experientials/ziloo/Hardware/faceboard/FACEBOARD.md

## Faceboard

LED arrangement

LED mounting

Powering

Camera mounting

Sensors. Motion, light, sound
