experientials/ziloo/Hardware/faceboard/USING_GPIO.md

# Using the GPIO connectors

## CAN bus interfacing

## SPI communication

## Retro signalling

If you want to interface with retro computing equipment software drivers for VGA, DVI and Parallel Port the allow you connect
these via the GPIO header.

## Attaching extra I2C sensors

## Attaching Analog Sensors

- humidity
- temperature
- human body
- ?

## Making a Robot

Adding
- Wheels
- Arms 
- Legs

# Power

- 5V (limited A)
- 3V3 while awake
- 3V3 for always on sensors
