experientials/ziloo/Hardware/pinouts/I2C_EXPANDER_1.md

The development board uses a single Expander. The 909 and 801 uses 2x PCA9555 to control more states.

The EX1 expander input triggers interrupt via EX_OH_nINT (GPIO1_IO0).
The pins relate to USB1 OTG and M.2 Key E.

The EX1 expander allows controlling T-USB maps,

| Expander  | Connected to |
|---|---|
| EX1.0 | |
| EX1.1 | |
| EX1.2 |  |
| EX1.3 | MUX_USB2_SEL |
| EX1.4 | MUX_USB3_SEL |
| EX1.5 | COEX4 |
| EX1.6 | DEV_WLAN_WAKE |
| EX1.7 | ALERT / I2C_IRQ |
| EX1.9 | LED / DAS / DSS  |
| EX1.10 | W_DISABLE2# |
| EX1.11 | W_DISABLE1# |
| EX1.12 | UART WAKE |
| EX1.13 | SDIO WAKE |
| EX1.14 | LED2# |
| EX1.15 | |
