experientials/ziloo/Hardware/pinouts/RPI_15_CONNECTOR.md

| Pin | Code | Type | Details | Voltage |
|-----|---|---|---|---|
| 1 |	GND | Power | Ground | |
| 2 |	CAM_D0_N | Data | MIPI Data Lane 0 Negative | |
| 3 |	CAM_D0_P | Data | MIPI Data Lane 0 Positive | |
| 4 |	GND | Power | Ground | |
| 5 |	CAM_D1_N | Data | MIPI Data Lane 1 Negative | |
| 6 |	CAM_D1_P | Data | MIPI Data Lane 1 Positive | |
| 7 |	GND | Power | Ground | |
| 8 |	CAM_CK_N | Data | MIPI Clock Lane Negative | |
| 9 |	CAM_CK_P | Data | MIPI Clock Lane Positive | |
| 10  |	GND | Power | Ground | |
| 11  |	CAM_IO0 | Power | Power Enable | |
| 12  |	CAM_IO1 | LED | LED Indicator | |
| 13  |	SCL | I2C | I2C SCL | |
| 14  |	SDA | I2C | SCCB serial Interface data IO | | 
| 15  |	CAM_3V3 | Power | 3.3V Power Supply | |
