experientials/ziloo/Hardware/pinouts/T-USB_HOST_ALT_CONNECTOR.md

| Pin | Code | Description | 
|-----|---|---|
|  1  | 3V3 | |
|  2  | SBU2 | Host AUX+ / SBU2 |
|  3  | SBU1 | Host AUX- / SBU1 |
|  4  | 3V3 | |
|  5  | HA+ | Host A+ |
|  6  | HA- | Host A- |
|  7  | 3V3 | |
|  8  | HB+ | Host B+ |
|  9  | HB- | Host B- |
| 10  | 3V3 | |
| 11  | HC+ | Host C+ |
| 12  | HC- | Host C- |
| 13  | 3V3 | |
| 14  | HD+ | Host D+ |
| 15  | HD- | Host D- |
| 16  | GND | |
| 17  | | |
| 18  | | |
| 19  | GND | |
| 20  | HX+ | Host Extra 2.0 D+ |
| 21  | HX- | Host Extra 2.0 D- |
| 22  | | |
| 23  | | |
| 24  | GND | |
| 25  | LVCLK+ | LVDS CLK+ |
| 26  | LVCLK- | LVDS CLK- |
| 27  | GND | |
| 28  | LVD0+ | LVDS D0+ |
| 29  | LVD0- | LVDS D0- |
| 30  | GND | |
| 31  | LVD1+ | LVDS D1+ |
| 32  | LVD1- | LVDS D1- |
| 33  | GND | |
| 34  | LVD2+ | LVDS D2+ |
| 35  | LVD2- | LVDS D2- |
| 36  | GND | |
| 37  | LVD3+ | LVDS D3+ |
| 38  | LVD3- | LVDS D3- |
| 39  | GND | |
| 44  | UART_RP…TXD. | Debug  | | | | GP0. |
| 45  | UART…RP…RXD. | Debug. | | | | GP1 |
