experientials/ziloo/Hardware/pinouts/T-USB_OTG_ALT_CONNECTOR.md

| Pin | Code | Category | Description | Voltage | SoM pin  | MCU pin |
|-----|---|---|---|---|---|---|
|  1  | 3V3 | Power | |
|  2  | SBU2 | USB | OTG AUX+ / SBU2 |
|  3  | SBU1 | USB | OTG AUX- / SBU1 |
|  4  | 3V3 | |
|  5  | OA+ | USB | OTG A+ |
|  6  | OA- | USB | OTG A- |
|  7  | 3V3 | |
|  8  | OB+ | USB | OTG B+ |
|  9  | HB- | USB | OTG B- |
| 10  | 3V3 | |
| 11  | OC+ | USB | OTG C+ | 
| 12  | OC- | USB | OTG C- |
| 13  | 3V3 | |
| 14  | OD+ | USB | OTG D+ |
| 15  | OD- | USB | OTG D- |
| 16  | GND | |
| 17  | OX+ | USB | OTG Extra 2.0 D+ |
| 18  | OX- | USB | OTG Extra 2.0 D- |
| 19  | MCU_D+ | USB | Stem MCU 2.0 D+ | 
| 20  | MCU_D- | USB | Stem MCU 2.0 D- |
| 21  | GND | |
| 22  | STEM SCL | I2C | STEM SCL | | | GP17 I2C0 |
| 23  | STEM SDA | I2C | STEM SDA | | | GP16 I2C0 |
| 24  | STEM INT | I2C | Sensor interrupts | |
| 25  | NIGHT SCL  | I2C | I2C6 SCL | | P21.2 ? | GP19 I2C1. |
| 26  | NIGHT SDA  | I2C | I2C6 SDA | | P21.4 ? | GP18 I2C1. |
| 27  | NIGHT INT  | I2C | Sensor interrupts | |
| 28  | SYS I2C SCL| I2C | | | GP15 I2C1.  |
| 29  | SYS I2C SDA| I2C | | | GP14 I2C1.  |
| 30  | GND | Power | Ground | |
| 31  | SWD CLK RP | | | |
| 32  | SWD DAT RP | | | 
| 33  | GND | Power | Ground | |
| 34  | UART1_TXD  | UART | P1.72 UART1 Tx | | P20.9 | GP4 UART1 |
| 35  | UART1_RXD  | UART | P1.19 UART1 Rx | | P20.11  | GP5 UART1 |
| 36  | UART2_TXD  | UART | UART2 Tx | | P20.1 | GP8 UART1. |
| 37  | UART2_RXD  | UART | UART2 Rx | | P20.3 | GP9 UART1 |
| 38  | UART3_TXD  | UART | P1.61 UART3 Tx | | P20.2 | GP12 UART0 |
| 39  | UART3_RXD  | UART | P1.21 UART3 Rx | | P20.4 | GP13 UART0 |
| 40  | UART4_TXD  | UART | UART4 Tx | | P20.8 | GP20 UART1 |
| 41  | UART4_RXD  | UART | UART4 Rx | | P20.10  | GP21 UART1 |
| 42  | SPI_CS | RP2040 | Programming/External flash directly  | 3.3V | | GP29 SPI1 |
| 43  | SPI_CLK | RP2040 | Programming/External flash directly  | 3.3V | | GP26 SPI1 |
| 44  | SPI_MISO | RP2040 | Programming/External flash directly  | 3.3V | | GP28 SPI1 |
| 45  | SPI_MOSI | RP2040 | Programming/External flash directly  | 3.3V | | GP27 SPI1 |
