experientials/ziloo/Hardware/pinouts/BOARD_POWER_4_CONNECTOR.md

| No. | Pin  | Description |
|-----|---|---|
|  1  |	5V |	Board Power 5V |
|  2  |	GND  |	 GND 	 |
|  3  |	GND  |	 GND 	 |
|  4  |	VIN  |	Voltage Input from USB-C |

Max. Current per pin 1A
