experientials/ziloo/Hardware/standards/POWER.md

PMIC_STBY_REQ

Output low with PD
NVCC_SNVS

POR_B

Input with PU
NVCC_SNVS

NVCC_SNVS_1P8
Expected max draw 2mA
