experientials/ziloo/Hardware/pinouts/BOARD_POWER_CONNECTOR.md

| No. | Pin  | Description |
|-----|---|---|
|  1  |	 | Reserved 	 |
|  2  |	5V |	Board Power 5V |
|  3  |	GND  |	 GND 	 |
|  4  |	GND  |	 GND 	 |
|  5  |	VIN  |	Voltage Input from USB-C |
| 6  |	VIN  |	 VIN 	 |
| 7  | PD_I2C1_SCL| I2C1_SCL(pullup resistor 2.2K) | 
| 8  | PD_I2C1_SDA| I2C1_SDA(pullup resistor 2.2K) | 
| 9  | PD_I2C2_SCL| I2C2_SCL(pullup resistor 2.2K) | 
| 10  | PD_I2C2_SDA| I2C2_SDA(pullup resistor 2.2K) | 

Max. Current per pin 3.0A

IRQZ pins for the two I2Cx
