experientials/ziloo/Hardware/pinouts/EXTRAS_CONNECTOR.md

| Pin | Code | Description | 
|-----|---|---|
| 1 | LCAM_FSIN  | Left Frame sync input | 
| 2 | LCAM_STROBE| Left Frame sync output | 
| 3 | LCAM_RESET | Camera Reset, Active Low (RSTB) | 
| 4 | LCAM_PWRDN | Camera Power Down | 
| 5 | LCAM_EXTCLK| Left External Clock Input (MCLK) | 
| 6 | LATT_INT | Left Interrupt Attached Sensor, Active L |
| 7 | LATT_XSHUT | Left Attached Sensor XSHUTDOWN |
| 8 | L_AF_PWM | PWM Motor control | 
| 9 | | Reserved |
| 10  | | Reserved |
| 11  | LCAM_FSIN  | Left Frame sync input | 
| 12  | LCAM_STROBE| Left Frame sync output | 
| 13  | LCAM_RESET | Camera Reset, Active Low (RSTB) | 
| 14  | LCAM_PWRDN | Camera Power Down | 
| 15  | LCAM_EXTCLK| Left External Clock Input (MCLK) | 
| 16  | LATT_INT | Left Interrupt Attached Sensor, Active L |
| 17  | LATT_XSHUT | Left Attached Sensor XSHUTDOWN |
| 18  | L_AF_PWM | PWM Motor control | 
| 19  | | Reserved |
| 20  | | Reserved |
| 21  | BCLK / SCK | Bit clock line | 
| 22  | WS / LRCLK | Word clock line | 
| 23  | SDATA1 | Input data 1 | 
| 24  | SDATA2 | Input data 2 (NC) | 
| 25  | SDATA3 | Input data 3 (NC) | 
| 26  | SDATA4 | Input data 4 (NC) | 
| 27  | PD_I2C1_SCL| I2C1_SCL(pullup resistor 2.2K) | 
| 28  | PD_I2C1_SDA| I2C1_SDA(pullup resistor 2.2K) | 
| 29  | PD_I2C2_SCL| I2C2_SCL(pullup resistor 2.2K) | 
| 30  | PD_I2C2_SDA| I2C2_SDA(pullup resistor 2.2K) | 
| 31  | GND | |
| 34  | GND | |
| 37  | GND | |
| 40  | GND | |
| 43  | GND | |
