experientials/ziloo/Hardware/pinouts/I-PEX_30_CONNECTOR.md

The connector is an [I-PEX type 20525-030E-02](https://www.i-pex.com/product/cabline-ca) with 0.4mm pitch & 30 pins.
Data pins are 1.8V level.

| Pin | Code | Details |
|-----|---|---|
| 1 | CAM_3V3	 | 3.3V Power Input |
| 2 | CAM_3V3 | |
| 3 | CAM_1V8	 | 1.8V Power Input |
| 4 | GND | |
| 5 | GND | |
| 6 | PWR DWN | PWRDN on 34pin |
| 7 | I2C SCL | |
| 8 | I2C SDA | |
| 9 | GND | |
| 10  | CSI D2- | |
| 11  | CSI D2+ | |
| 12  | TRIGGER | |
| 13  | MCLK | EXTCLK on 34pin |
| 14  | Reserved | |
| 15  | CSI D1- | |
| 16  | CSI D1+ | |
| 17  | GND | |
| 18  | GND | |
| 19  | CSI D0- | |
| 20  | CSI D0+ | |
| 21  | RESET | RESET on 34pin |
| 22  | GND | |
| 23  | Reserved | |
| 24  | CSI CLK- | |
| 25  | CSI CLK+ | |
| 26  | GND | |
| 27  | CSI D3- | |
| 28  | CSI D3+ | |
| 29  | Flash | |
| 30  | Reserved | |

Refs
- https://www.leopardimaging.com/product/accessories/cables/faw-1233-03/
- https://www.mouser.com/datasheet/2/233/LI-TX1-CB-6CAM_datasheet-1395894.pdf
- https://connecttech.com/ftp/pdf/ASG006_Spacely.pdf
- https://www.i-pex.com/product/cabline-ca
