experientials/ziloo/Hardware/801/iMX8MP.md

# i.MX 8M Plus

The model used on Compulab dev board is i.MX8M Plus QuadLite 1.8GHz, 1GB RAM, 16GB eMMC w/o Ethernet. 
UCM-iMX8PLUS-C1800Q-D1-N16 price $54*150 for 100pcs.

* [Forlinx OKMX8MP-C Single Board Computer](https://www.forlinx.net/product/okmx8mp-c-development-board-120.html) $54
* [Compulab UCM-iMX8M-Plus](https://www.compulab.com/products/computer-on-modules/ucm-imx8m-plus-nxp-i-mx-8m-plus-som-system-on-module-computer/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) $150
* [Compulab Resources](https://www.compulab.com/products/computer-on-modules/ucm-imx8m-plus-nxp-i-mx-8m-plus-som-system-on-module-computer/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)

* [Building Boot Firmware for CompuLab's i.MX8M Plus products](https://github.com/compulab-yokneam/meta-bsp-imx8mp/blob/ucm-imx8m-plus-r1.0/Documentation/imx_boot_image_build.md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)
* [Compulab Yocto Layer](https://github.com/compulab/yocto-compulab-layer)
* [Compulab getting started](https://mediawiki.compulab.com/w/index.php?title=UCM-iMX8M-Plus:_Evaluation_Kit:_Getting_Started)

nRF 5340 BT40 Module

https://www.digikey.com/en/products/detail/fanstel-corp/BT40/13174283
