experientials/ziloo/Hardware/refs/RV1126.md

# RV1126 Implementation Notes

1. Quad-core AI vision processor
Low-consumption AI vision processor RV1126, with 14nm lithography process and quad-core 32-bit ARM Cortex-A7 architecture, integrates NEON and FPU — the frequency is up to 1.5GHz. It supports FastBoot, TrustZone technology and multiple crypto engines.

2. High performance, high computing power
Built-in neural network processor NPU with computing power up to 2.0 Tops realizes that the power consumption of AI computing is less than 10% of the power required by the GPU. With tools and supporting AI algorithms provided, it supports direct conversion and deployment of Tensorflow, PyTorch, Caffe, MxNet, DarkNet, ONNX, etc.

3. Multi-level image noise reduction
With multi-level image noise reduction, 3F-HDR and other technologies, RV1126 not only ensures the dynamic range of the scene, but also meets the needs of outputting full color in darkness, making "clearly visible" a reality — more conforms to the actual demands in the security field.

4. 4K H.265 encoding & decoding
Built-in Video CODEC supports 4K H.254/H.265@30FPS and multi-channel video encoding and decoding, meeting the needs of low bit rate, low-latency encoding, perceptual encoding and making the video occupancy smaller.

5. Exquisite and mini
Core board pins are made with gold plating technology, which is anti-corrosion. The size is only 69.6mm x 33.9mm, saving a lot of space.

6. Stable and reliable OS
It supports Buildroot+QT OS — occupies small space, starts fast, and provides stable and reliable operation.

7. Various interfaces
SODIMM 260P port is provided; I2C, SPI, UART, ADC, PWM, GPIO, USB2.0, SDIO, I2S, MIPI-DSI, MIPI-CSI, CIF, SDMMC, PHY and other interfaces are equipped, meeting needs of more usage scenarios.

8. To form high-performance mainboard
The core board can be combined with the backplane to form a complete high-performance industrial mainboard with more expansion interfaces and more powerful performance, which can be directly applied to various smart products to accelerate the product development process.

9. Abundant resources for customization
A complete SDK, including cross compiler toolchain, BSP source code, application development environment, development documents, examples, face recognition algorithms and other resources, is provided for the users to make a further customization.

10. Applications
It is widely used in face recognition, gesture recognition, gate access control, smart security, smart IP camera, smart doorbell/peephole, self-service terminals, smart finance, smart construction, smart travel and other industries.

Basic Specifications
SoC
RV1126
CPU
Quad-core ARM Cortex-A7 32-bit, integrates NEON and FPU
Each core has a 32KB I-cache, 32KB D-cache and 512KB shared second-level cache Based on RISC-V MCU
NPU
2.0Tops, supports INT8/ INT16，
It has strong network model compatibility, can realize the conversion of commonly used AI framework models,eg:
Tensor Flow/MXNet/PyTorch/Caffe/...
RAM
1GB / 2GB DDR4
Storage
8GB / 16GB eMMC
Video Encoding
4K H.264/H.265 30fps video encoding:
3840 x 2160@30 fps+720p@30 fps encoding
Video Decoding
4K H.264/H.265 30fps video decoding:
3840 x 2160@30 encoding + 3840 x 2160@30 fps decoding
Hardware Features
Ethernet
Supports 10/100/1000M Ethernet,
With TSO(TCP Segmentation Offload) network acceleration
WiFi
Via SDIO 3.0 interface
Display
Supports MIPI-DSI interface 1080P @ 60 FPS
Audio
8-channel I2S with TDM/PDM, 2-channel I2S
Camera
Supports 3 cameras simultaneous input:
2 groups of MIPI CSI (or LVDS/sub LVDS) and 1 group of DVP (BT.601/BT.656/BT.1120) Supports 14M ISP 2.0 with 3-frame HDR(Line-based/Frame-based/DCG)
Interface
USB 2.0 OTG , USB 2.0 host
1000M Ethernet port, with TSO(TCP Segmentation Offload) network acceleration SDIO 3.0×2 (for Wi-Fi and SD card)
8-channel I2S with TDM/PDM, 2-channel I2S
UART×6, SPI×2, I2C×6, GPIO, CAN, PWM

## CAM-C1126S2U Spec

J4700(MIPI CSI Interface) 

Pin Pin Name            Default function                                IO Power domain   Pad type IO pull
1 AVDD_2V8                2.8V OUTPUT, Max 500mA            IR_AVDD 2.8V
2 VCC3V3_SYS            3.3V OUTPUT, Max 500mA            RGB_AVDD        3.3V
3 GND                    GND                                Power ground
4 IR_PWDN                IR- PWER EN                    For IR Camera            3.3V
5 IR_RESET                IR_RESET,Active L                 For IR Camera     3.3V
6 I2C1_SCL                I2C1_SCL(pullup resistor 2.2K)    IR+RGB            1.8V         UP
7 I2C1_SDA                I2C1_SDA(pullup resistor 2.2K)    IR+RGB             1.8V         UP
8 GND                    GND                                Power ground
9 MIPI_CSI_CLK0            MIPI_CSI_CLK0 OUTPUT             For IR Camera        1.8V DOWN
10 GND                    GND                                Power ground
11 MIPI_CSI_RX0_CLKP        MIPI_CSI_RX0_CLK+                For IR Camera     1.8V
12 MIPI_CSI_RX0_CLKN        MIPI_CSI_RX0_CLK-                For IR Camera      1.8V
13 GND                    GND                                Power ground
14 MIPI_CSI_RX0_D0P        MIPI_CSI_RX0_D0+                For IR Camera        1.8V
15 MIPI_CSI_RX0_D0N        MIPI_CSI_RX0_D0-                  For IR Camera         1.8V
16 GND                    GND                            Power ground
17 MIPI_CSI_RX0_D1P        MIPI_CSI_RX0_D1+                    For IR Camera         1.8V
18 MIPI_CSI_RX0_D1N        MIPI_CSI_RX0_D1-                For IR Camera            1.8V
19 GND                    GND                                Power ground
20 MIPI_CSI_RX0_D2P        MIPI_CSI_RX0_D2+                For IR Camera            1.8V
21 MIPI_CSI_RX0_D2N        MIPI_CSI_RX0_D2-                For IR Camera            1.8V
22 GND                    GND                                Power ground
23 NC                    NC
24 VCC_1V8                1.8V OUT ,MAX 200mA                IR+RGB                    3.3V
25 FSVNC                Default NC                            IR+RGB
26 DVDD_1V2                1.2V OUT ,MAX 300mA                For IR Camera            1.2V
27 DVDD_1V3                1.3V OUT ,MAX 300mA                For RGB Camera           1.3V
28 GND                    GND                                Power ground
29 MIPI_RX0_PDN            MIPI_ PDN                         For RGB Camera           1.8V DOWN
30 MIPI_RX0_RST            MIPI _RST, Active L                For RGB Camera            1.8V        DOWN
31 GND                    GND                                Power ground
32 MIPI_CSI_CLK1            MIPI_CSI_CLK1 Output            For RGB Camera            1.8V        DOWN
33 GND                    GND                                Power ground
34 MIPI_CSI_RX1_CLKP        MIPI_CSI_RX1_CLK+                For RGB Camera            1.8V
35 MIPI_CSI_RX1_CLKN        MIPI_CSI_RX1_CLK-                For RGB Camera            1.8V
36 GND                    GND                                Power ground
37 MIPI_CSI_RX1_D0P        MIPI_CSI_RX1_D0+                  For RGB Camera            1.8V
38 MIPI_CSI_RX1_D0N        MIPI_CSI_RX1_D0-                  For RGB Camera            1.8V
39 GND                    GND                                Power ground
40 MIPI_CSI_RX1_D1P        MIPI_CSI_RX1_D1+                  For RGB Camera            1.8V
41 MIPI_CSI_RX1_D1N        MIPI_CSI_RX1_D1-                  For RGB Camera            1.8V
42 GND                    GND                                Power ground
43 MIPI_CSI_RX1_D2P        MIPI_CSI_RX1_D2P                  For RGB Camera            1.8V
44 MIPI_CSI_RX1_D2N        MIPI_CSI_RX1_D2N                  For RGB Camera            1.8V
45 GND                     GND                                POWER GROUND

## Related Repos

* https://github.com/Consti10/rv1126/issues/13
* https://github.com/lloovve/RV1126-SDK
* https://github.com/xingxingRealzyx/rv1126_bsp/tree/main/projects

## Core-1126-JD4 Spec

* RV1126 MCU/NPU
* 2 * SEC 040K4A46165VF / SEC 949 K4A4G16 5NE BCRC DDR3 1GB 
* SEC 946 BO41 KLM8G1GETF eMMC 8GB
* RK809-2 PMU

1
3
5
7
9
11
13
15
17
19
21
23
25
27
29
31
33
35
37
39
41
43
45
47
49
51
53
55
57
59
61
63
65
67
69
71
73
75
77
79
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
Core board pin definition
GND_1
GPIO0_A4_U
GPIO0_C0_D
GPIO0_A2_Z
GND_2
MIC1_INN
MIC1_INP
HPR_OUT
HP_SNS
HPL_OUT
SPKN_OUT
SPKP_OUT
GND
USB_HOST_DP
USB_HOST_DM
GND_4
NC
NC
GND_5
I2C2_SCL
I2C2_SDA
GND_4
MIPI_CSI_RX0_D2P
MIPI_CSI_RX0_D2N
MIPI_CSI_RX0_D3P
MIPI_CSI_RX0_D3N
MIPI_CSI_RX0_D1P
MIPI_CSI_RX0_D1N
MIPI_CSI_RX1_D3P
MIPI_CSI_RX1_D3N
MIPI_CSI_RX1_D2P
MIPI_CSI_RX1_D2N
GND_7
MIPI_CSI_RX1_D1P
MIPI_CSI_RX1_D1N
MIPI_CSI_RX1_D0P
MIPI_CSI_RX1_D0N
GND8
MIPI_CSI_PWDN0
MIPI_CSI_CLK1
MIPI_CSI_CLK0
GND_9
SPI0_CS1N_M1
SPI0_MOSI_M1/I2C3_SC L_M2
SPI0_CLK_M1
SPI0_CS0N_M1
SPI0_MISO_M1/I2C3_SD A_M2
UART4_TX_M1 /GPIO2_A6_D
GND_10
RMII_RXDV
RMII_RXD0
RMII_CLK
RMII_RXD1
RMII_MDIO
RMII_MDC
RMII_RXER
RMII_TXD0
GND_11
RMII_TXD1
CLKOUT/GPIO_C5_D
RMII_RXD3/HOST_DRV_ H
GND_12
RMII_TXEN/GPIO2_C6_D
RMII_TXD2/ZOOM_EN_ H
RMII_TXCLK/FOCUS_EN_ H
NC
Pin type
G
I/O
I/O
I/O
G
O
O
O
O
G
I/O
I/O
G
G
I/O
I/O
G
G
G
I/O
I/O
I/O
G
I/O
I/O
I/O
I/O
I/O
I/O
G
I/O
I/O
I/O
I/O
I/O
I/O
I/O
I/O
G
I/O
I/O
I/O
G
I/O
I/O
I/O
I
I
I
I
I
I
I
I
I
I
I
I
I
I
I
I
I/O Pull
UP
DOWN
DOWN
DOWN
UP
DOWN
DOWN
DOWN
DOWN
DOWN
DOWN
DOWN
DOWN
DOWN
DOWN
DOWN
DOWN
DOWN
DOWN
DOWN
DOWN
DOWN
DOWN
DOWN
DOWN
DOWN
DOWN
Function for Floor(MB-JD4- RV11091126)
GND_1
WORKLED
DIYLED
FAN_CTRL
GND_2
MIC1_INN
MIC1_INP
HPR_OUT
HP_SNS
HPL_OUT
SPKN_OUT
SPKP_OUT
GND
USB_HOST_DP
USB_HOST_DM
GND
NC
NC
GND
PWM4_M0
PWM5_M0
GND
MIPI_CSI_RX0_D2P
MIPI_CSI_RX0_D2N
MIPI_CSI_RX0_D3P
MIPI_CSI_RX0_D3N
MIPI_CSI_RX0_D1P
MIPI_CSI_RX0_D1N
MIPI_CSI_RX1_D3P
MIPI_CSI_RX1_D3N
MIPI_CSI_RX1_D2P
MIPI_CSI_RX1_D2N
GND
MIPI_CSI_RX1_D1P
MIPI_CSI_RX1_D1N
MIPI_CSI_RX1_D0P
MIPI_CSI_RX1_D0N
GND
MIPI_CSI_PWDN0
MIPI_CSI_CLK1
MIPI_CSI_CLK0
GND
SPI0_CS1N_M1
SPI0_MOSI_M1
SPI0_CLK_M1
SPI0_CS0N_M1
SPI0_MISO_M1
UART4_TX
GND
RMII_RXDV
RMII_RXD0
RMII_CLK
RMII_RXD1
RMII_MDIO
RMII_MDC
RMII_RXER
RMII_TXD0
GND
RMII_TXD1
CLKOUT/GPIO_C5_D
RMII_RXD3
GND
RMII_TXEN
RMII_TXD2
RMII_TXCLK
NC
Default function description
GND
System LED control 1:Enable,0:Disable
Diy led control 1:Enable,0:Disable
PMIC MIC_IN_N
Core board internal series capacitor
0.1uF
PMIC MIC_IN_P,
Core board internal series capacitor 0.1uF
PMIC_HearPhone_OUT_R
PMIC_HearPhone_OUT_GND
PMIC_HearPhone_OUT_L
PMIC_Sperker_OUT_N
PMIC_Sperker_OUT_P
PWM4_M0
PWM5_M0
GND
MIPI_CSI_RX0_D2P
MIPI_CSI_RX0_D2N
MIPI_CSI_RX0_D3P
MIPI_CSI_RX0_D3N
MIPI_CSI_RX0_D1P
MIPI_CSI_RX0_D1N
MIPI_CSI_RX1_D3P
MIPI_CSI_RX1_D3N
MIPI_CSI_RX1_D2P
MIPI_CSI_RX1_D2N
GND
MIPI_CSI_RX1_D1P
MIPI_CSI_RX1_D1N
MIPI_CSI_RX1_D0P
MIPI_CSI_RX1_D0N
GND
MIPI-CSI Power_EN
MIPI-CSI_clock1
MIPI-CSI_clock0
GND
SPI0_CS1N_M1
SPI0_MOSI_M1
SPI0_CLK_M1
SPI0_CS0N_M1
SPI0_MISO_M1
UART4_TX
GND
RMII_RXDV
RMII_RXD0
RMII_CLOCK
RMII_RXD1
RMII_MDIO
RMII_MDC
RMII_RXER
RMII_TXD0
Core board internal series resistance 22R
GND
RMII_TXD1
Core board internal series resistance 22R
PHY_XTALOUT
RMII_RXD3
GND
RMII_TXEN
RMII_TXD2
Core board internal series resistance 22R
RMII_TXCLK
Core board internal series resistance 22R
NC
IO Power domain
1.8V
3.3V
1.8V
3.3V
3.3V
3.3V
3.3V
3.3V
3.3V
3.3V
3.3V
3.3V
3.3V
1.8V
1.8V
1.8V
1.8V
1.8V
1.8V
1.8V
1.8V
1.8V
1.8V
1.8V
1.8V
1.8V
1.8V
1.8V
1.8V
1.8V
1.8V
1.8V
1.8V
1.8V
1.8V
3.3V
3.3V
3.3V
3.3V
3.3V
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
RV1126 Pin
V7
U9
AA3
Y1
Y2
AA6
Y6
W15
Y15
AA15
AA16
Y16
W16
Y17
W17
AA18
Y18
AA19
Y19
AA20
Y20
W20
W21
V21
V20
V19
U20
U19
U18
M21
K18
K19
K21
K20
J21
J20
J19
H20
H19
G21
H18
G20
F21
F20
RV1126 Pin Name
GND_1
SPI0_CS1N_M0 / GPIO0_A4_U
SDMMC0_PWR / UART1_RTSN_M0 / PWM2_M0 / GPIO0_C0_D
CLKI_CLKO_32K / GPIO0_A2_Z
GND_2
MIC1_N / MIC_R
MIC1_P / MIC_L
HPR_OUT
HP_SNS
HPL_OUT
SPKN_OUT
SPKP_OUT
GND_3
USB_HOST_DP
USB_HOST_DM
GND_4
NC_1
NC_2
GND_5
I2C2_SCL / PWM4_M0 / GPIO0_C2_D
I2C2_SDA / PWM5_M0 / GPIO0_C3_D
GND_6
MIPI_CSI_RX0_D2P / LVDS0_RX2P
MIPI_CSI_RX0_D2N / LVDS0_RX2N
MIPI_CSI_RX0_D3P / LVDS0_RX3P
MIPI_CSI_RX0_D3N / LVDS0_RX3N
MIPI_CSI_RX0_D1P / LVDS0_RX1P
MIPI_CSI_RX0_D1N / LVDS0_RX1N
MIPI_CSI_RX1_D3P / LVDS1_RX3P
MIPI_CSI_RX1_D3N / LVDS1_RX3N
MIPI_CSI_RX1_D2P / LVDS1_RX2P
MIPI_CSI_RX1_D2N / LVDS1_RX2N
GND_7
MIPI_CSI_RX1_D1P / LVDS1_RX1P
MIPI_CSI_RX1_D1P / LVDS1_RX1N
MIPI_CSI_RX1_D0P / LVDS1_RX0P
MIPI_CSI_RX1_D0P / LVDS1_RX0N
GND8
UART4_RX_M2 / GPIO1_D4_d
MIPI_CSI_CLK1 / UART5_RTSN_M2 / GPIO2_A2_D
MIPI_CSI_CLK0 / UART5_CTSN_M2 / GPIO2_A3_D
GND_9
SPI0_CS1N_M1 / I2S1_MCLK_M1 / UART4_TX_M2 / GPIO1_D5_D
SPI0_MOSI_M1 / I2S1_SCLK_M1 / I2C3_SCL_M2 / GPIO1_D6_D
SPI0_CLK_M1 / I2S1_SDO_M1 / UART5_RX_M2 / GPIO2_A1_D
SPI0_CS0N_M1 / I2S1_SDI_M1 / UART5_TX_M2 / GPIO2_A0_D
SPI0_MISO_M1 / I2S1_LRCK_M1 / I2C3_SDA_M2 / GPIO1_D7_D
UART4_TX_M1 / PWM5_M1 / RGMII_COL_M1 / CIF_D2_M1 / LCDC_D2 / GPIO2_A6_D
GND_10
RGMII_RXDV_M1 / CIF_D4_M1 / LCDC_D8 / GPIO2_B4_D
RGMII_RXD0_M1 / CIF_D5_M1 / LCDC_D9 / GPIO2_B5_D
RGMII_CLK_M1 / CIF_D7_M1 / LCDC_D11 / GPIO2_B7_D
RGMII_RXD1_M1 / CIF_D6_M1 / LCDC_D10 / GPIO2_B6_D
RGMII_MDIO_M1 / CIF_D9_M1 / LCDC_D13 / GPIO2_C1_D
RGMII_MDC_M1 / CIF_D10_M1 / LCDC_D14 / GPIO2_C2_D
RGMII_RXER_M1 / CIF_D8_M1 / LCDC_D12 / GPIO2_C0_D
RGMII_TXD0_M1 / CIF_D11_M1 / LCDC_D15 / GPIO2_C3_D
GND_11
RGMII_TXD1_M1 / CIF_D12_M1 / LCDC_D16 / GPIO2_C4_D
CLK_OUT_ETHERNET_M1 / CIF_D13_M1 / LCDC_D17 / GPIO2_C5_D
I2S1_SDO_M2 / RGMII_RXD3_M1 / CIF_VSYNC_M1 / LCDC_D20 / GPIO2_D0_D
GND_12
RGMII_TXEN_M1 / CIF_D14_M1 / LCDC_D18 / GPIO2_C6_D
I2S1_SCLK_M2 / RGMII_TXD2_M1 / CIF_CLKOUT_M1 / LCDC_D21 / GPIO2_D1_D
I2S1_LRCK_M2 / RGMII_TXCLK_M1 / CIF_CLKIN_M1 / LCDC_D22 / GPIO2_D2_D
NC_3

-8-
        High-Performance AI Vision Core Board
 133
OTG_DP
OTG_DP
USB_OTG_DP
3.3V
W3
OTG_DP
135
OTG_DM
OTG_DM
USB_OTG_DM
3.3V
W4
OTG_DM
137
NC
NC
NC
NC_4
139
LCD_PWREN/UART3_TX _M2
I/O
UP
UART3_TX
UART3_TX_M2
3.3V
E20
I2C4_SCL_M0 / CAN_RXD_M0 / UART3_TX_M2 / PWM7_IR_M1 / SPI1_CS1N_M2 / GPIO3_A0_U
141
GPIO3_A1_U/UART3_RX _M2
I/O
UP
UART3_RX
UART3_RX_M2
3.3V
E19
I2C4_SDA_M0 / CAN_TXD_M0 / UART3_RX_M2 / PWM11_IR_M1 / GPIO3_A1_U
143
PWM8_M1
I/O
DOWN
PWM8_M1/SPI1_MISO_M2
PWM8_M1/SPI1_MISO_M2
3.3V
D21
UART3_CTSN_M2 / PWM8_M1 / SPI1_MISO_M2 / LCDC_CLK / GPIO2_D7_D
145
OTG_VBUS_DET
I
DOWN
OTG_DET_1V8
OTG_DET.Active Hight
1.8V
V5
OTG_VBUS1V8
147
MIPI_DSI_TX0_D3P
O
MIPI_DSI_TX0_D3P
MIPI_DSI_TX0_D3P
1.8V
D20
MIPI_DSI_TX0_D3P
149
MIPI_DSI_TX0_D3N
O
MIPI_DSI_TX0_D3N
MIPI_DSI_TX0_D3N
1.8V
D19
MIPI_DSI_TX0_D3N
151
MIPI_DSI_TX0_D2P
O
MIPI_DSI_TX0_D2P
MIPI_DSI_TX0_D2P
1.8V
B21
MIPI_DSI_TX0_D2P
153
MIPI_DSI_TX0_D2N
O
MIPI_DSI_TX0_D2N
MIPI_DSI_TX0_D2N
1.8V
C20
MIPI_DSI_TX0_D2N
155
MIPI_DSI_TX0_D1N
O
MIPI_DSI_TX0_D1N
MIPI_DSI_TX0_D1N
1.8V
B20
MIPI_DSI_TX0_D1N
157
MIPI_DSI_TX0_D1P
O
MIPI_DSI_TX0_D1P
MIPI_DSI_TX0_D1P
1.8V
A20
MIPI_DSI_TX0_D1P
159
MIPI_DSI_TX0_D0N
O
MIPI_DSI_TX0_D0N
MIPI_DSI_TX0_D0N
1.8V
B19
MIPI_DSI_TX0_D0N
161
MIPI_DSI_TX0_D0P
O
MIPI_DSI_TX0_D0P
MIPI_DSI_TX0_D0P
1.8V
A19
MIPI_DSI_TX0_D0P
163
GND_13
G
GND
GND
GND_13
165
SDIO_CLK
I/O
DOWN
SDIO_CLK
SDIO_CLK
Core board internal series resistance 22R
1.8V
D16
SDMMC1_CLK / GPIO1_B2_D
167
SDIO_D1
I/O
UP
SDIO_D1
SDIO_D1
1.8V
C16
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
G
GND
MIPI_CSI_RX0_CLKN
MIPI_CSI_RX0_CLKP
MIPI_CSI_RX0_D0P
MIPI_CSI_RX0_D0N
MIPI_CSI_RX1_CLKP
MIPI_CSI_RX1_CLKN
NC
MIPI_CSI_PWDN1
GND
MIPI_CSI_RST1
MIPI_CSI_RST0
BL_EN
TP_RST
TP_INT
GPIO0_D6
NC
NC
UART1_TX
Power ground
Power ground
Power ground
Power ground
Input Voltage 4.8V-5.5V
Input Voltage 4.8V-5.5V
Input Voltage 4.8V-5.5V
Input Voltage 4.8V-5.5V
Input Voltage 4.8V-5.5V
Default function description
GND
Mipi Reset,active low
NC
LCD_PWOER_EN
NC
I2C serial port 1,
Core board internal pull up Resistor 2.2K
I2C serial port 1,
Core board internal pull up Resistor 2.2K
NC
NC
NC
I2C serial port 1,
need pull up Resistor 2.2K
I2C serial port 1,
need pull up Resistor 2.2K
GND
NC
Speaker_EN ,active hight
GPIO3_D4
GND
NC
PMIC power_en output,active hight
Core board internal series resistance 1K
GND
TF_Card DET,active low
GND
SDMMC0_CMD
SDMMC0_CLK
SDMMC0_D1
SDMMC0_D0
SDMMC0_D2
SDMMC0_D3
GND
MIPI_CSI_RX0_CLKN
MIPI_CSI_RX0_CLKP
MIPI_CSI_RX0_D0P
MIPI_CSI_RX0_D0N
MIPI_CSI_RX1_CLKP
MIPI_CSI_RX1_CLKN
NC
MIPI_CSI_Powerdown1
GND
MIPI_CSI_RST1,active low
MIPI_CSI_RST0,active low
Black light EN ,active hight
TP_Reset,active low
TP_INT
GPIO0_D6
NC
NC
UART1_TX
5.0V_IN
5.0V_IN
5.0V_IN
5.0V_IN
5.0V_IN
IO Power domain
1.8V
1.8V
3.3V
3.3V
1.8V
1.8V
1.8V
1.8V
5.0V
1.8V
Note 1
1.8V
1.8V
1.8V
1.8V
1.8V
1.8V
3.3V
1.8V
1.8V
3.3V
3.3V
3.3V
3.3V
3.3V
RV1126 Pin
R4
T3
AA7
Y7
W19
Y21
AA12
Y12
U7
Y13
AA13
W13
Y14
V13
U13
V15
U15
V16
U16
V18
W18
T18
V11
U11
R3
U2
T2
R2
W8
RV1126 Pin Name
GND_21
I2S1_SDI_M0 / FSPI_D3 / FLASH_RDN / GPIO1_A2_U
NC_16
I2S1_SDO_M0 / FSPI_D2 / GPIO0_D6_D
NC_17
I2C0_SCL / GPIO0_B4_D
I2C0_SDA / GPIO0_B5_D
NC_18
NC_19
NC_20
I2C1_SDA / UART4_RTSN_M2 / GPIO1_D2_U
I2C1_SCL / UART4_CTSN_M2 / GPIO1_D3_U
GND_22
NC_21
I2S0_SDI0_M0 / PDM_SDI0_M0 / ACODEC_DAC_DATAL / GPIO3_D6_D
I2S0_LRCK_RX_M0 / PDM_CLK0_M0 / ACODEC_ADC_SYNC / GPIO3_D4_D
GND_23
NC_22
PMIC_EXT_EN
GND_24
SDMMC0_DET / GPIO0_A3_U
GND_25
UART3_CTSN_M1 / RISC-V_JTAG_TDI / SDMMC0_CMD / GPIO1_B1_U
UART3_RTSN_M1 / RISC-V_JTAG_TDO / SDMMC0_CLK / GPIO1_B0_U
UART2_TX_M0 / TEST_CLK0_OUT / RISC-V_JTAG_TRSTN / SDMMC0_D1 / GPIO1_A5_U
UART2_RX_M0 / TEST_CLK1_OUT / SDMMC0_D0 / GPIO1_A4_U
UART3_RX_M1 / A7_JTAG_TCK_M0 / RISC-V_JTAG_TCK / SDMMC0_D2 / GPIO1_A6_U
UART3_TX_M1 / A7_JTAG_TMS_M0 / RISC-V_JTAG_TMS / SDMMC0_D3 / GPIO1_A7_U
GND_26
MIPI_CSI_RX0_CLKN / LVDS0_CLKN
MIPI_CSI_RX0_CLKP / LVDS0_CLKP
MIPI_CSI_RX0_D0P / LVDS0_RX0P
MIPI_CSI_RX0_D0N / LVDS0_RX0N
MIPI_CSI_RX1_CLKP / LVDS1_CLKP
MIPI_CSI_RX1_CLKN / LVDS1_CLKN
NC_23
CIF_D1_M0 / RGMII_CRS_M0 / I2S0_LRCK_TX_M1 / UART4_RX_M0 / I2C3_SDA_M0 / PWM9_M0 / GPIO3_A5_D
GND_27
I2S0_SDO3_SDI1_M0 / PDM_SDI1_M0 / I2C4_SDA_M1 / AUDPWM_R_M0 / AUDDSM_RP / GPIO4_A1_D
I2S0_SDO2_SDI2_M0 / PDM_SDI2_M0 / I2C4_SCL_M1 / AUDPWM_L_M0 / AUDDSM_RN / GPIO4_A0_D
FSPI_CLK / EMMC_RSTN / FLASH_WPN / GPIO1_A3_D
I2S1_MCLK_M0 / FSPI_CS0N / FLASH_CS0N / GPIO0_D4_U
I2S1_LRCK_M0 / FSPI_D0 / FLASH_ALE / GPIO1_A0_D
I2S1_SCLK_M0 / FSPI_D1 / FLASH_RDYN / GPIO1_A1_U
NC_24
NC_25
UART1_TX_M0 / PWM0_M0 / GPIO0_B6_D
                                                             - 10 -

        High-Performance AI Vision Core Board
 96
PWM1_M0/UART1_RX_ M0
I/O
DOWN
UART1_RX
UART1_RX
3.3V
V9
UART1_RX_M0 / PWM1_M0 / GPIO0_B7_D
98
NC_26
NC
NC
NC_26
100
UART2_RX/DEBUG_RX
I/O
UP
UART2_RX/DEBUG_RX
UART2_RX/DEBUG_RX
3.3V
H16
A7_JTAG_TMS_M1 / UART2_RX_M1 / GPIO3_A3_U
102
UART2_TX/DEBUG_TX
I/O
UP
UART2_TX/DEBUG_TX
UART2_TX/DEBUG_TX
3.3V
G18
A7_JTAG_TCK_M1 / UART2_TX_M1 / GPIO3_A2_U
104
PWM10_M0 / GPIO3_A6_D
I/O
DOWN
LCD_BL_PWM
LCD_BL_PWM
3.3V
P17
CIF_D2_M0 / RGMII_COL_M0 / I2S0_SDO0_M1 / UART5_TX_M0 / CAN_RXD_M1 / PWM10_M0 / GPIO3_A6_D
106
PWM4_M1/ GPIO2_A7_D
I/O
DOWN
PWM4_M1/UART4_RX
PWM4_M1/UART4_RX output
3.3V
M20
I2S2_SDO_M1 / UART4_RX_M1 / PWM4_M1 / SPI0_CS0N_M2 / LCDC_D3 / GPIO2_A7_D
108
PWM3_IR_M1/ GPIO2_B0_D
I/O
DOWN
PWM3_M1
PWM3_M1 output
3.3V
L19
I2S2_SDI_M1 / UART5_TX_M1 / PWM3_IR_M1 / SPI0_MOSI_M2 / LCDC_D4 / GPIO2_B0_D
110
I2C5_SCL_M0/GPIO2_A5 _D
I/O
DOWN
3G_PWR_EN
3G_Power_EN,active hight
3.3V
L17
I2C5_SCL_M0 / UART4_CTSN_M1 / RGMII_CRS_M1 / CIF_D1_M1 / LCDC_D1 / GPIO2_A5_D
112
I2C5_SDA_M0/GPIO2_B 3_D
I/O
DOWN
CIFD3/PWM0_M1
CIFD3/PWM0_M1 output
3.3V
K17
I2C5_SDA_M0 / I2S2_MCLK_M1 / UART5_CTSN_M1 / PWM0_M1 / SPI0_CS1N_M2 / CIF_D3_M1 / LCDC_D7 / GPIO2_B3_D
114
NC_27
NC
NC
NC_27
116
PWM6_M1
I/O
DOWN
PWM6_M1/SPI1_CS0_M2
PWM6_M1/SPI1_CS0_M2
3.3V
J17
I2C3_SCL_M1 / PWM6_M1 / SPI1_CS0N_M2 / LCDC_DEN / GPIO2_D4_D
118
PWM10_M1
I/O
DOWN
PWM10_M1/SPI1_CLK_M2
PWM10_M1/SPI1_CLK_M2
3.3V
H17
I2C3_SDA_M1 / PWM10_M1 / SPI1_CLK_M2 / LCDC_HSYNC / GPIO2_D5_D
120
RMII_TXD3/GPIO2_A4_D
I/O
DOWN
RMII_TXD3
RMII_TXD3
Core board internal series resistance 22R
3.3V
J18
UART4_RTSN_M1 / RGMII_TXD3_M1 / CIF_D0_M1 / LCDC_D0 / GPIO2_A4_D
122
RMII_RXD2/GPIO2_C7_D
I/O
DOWN
RMII_RXD2
RMII_RXD2
3.3V
G19
I2S1_MCLK_M2 / RGMII_RXD2_M1 / CIF_D15_M1 / LCDC_D19 / GPIO2_C7_D
124
GND_28
G
GND
GND
GND_28
126
RMII_RXCLK/P_IRIS_EN_ H
I/O
DOWN
RMII_RXCLK
RMII_RXCLK
3.3V
F19
I2S1_SDI_M2 / RGMII_RXCLK_M1 / CIF_HSYNC_M1 / LCDC_D23 / GPIO2_D3_D
128
NC_28
NC
NC
NC_28
130
OTG_ID
I
UP
OTG_ID
OTG_DET.Active low
1.8V
Y3
OTG_ID
132
NC
NC
NC
NC
134
NC_29
NC
NC
NC_29
136
PWM9_M1
I/O
DOWN
PWM9_M1/SPI1_MOSI_M2
PWM9_M1/SPI1_MOSI_M2
3.3V
C21
UART3_RTSN_M2 / PWM9_M1 / SPI1_MOSI_M2 / LCDC_VSYNC / GPIO2_D6_D
138
GND_29
G
GND
GND
GND_29
140
MIPI_DSI_TX0_CLKP
O
MIPI_DSI_CLKP
MIPI_DSI_CLKP
1.8V
C19
MIPI_DSI_TX0_CLKP
142
MIPI_DSI_TX0_CLKN
O
MIPI_DSI_CLKN
MIPI_DSI_CLKN
1.8V
C18
MIPI_DSI_TX0_CLKN
144
NC_30
NC
NC
NC_30
146
NC_31
NC
NC
NC_31
148
NC_32
NC
NC
NC_32
150
ADC_IN4
I
UP
ADCIN4
ADC4 input,
Core board interiorl pull up Resistor 10K
1.8V
C17
ADC_IN4
152
ADC_IN0
I
UP
RECOVER
ADC0 input,RECOVER KEY, active low
Core board interiorl pull up Resistor 10K
1.8V
E17
ADC_IN0
154
ADC_IN2
I
UP
ADCIN2
ADC2 input,
Core board interiorl pull up Resistor 10K
1.8V
B18
ADC_IN2
156
ADC_IN3
I
UP
ADCIN3
ADC3 input,
Core board interiorl pull up Resistor 10K
1.8V
A18
ADC_IN3
158
GND_30
G
GND
GND
GND_30
160
NC_33
NC
NC
NC_33
162
PCM_RX/ GPIO1_C5_D
I/O
DOWN
HP_DET
Headphone plug in det,active low
1.8V
E13
I2S2_SDI_M0 / SPI1_MISO_M1 / FLASH_TRIG_IN / GPIO1_C5_D
164
PCM_CLK/ GPIO1_C6_D
I/O
DOWN
USB_OTG_EN
OTG power en ,active hight
1.8V
D13
I2S2_SCLK_M0 / SPI1_CLK_M1 / PRELIGHT_TRIG_OUT / UART1_RTSN_M1 / GPIO1_C6_D
166
PCM_SYNC/ GPIO1_C7_D
I/O
DOWN
MUTE
Headphone output en,active hight
1.8V
C13
I2S2_LRCK_M0 / SPI1_CS0N_M1 / UART1_CTSN_M1 / GPIO1_C7_D
168
PCM_TX/ GPIO1_C4_D
I/O
DOWN
USB_HOST_EN
USB Host power en ,active hight
1.8V
B14
I2S2_SDO_M0 / SPI1_MOSI_M1 / FLASH_TRIG_OUT / GPIO1_C4_D
170
UART0_TX
I/O
UP
UART0_TX
UART0_TX for BT
1.8V
C14
UART0_TX / GPIO1_C3_U
172
UART0_RX
I/O
UP
UART0_RX
UART0_RX for BT
1.8V
D14
UART0_RX / GPIO1_C2_U
174
UART0_CTSN
I/O
UP
UART0_CTSN
UART0_CTSN for BT
1.8V
A15
UART0_CTSN / GPIO1_C1_U
176
UART0_RTSN
I/O
UP
UART0_RTSN
UART0_RTSN for BT
1.8V
B15
UART0_RTSN / GPIO1_C0_U
178
NC_34
NC
NC
NC_34
180
GND_31
G
GND
GND
GND_31
182
GMAC_MDIO_M0
I/O
DOWN
GMAC_MDIO_M0/D15
GMAC_MDIO_M0/D15
3.3V
N20
CIF_D15_M0 / RGMII_MDIO_M0 / PDM_CLK1_M1 / GPIO3_C3_D
184
GMAC_MDC_M0
I/O
DOWN
GMAC_MDC_M0/VSYNC
GMAC_MDC_M0/VSYNC
3.3V
N21
CIF_VSYNC_M0 / RGMII_MDC_M0 / UART3_RTSN_M0 / GPIO3_C4_D
186
GMAC_TXCLK_M0
I/O
DOWN
GMAC_TXCLK_M0/CLKOUT
GMAC_TXCLK_M0/CLKOUT
Core board internal series resistance 22R
3.3V
P19
CIF_CLKOUT_M0 / RGMII_TXCLK_M0 / UART3_TX_M0 / GPIO3_C6_D
188
GMAC_RXCLK_M0
I/O
DOWN
GMAC_RXCLK_M0/NHYNC
GMAC_RXCLK_M0/NHYNC
3.3V
P20
CIF_HSYNC_M0 / RGMII_RXCLK_M0 / UART3_RX_M0 / GPIO3_C7_D
190
GND_32
G
GND
GND
GND_32
192
GMAC_CLK_M0
I/O
DOWN
GMAC_CLK_M0/D12
MAC reference clock output /CIF_D12
3.3V
N19
CIF_D12_M0 / RGMII_CLK_M0 / PDM_CLK0_M1 / SPI1_CLK_M0 / GPIO3_C0_D
194
GMAC_RXD1_M0
I/O
DOWN
GMAC_RXD1_M0/D11
MAC receive data/CIF_D11
3.3V
R21
CIF_D11_M0 / RGMII_RXD1_M0 / PDM_SDI3_M1 / SPI1_MISO_M0 / GPIO3_B7_D
196
GMAC_RXD3_M0
I/O
DOWN
GMAC_RXD3_M0/D4
MAC receive data/CIF_D4
3.3V
T19
CIF_D4_M0 / RGMII_RXD3_M0 / I2S0_MCLK_M1 / UART5_RTSN_M0 / I2C5_SCL_M1 / GPIO3_B0_D
198
GMAC_RXD0_M0
I/O
DOWN
GMAC_RXD0_M0/D10
MAC receive data/CIF_D10
3.3V
R20
CIF_D10_M0 / RGMII_RXD0_M0 / PDM_SDI2_M1 / SPI1_MOSI_M0 / GPIO3_B6_D
200
GMAC_RXD2_M0
I/O
DOWN
PWM11_M0
PWM11_M0/CIF_D3
3.3V
R18
CIF_D3_M0 / RGMII_RXD2_M0 / I2S0_SDI0_M1 / UART5_RX_M0 / CAN_TXD_M1 / PWM11_IR_M0 / GPIO3_A7_D
202
GMAC_RXDV_M0
I/O
DOWN
GMAC_RXDV_M0/D13
MAC receive data valid/CIF_D13
3.3V
M17
CIF_D13_M0 / RGMII_RXDV_M0 / PDM_SDI0_M1 / GPIO3_C1_D
204
GMAC_TXD0_M0
I/O
DOWN
GMAC_TXD0_M0/D7
MAC transmit data /CIF_D7
Core board internal series resistance 22R
3.3V
R19
CIF_D7_M0 / RGMII_TXD0_M0 / I2S0_SDO1_SDI3_M1 / UART4_CTSN_M0 / GPIO3_B3_D
206
GMAC_TXD2_M0
I/O
DOWN
GMAC_TXD2_M0/D5
MAC transmit data/CIF_D5
Core board internal series resistance 22R
3.3V
T20
CIF_D5_M0 / RGMII_TXD2_M0 / I2S0_SCLK_RX_M1 / UART5_CTSN_M0 / I2C5_SDA_M1 / GPIO3_B1_D
208
GMAC_TXD3_M0
I/O
DOWN
GMAC_TXD3_M0/D6
MAC transmit data/CIF_D6
Core board internal series resistance 22R
3.3V
N17
CIF_D6_M0 / RGMII_TXD3_M0 / I2S0_LRCK_RX_M1 / UART4_RTSN_M0 / GPIO3_B2_D
                                                                    - 11 -

       High-Performance AI Vision Core Board
210
GMAC_TXD1_M0
I/O
DOWN
GMAC_TXD1_M0/D8
MAC transmit data/CIF_D8
Core board internal series resistance 22R
3.3V
T21
CIF_D8_M0 / RGMII_TXD1_M0 / I2S0_SDO2_SDI2_M1 / SPI1_CS1N_M0 / GPIO3_B4_D
212
GMAC_TXEN_M0
I/O
DOWN
GMAC_TXEN_M0/D9
MAC transmit enable /CIF_D9
Core board internal series resistance 22R
3.3V
N18
CIF_D9_M0 / RGMII_TXEN_M0 / I2S0_SDO3_SDI1_M1 / SPI1_CS0N_M0 / GPIO3_B5_D
214
EPHY_PMEB
I/O
DOWN
EPHY_PMEB
PHY interrupt input,
3.3V
L20
I2S2_SCLK_M1 / UART5_RX_M1 / PWM2_M1 / SPI0_MISO_M2 / LCDC_D5 / GPIO2_B1_D
216
EPHY_RSTN
I/O
DOWN
EPHY_RSTN
phy reset output,active low
3.3V
K16
I2S2_LRCK_M1 / UART5_RTSN_M1 / PWM1_M1 / SPI0_CLK_M2 / LCDC_D6 / GPIO2_B2_D
218
RESET_KEY
I
RESET
system reset signal Input, External connection Reset key, active low
1.8V
W7
RESET_KEY
220
NC_35
NC
NC
NC_35
222
GND_33
G
GND
GND
GND_33
224
VCC_1V8
P
VCC_1V8
1.8V output,VCC_1V8 Total Max current 200mA(224PIN,225PIN same net)
1.8V
226
VCC3V3_SD
P
VCC3V3_SD
1.8V output,VCC_1V8 Total Max current 200mA(224PIN,225PIN same net)
3.3V
228
VCC1V2_DVDD
P
VCC1V2_DVDD
1.2V output,VCC1V2_DVDD Total Max current 300mA(228PIN,229PIN same net)
1.2V
230
VCC_3V3
P
VCC_3V3
3.3V output,VCC_3V3 Total Max current 400mA(230PIN,231PIN,234PIN,235PIN same net)
3.3V
232
VCC_RTC
P
VCC_RTC
3.3-5.0V input for RTC, Max current 50mA
5.0V
234
VCC_3V3
P
VCC_3V3
3.3V output,VCC_3V3 Total Max current 400mA(230PIN,231PIN,234PIN,235PIN same net)
3.3V
236
VCC2V8_AVDD
P
VCC2V8_AVDD
2.8V output,VCC2V8_AVDD Total Max current 300mA(236PIN,237PIN same net)
2.8V
238
VCC1V8_DOVDD
P
VCC1V8_DOVDD
1.8V output,VCC1V8_DOVDD Total Max current 300mA(238PIN,239PIN same net)
1.8V
240
NC_36
NC
NC
NC_36
242
NC_37
NC
NC
NC_37
244
GND_34
G
GND
Power ground
246
GND_35
G
GND
Power ground
248
GND_36
G
GND
Power ground
250
GND_37
G
GND
Power ground
252
VCC5V0_SYS_6
P
VCC5V0_SYS
Input Voltage 4.8V-5.5V
5.0V_IN
254
VCC5V0_SYS_7
P
VCC5V0_SYS
Input Voltage 4.8V-5.5V
5.0V_IN
256
VCC5V0_SYS_8
P
VCC5V0_SYS
Input Voltage 4.8V-5.5V
5.0V_IN
258
VCC5V0_SYS_9
P
VCC5V0_SYS
Input Voltage 4.8V-5.5V
5.0V_IN
260
VCC5V0_SYS_10
P
VCC5V0_SYS
Input Voltage 4.8V-5.5V
5.0V_IN
