experientials/ziloo/Hardware/801-T-USB/Ziloo 801 T-USB power circuit.pdf

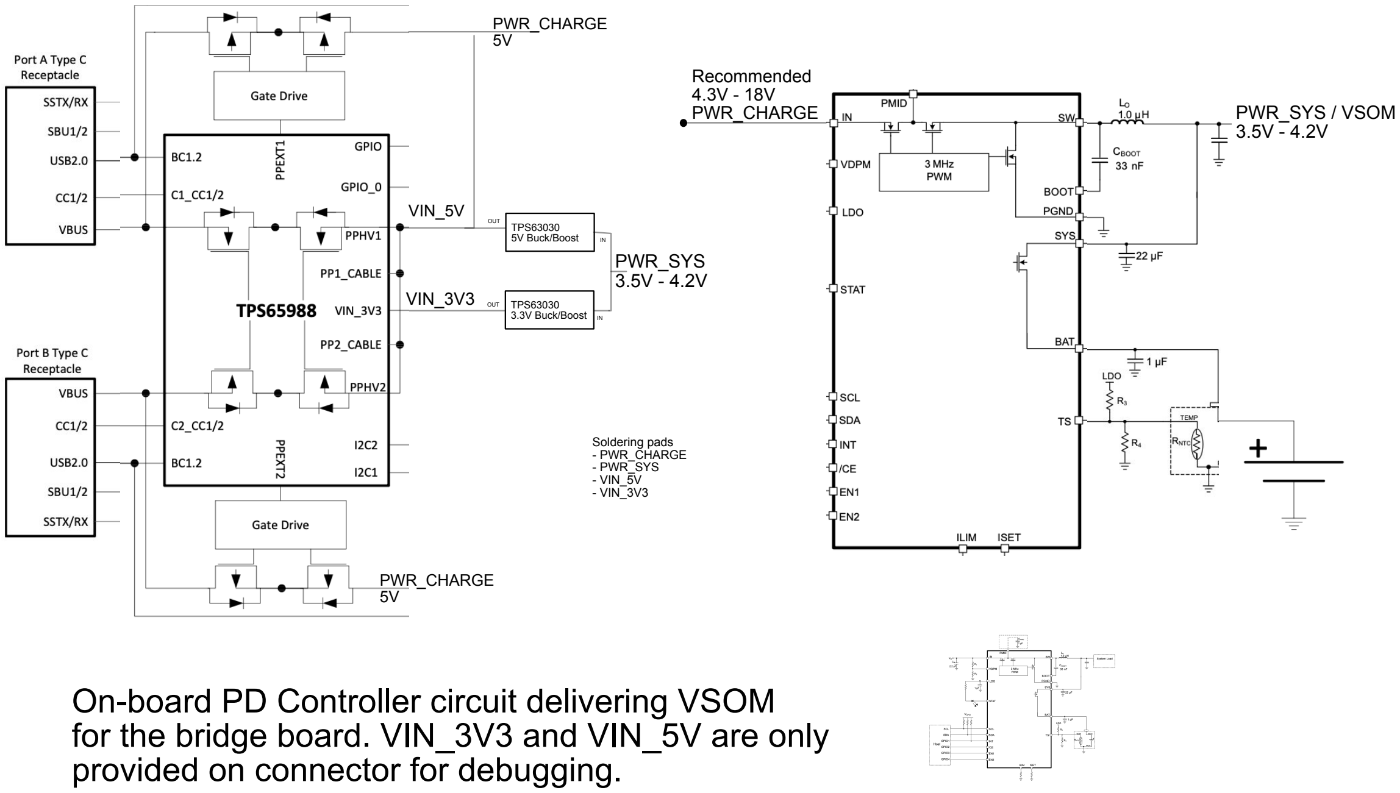
[picture p70: page 1]

TPS63030
3.3V Buck/Boost

TPS63030
5V Buck/Boost
PWR_SYS
3.5V - 4.2V

OUT

OUT

IN

IN

PWR_SYS / VSOM
3.5V - 4.2V

Recommended
4.3V - 18V
PWR_CHARGE

PWR_CHARGE
5V

PWR_CHARGE
5V

On-board PD Controller circuit delivering VSOM for the bridge board. VIN_3V3 and VIN_5V are only provided on connector for debugging.

VIN_5V

VIN_3V3

Soldering pads
- PWR_CHARGE
- PWR_SYS
- VIN_5V
- VIN_3V3
