experientials/ziloo/Hardware/909c/Ziloo 909b power circuit.pdf

TPS63030
3.3V Buck/Boost

TPS63030
5V Buck/Boost
PWR_SYS
3.5V - 4.2V

OUT

OUT

IN

IN

TPS63030
3.7V Buck/Boost

OUT

IN

Recommended
4.3V - 18V

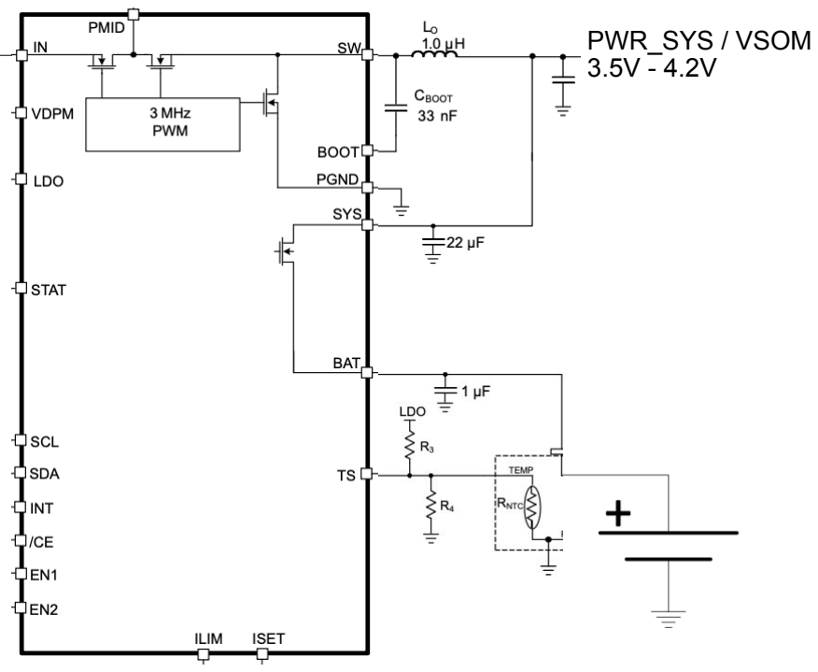
[picture p77: figure]
PWR_SYS / VSOM 3.5V - 4.2V

PWR_CHARGE

PWR_SYS / VSOM
3.7V

PWR_CHARGE
5V

dip

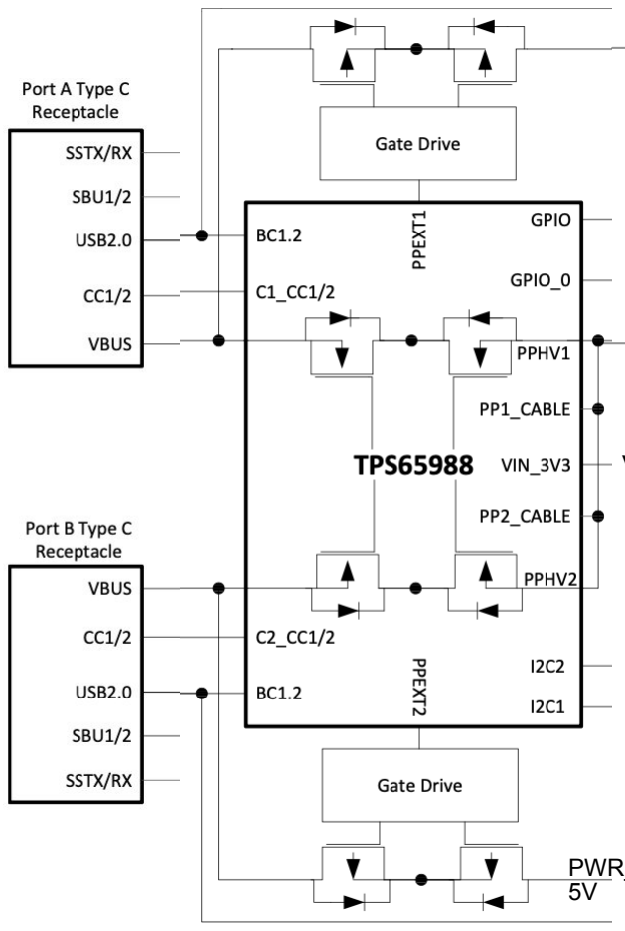
[picture p78: figure]

PWR_CHARGE

External. Battery Charger option (not included in the board design)

On-board PD Controller circuit delivering VSOM for the rest of the board.

VIN_5V

VIN_5V

VIN_3V3

VIN_3V3

Soldering pads
- PWR_CHARGE
- PWR_SYS
- VIN_5V
- VIN_3V3
