experientials/ziloo/Hardware/datasheets/Power/notes on power circuit.pdf

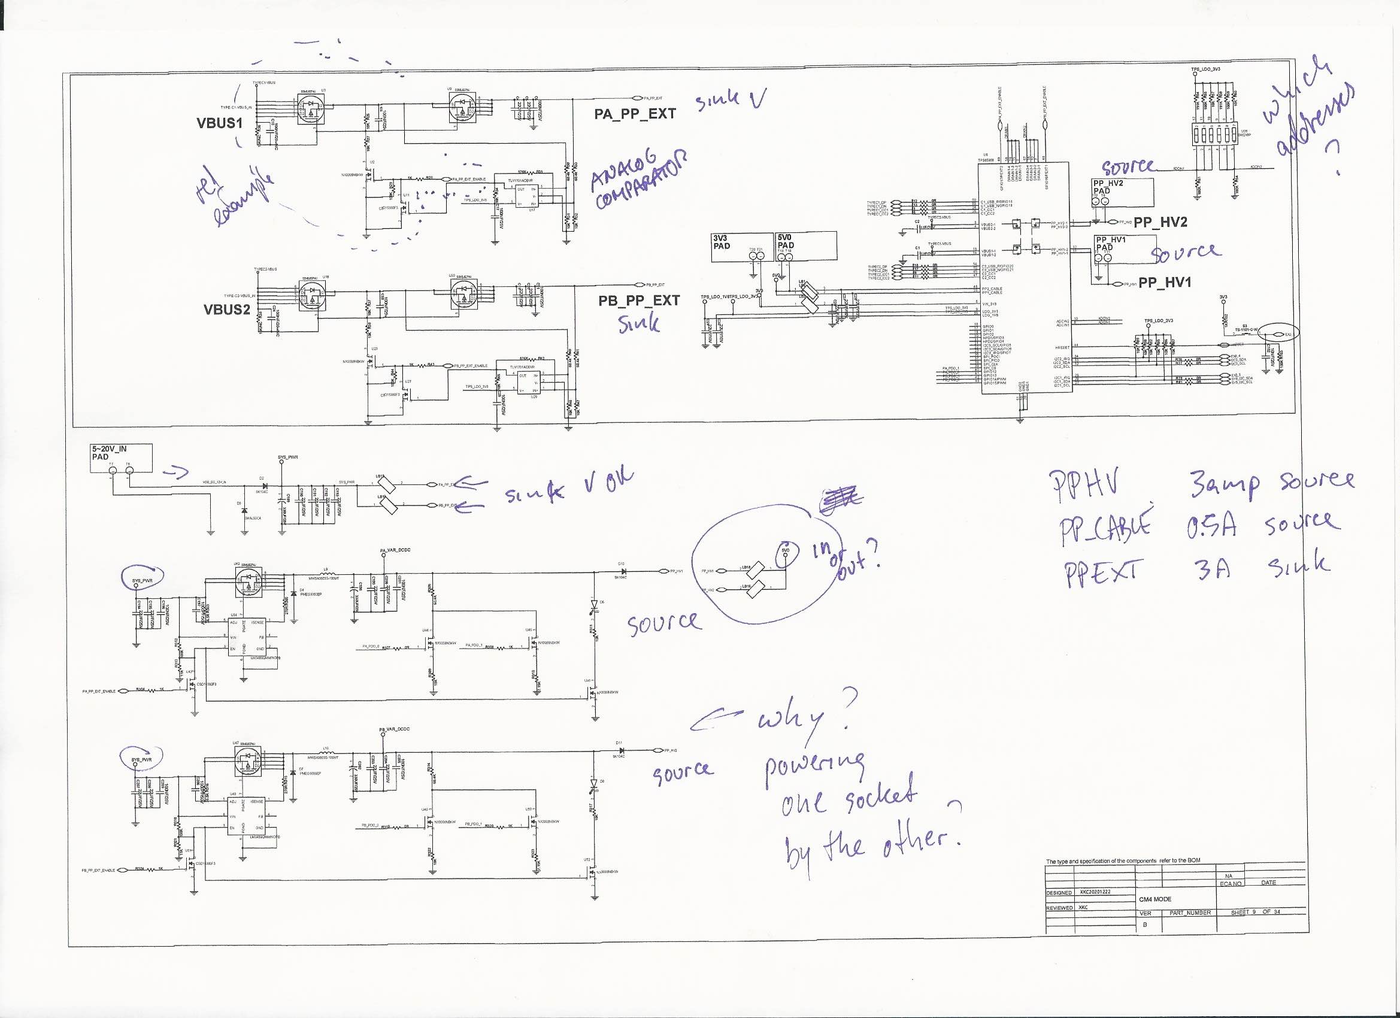
[picture p79: page 1]
