experientials/ziloo/Hardware/datasheets/JSD Lens list.xlsx

Model No | EFL(mm) | F/NO(Max) | FOV(°) |  |  | Distortion | Structure | Mounting | TTL (mm) | Diameter | Resolution | MAX IMAGE CIRCLE (mm)
 |  |  | D | H | V
JSD0125 | 2.09 | 2.4 | 142 | 125.5 | 77 | <-15.94% | 4G2P | M12*0.5P | 15 | Φ14 | 5MP | 1/3" OV4689
 |  |  | 134 | 110 | 86 | <19.8% |  |  |  |  |  | 1/3"AR0330
JSD0127 | 2.52 | 2.4 | 120 | 107.5 | 66.2 | <18% | 4G2P | M12*0.5P | 15.21 | Φ14 | 8MP | 1/3" OV4689 (∮6.40)
 |  |  | 118 | 106 | 65 | <-26% | 6E |  |  |  |  | 1/2.9" OV2778
JSD0128 | 2.00 | 2.4 | 112 | 102 | 70 | <2.7% | 4G2P | M12*0.5P | 18 | Φ15 | 8MP | 1/3" OV4689 /IMX274
 |  |  | 125 | 110 | 76 | <6% |  |  |  |  |  | 1/2.5" IMX274
JSD0129 | 2.52 | 2.0 | 120 | 107.5 | 66.2 | <18% | 4G2P | M12*0.5P | 15.21 | Φ14 | 8MP | 1/3" OV4689(∮6.40)
JSD0221 | 4.19 | 2.6 | 70 | 54.5 | 38 | <-6.77% | 5E | M7*0.35P | 11.87 | Φ8 | 1M | 1/4" (∮4.70)
JSD0228 | 1.6 | 2.0 | 180 | 141 | 85 | <-97.56% | 6E | M12*0.5P | 15.03 | Φ15.4 | 5MP | 1/4"(∮4.60)
JSD1001 | 5.7 | 3.0 | 60 | 52.5 | 30 | <1.97% | 5G | M8*0.35P /M12*0.5P | 10.29 | Φ6 | 5MP | 1/3" OV4689
 |  |  | 44.6 | 37.8 | 23.8 | <1.03% |  |  |  |  |  | 1/4"OV9281
 |  |  | 63 | 56 | 32 | <-6.4% |  |  |  |  |  | 1/2.7" AR0230
JSD1002 | 10.36 | 3.0 | 40 | 34 | 30 | <1% | 5G | M8*0.5P /M7*0.35P /M12*P0.5 | 16.03 |  | 8MP | 1/3" OV4689
JSD1005 | 17.80 | 2.0 | 20 | 17 | 10 | <-0.15% | 2G2P | M12*0.5P | 20 | φ13 | 2MP | 1/2.8"(∮6.7)
JSD1006 | 10.90 | 4.0 | 32 | 26 | 18 | <0.2% | 2G2P | M12*0.5P | 13.29 |  | 2MP | 1/2.8"(∮6.7)
JSD1224 | 1.17 | 2.4 | 120 | 96 | 72 | <-10.52% | 4E | M7*0.35P | 9.74 | φ10 | 5MP | 1/6"(∮3.2)
JSD1225 | 2.07 | 2.6 | 110 | 92 | 71 | <6.4% | 4E | M7*0.35P /M8*P0.35 /M12*0.5P | 10.7 | φ10 | 5MP | 1/4" OV5640
 |  |  | 108 | 96 | 62 | <5.34% |  |  |  |  |  | 1/4" AR0144
JSD1226 | 2.30 | 2.4 | 90 | 72 | 60 | <-1% | 2G2P | M7*P0.35 M8*0.5P M12x0.5 | 10.47 | φ11.5 | 2MP | 1/4"(∮5.30)
JSD1314 | 2.63 | 2.6 | 120 | 103.5 | 68 | <21.48% | 4G3P | M12*0.5P | 21.14 | Φ14 | 16MP | 1/2.5" IMX317
JSD1326 | 3.56 | 2.5 | 105 | 88 | 69 | <-16.5% | 7E | M12*0.5P | 22.8 | φ14 | 16MP | 1/2.3" IMX117
 |  |  | 107 | 89 | 70 | <-17.6% |  |  |  |  |  | 1/2.3" OV12896
JSD1328 | 3.90 | 2.8 | 90 | 77.5 | 61 | <0.5% | 4G2P | M12*0.5P | 22.15 | φ14 | 12MP | 1/2.33"
JSD1329 | 4.30 | 2.8 | 82 | 72 | 56 | <0.58% | 4G2P | M12*0.5P | 22 | φ14 | 16MP | 1/2.3"
 |  |  | 79 | 71 | 43 | <0.56% |  |  |  |  |  | 1/2.5" IMX317
JSD1521 | 1.60 | 2.8 | 160 | 120 | 100 | <56% | 1G3P | M7*0.35P /M12*P0.5 /M8*P0.5 | 10.46 | φ10 | 1MP | 1/3" AR0330
JSD1525 | 2.80 | 2.6 | 160 | 124.8 | 67 | <-38% | 5E | M8*P0.5 | 11.51 | φ10 | 2MP | 1/2.7"(∮6.7)
JSD1526 | 2.60 | 2.7 | 160 | 124 | 67 | <-39% | 6E | M12 | 11.4 | Φ14 | 2MP | 1/2.7"(∮6.7)
JSD1529 | 1.90 | 2.0 | 160 | 120 | 100 | <-26% | 5P | M7*P0.35 | 11 | 10 | 2MP | 1/3"
JSD1822 | 1.38 | 2.2 | 166 | 135 | 102 | <-44% | 2G2P | M8*0.35P /M12*P0.5 | 9.9 | φ12.5 | VGA | 1/4"(∮4.80)
JSD2008 | 2.05 | 2.0 | 134 | 114 | 61 | <-54.78% | 5G | M12*0.5P | 16.8 | φ14 | 2MP | 1/4" NT99142
 |  |  | 140 | 110 | 80 | <-56% |  |  |  |  |  | 1/4"
 |  |  | 160 | 120 | 95 | <-34% |  |  |  |  |  | 1/4" OV5642
 |  |  | 80 | 62 | 50 |  |  | M7*0.35P |  |  |  | 1/6"MT9M114
JSD2010 | 2.5 | 2.6 | 123 | 91 | 63.5 | <-49% | 3G1P | M7*0.35P /M12*P0.5 | 12.5 | φ10 | 2MP | 1/4" OV5640
JSD2011 | 2.28 | 2.4 | 130 | 110 | 95 | <-46% | 3G1P | M7*0.35P M8*0.35P M10*0.5P M12*0.5P | 10 | φ8 | 2MP | 1/4" (∮5.30)OV2643
 |  |  | 127 | 102.5 | 62 | <-49.95% |  |  |  |  |  | 1/4" OV9281
JSD2012 | 2.09 | 2.6 | 135 | 112.6 | 69 | <-54% | 3G1P | M7*0.35P M8*0.35P M12*0.5P | 11.9 | Φ10 | 2MP | 1/4" OV9281
 |  |  | 152 | 116 | 82.5 | <-70% |  |  |  |  |  | 1/3.7" OV7956
JSD2017 | 1.90 | 2.0 | 152 | 125 | 94 | <-25% | 7E | M8*P0.5 M12*0.5 | 15.99 | φ13 | 8MP | 1/3.2" ISX017
 |  |  | 156 | 127 | 97 | <-27% |  |  |  |  |  | 1/3.2" IMX179
JSD2018 | 2.20 | 2.8 | 134 | 116 | 80 | 55.00% | 6G | M12*0.5P | 28 | φ14 | 1MP | 1/4"OV9712
JSD2019 | 2.11 | 2.4 | 128 | 110 | 70 | <14% | 6E | M12*0.5P | 16.7 | φ14 | 8MP | 1/2.8" IMX335 (∮6.8)
 |  |  | 125 | 113 | 73 | <11% |  |  |  |  |  | 1/3" OV4689
JSD2020 | 2.20 | 1.8 | 196 | 155 | 98 | <-71.8% | 6G | M12*0.5P | 26.9 | φ25 | 5MP | 1/3"(∮5.60)AR0330
 |  |  | 134 | 105.6 | 78.6 | <-53.5% |  |  |  |  |  | 1/4" OV2643
 |  |  | 137 | 108 | 80 | <-55.3% |  |  |  |  |  | 1/4" OV5640
JSD2157 | 2.35 | 2.0 | 168 | 148 | 80 | <-34.3% | 6G | M12*0.5P | 22 | φ17 | 5MP | 1/2.7 OV2735
JSD2158 | 2.73 | 2.0 | 171.2 | 137.2 | 70.8 | <-21.4% | 6G | M12*P0.5 | 17.45 | 14 | 5MP | 1/2.7 AR0230
JSD2516 | 2.80 | 2.8 | 160 | 110 | 80 | / | 5G | M12*0.5P | 15 | φ14 | 5MP | 1/2.5"(∮7.30)
JSD2528 | 2.80 | 2.8 | 126 | 110 | 61 | <-46.6% | 6G | M12*0.5P | 22.5 | φ17.5 | 5MP | 1/3" AR0330
 |  |  | 155 | 123 | 91 | <-70.5% |  |  |  |  |  | 1/2.5" MI5100
 |  |  | 143 | 125 | 70 | <-58.8% |  |  |  |  |  | 1/2.7"
JSD2529 | 2.66 | 2.0 | 160 | 134 | 71 | <-20.9% | 6G | M12*0.5P | 22.29 | Φ17.5 | 4MP | 1/2.7 OV2710
 |  |  | 146 | 123 | 66.5 | <-18.8% |  |  |  |  |  | 1/3" OV4689
JSD2623 | 2.60 | 2.5 | 112 | 100 | 80 | <3.28% | 5G2P | M12*0.5P | 23 | Φ18 | 8MP | 1/2.5" IMX274
JSD2624 | 2.60 | 2.4 | 82.6 | 73.5 | 50 | <-1% | 2G2P | M12*0.5P /M7*P0.35 | 15 | φ14 | 2MP | 1/4" OV9712
 |  |  | 81.9 | 72.9 | 49.2 |  |  |  |  |  |  | 1/4" AR0144
JSD2625 | 2.60 | 2.4 | 112 | 100 | 80 | <3.28% | 4G2P | M12*0.5P | 22 | Φ18 | 8MP | 1/2.5" IMX274
JSD2628 | 2.80 | 2.8 | 84 | 75 | 58 | <-0.35% | 2G3P | M12*0.5P | 20 | φ14 | 5MP | 1/4" OV5648
JSD2629 | 2.20 | 1.8 | 124 | 112 | 82 | <-4% | 8E | M12*0.5P | 24 | Φ22 | 8MP | 1/2.5"(∮7.5) IMX274
JSD2631 | 2.70 | 2.8 | 113 | 100 | 82.8 | <-1.5% | 5G2P | M12*P0.5 | 22.5 | φ16 | 12MP | 1/2.3"∮8.3
JSD2635 | 4.40 | 2.4 | 74 | 66 | 40 | <0.38% | 4E | M8*P0.35 | 7.04 | φ7.04 | 2MP | 1/2.7“OV2733
 |  |  | 70 | 62 | 38 |  |  |  |  |  |  | 1/2.9"IMX323
 |  |  | 72 | 64 | 39 |  |  |  |  |  |  | 1/2.8"IMX307
JSD2636 | 1.80 | 2.8 | 132 | 123 | 86 | <-6.4% | 7E | M12*P0.5 | 24.43 | 17.5 | 8MP | 1/2.8" (∮7)
JSD2639 | 2.10 | 2.4 | 120 | 112 | 75 | <-4% | 6E | M12*P0.5 | 24.5 | φ17.5 | 8MP | 1/2.8“ IMX415
JSD2640 | 2.47 | 4.0 | 85 | 72 | 56.5 | <1.05% | 1G3P | M7*0.35P | 10.75 | Φ8 | 5MP | 1/4" OV5640
JSD2728 | 2.70 | 2.8 | 97 | 84 | 66 | <-3.4% | 3G2P | M12*0.5P | 16.6 | φ14 | 2MP | 1/3.2"(∮5.70)MT9D111
 |  |  | 80 | 71.5 | 43.5 | <1.2% |  |  |  |  |  | 1/4" NT99142
JSD2733 | 3.25 | 2.6 | 100.8 | 87.6 | 70.9 | <-0.6% | 4G2P | M12*P0.5 | 22.5 | φ14 | 12MP | 1/2.3"(φ8.3)IMX377
JSD2828 | 2.80 | 2.8 | 105 | 94 | 60 | <-4% | 2G3P | M12*0.5P | 13.5 | φ14 | 5MP | 1/2.7"AR0330
JSD2928 | 2.91 | 2.4 | 113.5 | 90 | 67 | <-13.31% | 5E | M7*0.35P /M6.5*P0.35 /M12*P0.5 | 9.5 | φ8 | 8M | 1/3.2" OV8865
 |  |  | 122.6 | 106.6 | 59.4 | <-20% | 5E |  |  |  |  | 1/3" OV4689
JSD3006 | 2.26 | 2.4 | 134 | 108 | 63 | <-37.6% | 5G | M7*0.35P /M8*P0.5 /M12*P0.5 | 13.1 | φ10 | 5MP | 1/4" OV9712
 |  |  | 130 | 98 | 71 | <-32.9 |  |  |  |  |  | 1/4" OV5640
 |  |  | 130 | 107 | 58 | <-36% |  |  |  |  |  | 1/4" NT99142
JSD3007 | 3.50 | 2.4 | 122 | 103.5 | 55 | <-46.7% | 3G1P | M7*0.35P | 15.22 | φ10 | 2MP | 1/2.7" OV2710
JSD3023 | 2.98 | 1.8 | 140 | 114 | 60 | <-16.2% | 6G | M12*0.5P | 16.2 | φ17.5 | 3MP | 1/2.9" IMX322
 |  |  | 154 | 126 | 64.5 |  |  |  |  |  |  | 1/2.7" OV2710
 |  |  | 138 | 115 | 60 |  |  |  |  |  |  | 1/3" OV4689
JSD3026 | 3.13 | 1.9 | 124 | 102.5 | 56 | <18% | 6G | M12*0.5P | 21.6 | φ14 | 5MP | 1/3" OV4689
JSD3028 | 0.90 | 2.8 | 154 | 115 | 90 | 25.9%% | 3P | M7*0.35 | 7.6 | φ9.4 | VGA | 1/6.5"GC0308
JSD3128 | 3.15 | 2.8 | 146 | 112 | 82 | <-20% | 4G1P | M12*0.5P | 21 | φ17.5 | 5MP | 1/2.5" (∮8.0)MI5100
 |  |  | 119 | 92 | 67 | <-17.4% |  |  |  |  |  | 1/3"H65
JSD3135 | 3.00 | 2.4 | 140 | 121 | 63 | 46.00% | 5G | M12*0.5P | 17.2 | φ14 | 3MP | 1/2.7"OV2710
 |  |  | 126 | 101 | 56 |  |  |  |  |  |  | 1/3"AR0330
 |  |  | 120 | 100 | 54 |  |  |  |  |  |  | 1/3"NT99230
JSD3137 | 3.10 | 2.8 | 160 | 116 | 60 | <28% | 5G | M12*0.5P | 14.63 | φ14 | 5MP | 1/3" OV4689
JSD3420 | 4.42 | 2.4 | 73.5 | 65.5 | 40 | <0.5% | 4E | M8*0.35P /M9*P0.5 /M12*P0.5 | 8.61 | φ1.84 | 2MP | 1/2.7" OV2735 (∮6.8)
 |  |  | 70.2 | 62 | 37.4 |  |  |  |  |  |  | 1/2.9" IMX323 (∮6.8)
JSD3427 | 3.18 | 2.8 | 89 | 80.5 | 51.2 | <0.95% | 2G2P | M12*0.5P | 15.6 | Φ14 | 5MP | 1/3"OV4689
 |  |  | 91.8 | 84 | 54 | <0.95% |  |  |  |  |  | 1/2.7"AR0230
 |  |  | 70 | 60 | 46 | <0.9% |  |  |  |  |  | 1/4" MT9P111
JSD3428 | 3.60 | 2.8 | 96 | 80 | 65 | 1.00% | 2G2P | M12*0.5P | 19 | φ14 | 5MP | 1/2.5"(∮8.00)MI5100
JSD3429 | 2.74 | 2.8 | 98.5 | 90 | 58 | <1.53% | 2G2P | M10*P0.35 /M12*0.5P | 15.6 | Φ14 | 5MP | 1/3" OV4689
 |  |  | 102.6 | 94.3 | 61 | <2.4% |  |  |  |  |  | 1/2.7" OV2710
 |  |  | 100 | 90 | 60 | <2% |  |  |  |  |  | 1/2.9" OV2718
JSD3522 | 4.70 | 2.4 | 68 | 61 | 36 | <-0.5% | 1G4P | M12*0.5P | 14.3 | Φ14 | 5MP | 1/2.8" IMX307
 |  |  | 70 | 63 | 38 | <-0.5% |  |  |  |  |  | 1/2.7" (∮7.0)
JSD3527 | 3.00 | 2.6 | 100 | 86 | 70 | <1% | 5E | M12*P0.5 | 15.58 | φ14 | 5MP | 1/2.5"MI5100
 |  |  | 95 | 87 | 56 | <0.93% |  |  |  |  |  | 1/2.7"OV2710
 |  |  | 92 | 83 | 54 | <0.9% |  |  |  |  |  | 1/3"OV4689
 |  |  | 89 | 76 | 61 | <0.9% |  |  |  |  |  | 1/3"AR0130
JSD3528 | 3.14 | 2.4 | 100 | 89 | 57 | <3.9% | 6E | M12*0.5P | 22 | Φ14 | 16MP | 1/2.5"IMX317
 |  |  | 86.5 | 76 | 47.3 | <3.9% |  |  |  |  |  | 1/3" AR0330
 |  |  | 91 | 82 | 51.4 | <4% |  |  |  |  |  | 1/2.8" IMX291
JSD3808 | 2.25 | 2.0 | 116 | 105 | 68 | <-6.2% | 7E | M12*0.5P | 23.49 | Φ18 | 8MP | 1/3"OV4689
JSD3920 | 3.60 | 2.0 | 90.5 | 82.5 | 52.2 | <1.5% | 3G2P | M12*0.5P | 16.3 | Φ14 | 2MP | 1/2.7"AR0230
 |  |  | 83.0 | 74.8 | 46.3 | <1% |  |  |  |  |  | 1/3" AR0330
JSD3921 | 4.50 | 3.5 | 77 | 62 | 46 | <0.5% | 3G2P | M12*0.5P | 21.5 | Φ14 | 5MP | 1/2.7"(∮7.20)
JSD3922 | 3.00 | 2.4 | 100 | 85 | 66 | <-1.0% | 5E | M12*0.5P | 17.5 | Φ14 | 5MP | 1/2.7"(∮7.00)
JSD3925 | 3.05 | 2.6 | 122 | 110 | 70 | <-10% | 3G2P | M12*0.5P | 17 | Φ14 | 2MP | 1/2"(∮8.8)
JSD3928 | 3.90 | 2.8 | 96 | 80 | 60 | <0.25% | 2G2P | M12*0.5P | 22 | φ14 | 5MP | 1/2.5"(∮8.00)MI5100
 |  |  | 73 | 66 | 40 | <1.26% |  |  |  |  |  | 1/3"AR0330
JSD3936 | 4.18 | 3.0 | 83 | 68 | 54 | <0.45% | 3G2P | M12*0.5P | 21.5 | φ14 | 5M | 1/2.5"MI5100
JSD4008 | 7.15 | 2.5 | 57 | 50 | 35 | <-1.5% | 4E | M12*0.5P | 11.22 | φ14 | 5MP | 1/2.5"
JSD4011 | 0.95 | 2.0 | 160 | 120 | 100 | <-8.5% | 2G2P | M7*0.35P M8*0.5P M12*0.5P | 9.29 | φ10 | VGA | 1/4" OV7725
 |  |  | 120 | 90 | 65 |  |  |  |  |  |  | 1/5" OV7740
JSD4012 | 1.05 | 2.4 | 145 | 123.5 | 100 | <-30.55% | 1G3P | M7*0.35P /M8*P0.5 | 8.69 | Φ10 | 2MP | 1/4" (∮4.80)
JSD4013 | 2.76 | 2.4 | 130 | 101 | 90 | <-10% | 5G | M7*0.35P | 11.91 | φ10 | 2MP | 1/4"
 |  |  | 106 | 86.6 | 51.7 | <-38.3% |  |  | 11.91 | φ11 |  | 1/4"(∮5.30)OV9712
JSD4017 | 1.50 | 2.4 | 144 | 120 | 93 | <-24% | 4E | M7*0.35P | 9.51 | φ10 | VGA | 1/4"(∮5.10)OV7725
 |  |  | 90 | 74 | 58 | <-4.4% |  |  |  |  |  | 1/6.5"GC0308
JSD4018 | 1.15 | 2.4 | 135 | 123 | 93 | 9.00% | 2G2P | M12*0.5P | 13.86 | φ15 | VGA | 1/4"OV9713
 |  |  | 115 | 100 | 82 |  |  |  |  |  |  | 1/5" OV7725
JSD4689 | 2.84 | 2.4 | 138 | 120 | 66 | -40.70% | 6G | M12*0.5P | 22.8 | φ17.5 | 5MP | 1/3" OV5653
 |  |  | 128 | 110 | 62 | -33.80% |  |  |  |  |  | 1/3" OV4689
 |  |  | 125 | 103 | 57 | -30.00% |  |  |  |  |  | 1/4" OV5640
JSD5011 | 1.70 | 2.0 | 116 | 100 | 85 | <-3.5% | 2G2P | M7*0.35P | 10.31 | φ10 | VGA | 1/5" OV7740
JSD5012 | 0.90 | 2.0 | 150 | 120 | 85 | 48.00% | 2G2P | M8*0.5P /M7*0.35P | 10.51 | φ11.5 | VGA | 1/5" OV7740
 |  |  | 125 | 108 | 89 |  |  |  |  |  |  | 1/6.5"GC0308
JSD5019 | 5.00 | 2.4 | 65 | 52 | 39 | <-0.94% | 2G3P | M12*0.5P | 14 | φ14 | 2MP | 1/2.8"(∮6.6) IMX307
JSD5021 | 1.85 | 1.8 | 90 | 72 | 60 | <-2.5% | 2G2P | M8*0.5P | 11.12 | φ14 | VGA | 1/5" OV7740
JSD5037 | 3.00 | 3.0 | 120 | 90 | 80 | <-18.5% | 6G | M12*0.5P | 20.58 | φ14 | 5MP | 1/3.2" (∮6.0)OV5653
JSD5038 | 6.00 | 2.4 | 56 | 50 | 29 | <-0.5% | 5E | M12*P0.5 | 14 | 14 | 2MP | 1/2.8" IMX307
JSD5108 | 2.90 | 2.2 | 100 | 90 | 70 | <1.5% | 6E | M9*0.35P /M12*P0.5 | 15 | φ12.5 φ14 | 5MP | 1/2.5 APTINA0521
JSD5500 | 1.70 | 2.4 | 166 | 126 | 92 | <19.13% | 2G3P | M8*0.35P /M7*P0.35 /M12*P0.5 | 10 | φ12.5 | 5MP | 1/4" OV5640
 |  |  | 121 | 96 | 72.5 | <7.37% |  |  |  |  |  | 1/5" GC2145
 |  |  | 104 | 83.5 | 62.5 | <6.22% |  |  |  |  |  | 1/6"MT9M114
 |  |  | 162 | 131 | 81 | <18.8% |  |  |  |  |  | 1/4" AR0144
JSD5501 | 1.39 | 2.4 | 166 | 138 | 105 | <-79.8% | 2G3P | M8*0.35P /M7*P0.35 | 9.5 | φ12.5 | 5MP | 1/4" OV5640
 |  |  | 104 | 83.5 | 62.5 | <11.54% |  |  |  |  |  | 1/6" MT9M114
JSD6010 | 6.00 | 2.8 | 78 | 60 | 40 | <0.82% | 3G2P | M12*0.5P | 23.1 | φ16 | 2MP | 1/1.8"(∮9.0)
JSD6016 | 4.10 | 1.8 | 92 | 80 | 48 | <-10% | 6G | M12*0.5P | 23.12 | φ14 | 2MP | 1/2.7"(∮6.6)
JSD6068 | 3.13 | 2.6 | 147 | 120 | 62.9 | <-68% | 4G | M12*P0.5 | 20.68 | 14 | 3MP | 1/2.7"
JSD6069 | 3.05 | 2.4 | 140 | 116 | 60 | <-19.5% | 5G | M12*0.5P | 17.75 | φ14 | 2MP | 1/2.7"
JSD6886 | 0.85 | 2.6 | 140 | 110 | 80 | 29.00% | 4P | M7*0.35P | 7.43 | φ10 | VGA | 1/9" (∮1.90) OV7675
JSD8015 | 3.48 | 2.8 | 79 | 64 | 52 | <0.024% | 2G3P | M12*0.5P | 21.5 | φ16 | 13MP | 1/3.06" (∮5.9) IMX214
JSD8016 | 1.43 | 2.0 | 200 | 200 | 142 | <-122% | 6G | M12*0.5P | 14.5 | φ14 |  | 1/3" (∮6.3) OV4689
 |  |  | 200 | 186 | 133 | <-106% |  |  |  |  |  | 1/4" OV7725
JSD8018 | 1.29 | 2.4 | 192 | 192 | 113 | <-115% | 8G | M12*0.5P | 17.5 | φ14 |  | 1/4" (∮3.65) OV9712
 |  |  | 210 | 187 | 150 | <-134% |  |  |  |  |  | 1/4"
JSD9200 | 0.81 | 1.1 | 140 | 126 | 112 | <5.6% | 1G3P | M8*0.35P | 12.01 | φ14 | VGA | 1/5"(∮4.20)
JSD9060 | 10.00 | 6.0 | 35 | 28 | 21 | 0.10% | 2G2P | M12*5P | 13.22 | φ14 | 8M | 1/2.8" (IMX335)
 |  |  | 47 | 41 | 24 | <0.4% |  |  |  |  |  | 1/1.8"(∮OS08A20)
