experientials/ziloo/Face/909-inverted.jpg

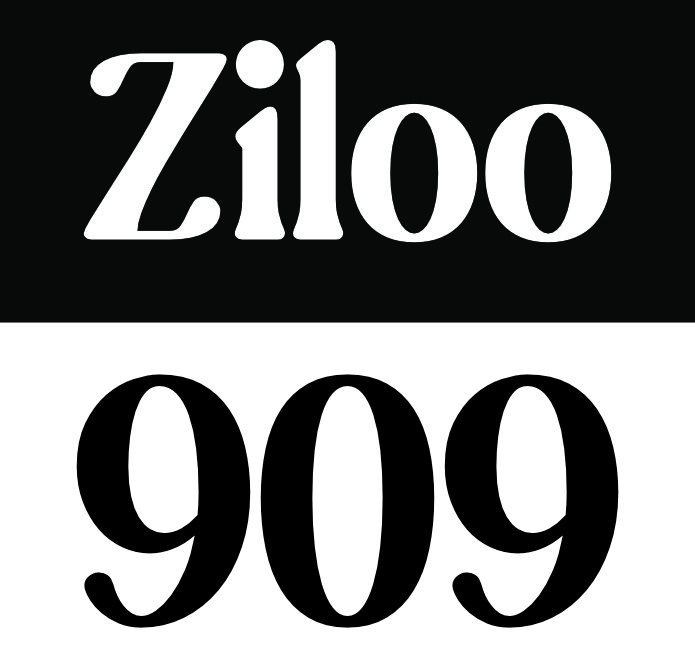
Face/909-inverted.jpg
