experientials/ziloo/Hardware/201/OV2735-combined-module/IR-version-mounting.png

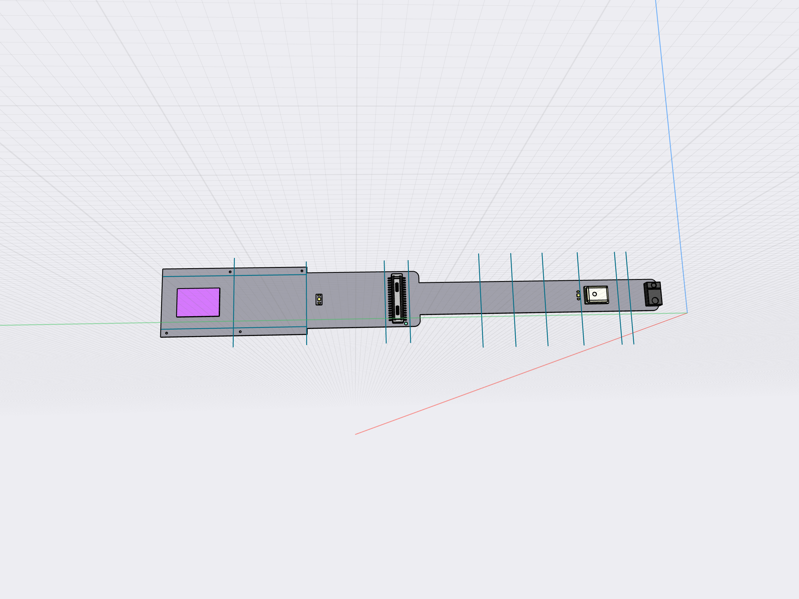
Hardware/201/OV2735-combined-module/IR-version-mounting.png
