experientials/ziloo/Hardware/201/OV2735-combined-module/OV2735-module.png

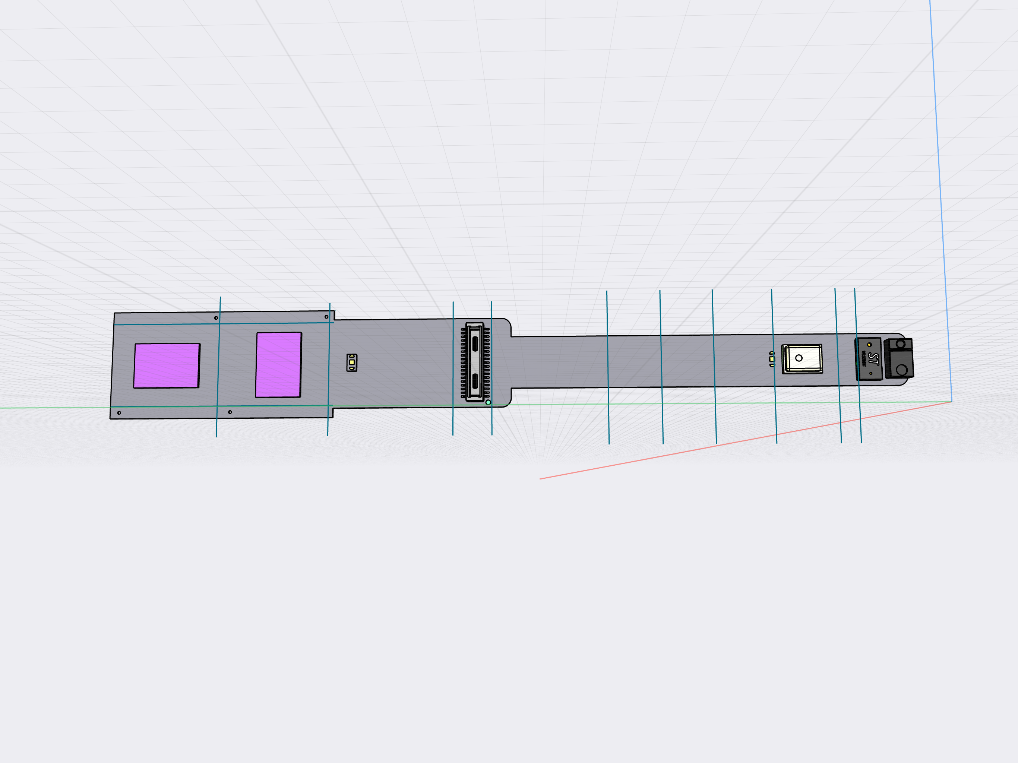
Hardware/201/OV2735-combined-module/OV2735-module.png
