experientials/ziloo/Hardware/201/OV2735-module/holders/Focusafe BLH027.bmp

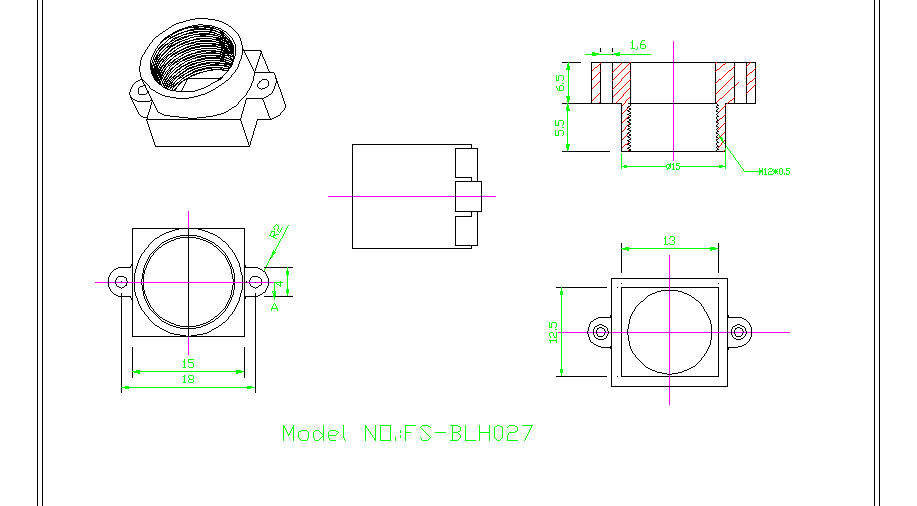
Hardware/201/OV2735-module/holders/Focusafe BLH027.bmp
