experientials/ziloo/Hardware/201/OV2735-module/lenses/CA1308C-holder.jpg

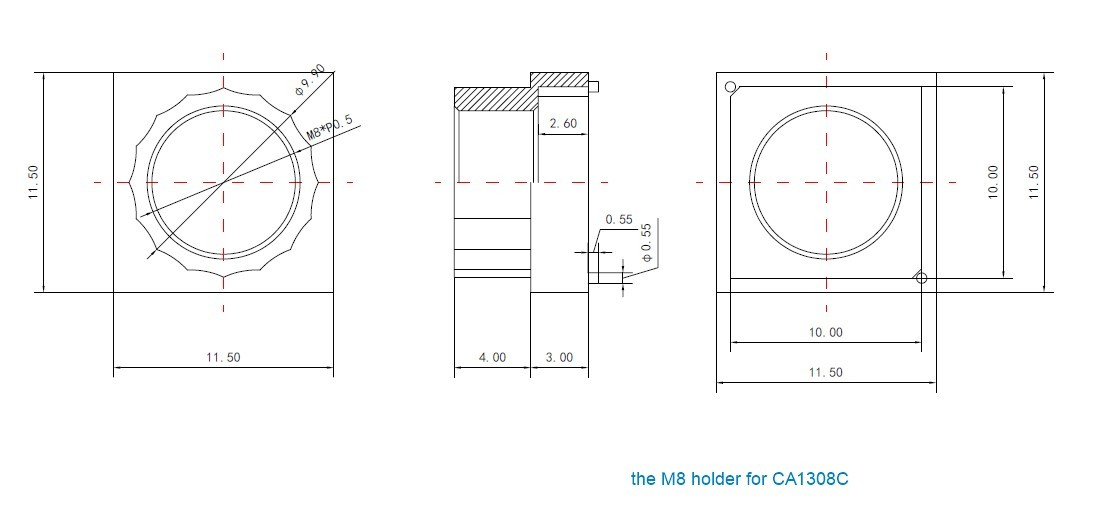
Hardware/201/OV2735-module/lenses/CA1308C-holder.jpg
