experientials/ziloo/Hardware/201/OV2735-module/lenses/CW-BL15620-5MP.jpg

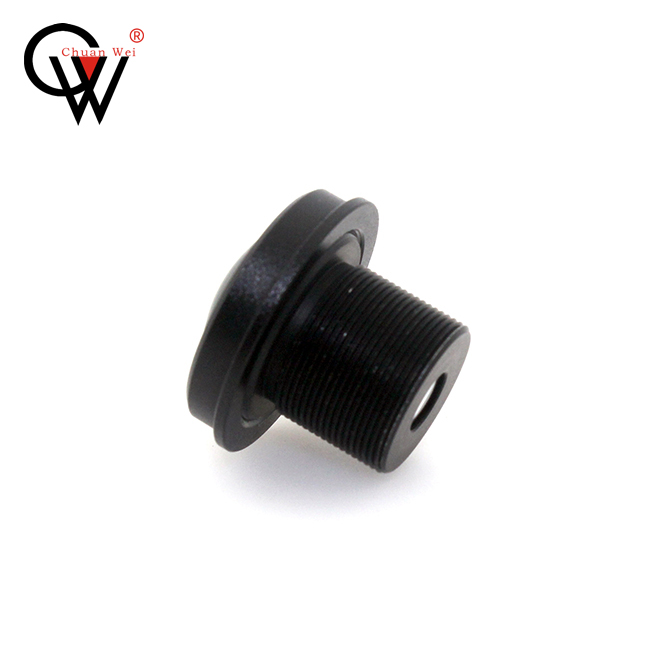
Hardware/201/OV2735-module/lenses/CW-BL15620-5MP.jpg
