experientials/ziloo/Hardware/201/OV2735-module/lenses/FS2328B13M8.png

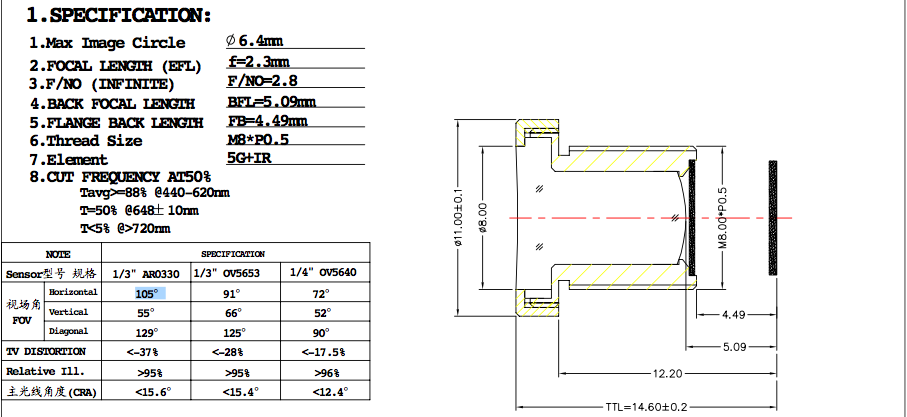
Hardware/201/OV2735-module/lenses/FS2328B13M8.png
