experientials/ziloo/Hardware/201/OV2735-module/lenses/HK-8189-823-1 HTB1yuIFX5DxK1Rjy1zc761GeXXaL.png

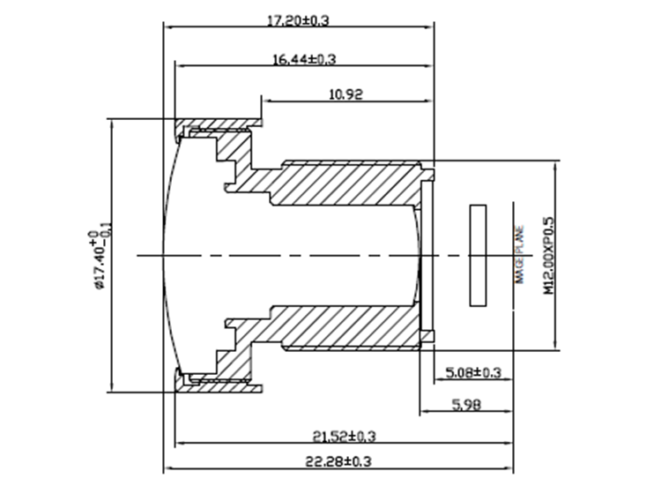
Hardware/201/OV2735-module/lenses/HK-8189-823-1 HTB1yuIFX5DxK1Rjy1zc761GeXXaL.png
