experientials/ziloo/Hardware/201/OV2735-module/lenses/M7 JSD1529-A1 H0a379630da49466e83e74935b392cd56l.jpg

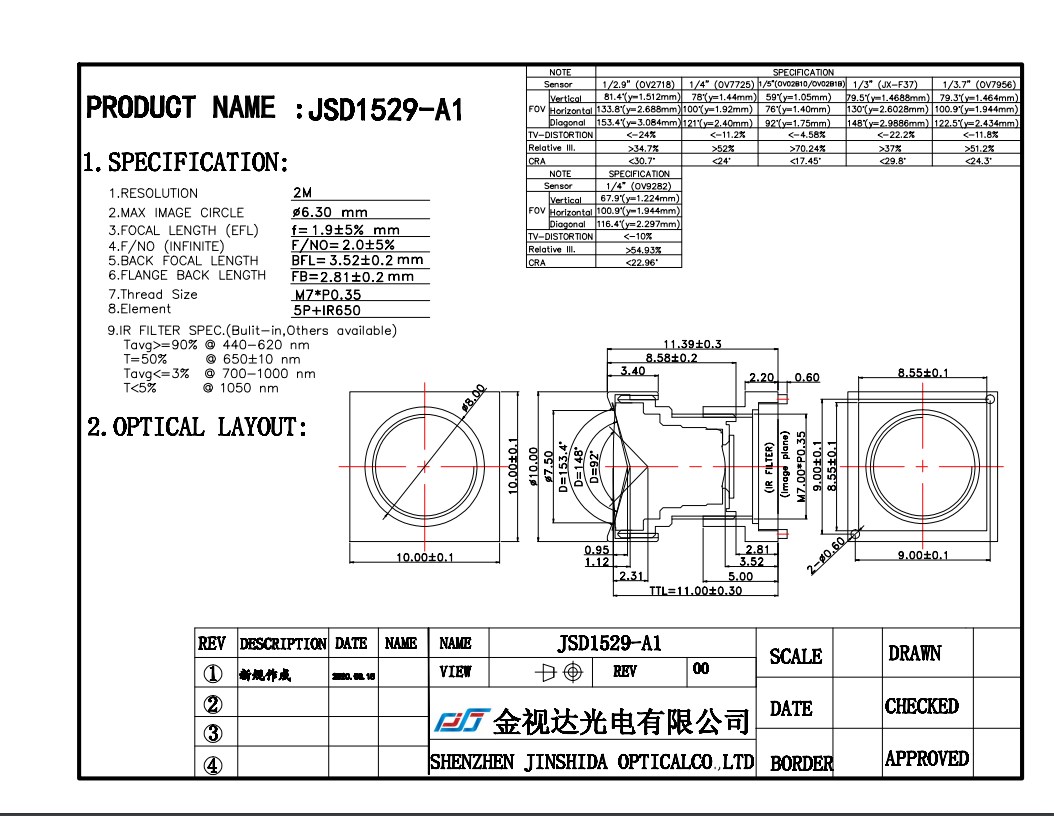
Hardware/201/OV2735-module/lenses/M7 JSD1529-A1 H0a379630da49466e83e74935b392cd56l.jpg
