experientials/ziloo/Hardware/201/OV2735-module/lenses/TREEYE-CW-BL15620-5MP.jpeg

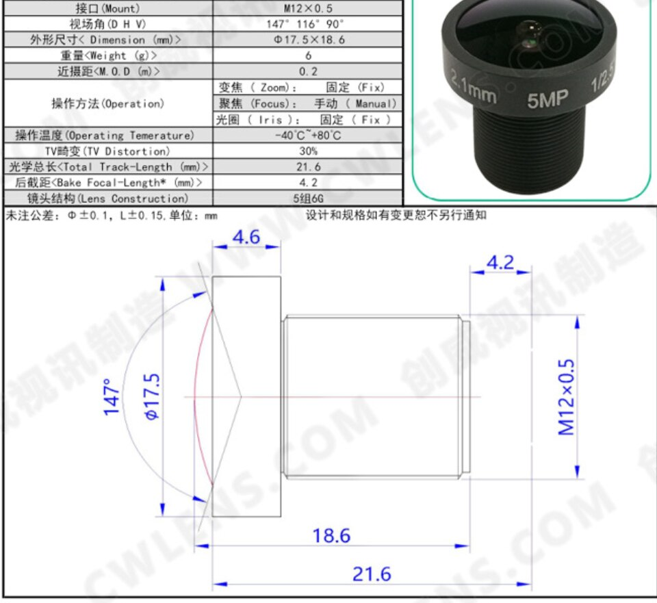
Hardware/201/OV2735-module/lenses/TREEYE-CW-BL15620-5MP.jpeg
