experientials/ziloo/Hardware/801-T-USB/801 T-USB above.png

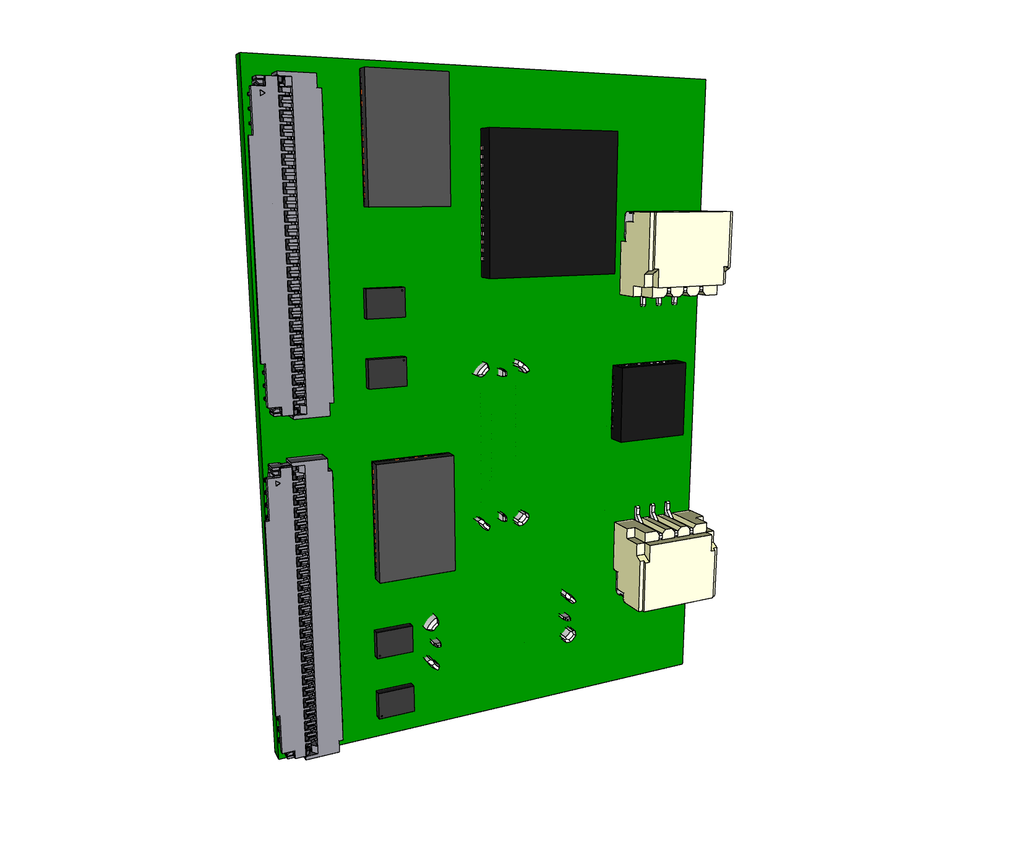
Hardware/801-T-USB/801 T-USB above.png
