experientials/ziloo/Hardware/801-T-USB/801 T-USB below.png

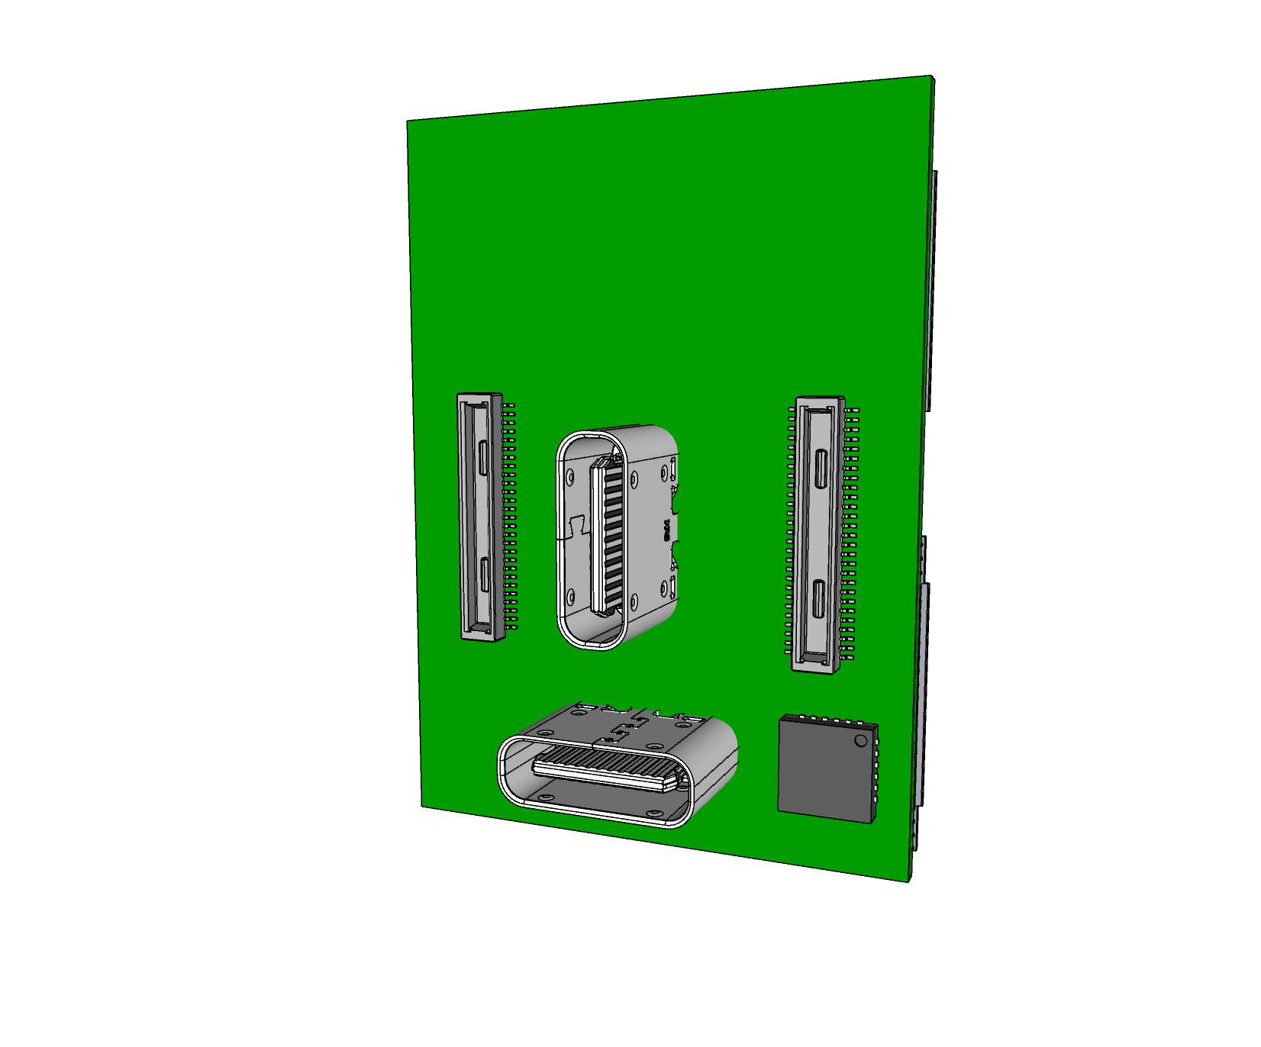
Hardware/801-T-USB/801 T-USB below.png
