experientials/ziloo/Hardware/801-T-USB/USB-2.0-extra-mux.png

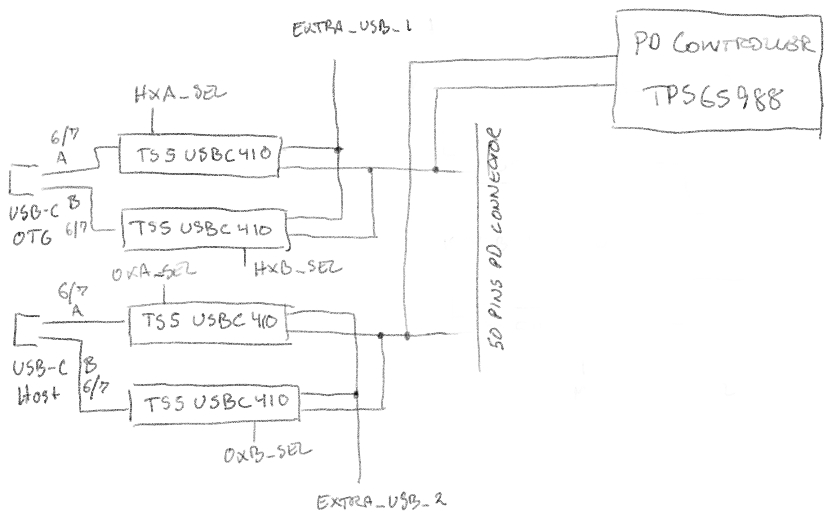
Hardware/801-T-USB/USB-2.0-extra-mux.png
