experientials/ziloo/Hardware/909b/T-USB Connections.jpg

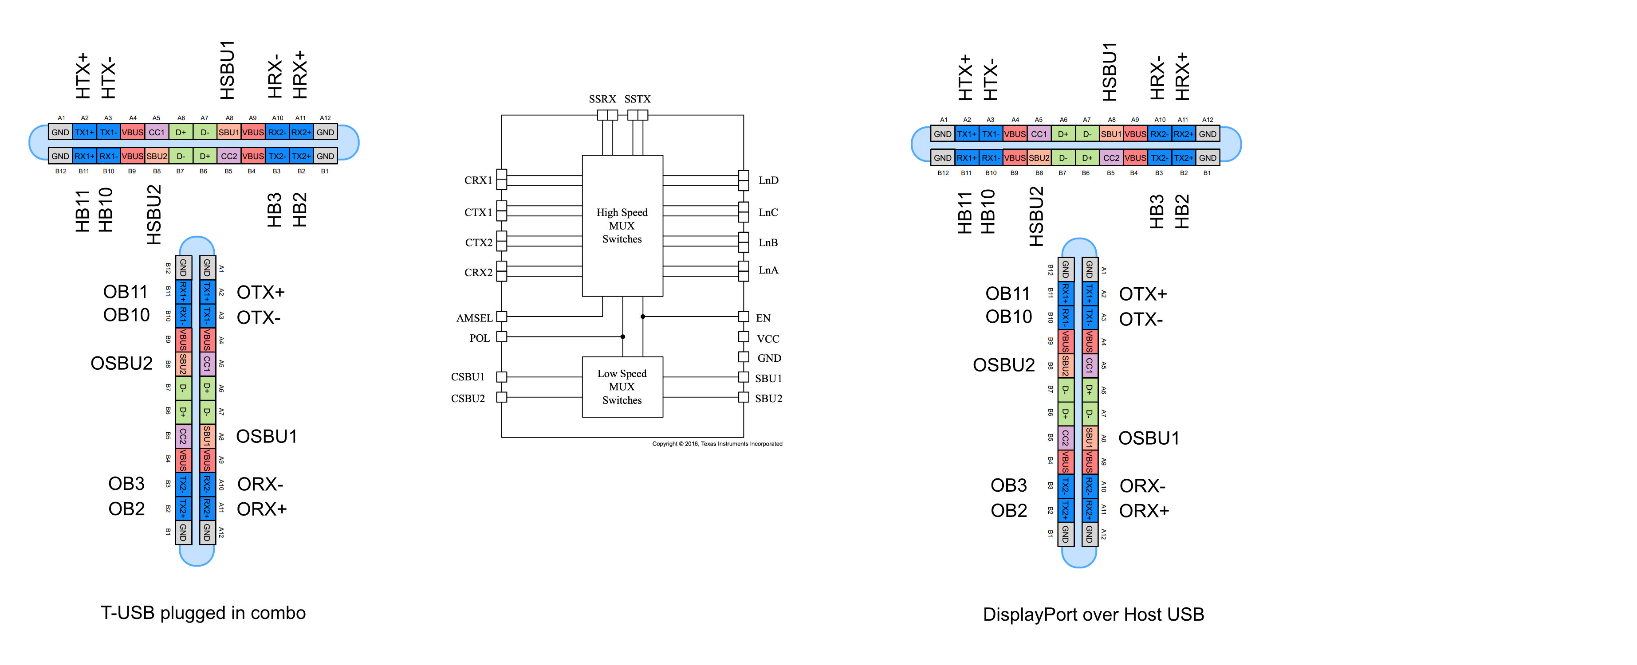
Hardware/909b/T-USB Connections.jpg
