experientials/ziloo/Hardware/909c/TBT-Notebook-ref.png

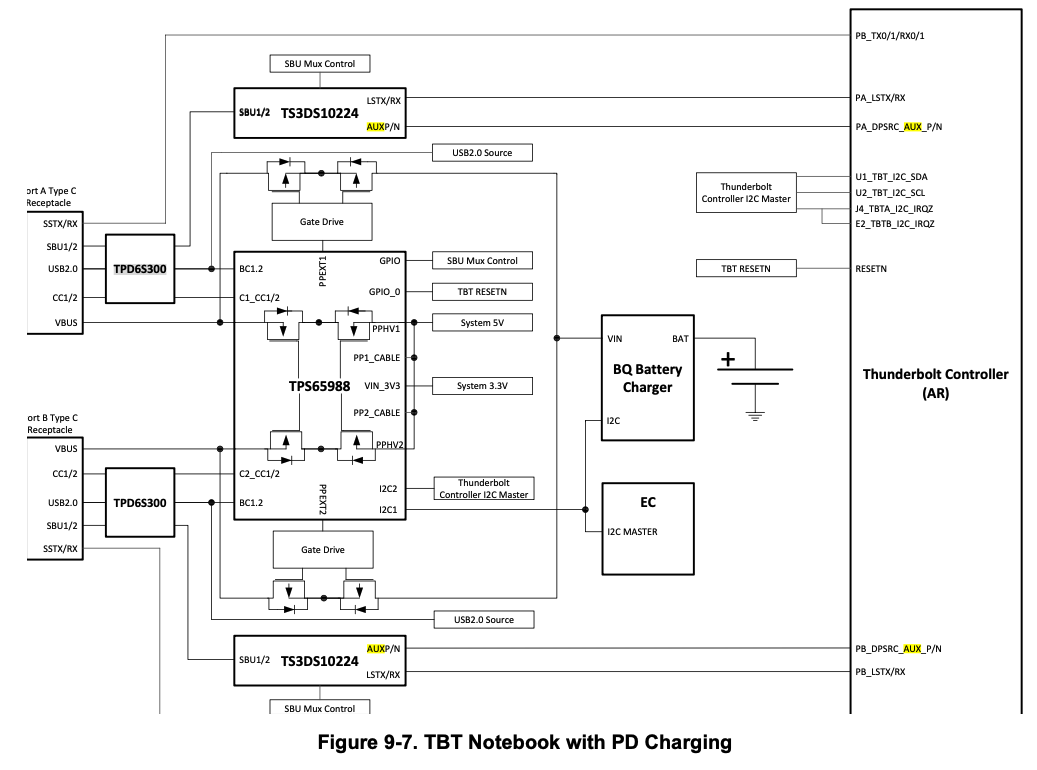
Hardware/909c/TBT-Notebook-ref.png
