experientials/ziloo/Hardware/919-smiley/decor/golden-front.jpg

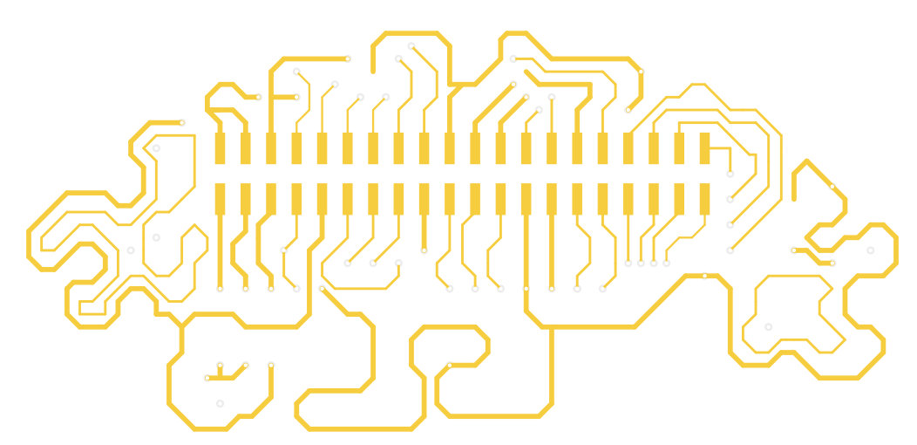
Hardware/919-smiley/decor/golden-front.jpg
