experientials/ziloo/Hardware/919-smiley/decor/golden-front.png

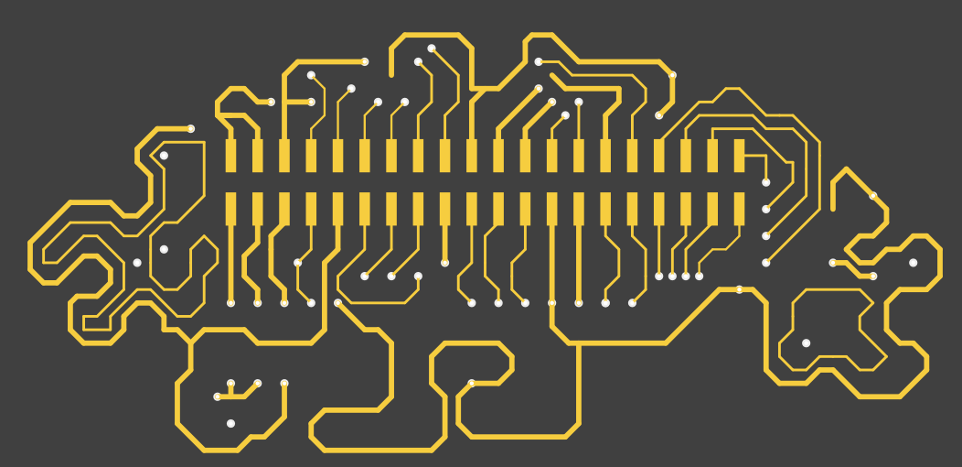
Hardware/919-smiley/decor/golden-front.png
