experientials/ziloo/Hardware/919-smiley/PCB screenshot.png

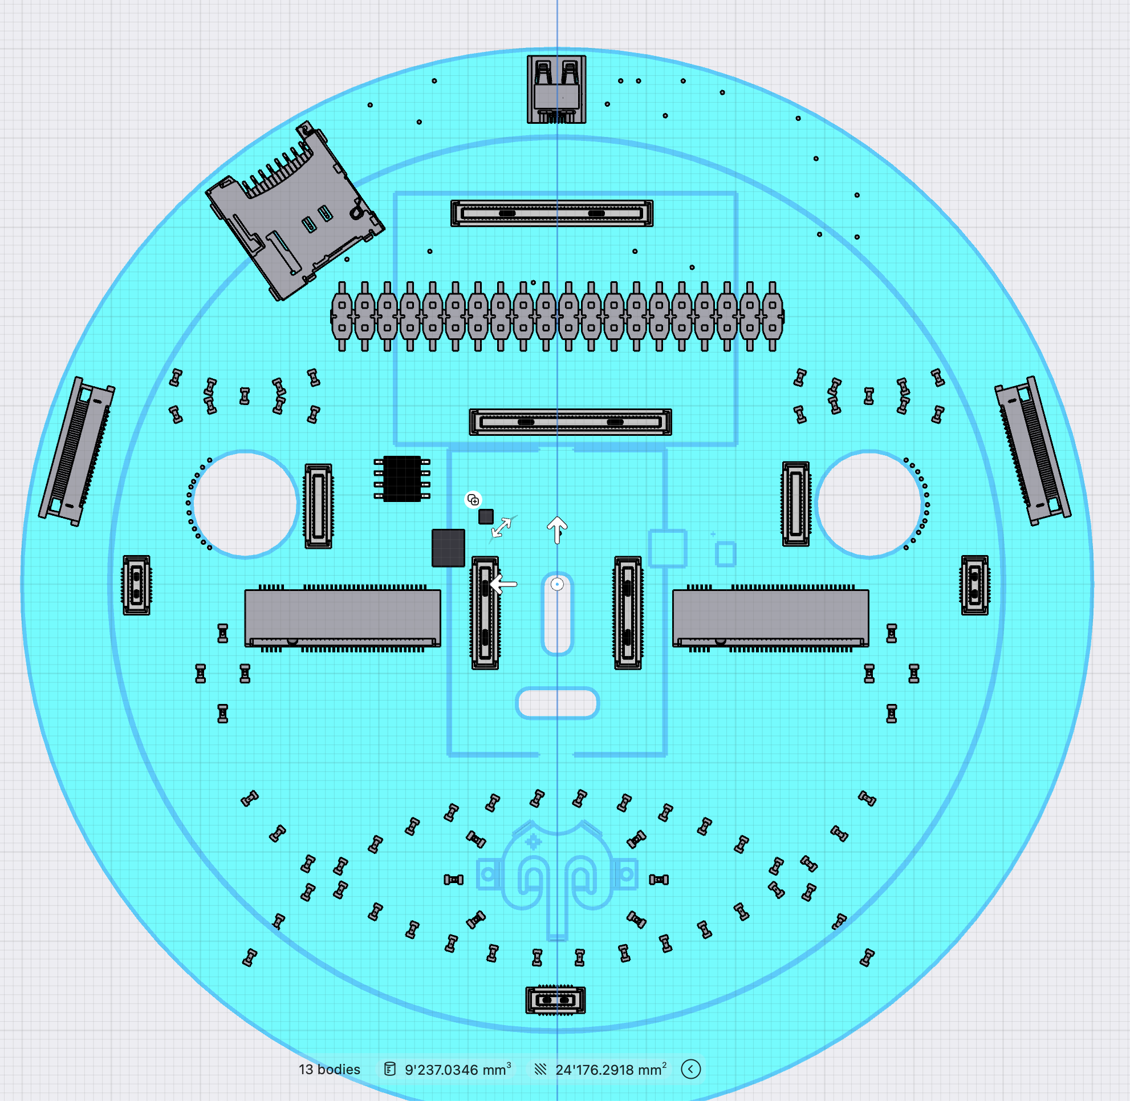
Hardware/919-smiley/PCB screenshot.png
