experientials/ziloo/Hardware/datasheets/lenses/210 FoV M12 TREEYE.jpg

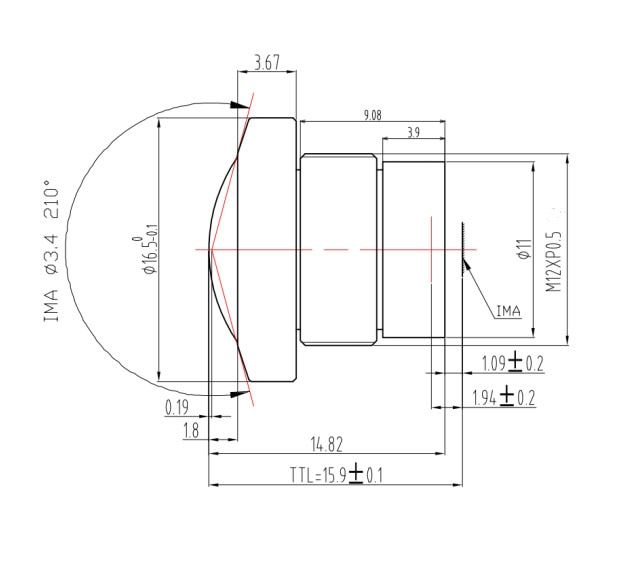
Hardware/datasheets/lenses/210 FoV M12 TREEYE.jpg
