experientials/ziloo/Hardware/datasheets/lenses/CA1300i-3.png

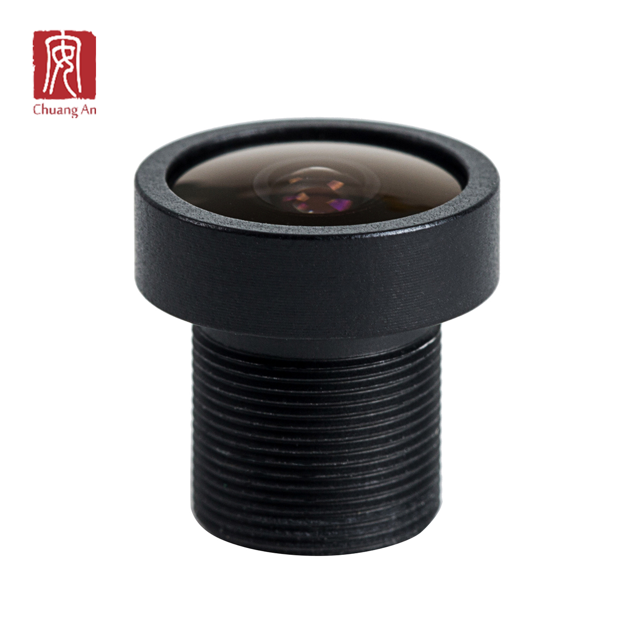
Hardware/datasheets/lenses/CA1300i-3.png
