experientials/ziloo/Hardware/datasheets/lenses/ChuangAn CA1300I 1633913527%281%29.png

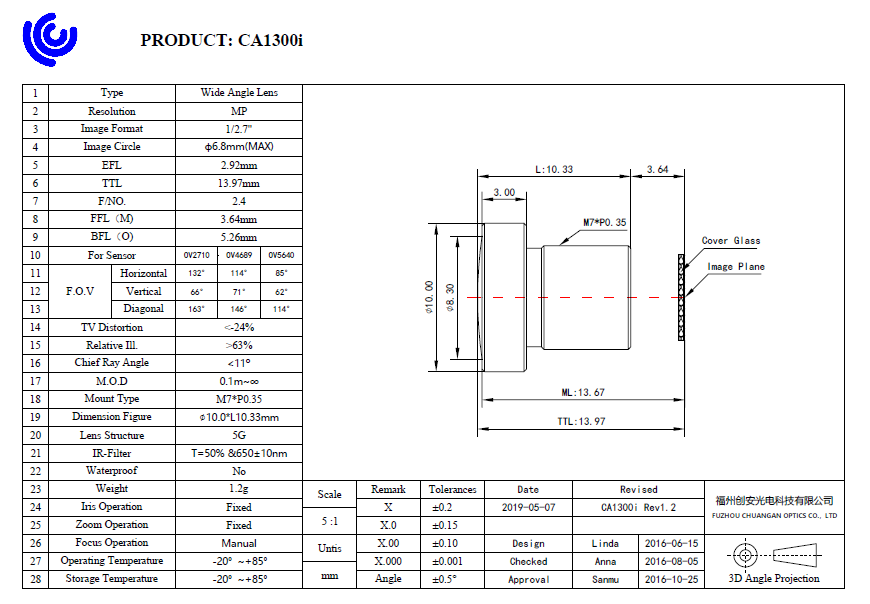
Hardware/datasheets/lenses/ChuangAn CA1300I 1633913527%281%29.png
