experientials/ziloo/Hardware/datasheets/lenses/HK-8244-1042-1-draw.png

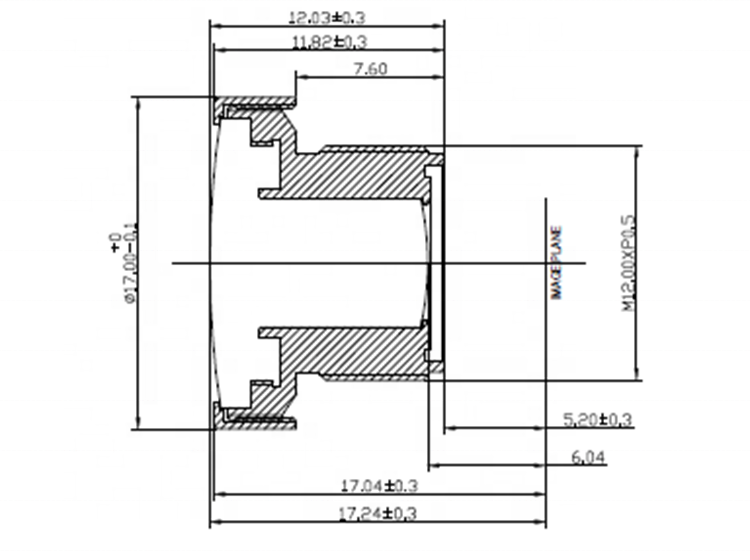
Hardware/datasheets/lenses/HK-8244-1042-1-draw.png
