experientials/ziloo/Hardware/datasheets/lenses/HK-8244-1042-1-pic.jpg

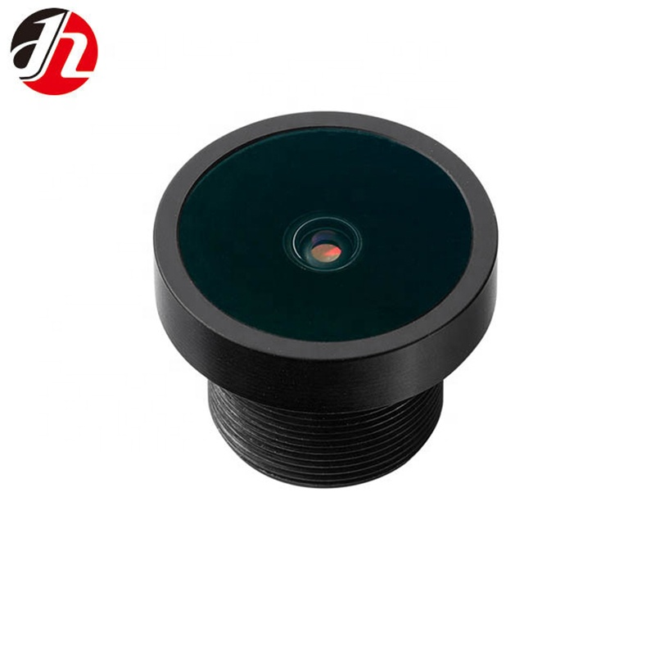
Hardware/datasheets/lenses/HK-8244-1042-1-pic.jpg
