experientials/ziloo/Hardware/datasheets/lenses/JSD2157 He9118f715eff4382ac724a5e50254d3ex.png

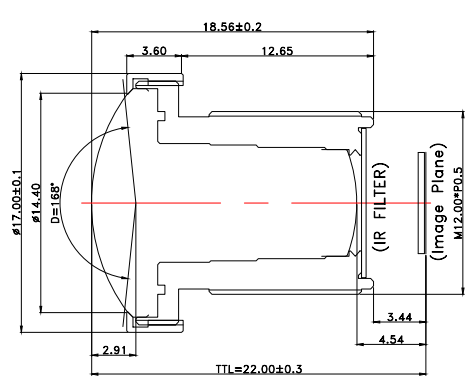
Hardware/datasheets/lenses/JSD2157 He9118f715eff4382ac724a5e50254d3ex.png
