experientials/ziloo/Hardware/datasheets/lenses/Towin pinhole CCL127028PMP-Pinhole-lens-2.8mm-12.7-IR-3MP-HD-CCTV-M12-mount-lens-for-Covert-hidden-Surveillance-1.jpg

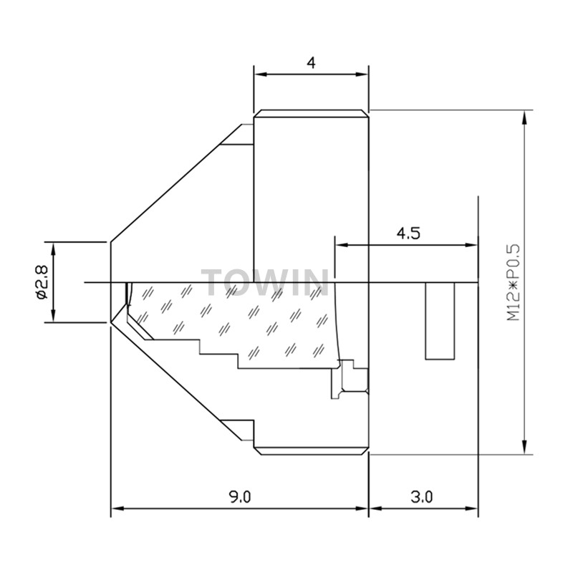
Hardware/datasheets/lenses/Towin pinhole CCL127028PMP-Pinhole-lens-2.8mm-12.7-IR-3MP-HD-CCTV-M12-mount-lens-for-Covert-hidden-Surveillance-1.jpg
