experientials/ziloo/Hardware/datasheets/Power/ref-TPS65988-power-input.png

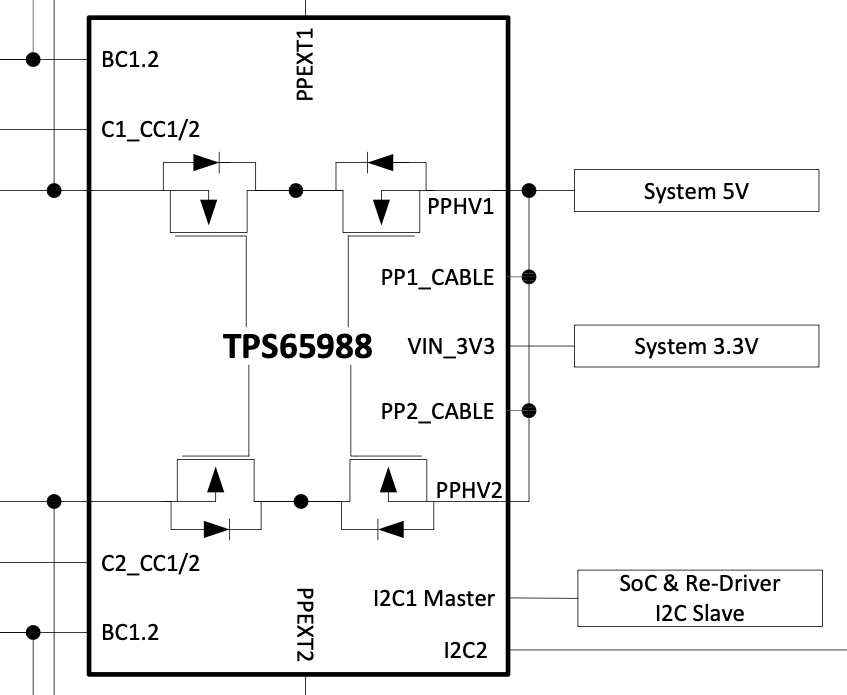
Hardware/datasheets/Power/ref-TPS65988-power-input.png
