experientials/ziloo/Hardware/Power/Power_module_PCB_files/03_GERBER FILES/PCB stackup.png

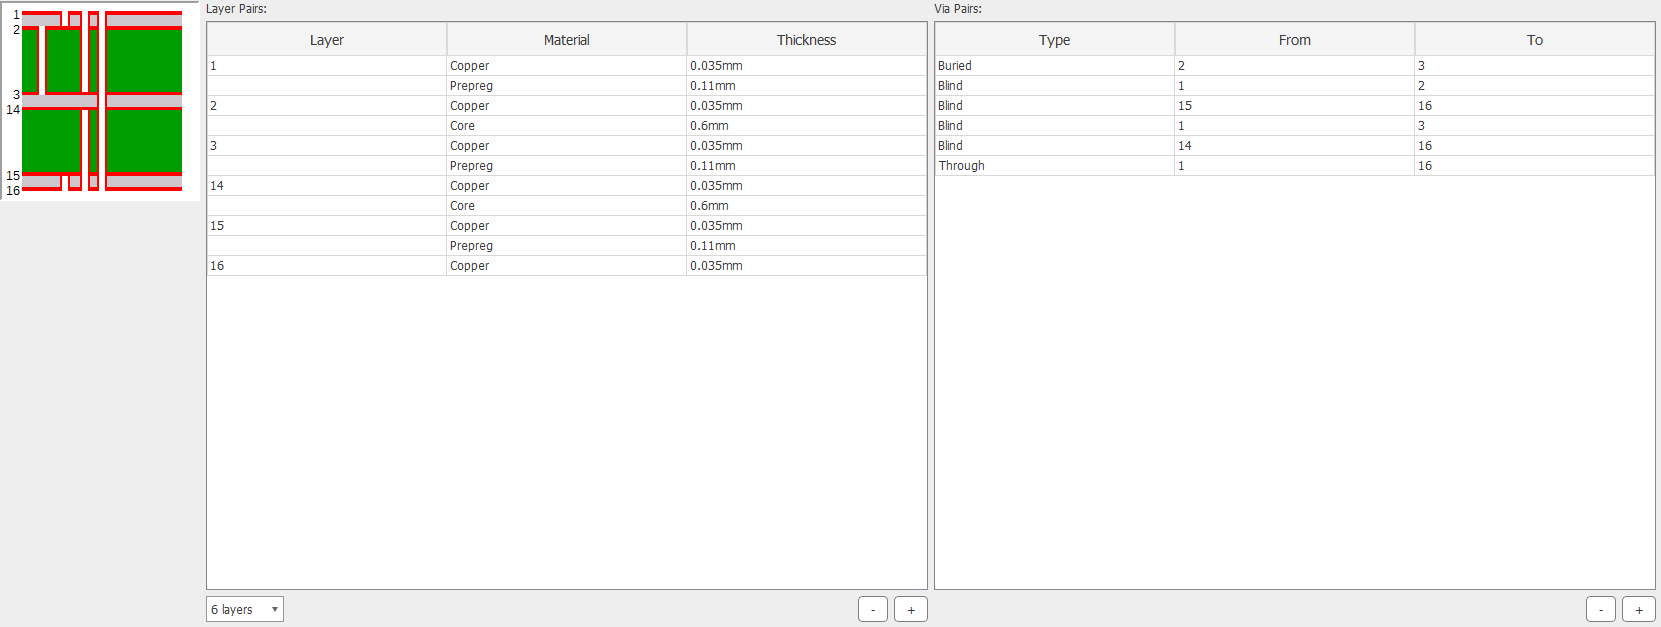
Hardware/Power/Power_module_PCB_files/03_GERBER FILES/PCB stackup.png
