experientials/ziloo/Hardware/Power/Power_module_PCB_files/03_GERBER FILES/USB_charge_PCB_V1_b.png

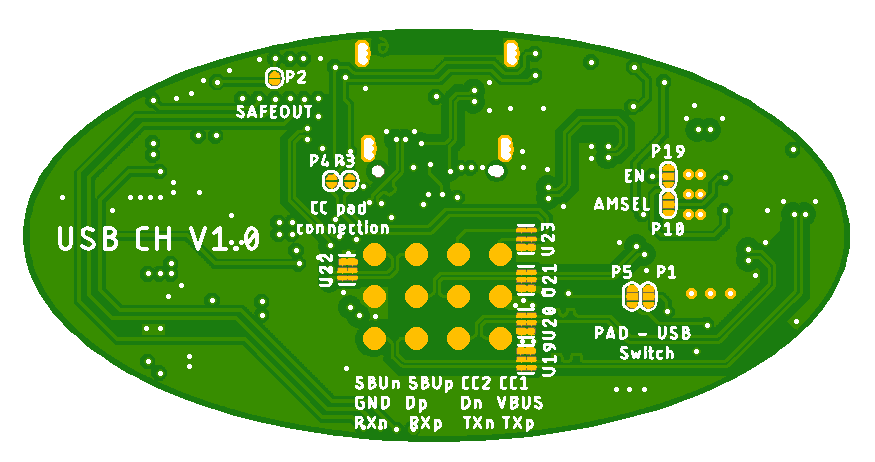
Hardware/Power/Power_module_PCB_files/03_GERBER FILES/USB_charge_PCB_V1_b.png
