experientials/ziloo/Hardware/Power/v1/20210705_094228.jpg

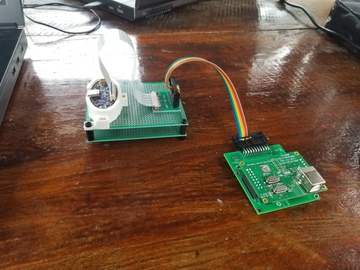
Hardware/Power/v1/20210705_094228.jpg
