experientials/ziloo/Hardware/Power/v1/20210705_094238.jpg

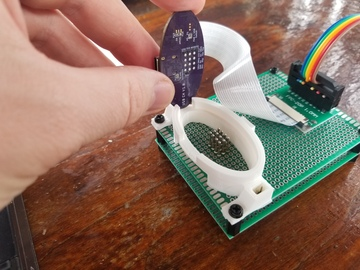
Hardware/Power/v1/20210705_094238.jpg
