experientials/ziloo/Hardware/Power/v1/20210705_095612.jpg

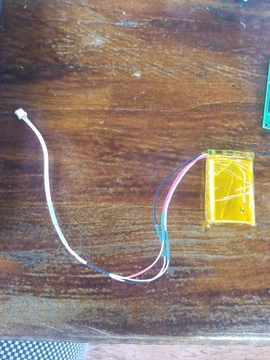
Hardware/Power/v1/20210705_095612.jpg
