experientials/ziloo/Hardware/Power/v1/First_screen.jpg

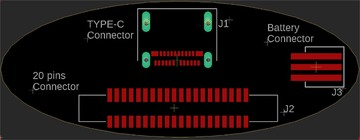
Hardware/Power/v1/First_screen.jpg
