experientials/ziloo/Hardware/Power/v1/Pasted File at February 4, 2021 9_57 AM.png

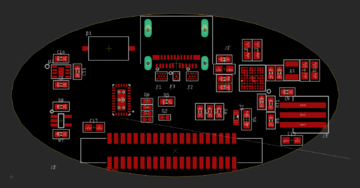
Hardware/Power/v1/Pasted File at February 4, 2021 9_57 AM.png
