experientials/ziloo/Hardware/Power/v1/Screenshot_1.png

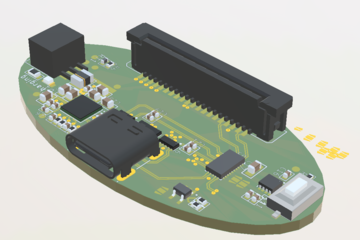
Hardware/Power/v1/Screenshot_1.png
