experientials/ziloo/Hardware/Power/v1/Screenshot_2.png

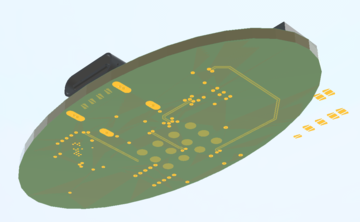
Hardware/Power/v1/Screenshot_2.png
