experientials/ziloo/Hardware/Power/v1/Screenshot_3.png

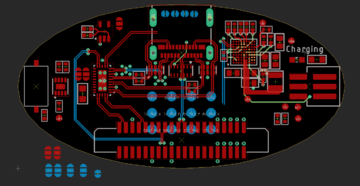
Hardware/Power/v1/Screenshot_3.png
