experientials/ziloo/Hardware/Power/v1/Screenshot_4.png

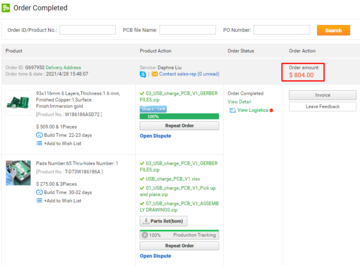
Hardware/Power/v1/Screenshot_4.png
