experientials/ziloo/Hardware/Power/v1/Second_screen.jpg

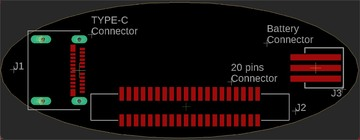
Hardware/Power/v1/Second_screen.jpg
