experientials/ziloo/Hardware/refs/Camera-Sensor-Size-Full-Frame-APSC-Four-Thirds-Camera-Sensor-Sizes-Graphic.jpg.webp

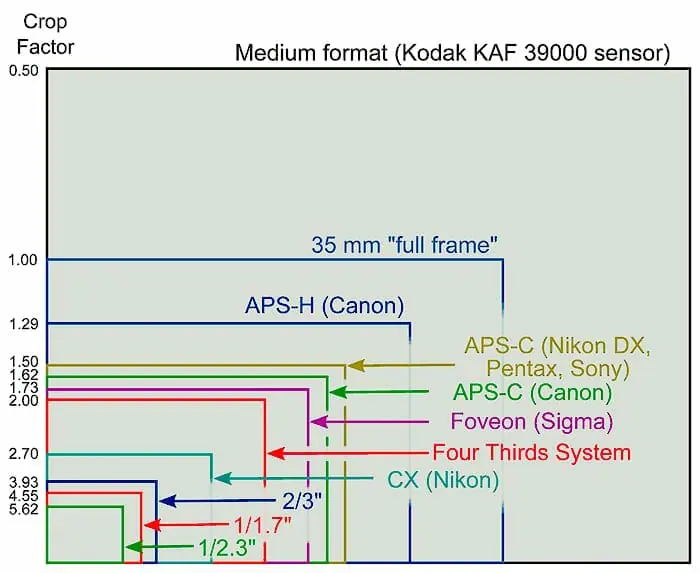
Hardware/refs/Camera-Sensor-Size-Full-Frame-APSC-Four-Thirds-Camera-Sensor-Sizes-Graphic.jpg.webp
