experientials/ziloo/Hardware/refs/POWER-MODULE-conceptual-wring.jpg

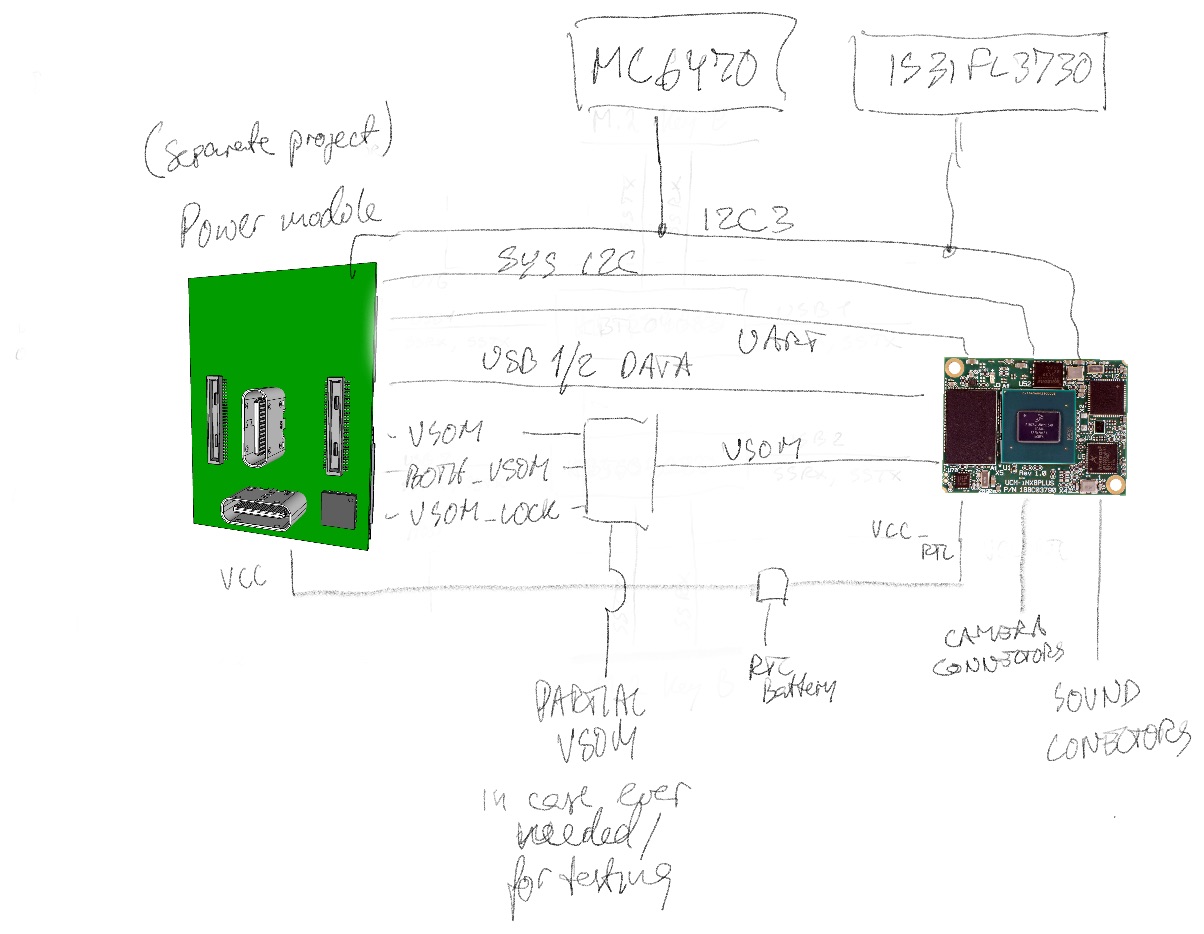
Hardware/refs/POWER-MODULE-conceptual-wring.jpg
