experientials/ziloo/Hardware/refs/Suggested diagram for Camera Module.png

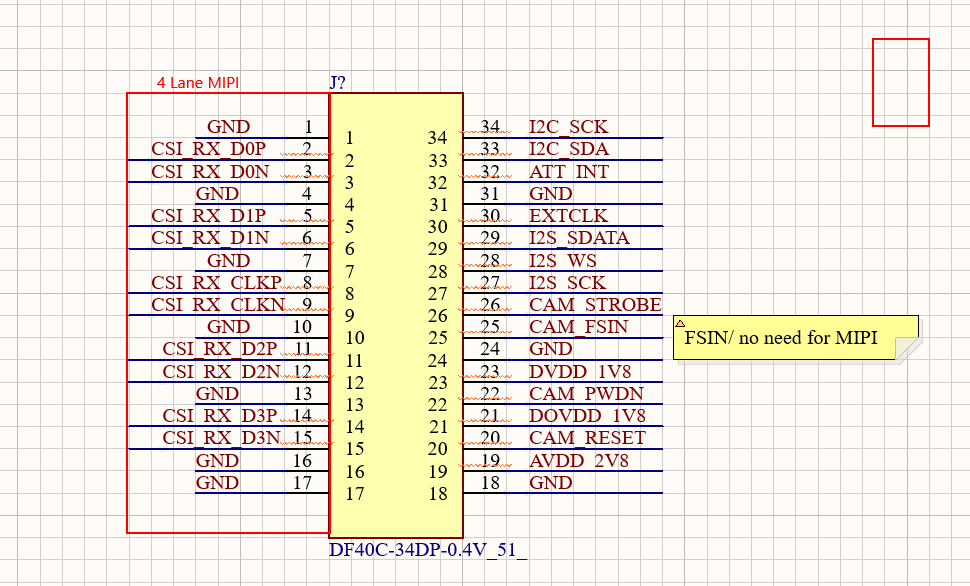
Hardware/refs/Suggested diagram for Camera Module.png
