experientials/ziloo/Hardware/801-T-USB/BRIDGE_BOARD_909b_ref_wiring.pdf

# Power Supply1

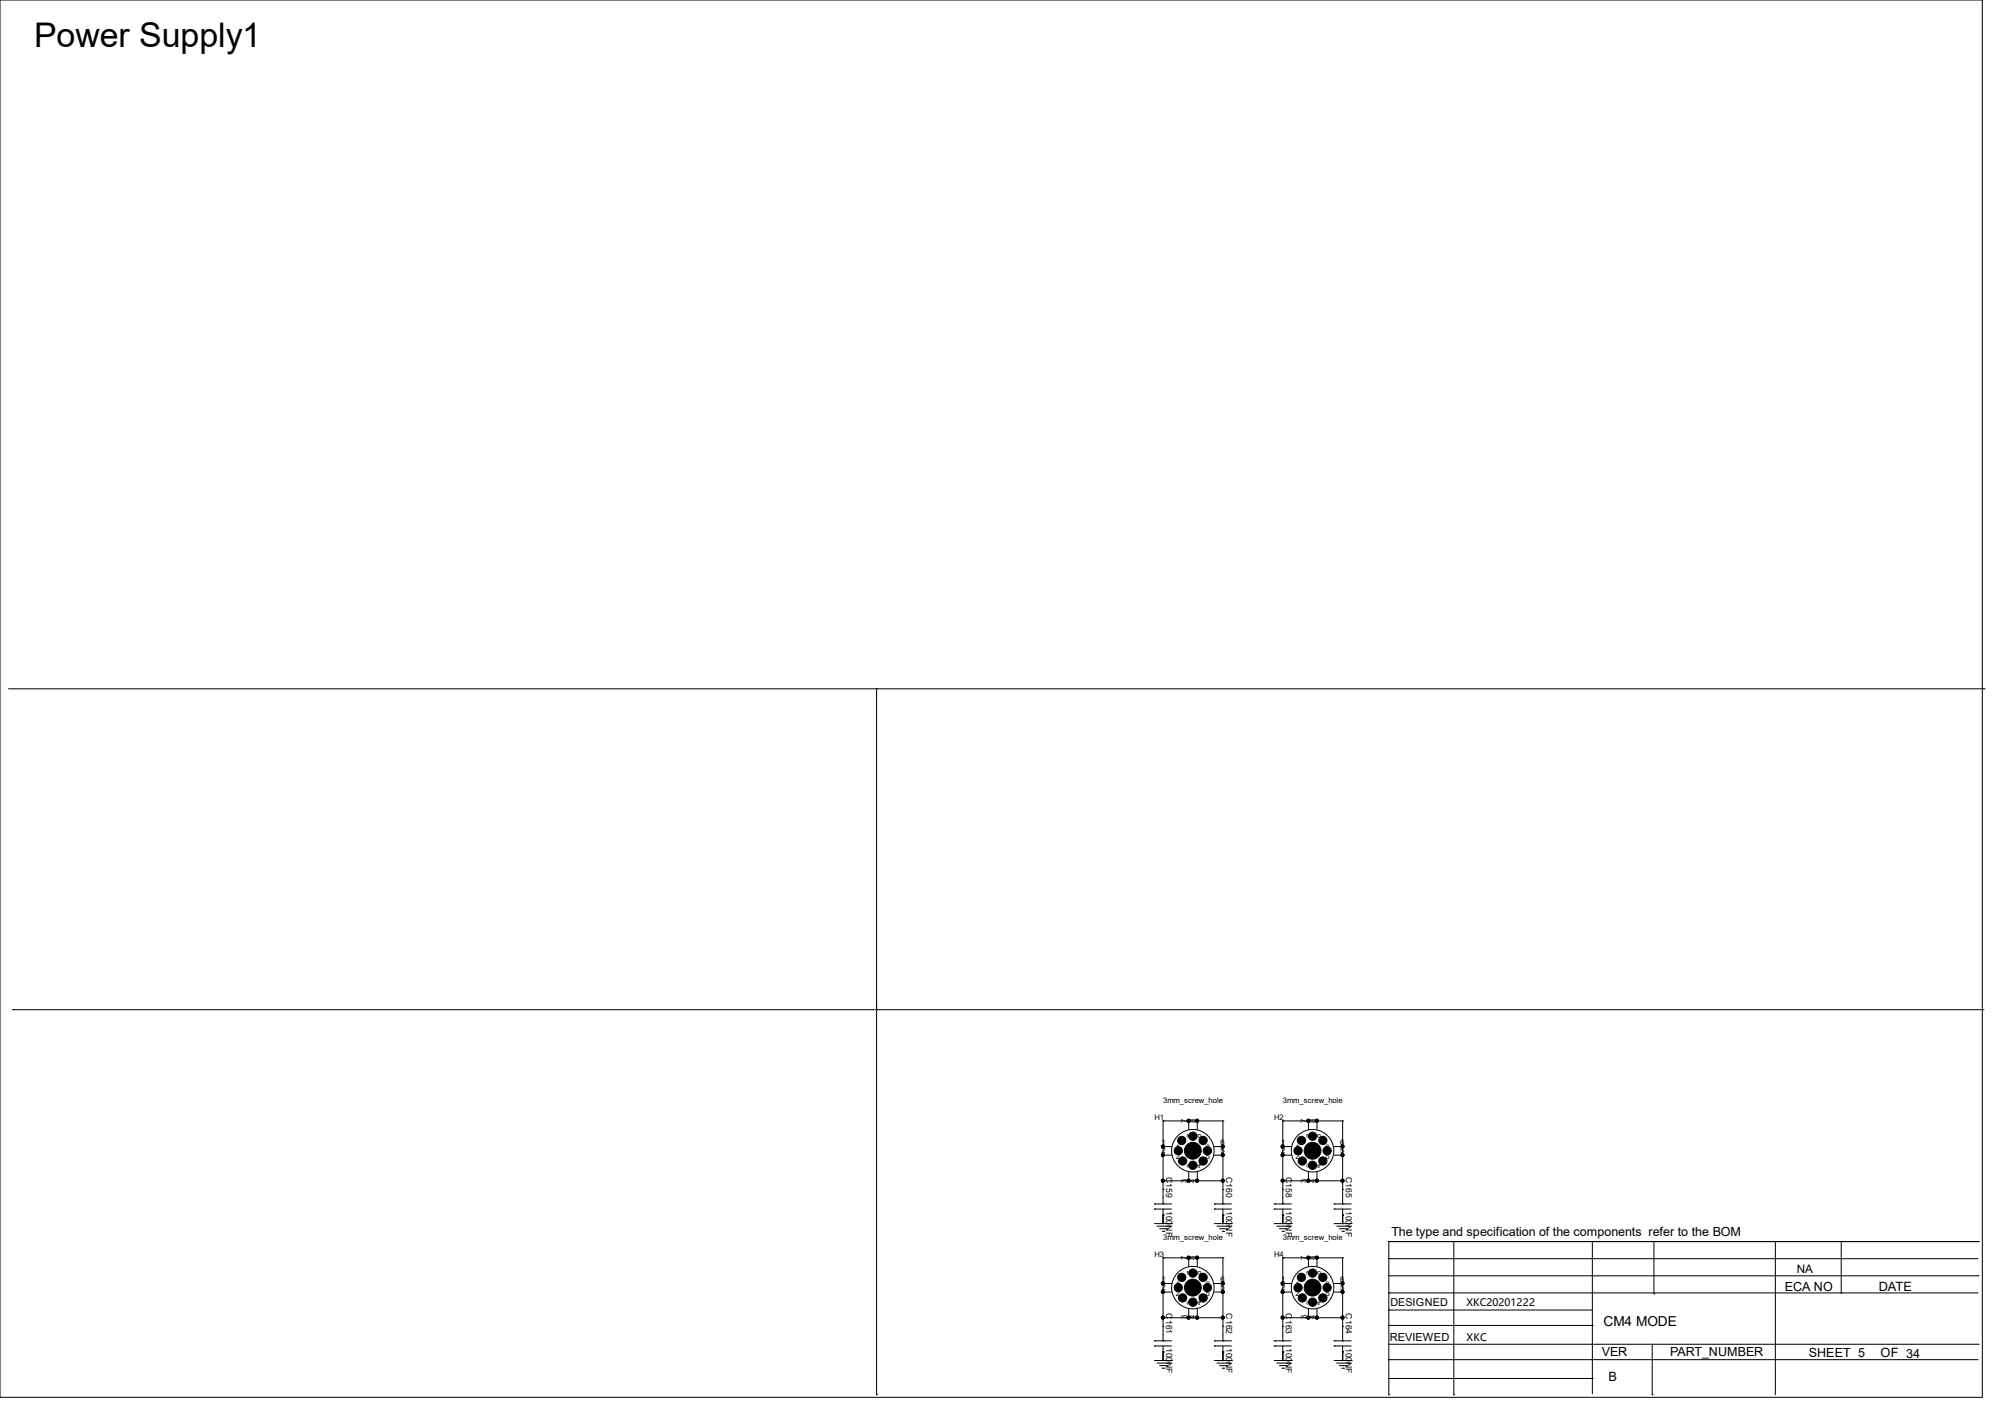
[picture p140: page 1]

The type and specification of the components refer to the BOM

NA
ECA NO | DATE

DESIGNED | XKC20201222 | CM4 MODE

REVIEWED | XKC

VER | PART_NUMBER | SHEET 5 OF 34

# Power Supply2

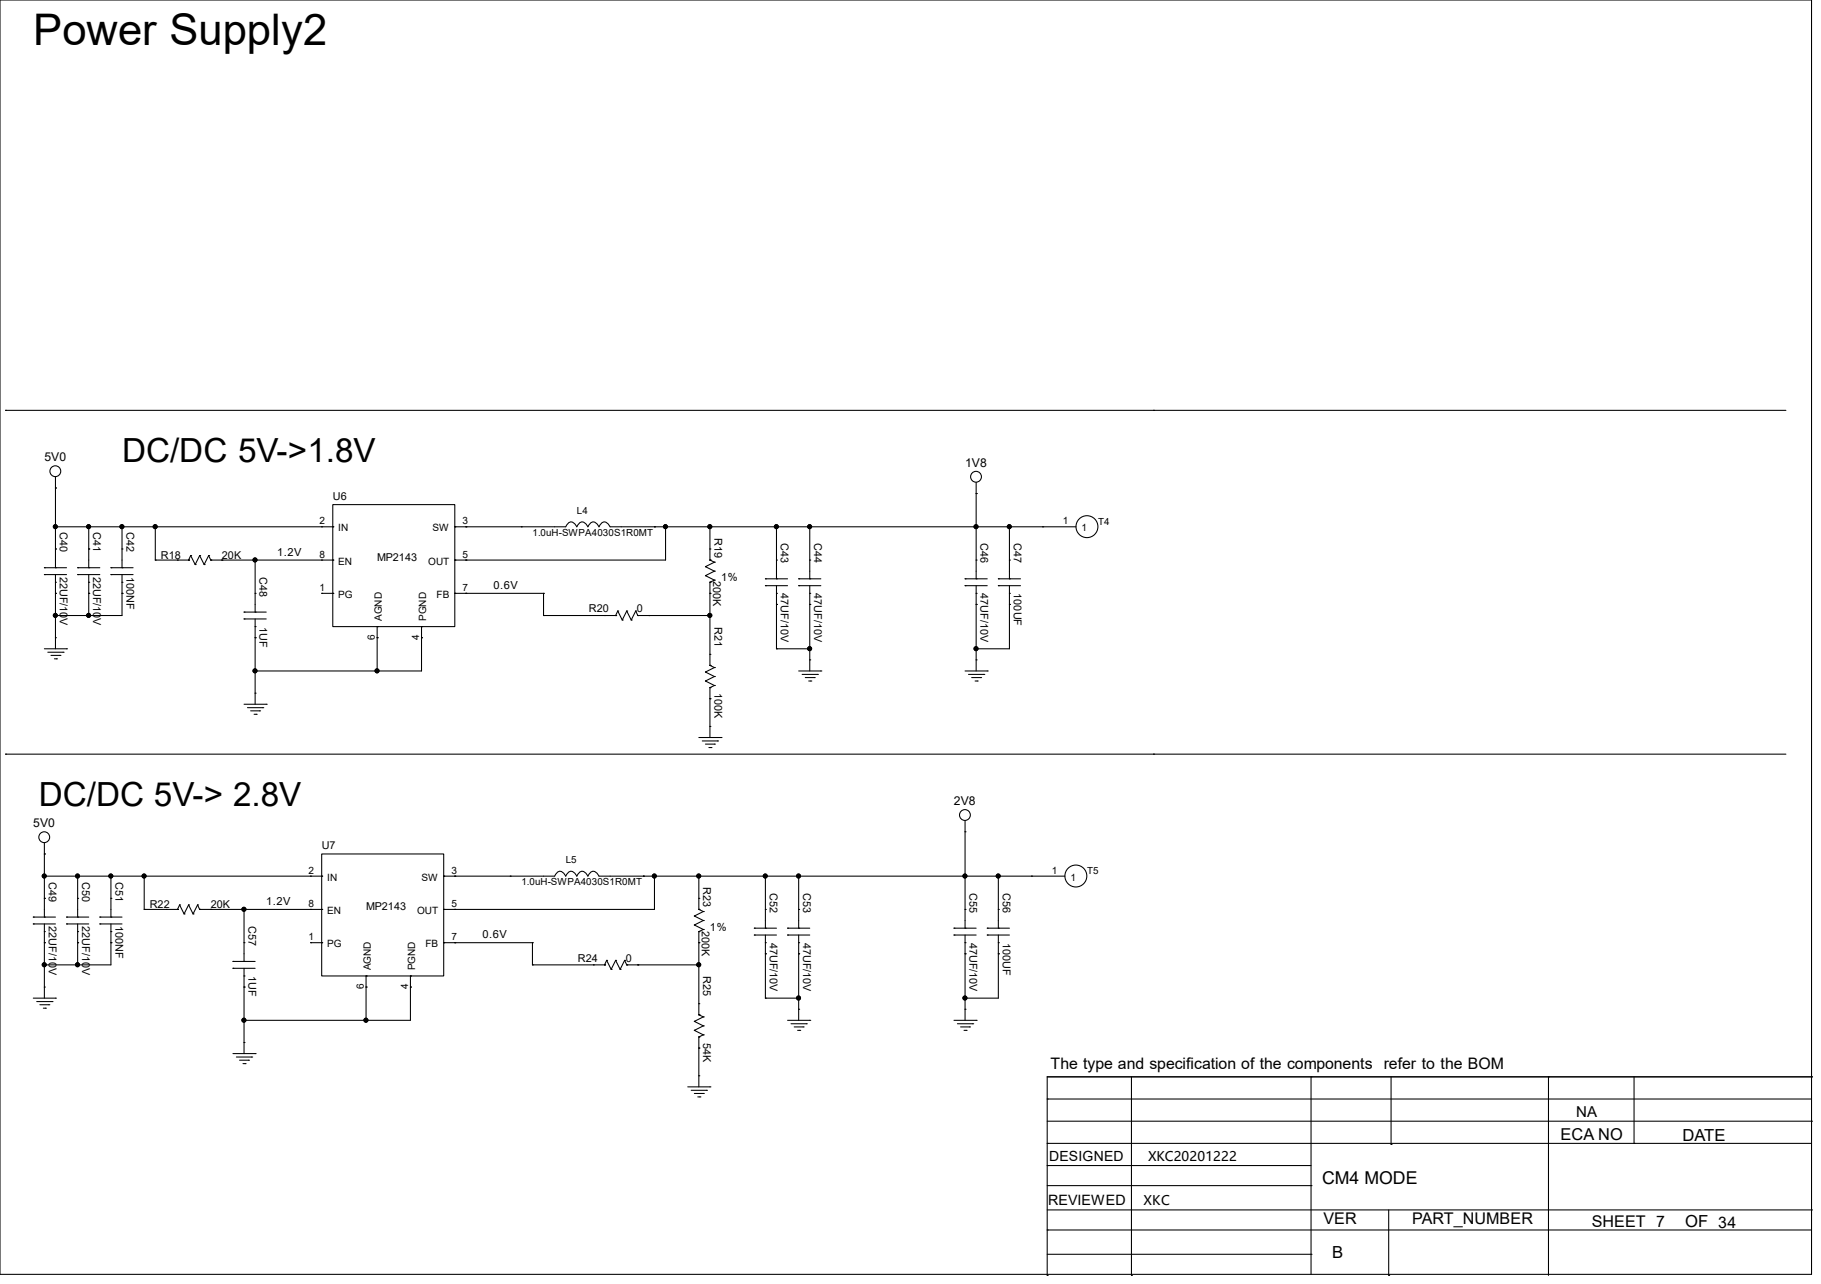
[picture p141: page 2]

The type and specification of the components refer to the BOM

NA
ECA NO | DATE

DESIGNED | XKC20201222 | CM4 MODE

XKC

VER | PART_NUMBER | SHEET 7 34

# PP_HV1

# PP_HV2

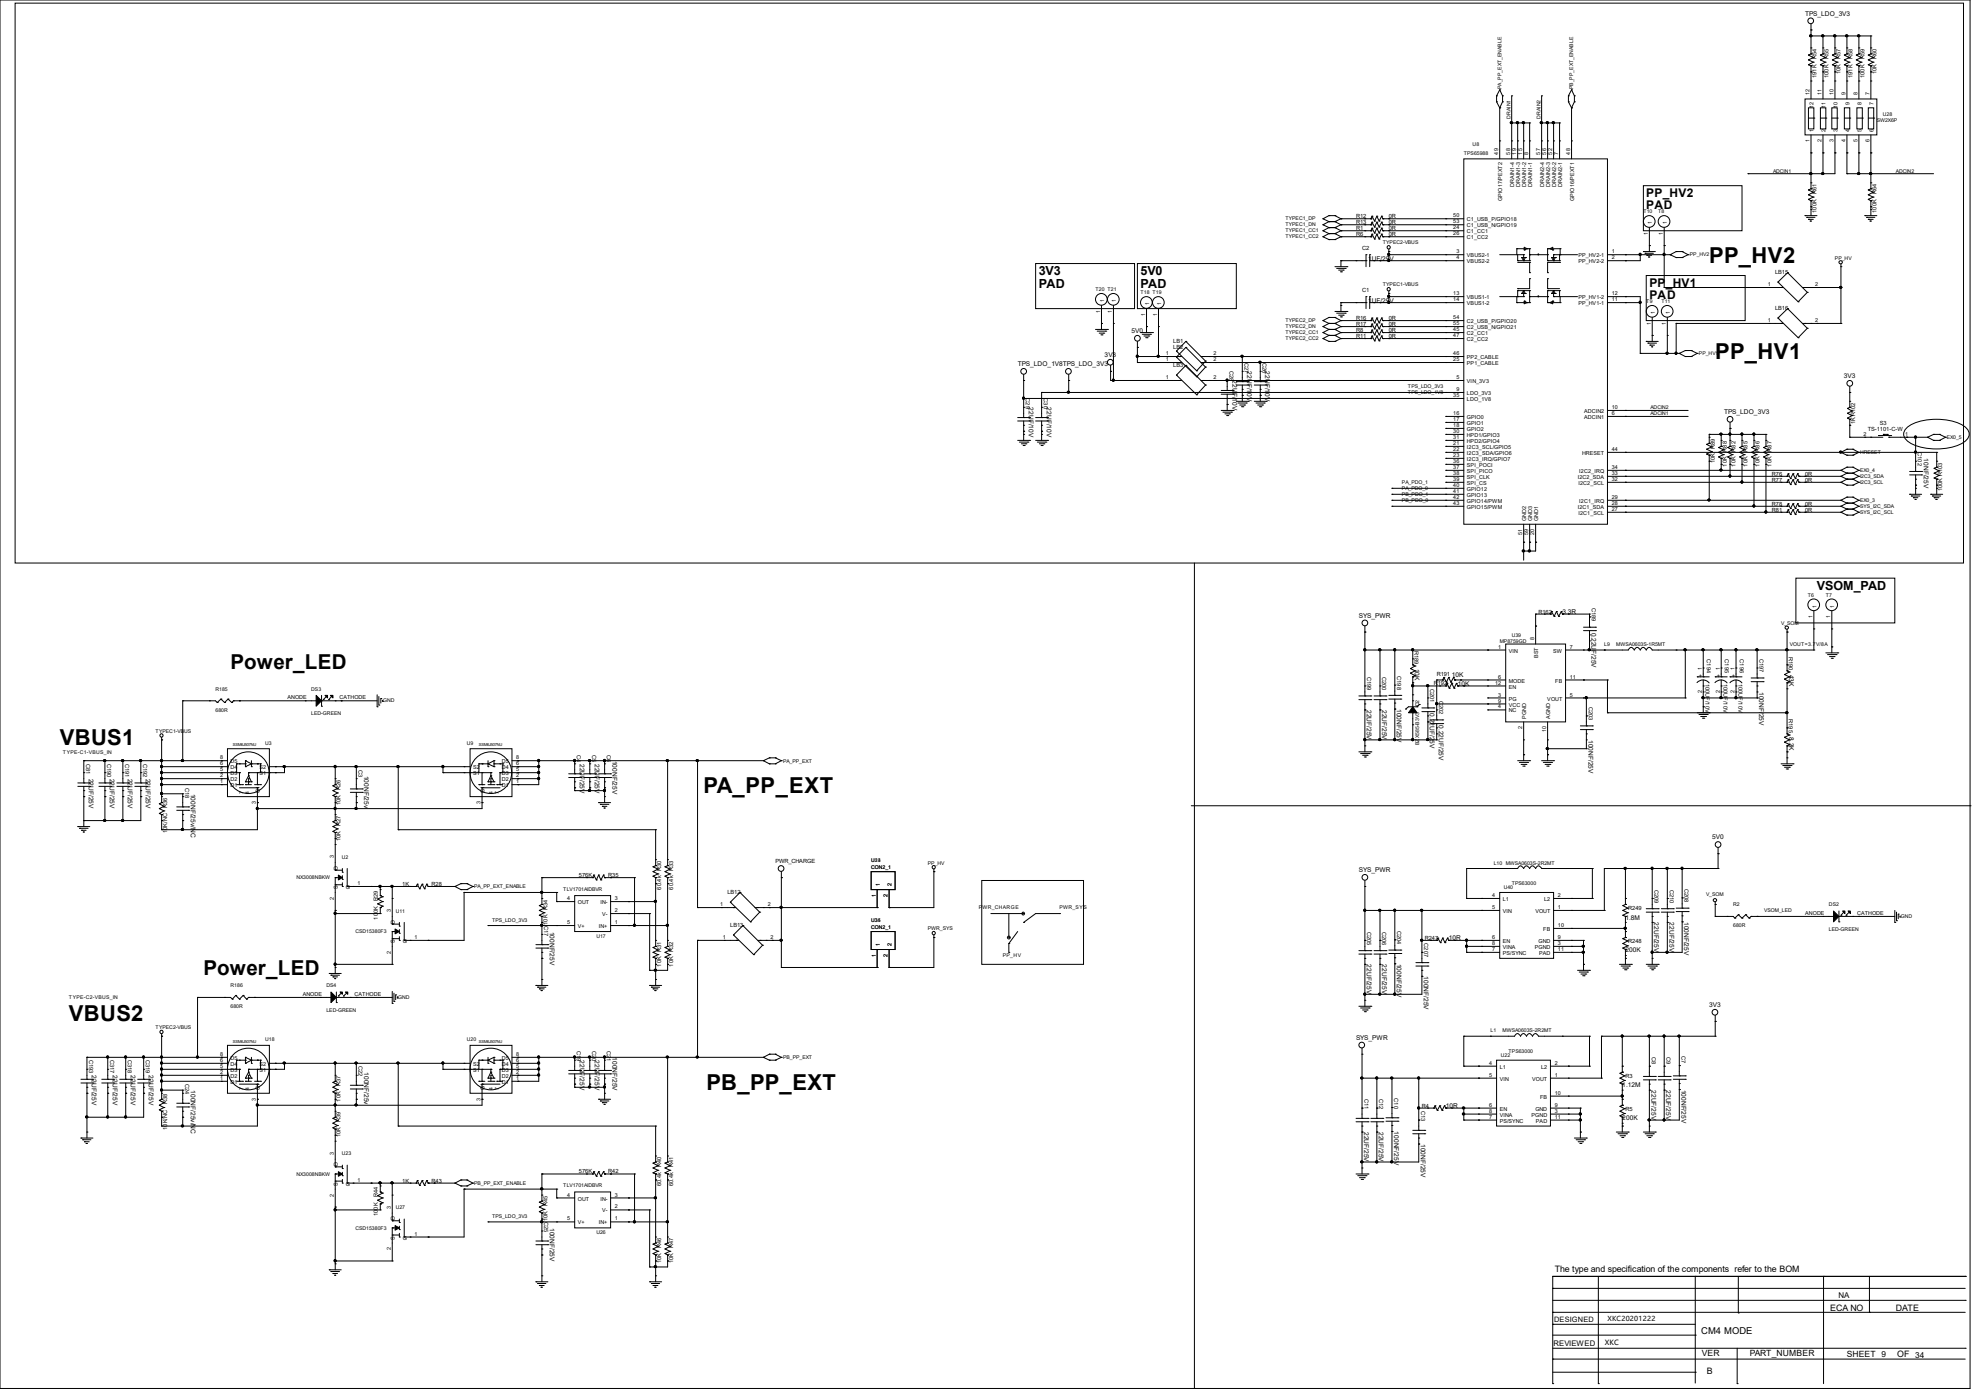
[picture p142: page 3]

The type and specification of the components refer to the BOM

NA
ECA NO | DATE

# CBTL04083 HD3SS460

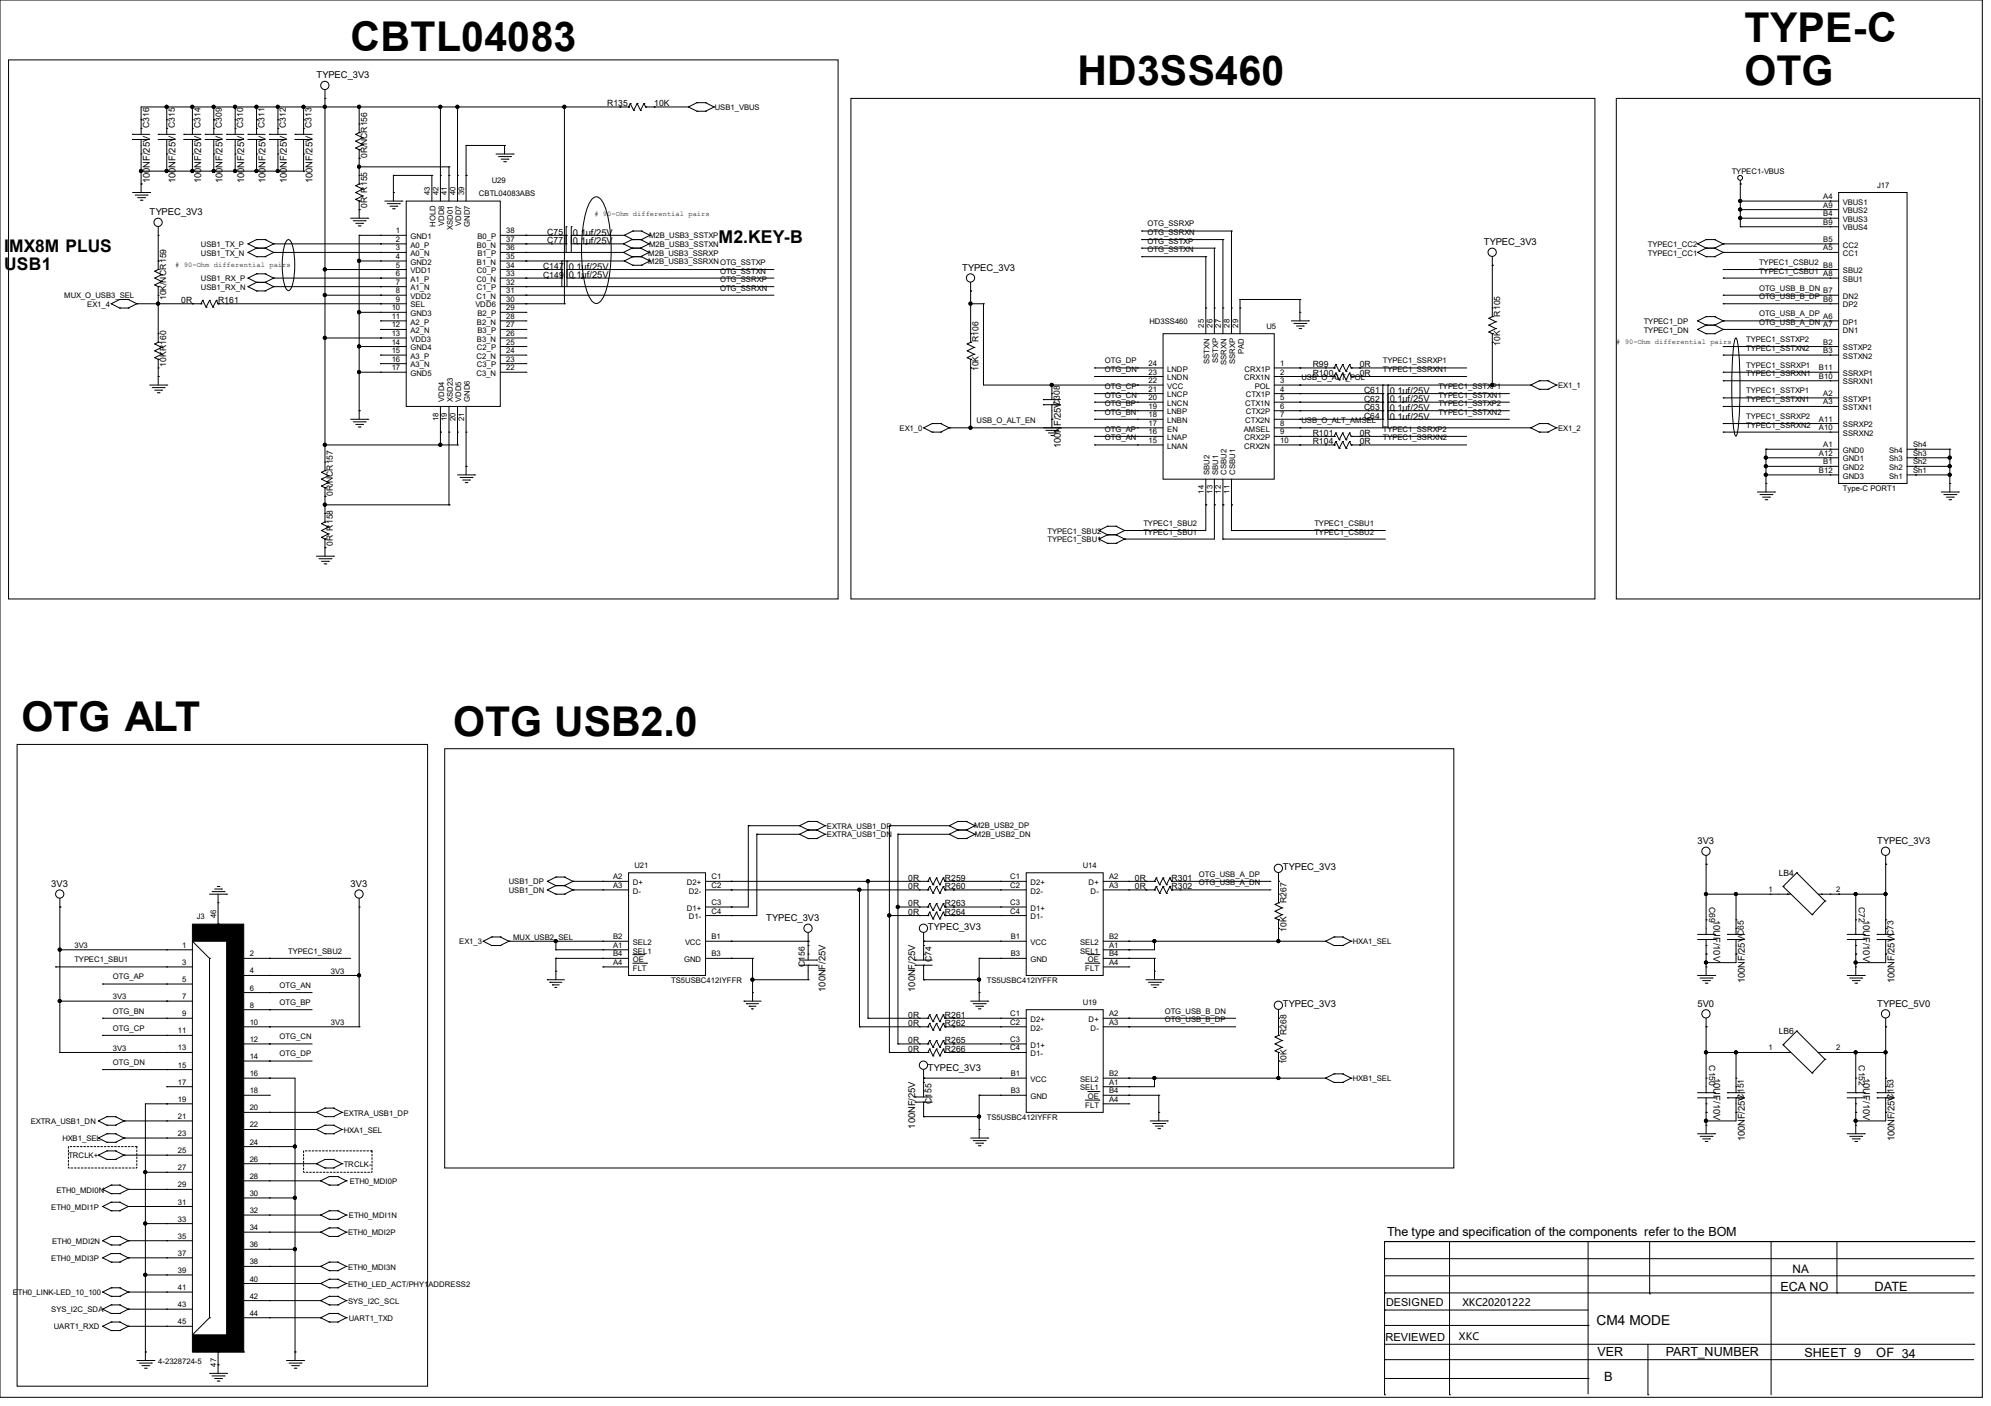
[picture p143: page 4]

TYPEC_3V3
22 GND⁷ ³⁹ VDD⁷ ⁴⁰ XSD⁰¹ ⁴¹ VDD⁸ ⁴² HOLD ⁴³

24 SSTXN ²⁵ SSTXP ²⁶ SSRXN ²⁷ SSRXP ²⁸ PAD ²⁹

10 CSBU¹ 11 CSBU² 12 SBU¹ 13 SBU² 14

The type and specification of the components refer to the BOM

# HD3SS460

# TYPE-C

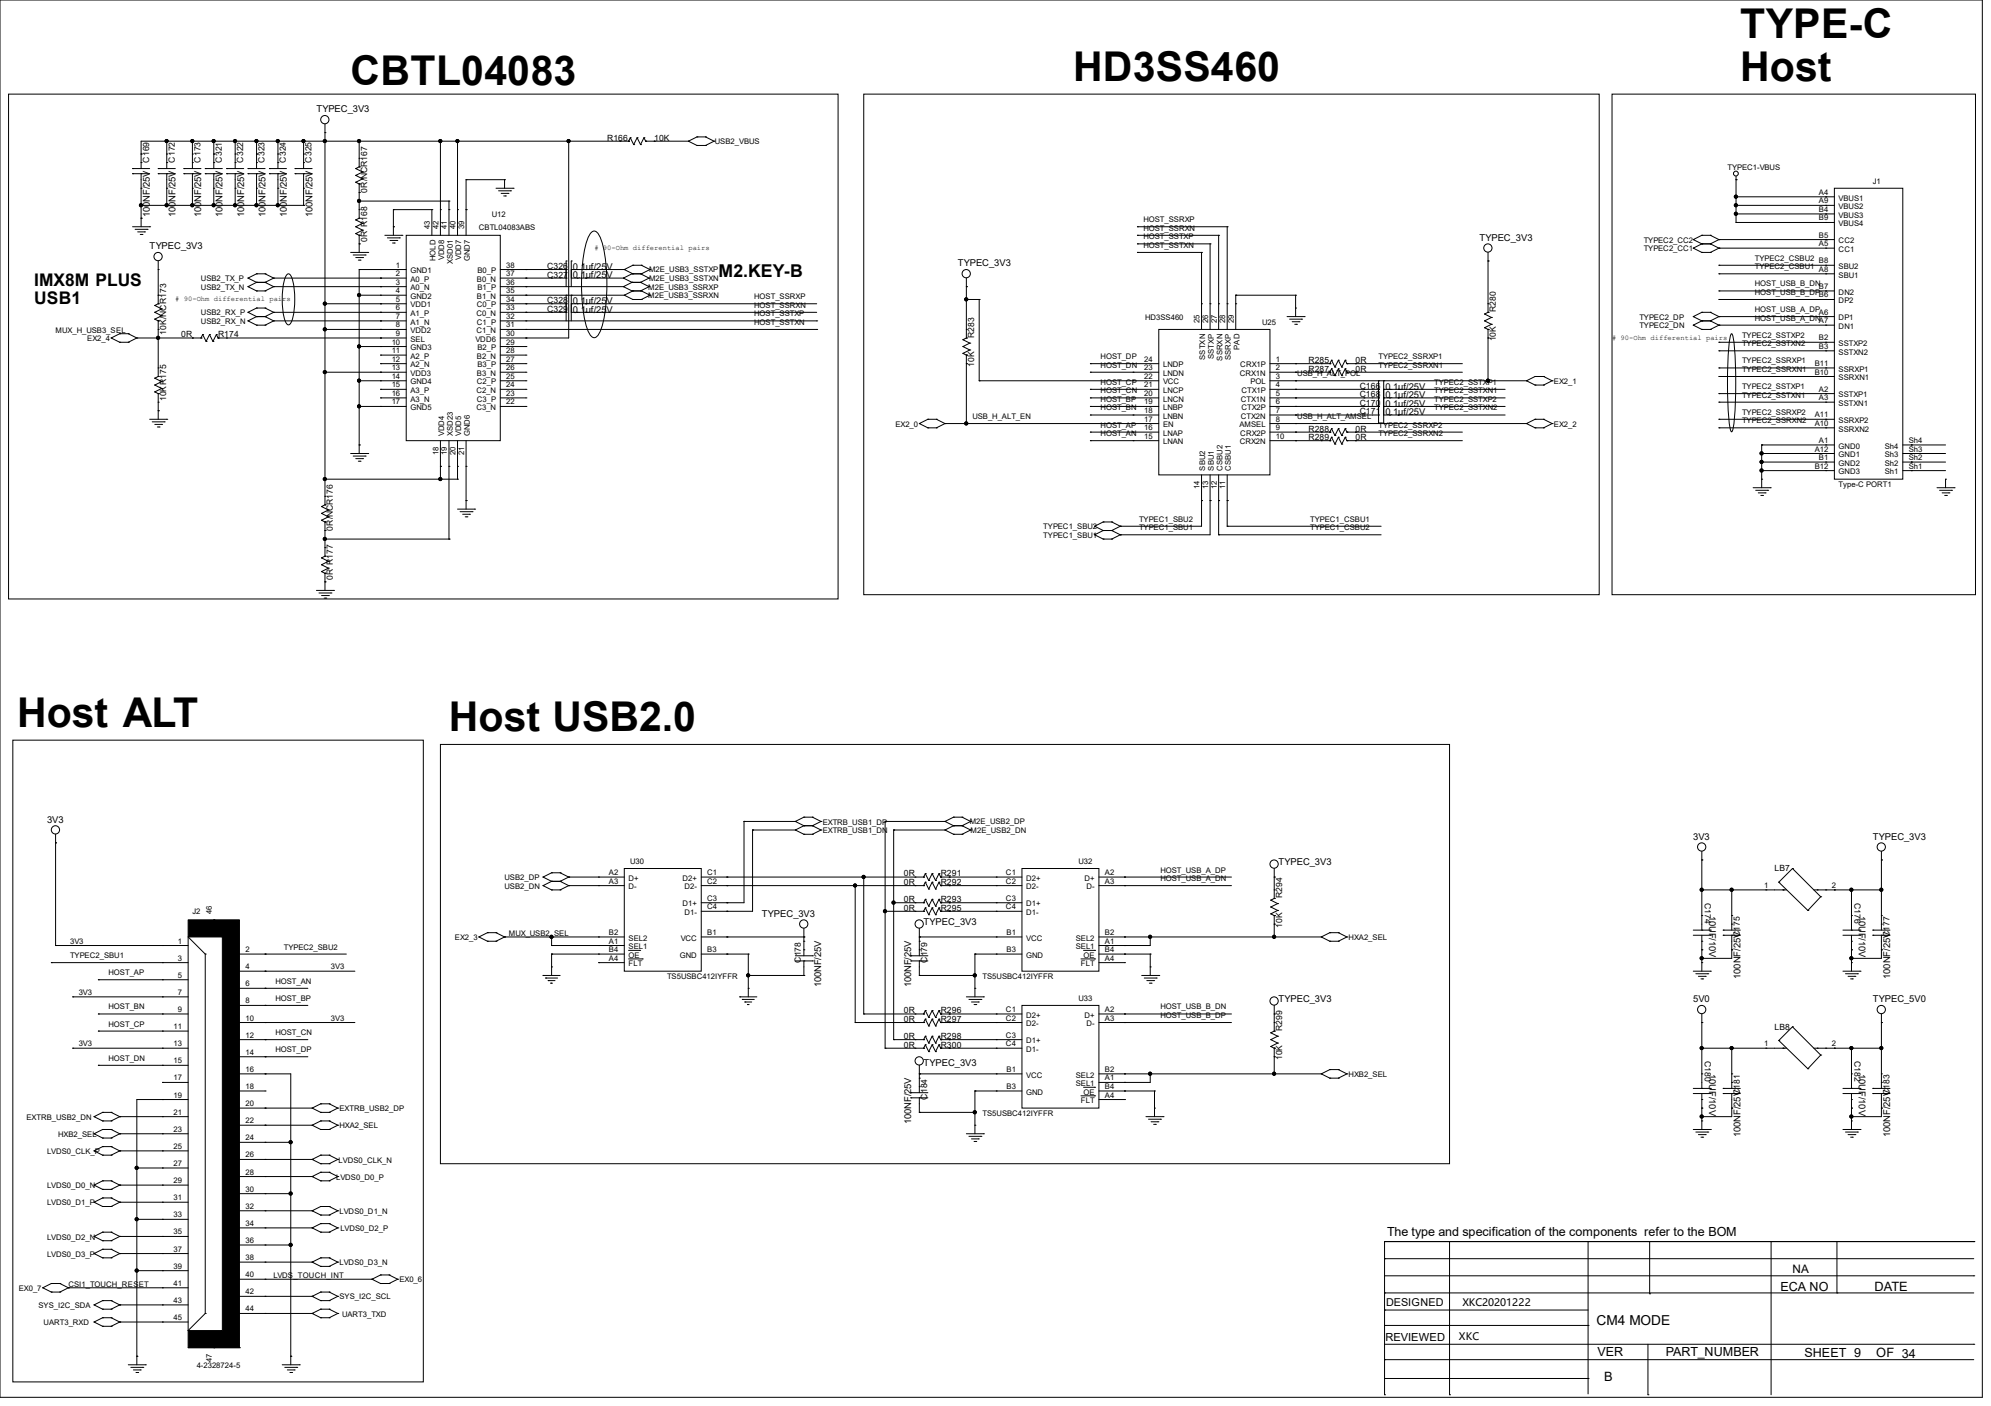
[picture p144: page 5]

22 GND⁷ ³⁹ VDD⁷ ⁴⁰ XSD⁰¹ ⁴¹ VDD⁸ ⁴² HOLD ⁴³ 10KR¹⁷⁵
TYPEC_3V3

10 CSBU¹ 11 CSBU² 12 SBU¹ 13 SBU² 14

The type and specification of the components refer to the BOM

# V-SOM decoupling capacitors

## USB1_OTG

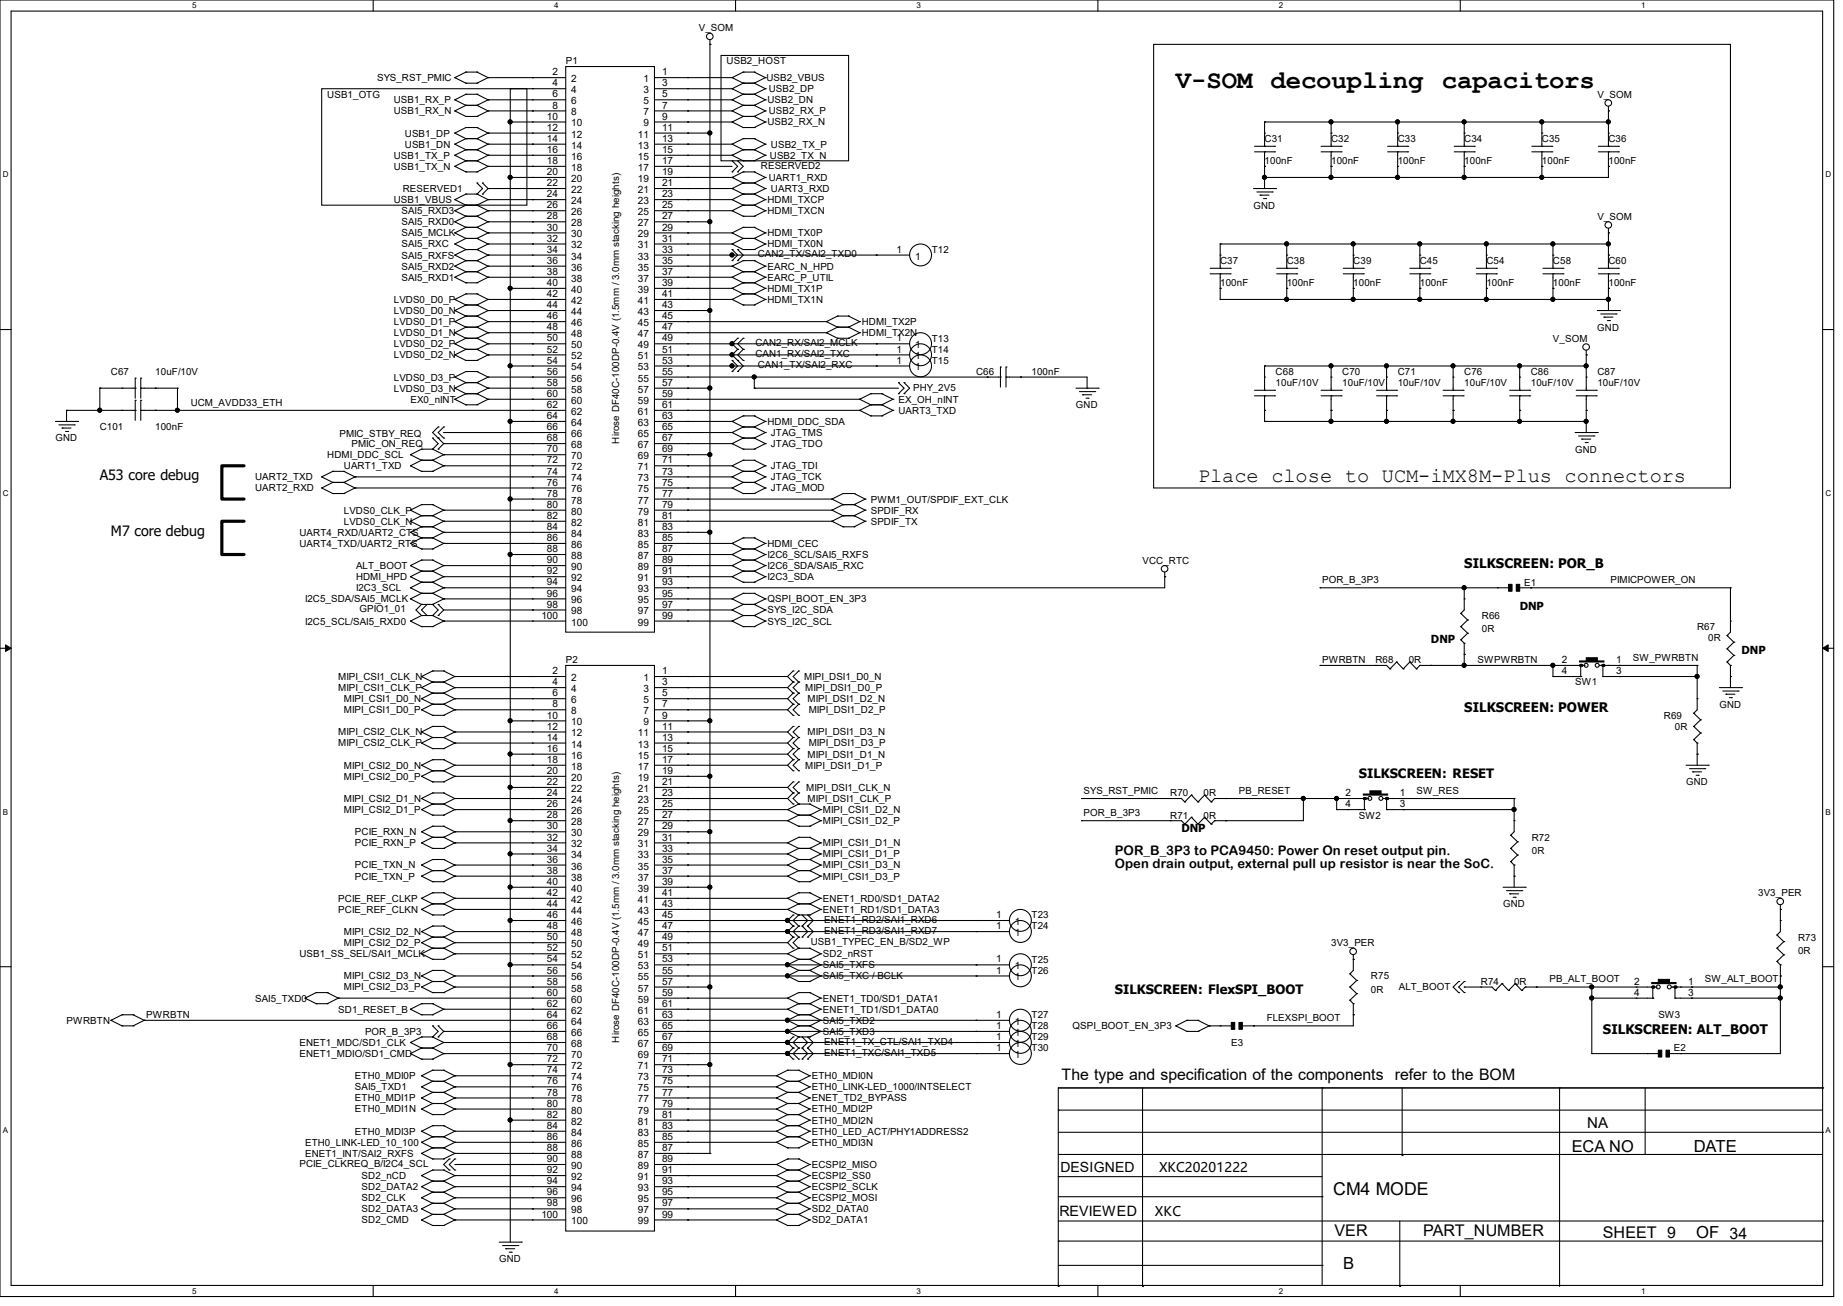
[picture p145: page 6]

Place close to UCM-iMX8M-Plus connectors

POR_B_3P3 to PCA9450: Power On reset output pin.
Open drain output, external pull up resistor is near the SoC.

NA
ECA NO | DATE

DESIGNED | XKC20201222 | CM4 MODE

# SYS_I2C to GPIO expander-EX0 Addres:0X40

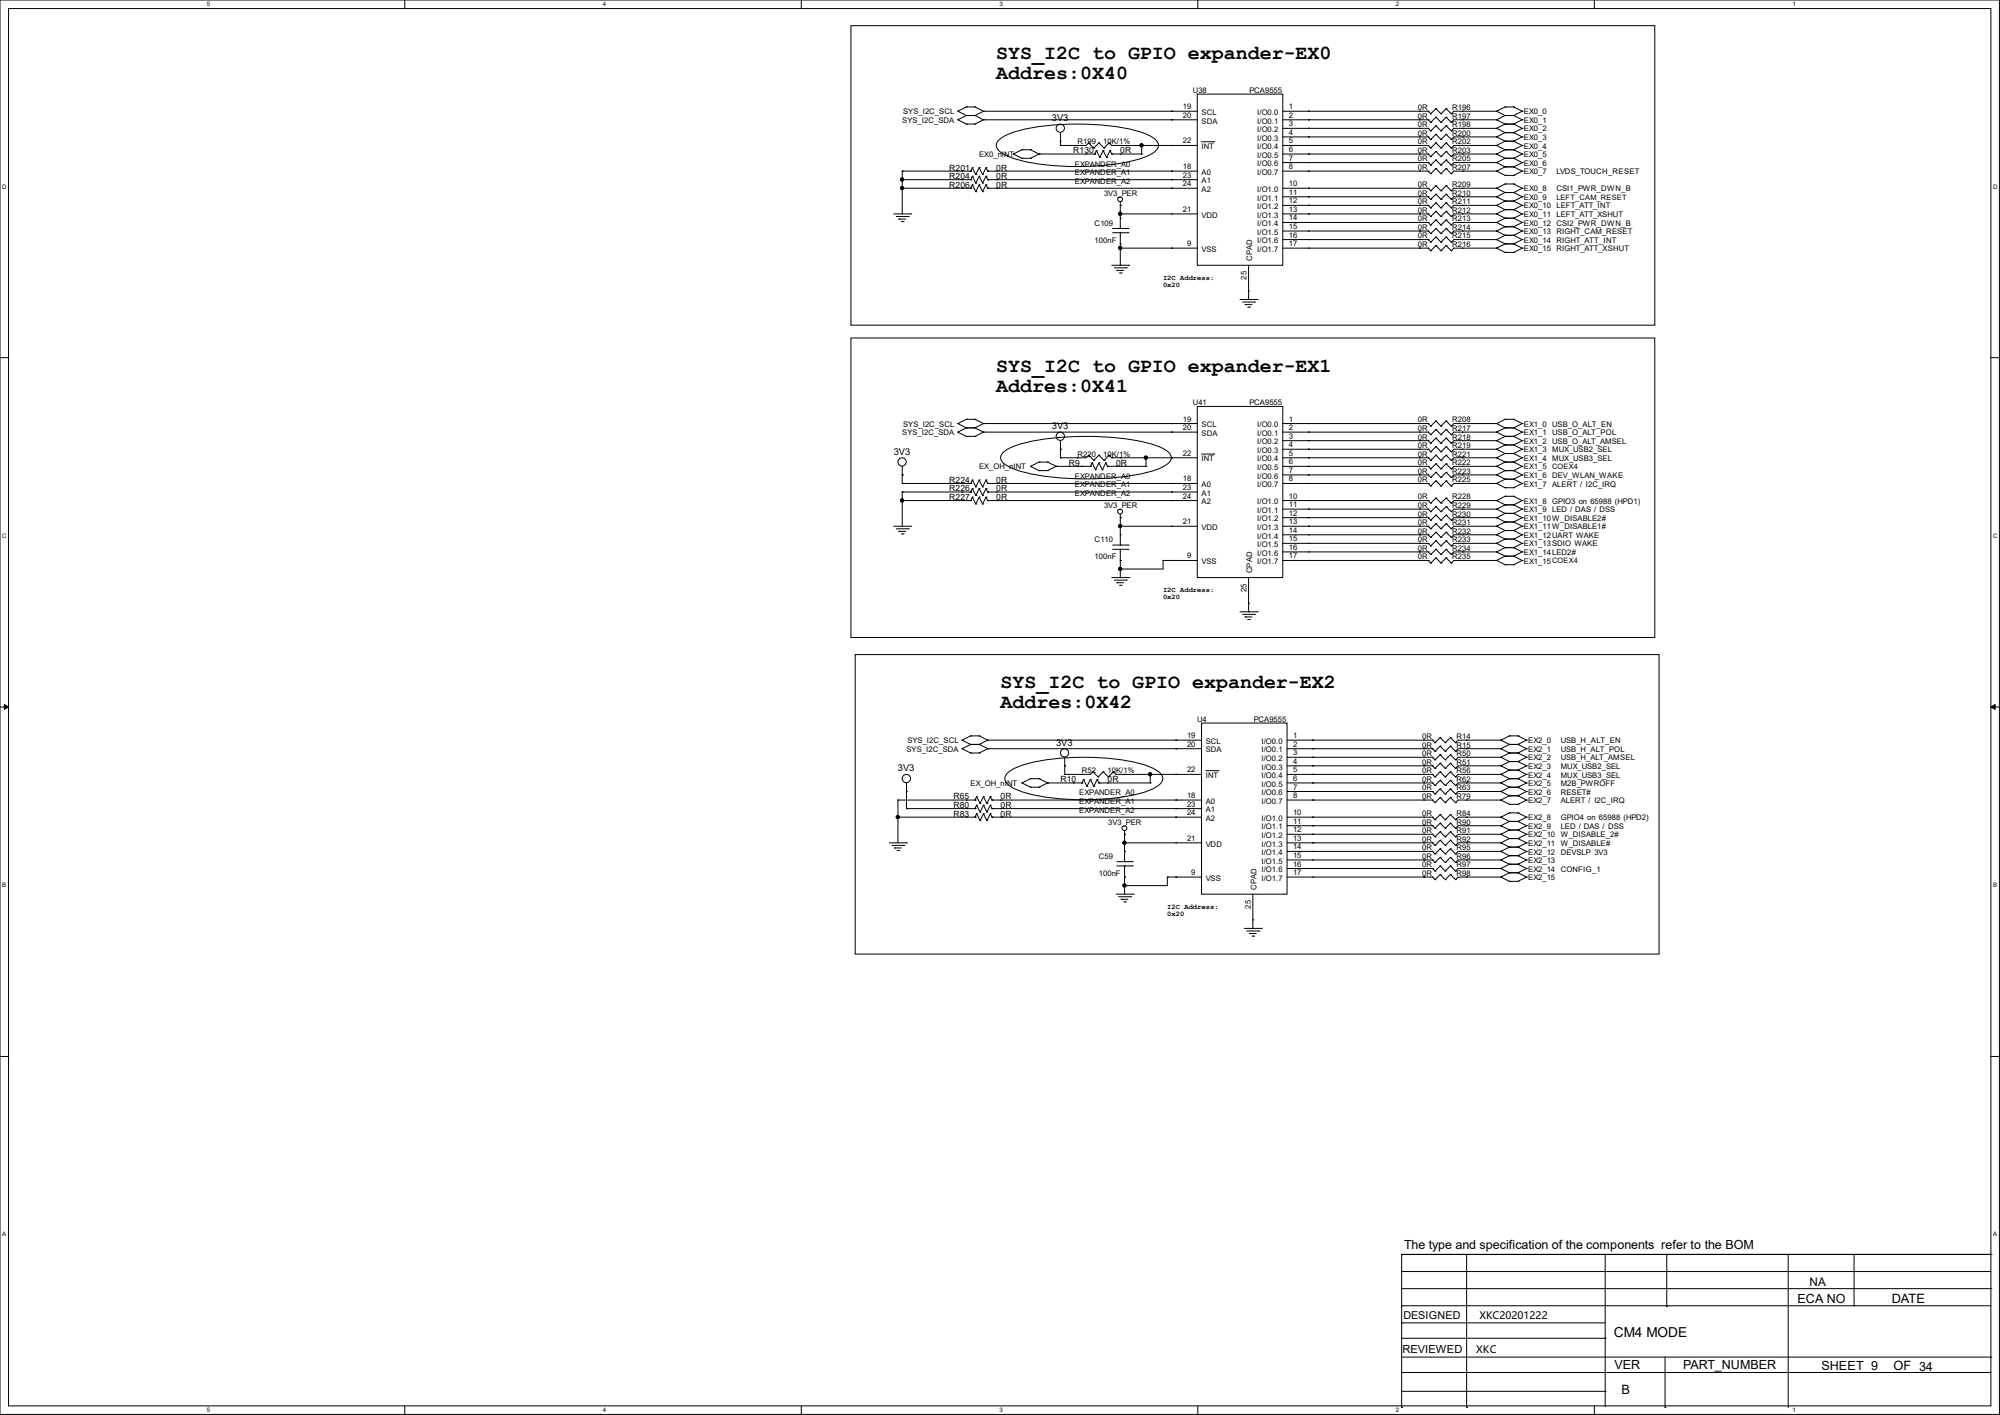
[picture p146: page 7]

The type and specification of the components refer to the BOM

NA
ECA NO | DATE

# (WWAN PCIe/USB3, NO SATA)

# M.2 Socket - Key B

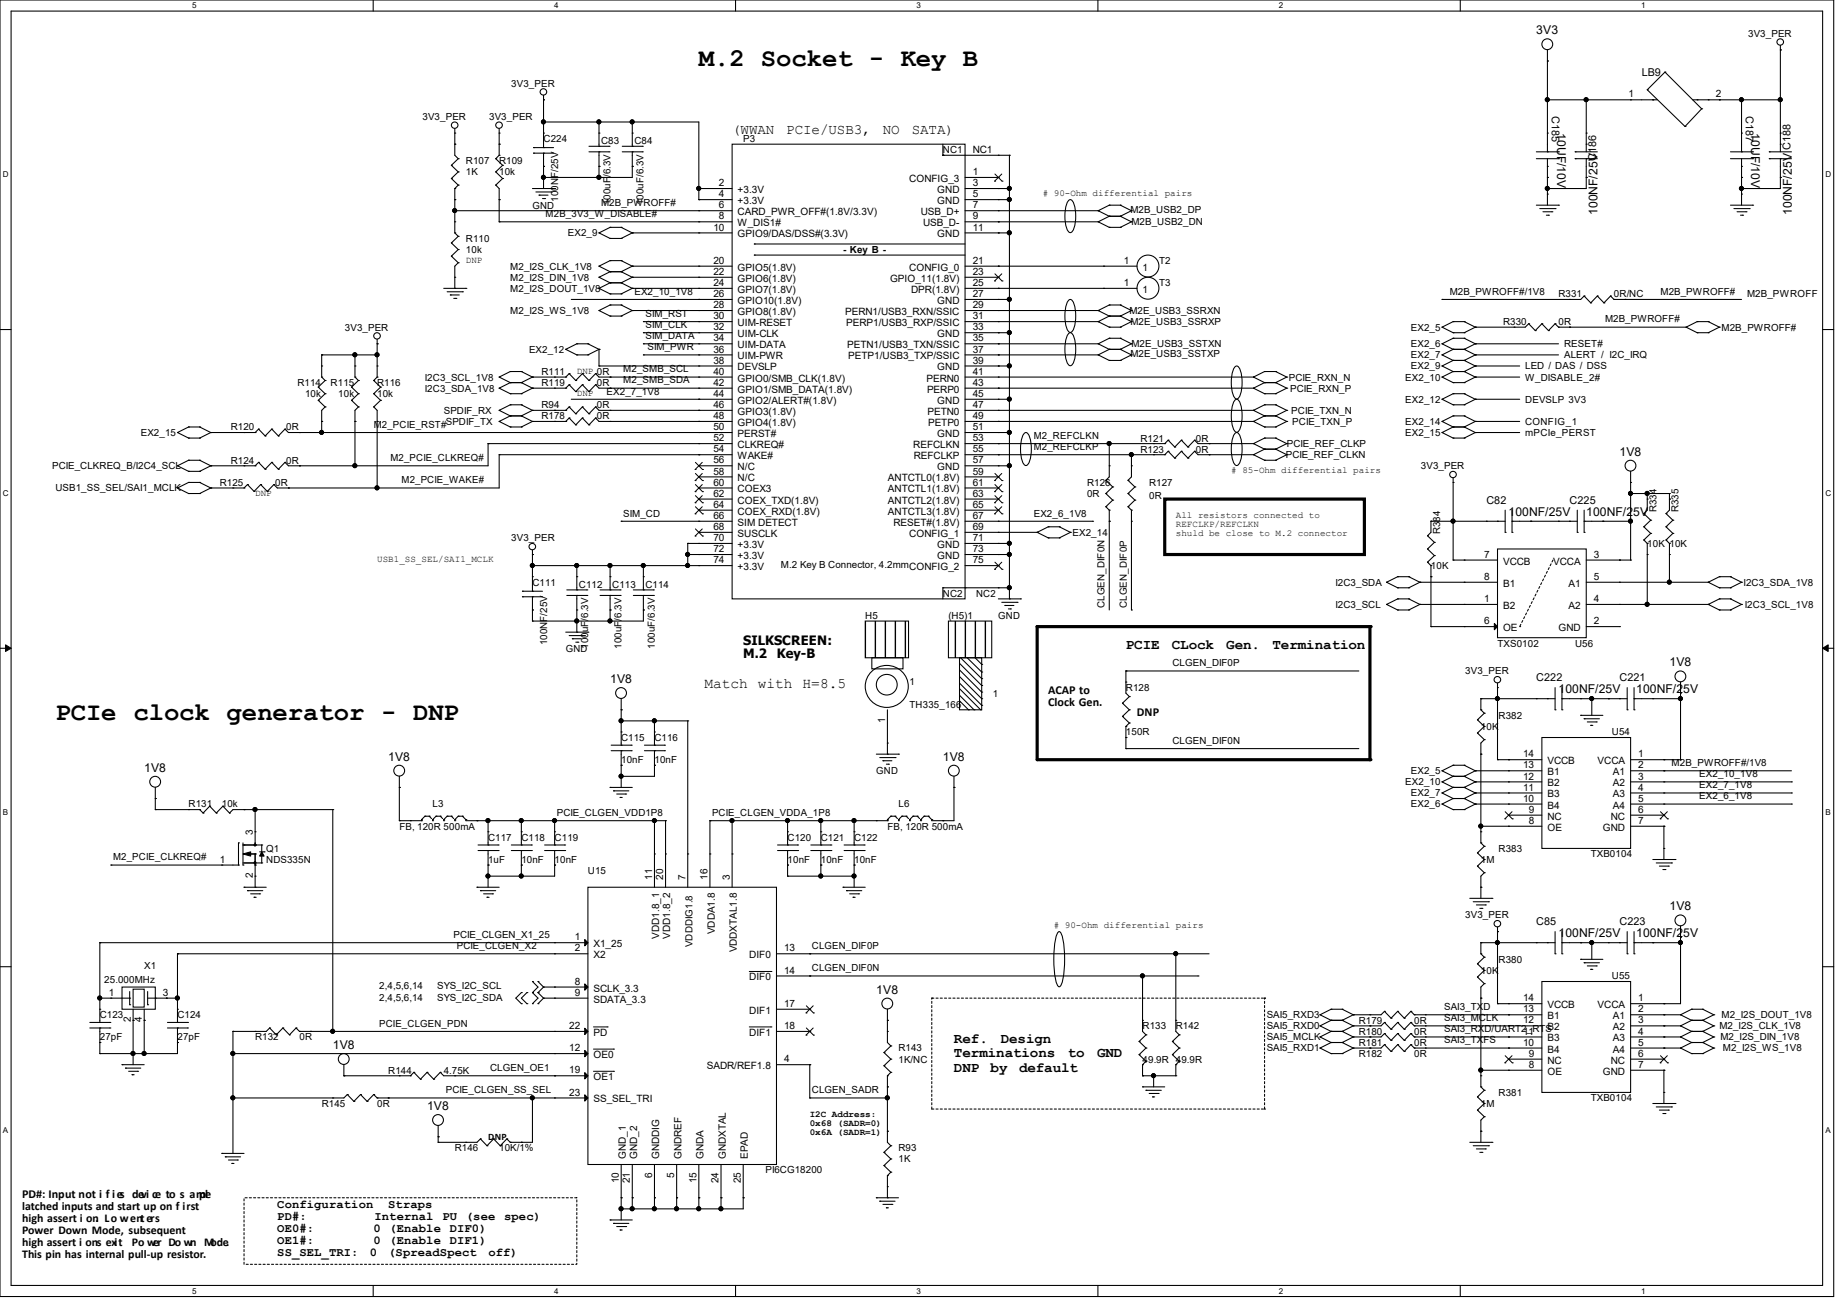
[picture p147: page 8]

All resistors connected to
REFCLKP/REFCLKN
shuld be close to M.2 connector

PCIE CLock Gen. Termination

PCIe clock generator - DNP

PD#: Input not i f i es devi ce to s ample
latched inputs and start up on f irst
high assert i on. Lo w ent ers
Power Down Mode, subsequent
high assert i ons exit Po wer Do wn Mode.
This pin has internal pull-up resistor.

## (WWAN PCIe/USB3, NO SATA)

# M.2 Socket - Key E

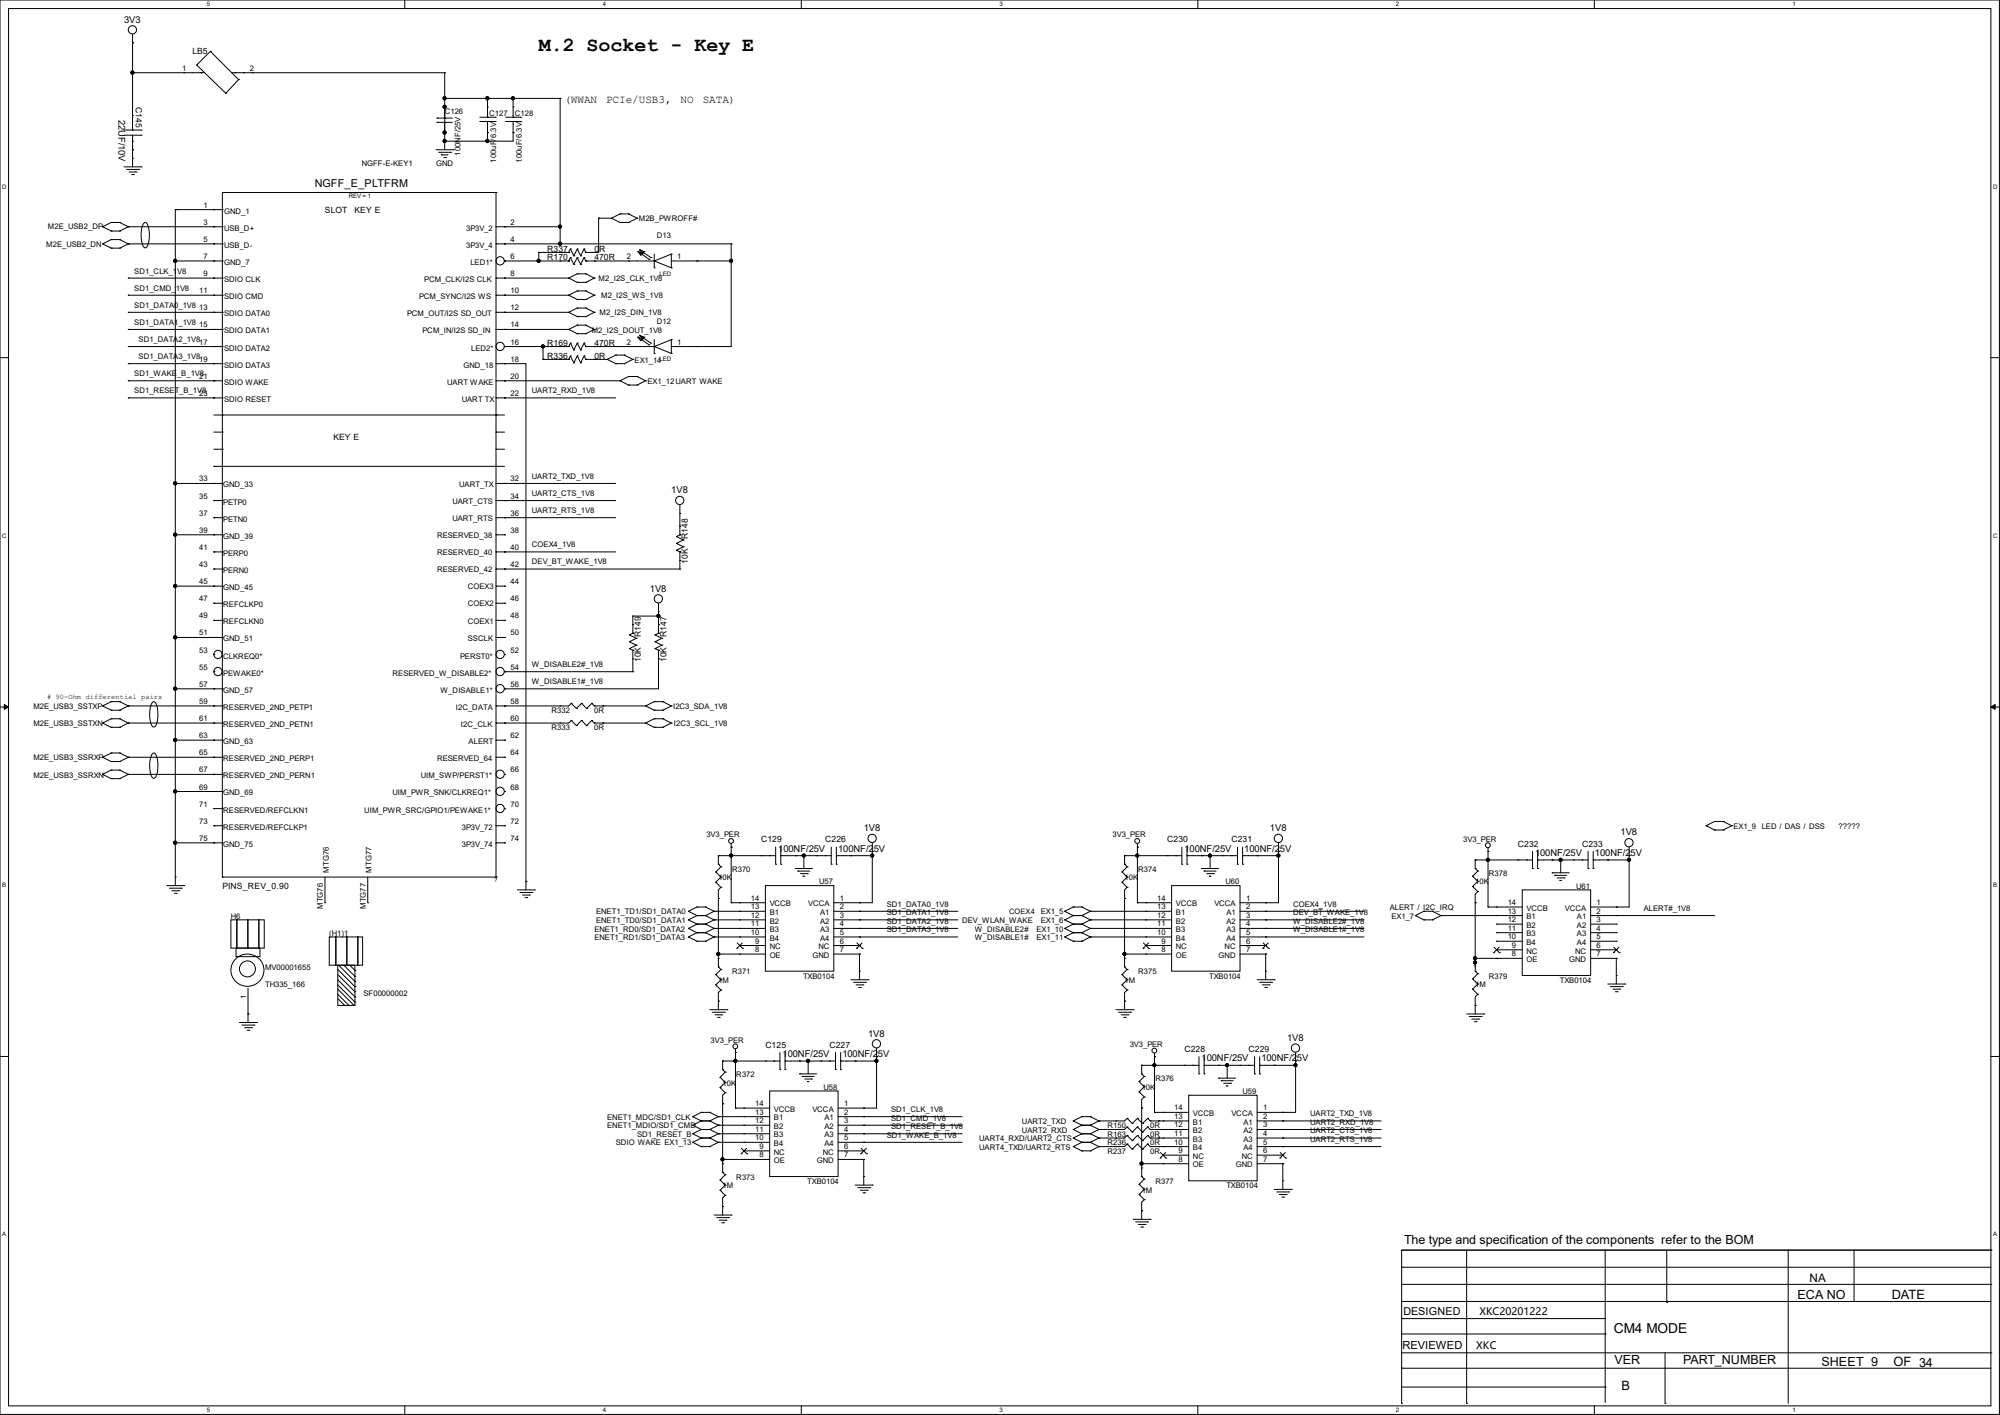
[picture p148: page 9]

The type and specification of the components refer to the BOM

NA
ECA NO | DATE

# HDMI connector with eARC

## # 100-Ohm diff pairs

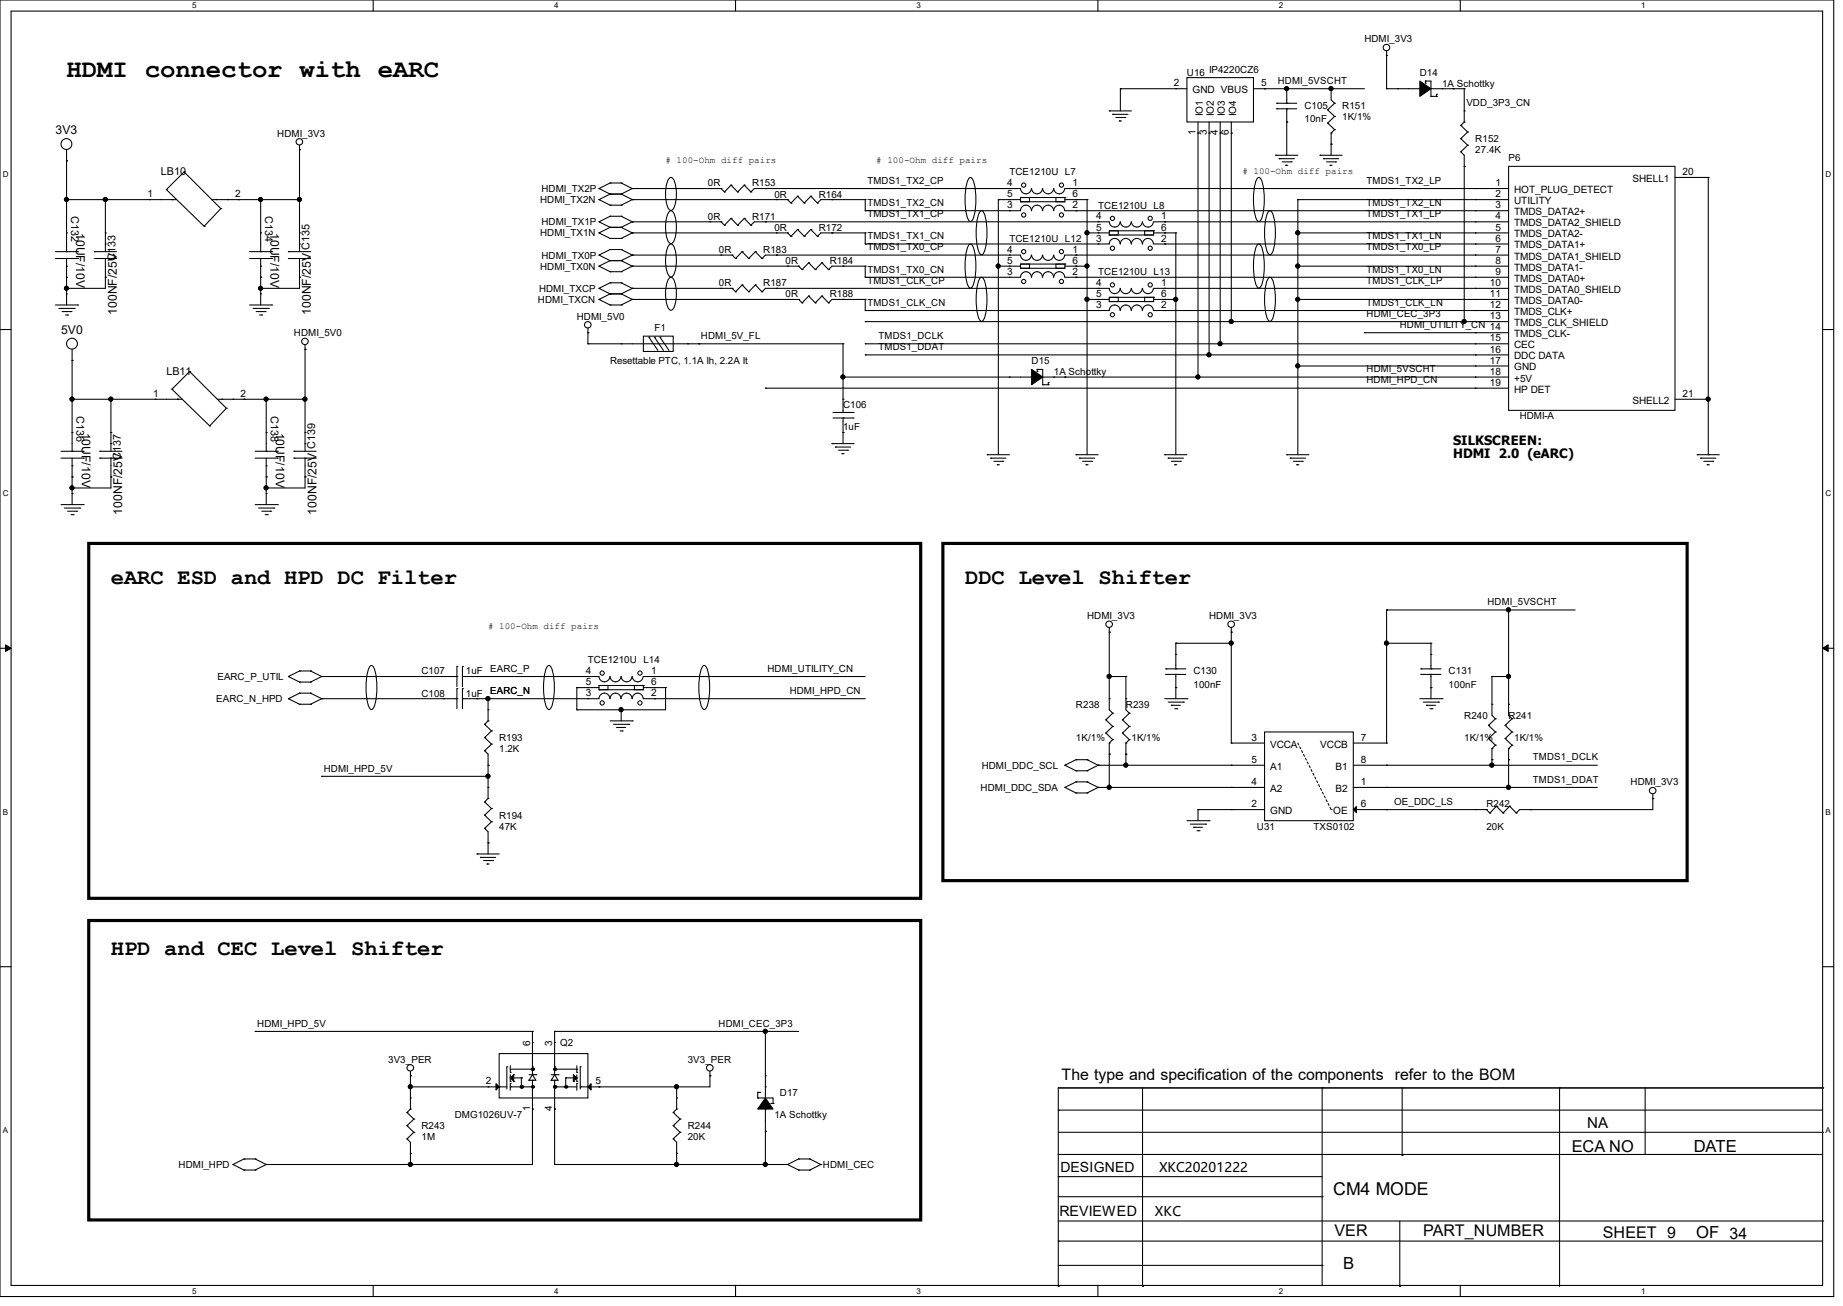
[picture p149: page 10]

TCE1210U L13 | | TMDS_DATA1- 8
4 1 5 6 3 2 | TMDS1_CLK_LP | TMDS_DATA0_SHIELD 10 TMDS_DATA0- 11

Resettable PTC, 1.1A Ih, 2.2A It

HPD and CEC Level Shifter

The type and specification of the components refer to the BOM

NA
ECA NO | DATE

DESIGNED | XKC20201222 | CM4 MODE

# Serial debug console Micro-SD socket (bootable)

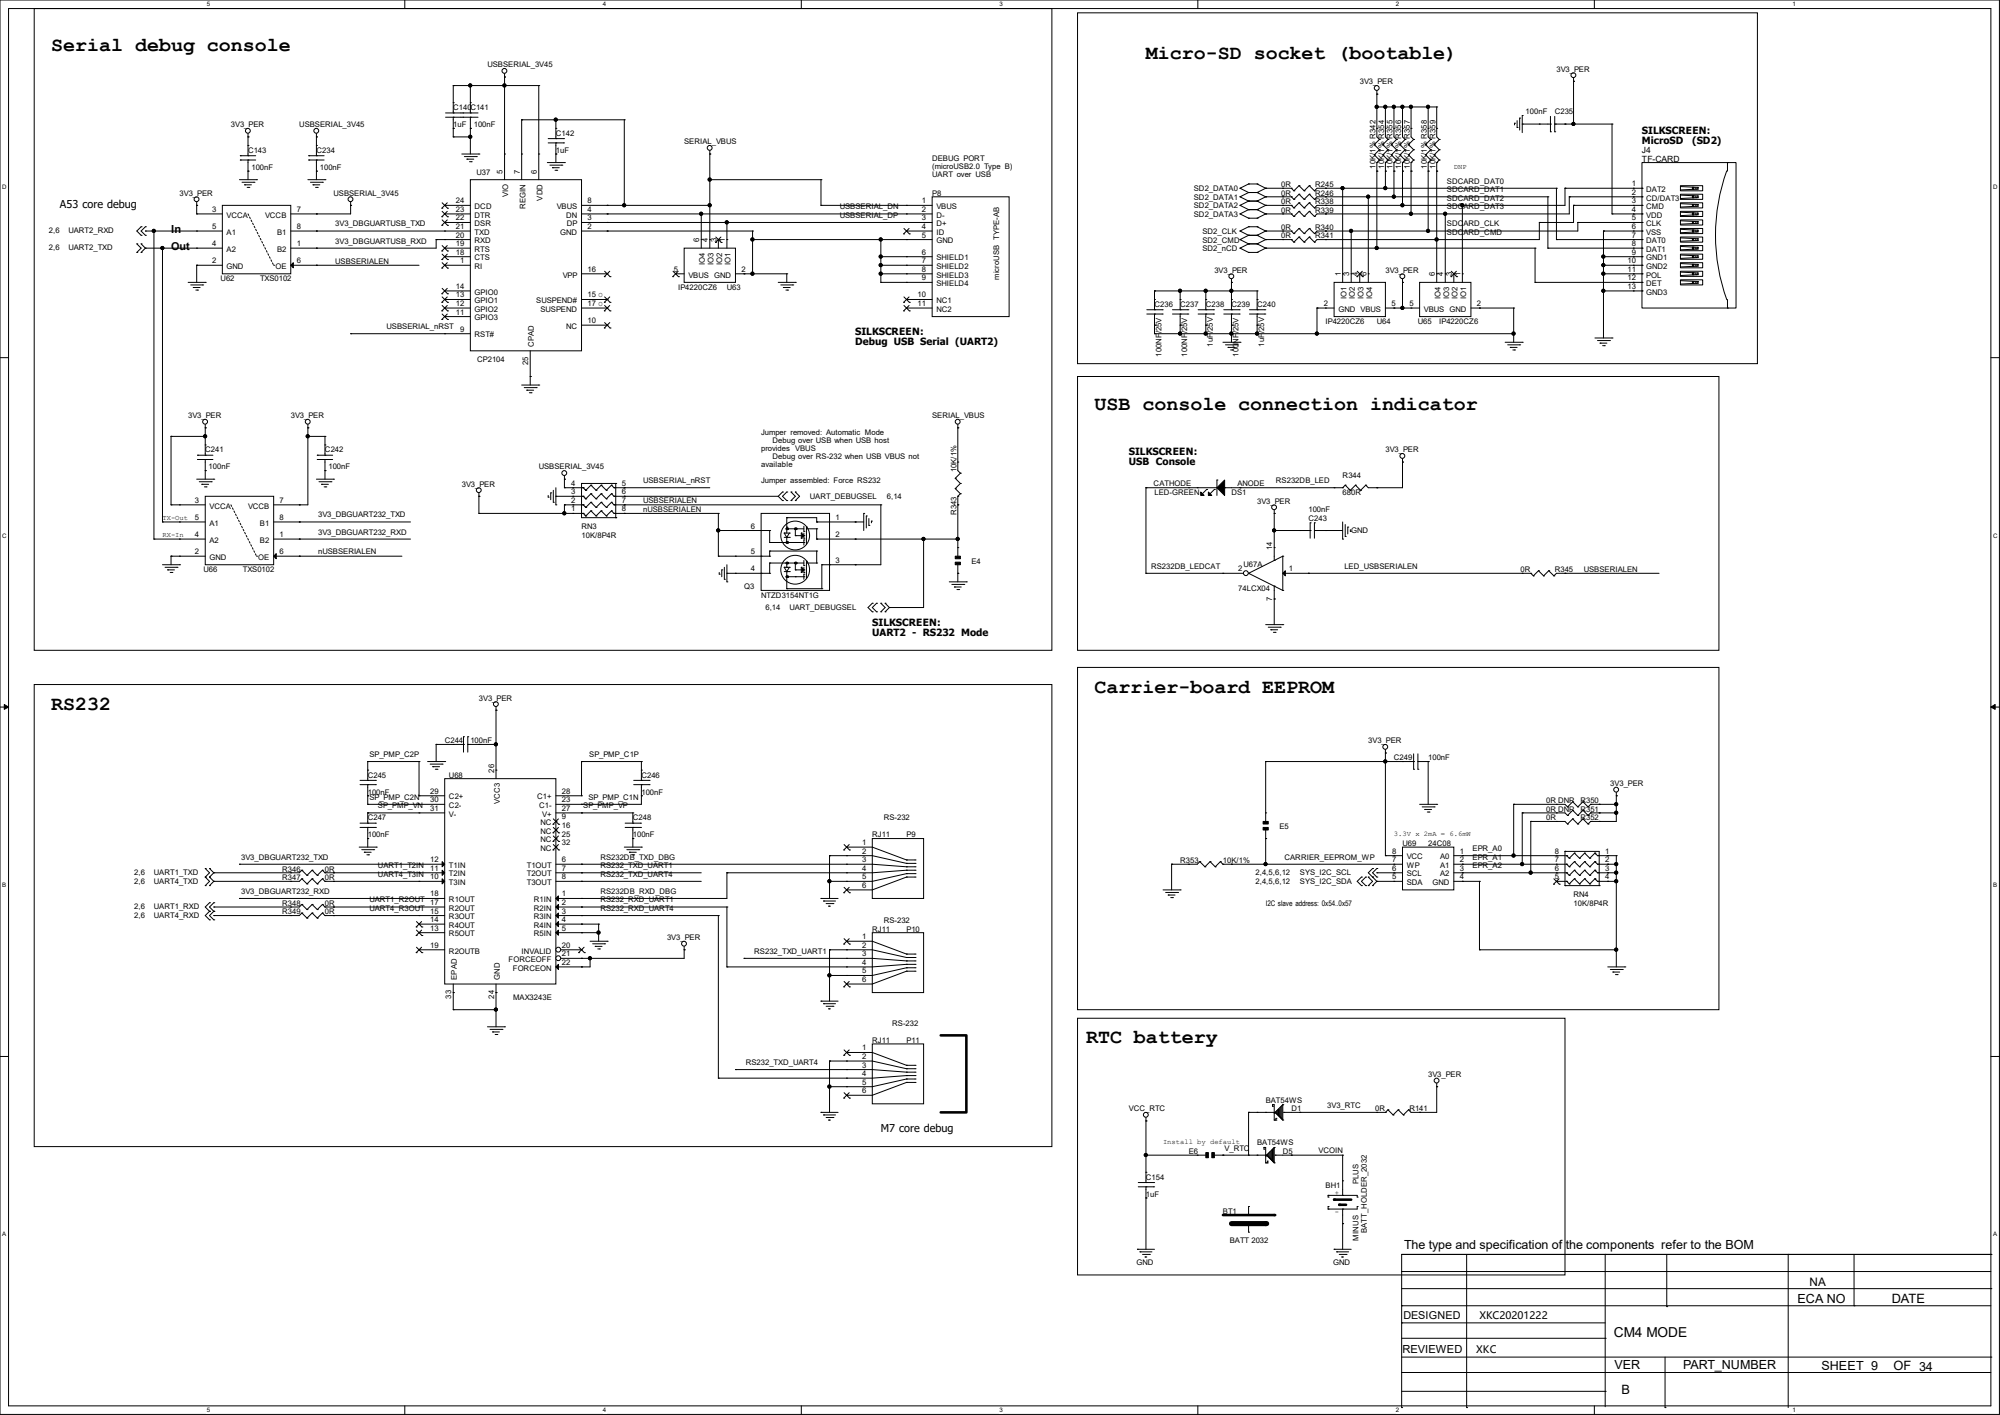
[picture p150: page 11]

USB console connection indicator

Jumper removed: Automatic Mode
Debug over USB when USB host
provides VBUS
Debug over RS-232 when USB VBUS not
available

The type and specification of the components refer to the BOM

NA
ECA NO | DATE

## 22-pin Connector for RPi cameras Four MIPI-CSI lanes connected

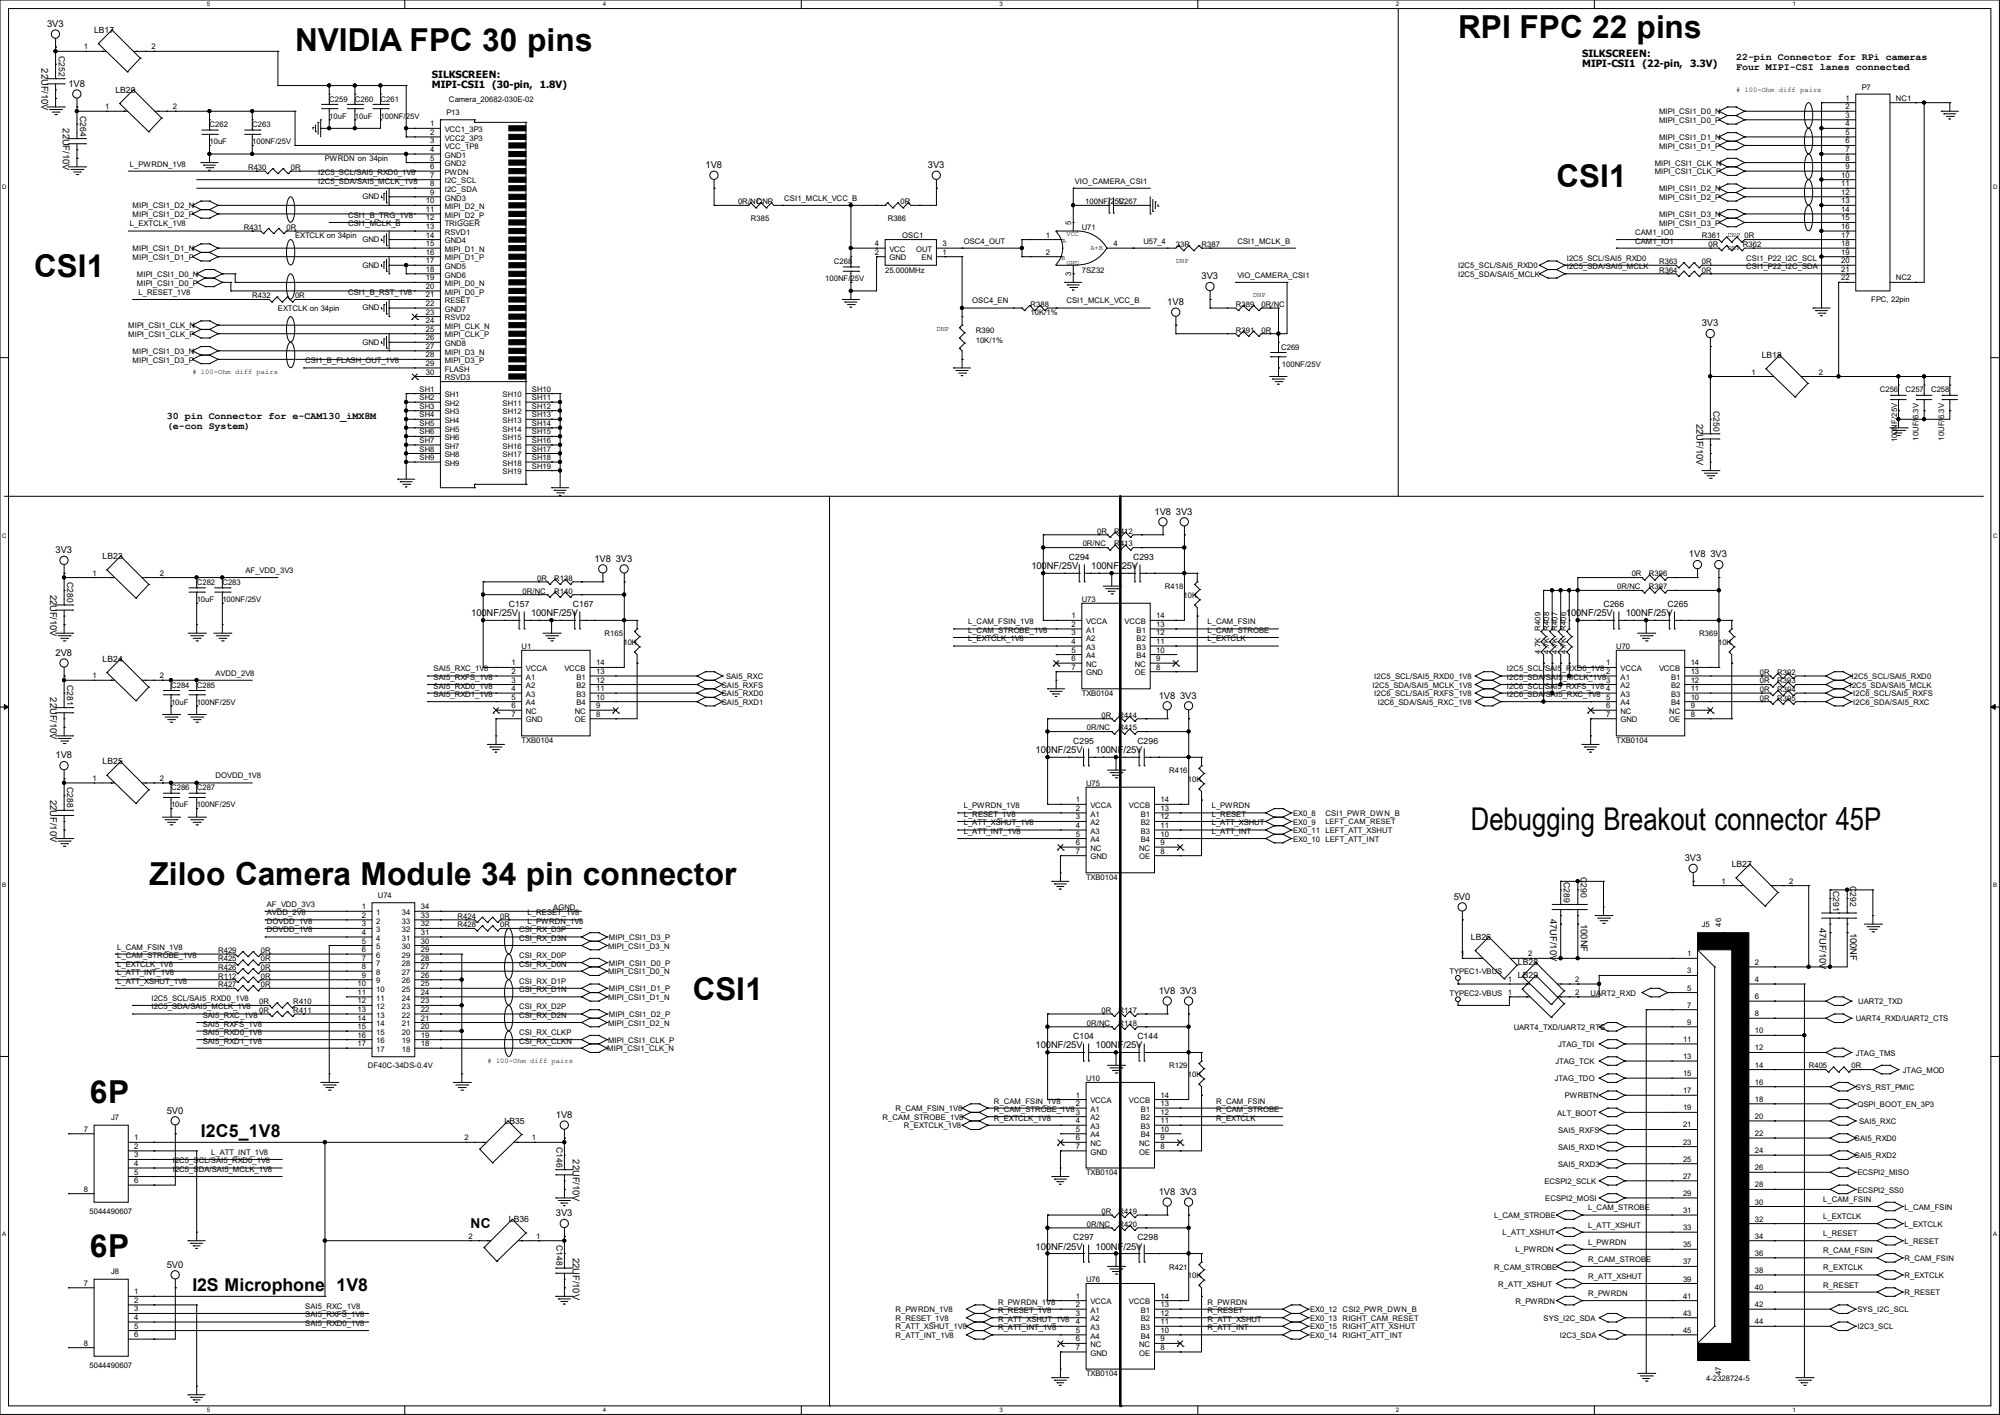
[picture p151: page 12]

RPI FPC 22 pins NVIDIA FPC 30 pins

Ziloo Camera Module 34 pin connector

# NVIDIA FPC 30 pins

CSI2 | CSI2

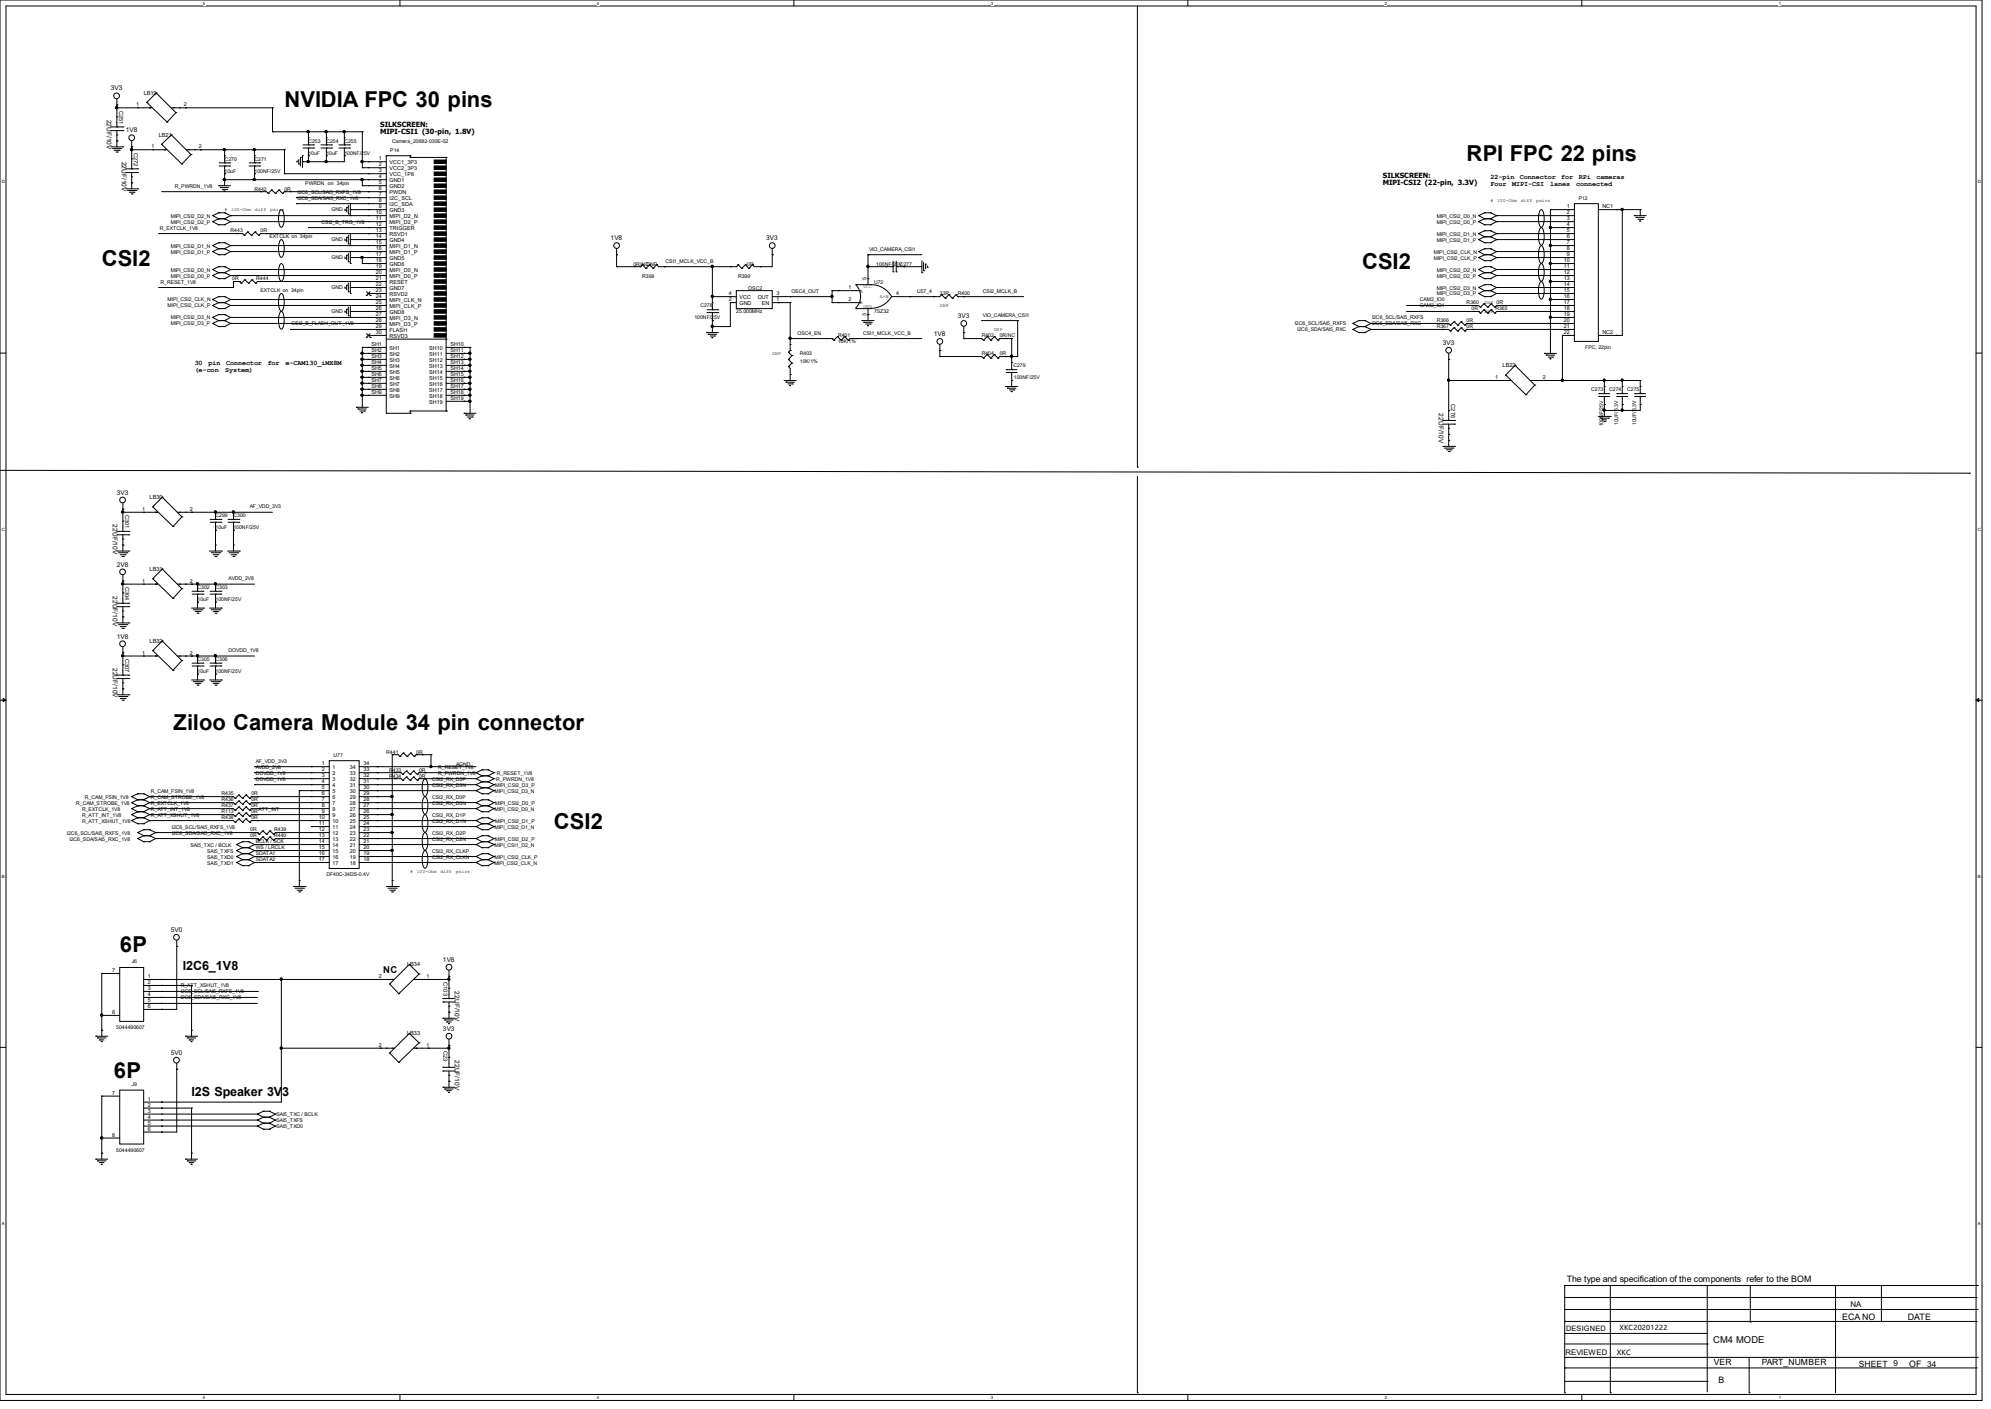
[picture p152: page 13]

22-pin Connector for RPi cameras
Four MIPI-CSI lanes connected

Ziloo Camera Module 34 pin connector

The type and specification of the components refer to the BOM

NA
ECA NO | DATE
