experientials/ziloo/Hardware/909c/TESTING.md

# Testing Model 909b

## Development board + 201 Camera Modules

Parts
- Compulab SB-UCM-iMX8PLUS carrier board
- 201 RGB module
- 201 IR module
- 2 * I-PEX 30 pin cables

## Development board + 201 Camera Modules

Parts
- I-Pi SMARC IMX8M Plus carrier board
- 201 RGB module
- 201 IR module
- 22 pins to 15 pins cable
- 22 pins cable

## DisplayLink support

- [Raspberry Pi on DisplayLink](https://blog.aaronbieber.com/2020/01/06/raspberry-pi-on-displaylink.html)
- [i.MX USB display with displaylink issue](https://community.nxp.com/t5/i-MX-Processors/USB-display-with-displaylink-issue/m-p/774138)
- [Amazon](https://www.amazon.de/s?k=displaylink+monitor&__mk_de_DE=ÅMÅŽÕÑ&crid=23HZRVAF1OABS&sprefix=displaylink+monitor%2Caps%2C65&ref=nb_sb_noss)
- [DisplayLink GitHub](https://github.com/DisplayLink/evdi)
-
