experientials/ziloo/Hardware/909b/Ziloo Bridge 909 rev B.pdf

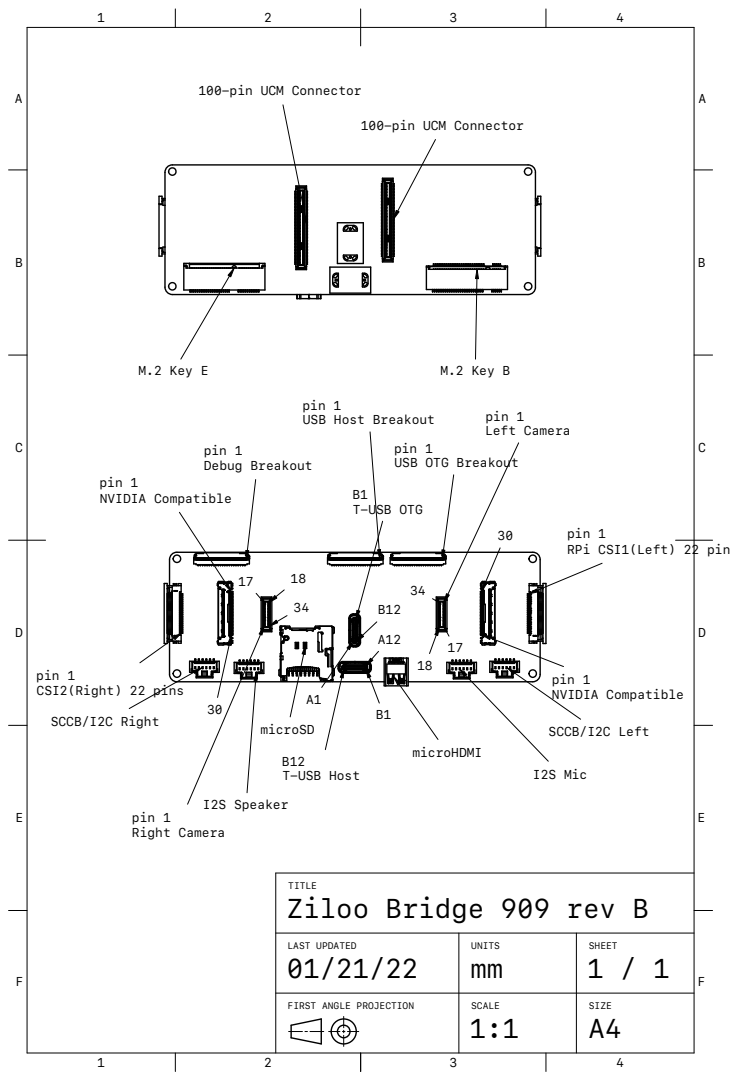
[picture p184: page 1]
pin 1 Debug Breakout; microHDMI; microSD; B12 T-USB Host; pin 1 Left Camera; pin 1 Right Camera; pin 1 NVIDIA Compatible; pin 1; pin 1 CSI2(Right) 22 pins; M.2 Key E; M.2 Key B; SCCB/I2C Right; SCCB/I2C Left; I2S Mic; I2S Speaker; TITLE Ziloo Bridge 909 rev B; LAST UPDATED 01/21/22; UNITS mm; SHEET 1 / 1; FIRST ANGLE PROJECTION; SCALE; SIZE A4

100-pin UCM Connector

pin 1
USB Host Breakout

USB OTG Breakout
T-USB OTG

RPi CSI1(Left) 22 pins
