experientials/ziloo/Hardware/909c/HDMI connector with eARC.pdf

# HDMI connector with eARC

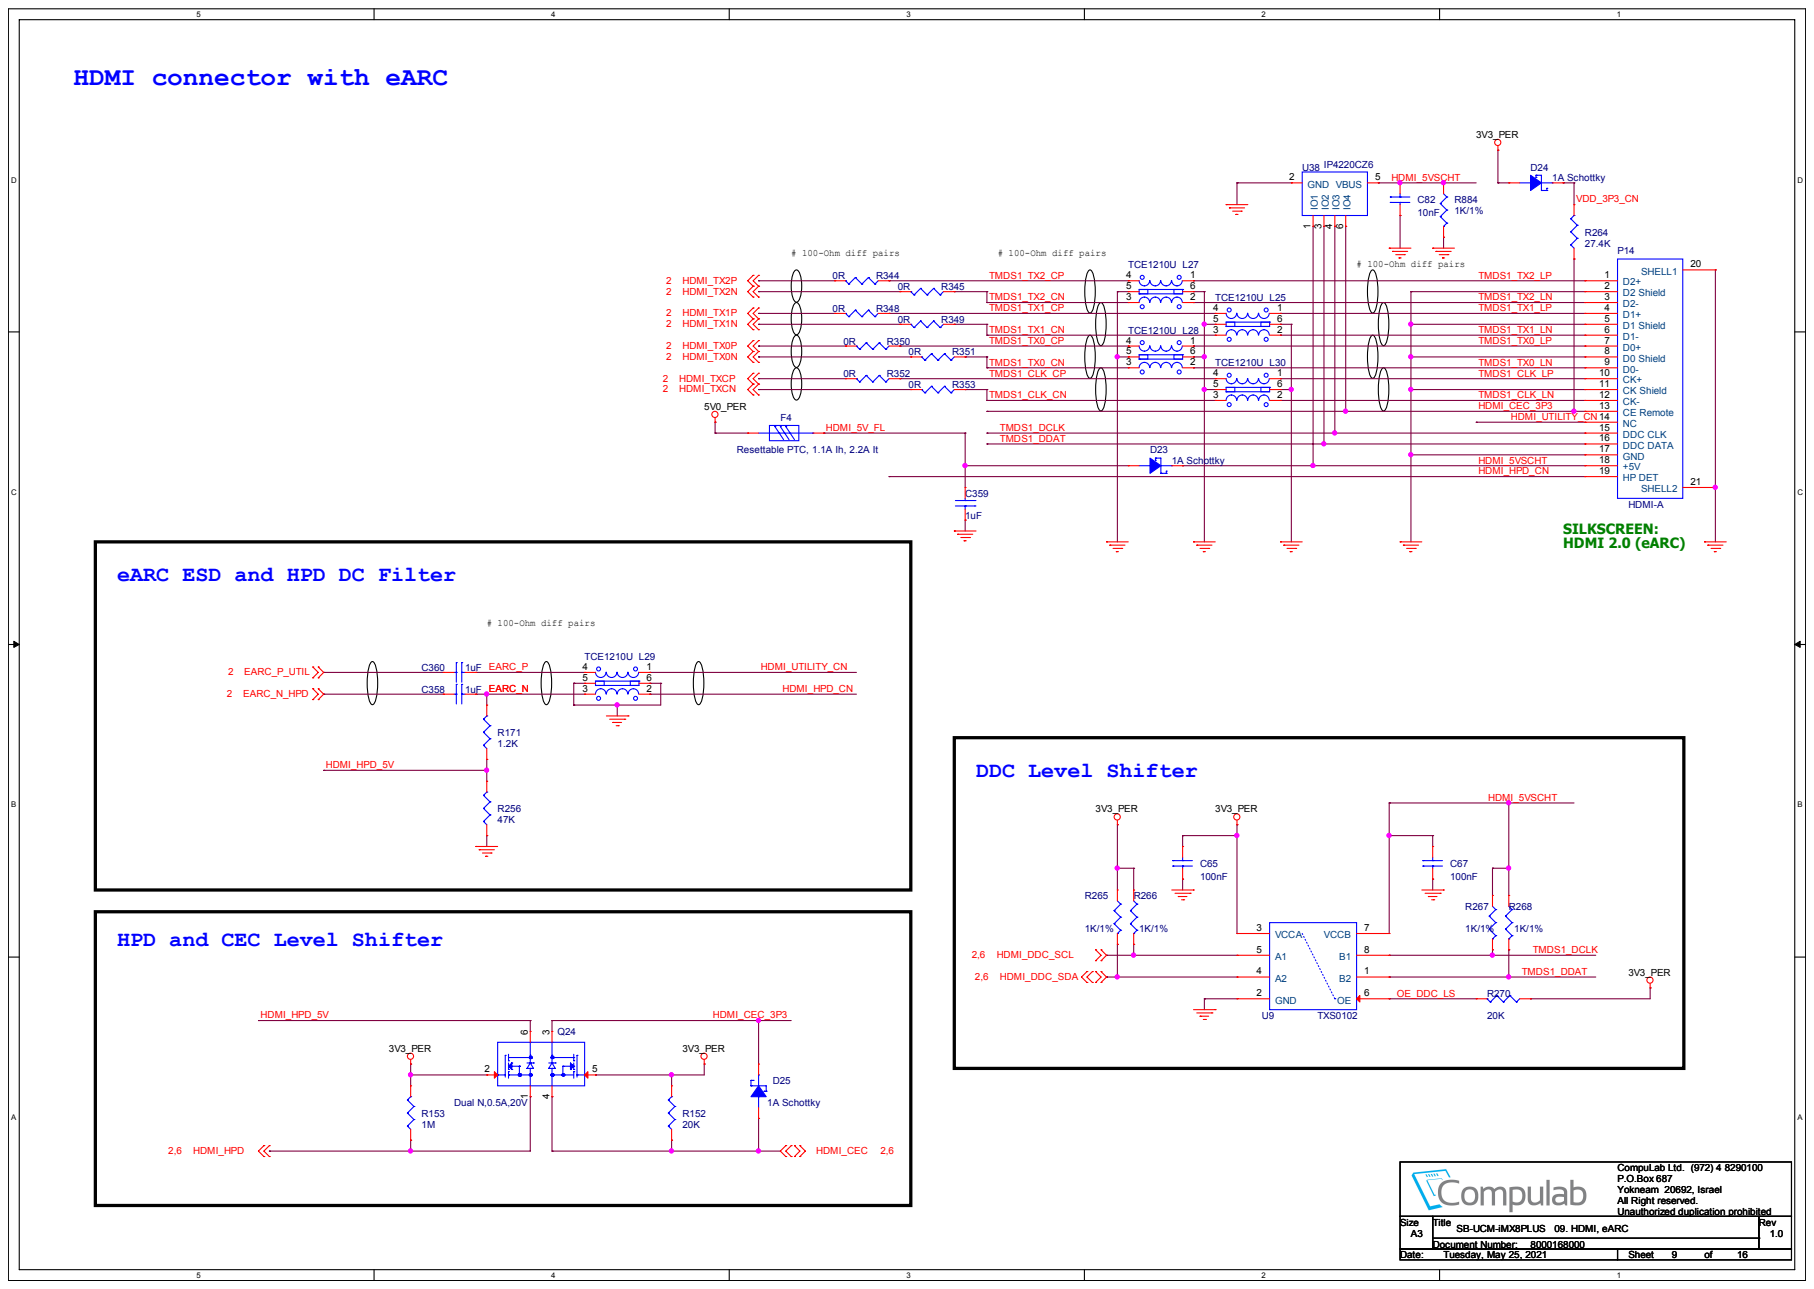
[picture p192: page 1]

Resettable PTC, 1.1A Ih, 2.2A It

eARC ESD and HPD DC Filter

HPD and CEC Level Shifter

SB-UCM-iMX8PLUS 09. HDMI, eARC Size
Document Number:

Title
SB-UCM-iMX8PLUS 09. HDMI, eARC
