experientials/ziloo/Hardware/909c/USB-OTG-hookup.pdf

# USB3.0 Type-C

## SILKSCREEN:

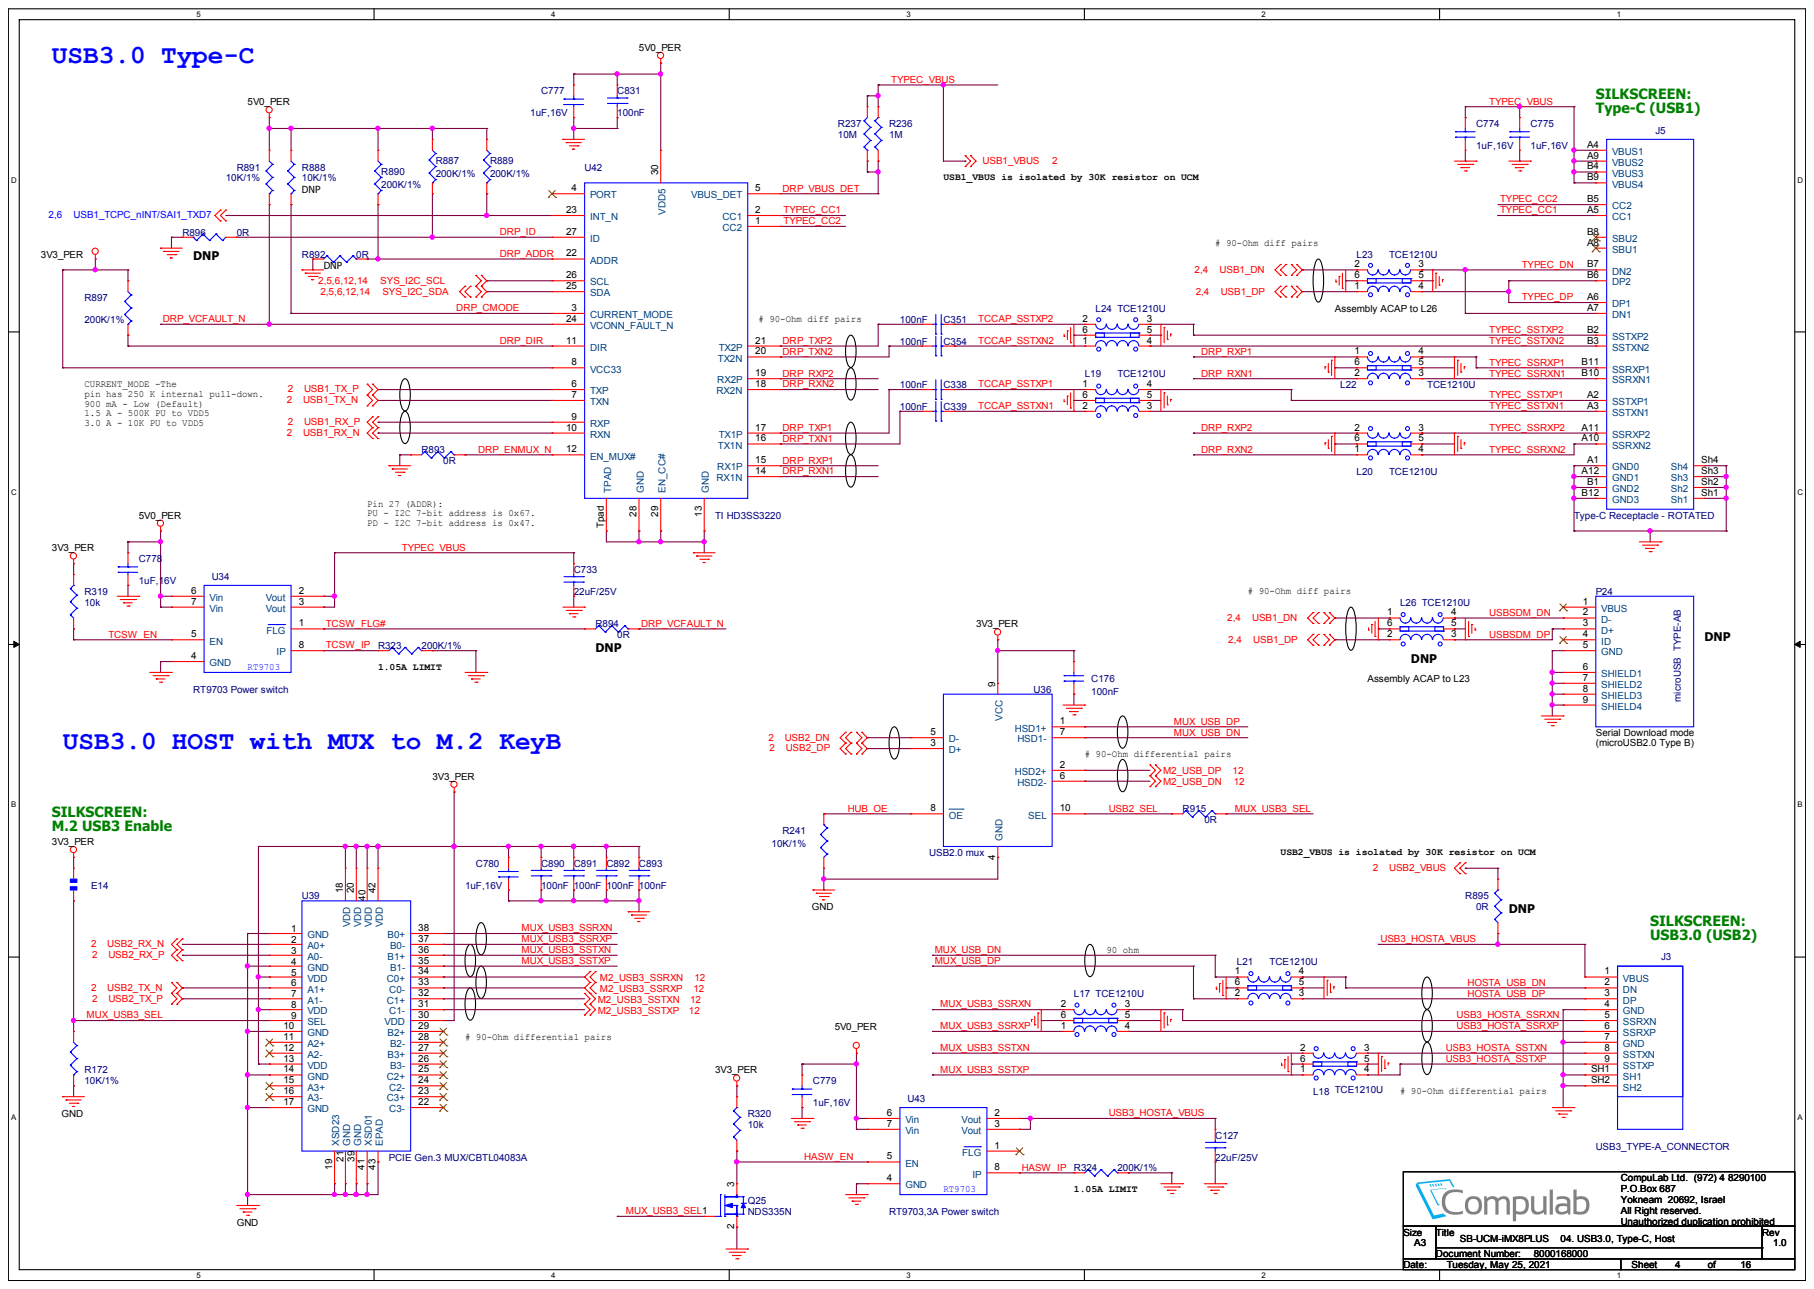
[picture p193: page 1]

USB1_VBUS is isolated by 30K resistor on UCM

CURRENT_MODE -The
pin has 250 K internal pull-down.
900 mA - Low (Default)
1.5 A - 500K PU to VDD5
3.0 A - 10K PU to VDD5

Pin 27 (ADDR):
PU - I2C 7-bit address is 0x67.
PD - I2C 7-bit address is 0x47.

USB3.0 HOST with MUX to M.2 KeyB

USB2_VBUS is isolated by 30K resistor on UCM

SB-UCM-iMX8PLUS 04. USB3.0, Type-C, Host Size
Document Number:

Title
SB-UCM-iMX8PLUS 04. USB3.0, Type-C, Host
