experientials/ziloo/Hardware/201/OV2735-combined-module/Ziloo simplified v2 camera module.pdf

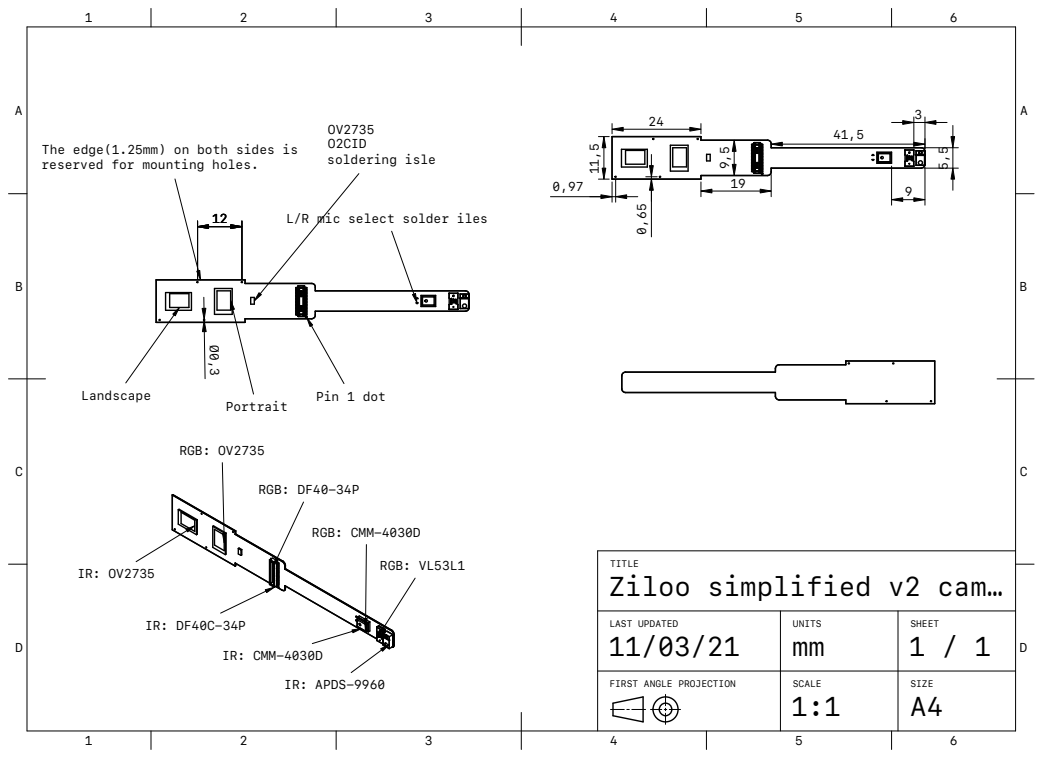
[picture p194: page 1]
RGB: OV2735; RGB: DF40-34P; IR: APDS-9960; RGB: VL53L1; RGB: CMM-4030D; IR: CMM-4030D; Pin 1 dot; OV2735 O2CID soldering isle; Landscape; Portrait

The edge(1.25mm) on both sides is
reserved for mounting holes.

L/R mic select solder iles

TITLE
Ziloo simplified v2 cam

LAST UPDATED 11/03/21 | UNITS mm | SHEET 1 / 1

FIRST ANGLE PROJECTION | | | SCALE 1:1 | SIZE A4
