experientials/ziloo/Hardware/201/OV2735-module/CBT-2MPFF84-MPV1 0-IR Schematic Diagram 211105.pdf

D

6 | 5 | 4 | 3 | 2 | 1

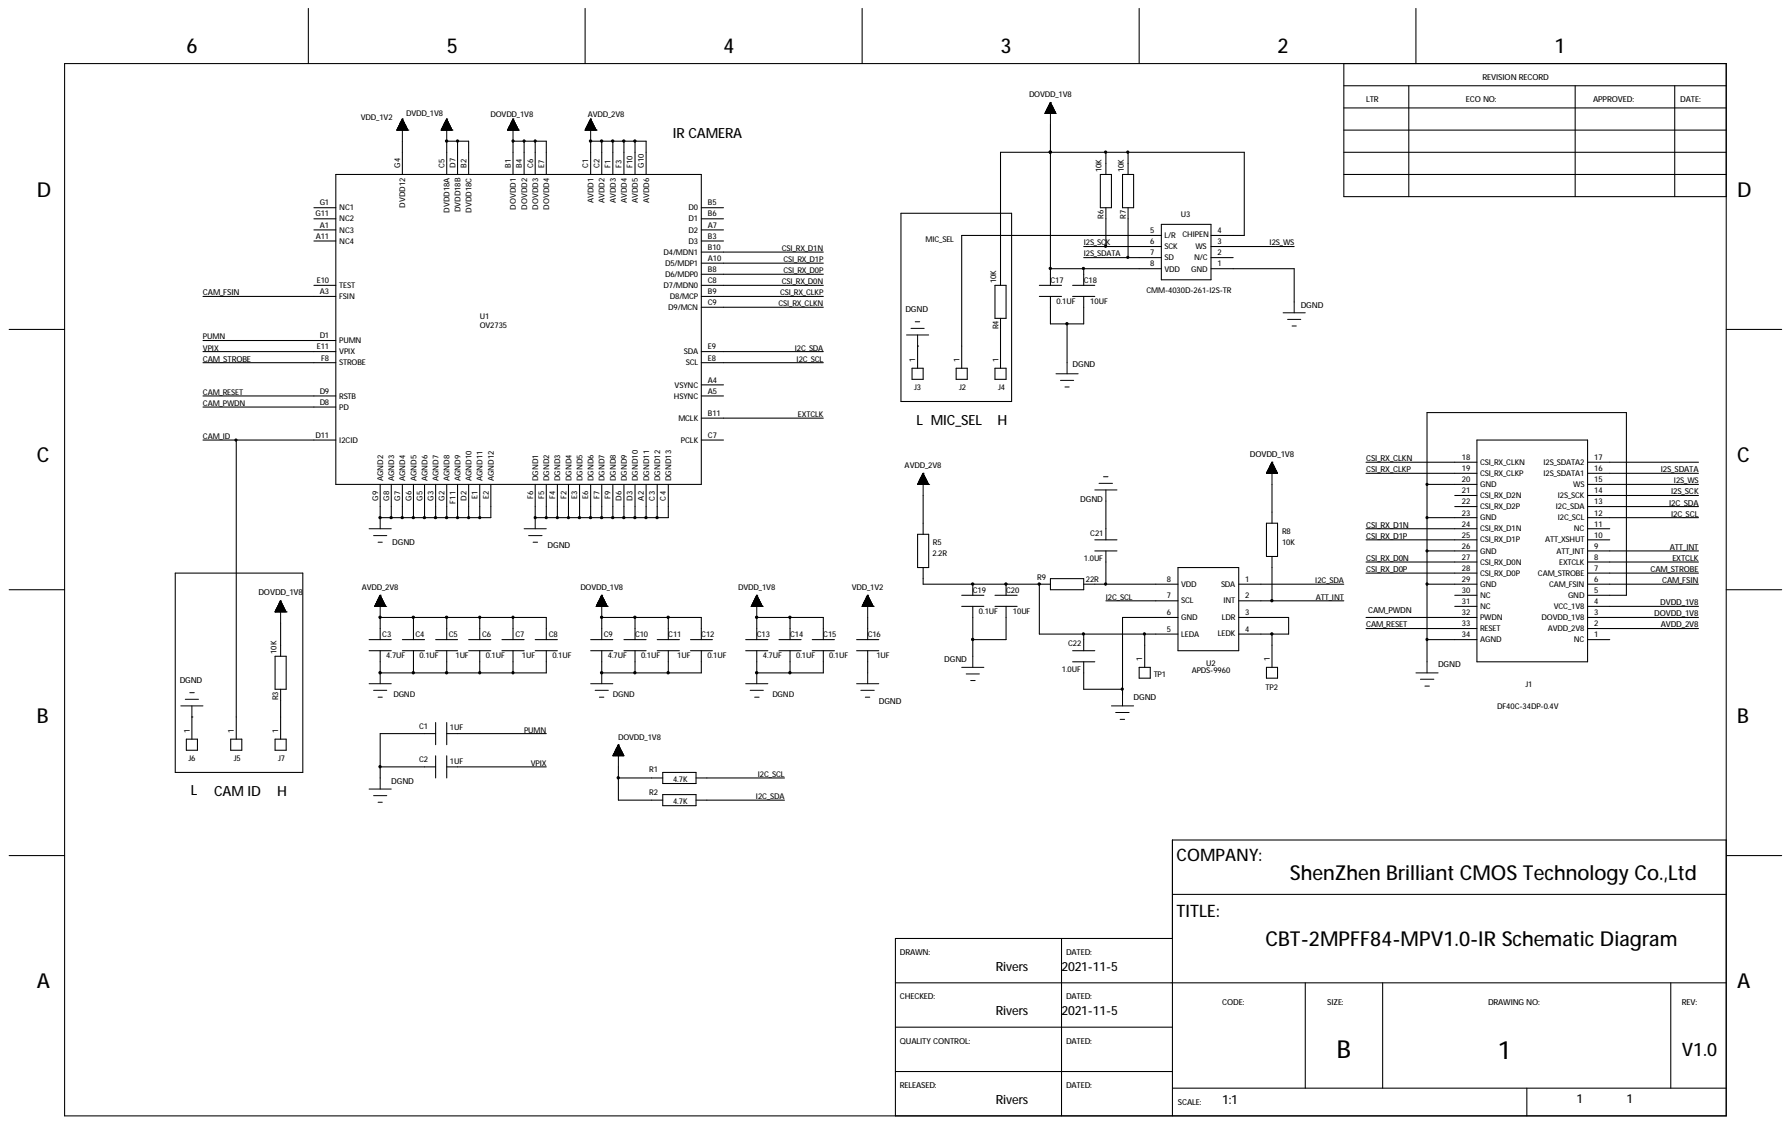
[picture p195: page 1]

DOVDD_1V8 | REVISION RECORD

LTR | ECO NO: | APPROVED: | DATE:

ShenZhen Brilliant CMOS Technology Co.,Ltd

CBT-2MPFF84-MPV1.0-IR Schematic Diagram

DRAWN: Rivers | DATED: 2021-11-5

CHECKED: Rivers | DATED: 2021-11-5 | CODE: | SIZE: B | DRAWING NO: 1 | REV: V1.0

QUALITY CONTROL: | DATED:

RELEASED: Rivers | DATED:

1:1 SCALE: | 1 1
