experientials/ziloo/Hardware/201/OV2735-module/holders/ChuangAn M12 CA5119A.pdf

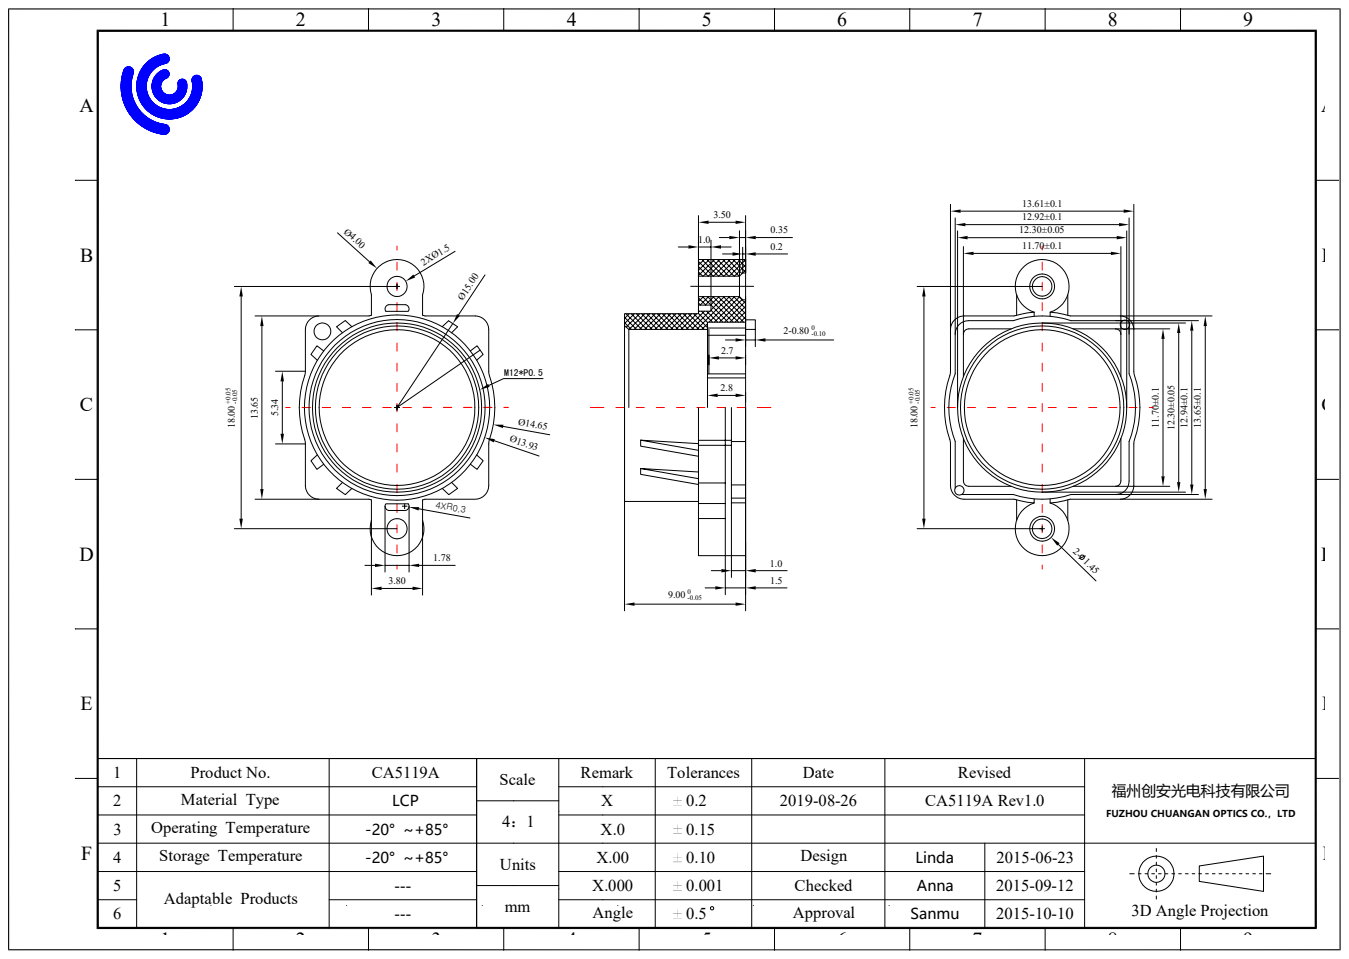
[picture p196: page 1]
Material Type; Operating Temperature; Storage Temperature; LCP -20° ~+85° -20° ~+85°; Scale; Units; Remark; Angle; Tolerances; Approval; Linda; Sanmu; Adaptable Products; Product No.; Date; Revised; 3D Angle Projection; 福州创安光电科技有限公司

X | | 2019-08-26 | CA5119A Rev1.0
X.0 X.00 | Design

FUZHOU CHUANGAN OPTICS CO.，LTD

X.000 | | Checked | Anna | 2015-09-12
