experientials/ziloo/Hardware/201/OV2735-module/holders/ChuangAn M12*P0.5 CA5117A.pdf

3.00 2⁻Ø⁰.7

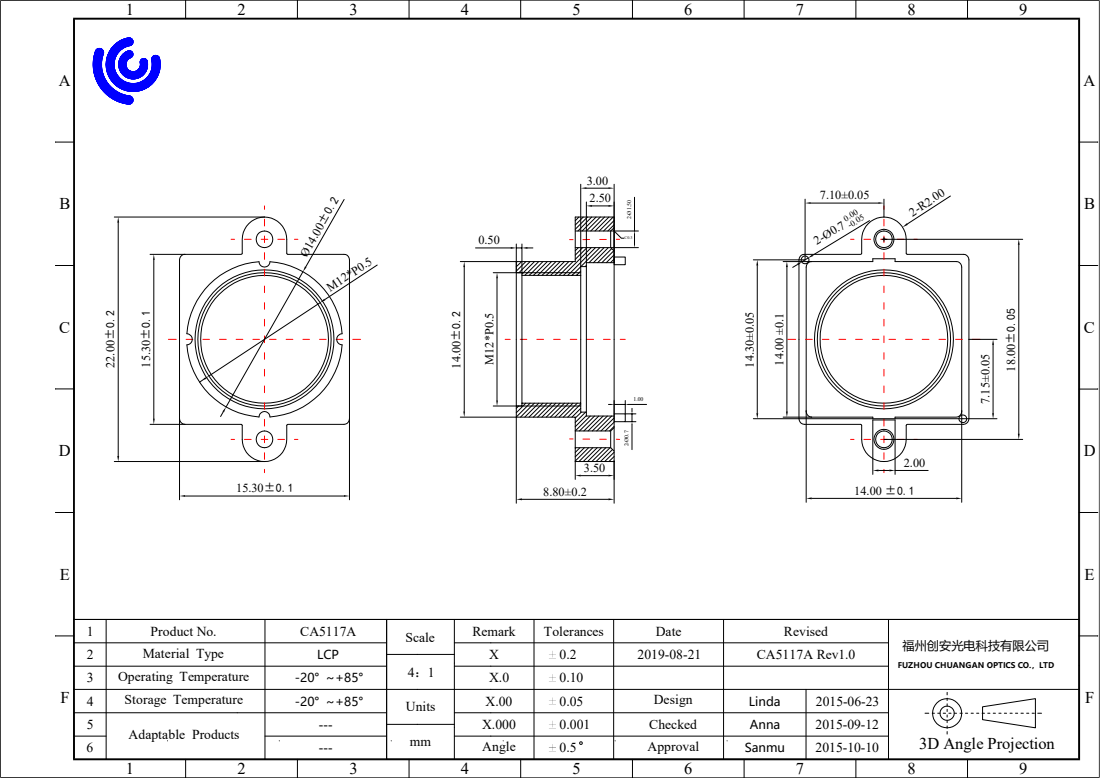
[picture p197: page 1]
M¹²*P⁰.5 14.00±⁰.2; 3D Angle Projection; Material Type; Operating Temperature; Storage Temperature; LCP -20° ~+85° -20° ~+85°; Scale; Units; Remark; Angle; 福州创安光电科技有限公司; Tolerances; Approval; Linda; Sanmu; Adaptable Products; Product No.; Date; Revised

X | 0.2 | 2019-08-21 | CA5117A Rev1.0
X.0 X.00 | 0.10 0.05 | Design

FUZHOU CHUANGAN OPTICS CO.，LTD

X.000 | 0.001 | Checked | Anna | 2015-09-12
