experientials/ziloo/Hardware/201/OV2735-module/holders/ChuangAn M8*0.35 CA5301A.pdf

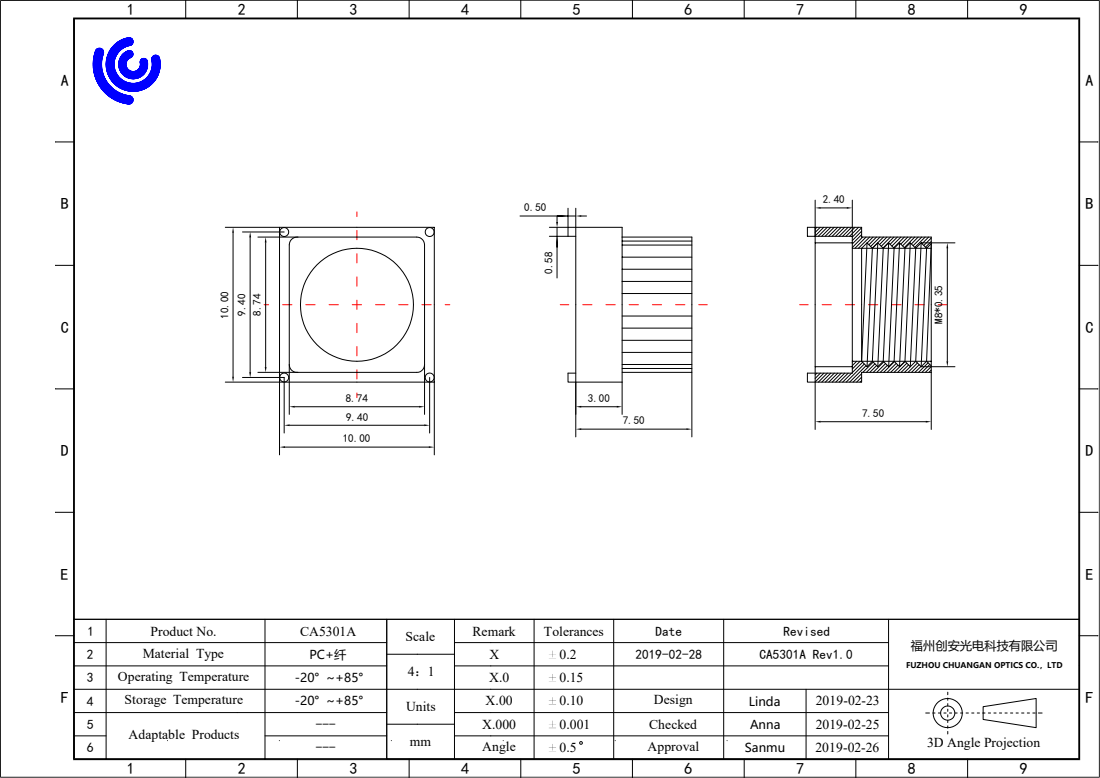
[picture p198: page 1]
Material Type; Operating Temperature; Storage Temperature; Scale; Units; Remark; Angle; Tolerances; Approval; Linda; Sanmu; Adaptable Products; Product No.; 福州创安光电科技有限公司; 3D Angle Projection; Date; Revised

X | 0.2 | 2019-02-28 | CA5301A Rev1.0
X.0 X.00 | 0.15 0.10 | Design

FUZHOU CHUANGAN OPTICS CO.，LTD

X.000 | 0.001 | Checked | Anna | 2019-02-25
