experientials/ziloo/Hardware/201/OV2735-module/holders/ChuangAn M8*0.5 CA5303A.pdf

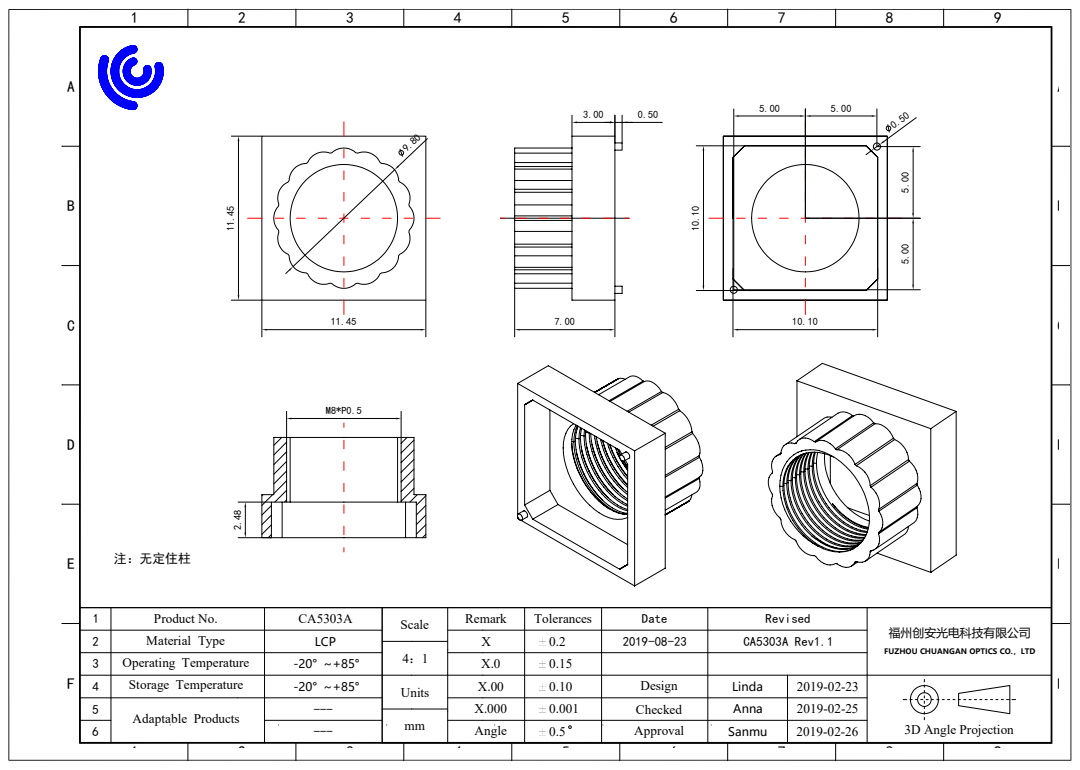
[picture p199: page 1]
Material Type; Operating Temperature; Storage Temperature; LCP -20° ~+85° -20° ~+85°; Scale; Units; Remark; Angle; Tolerances; Approval; Linda; Sanmu; Adaptable Products; Product No.; 注：无定住柱; Date; Revised; 3D Angle Projection; 福州创安光电科技有限公司

X | | 2019-08-23 | CA5303A Rev1.1
X.0 X.00 | Design

FUZHOU CHUANGAN OPTICS CO.，LTD

X.000 | | Checked | Anna | 2019-02-25
