experientials/ziloo/Hardware/201/OV2735-module/lenses/TY-6046-C1-MM-spec Model.pdf

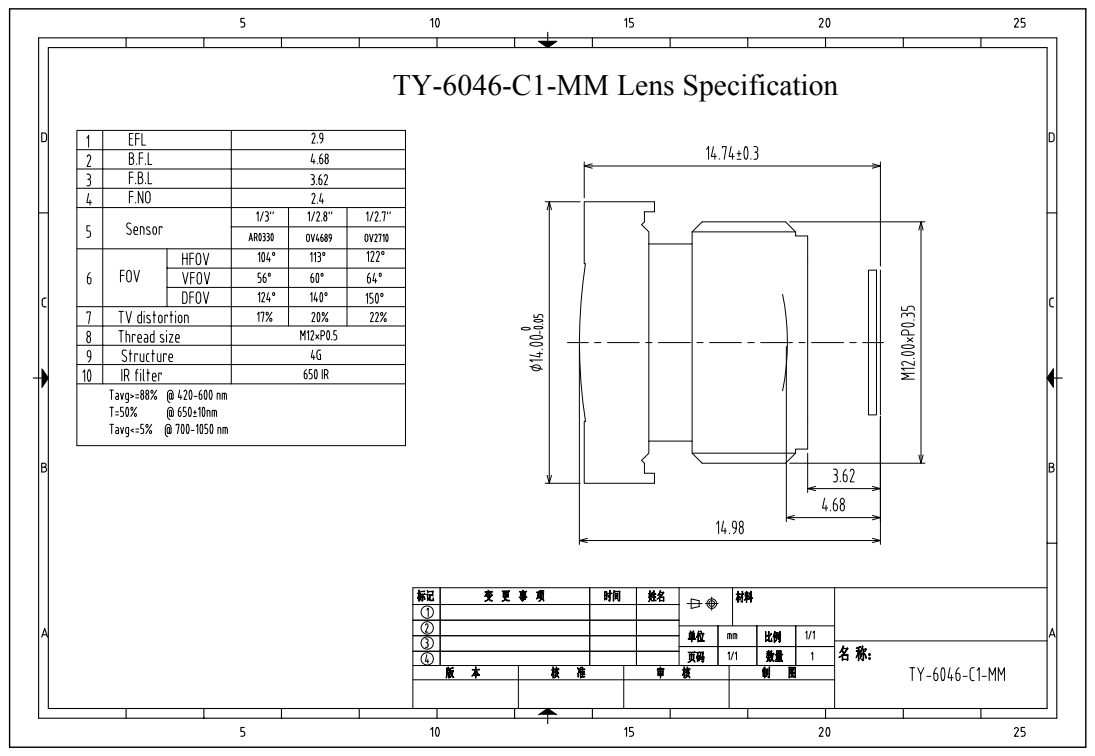
[picture p200: page 1]

TY-6046-C1-MM Lens Specification
