experientials/ziloo/Hardware/201/OV2735-module/lenses/TY-6046-D1-MM-spec Model.pdf

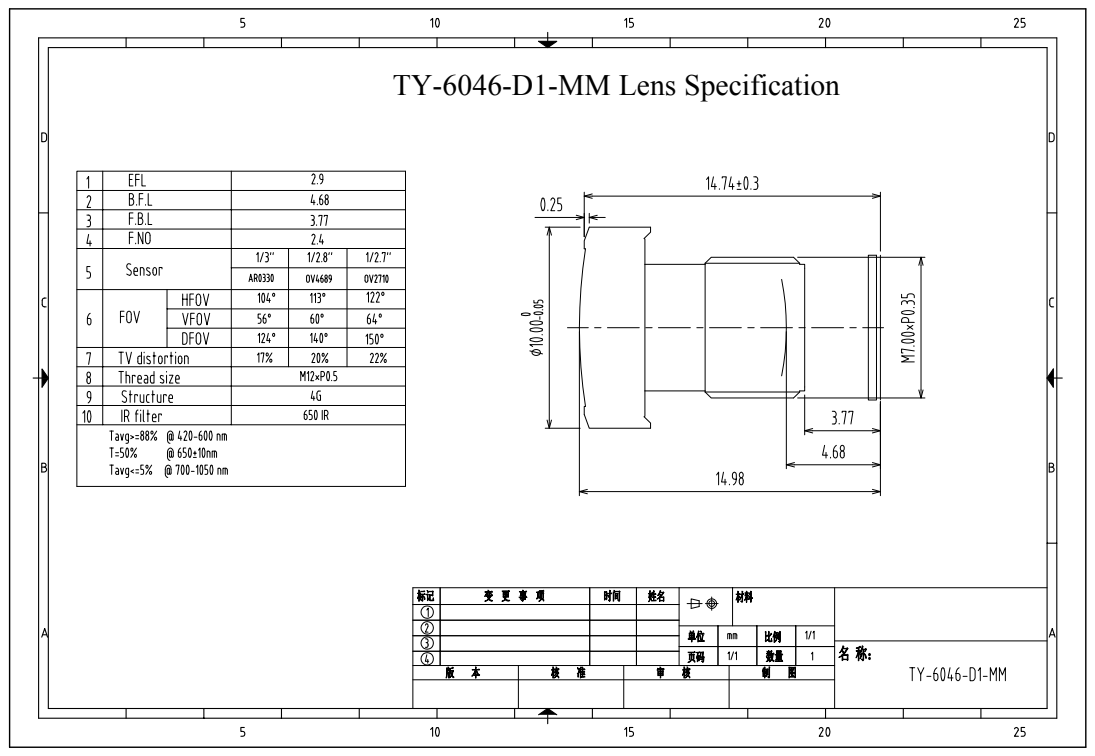
[picture p201: page 1]

TY-6046-D1-MM Lens Specification
