experientials/ziloo/Hardware/909c/Drawing_Ziloo_Bridge_909b.pdf

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

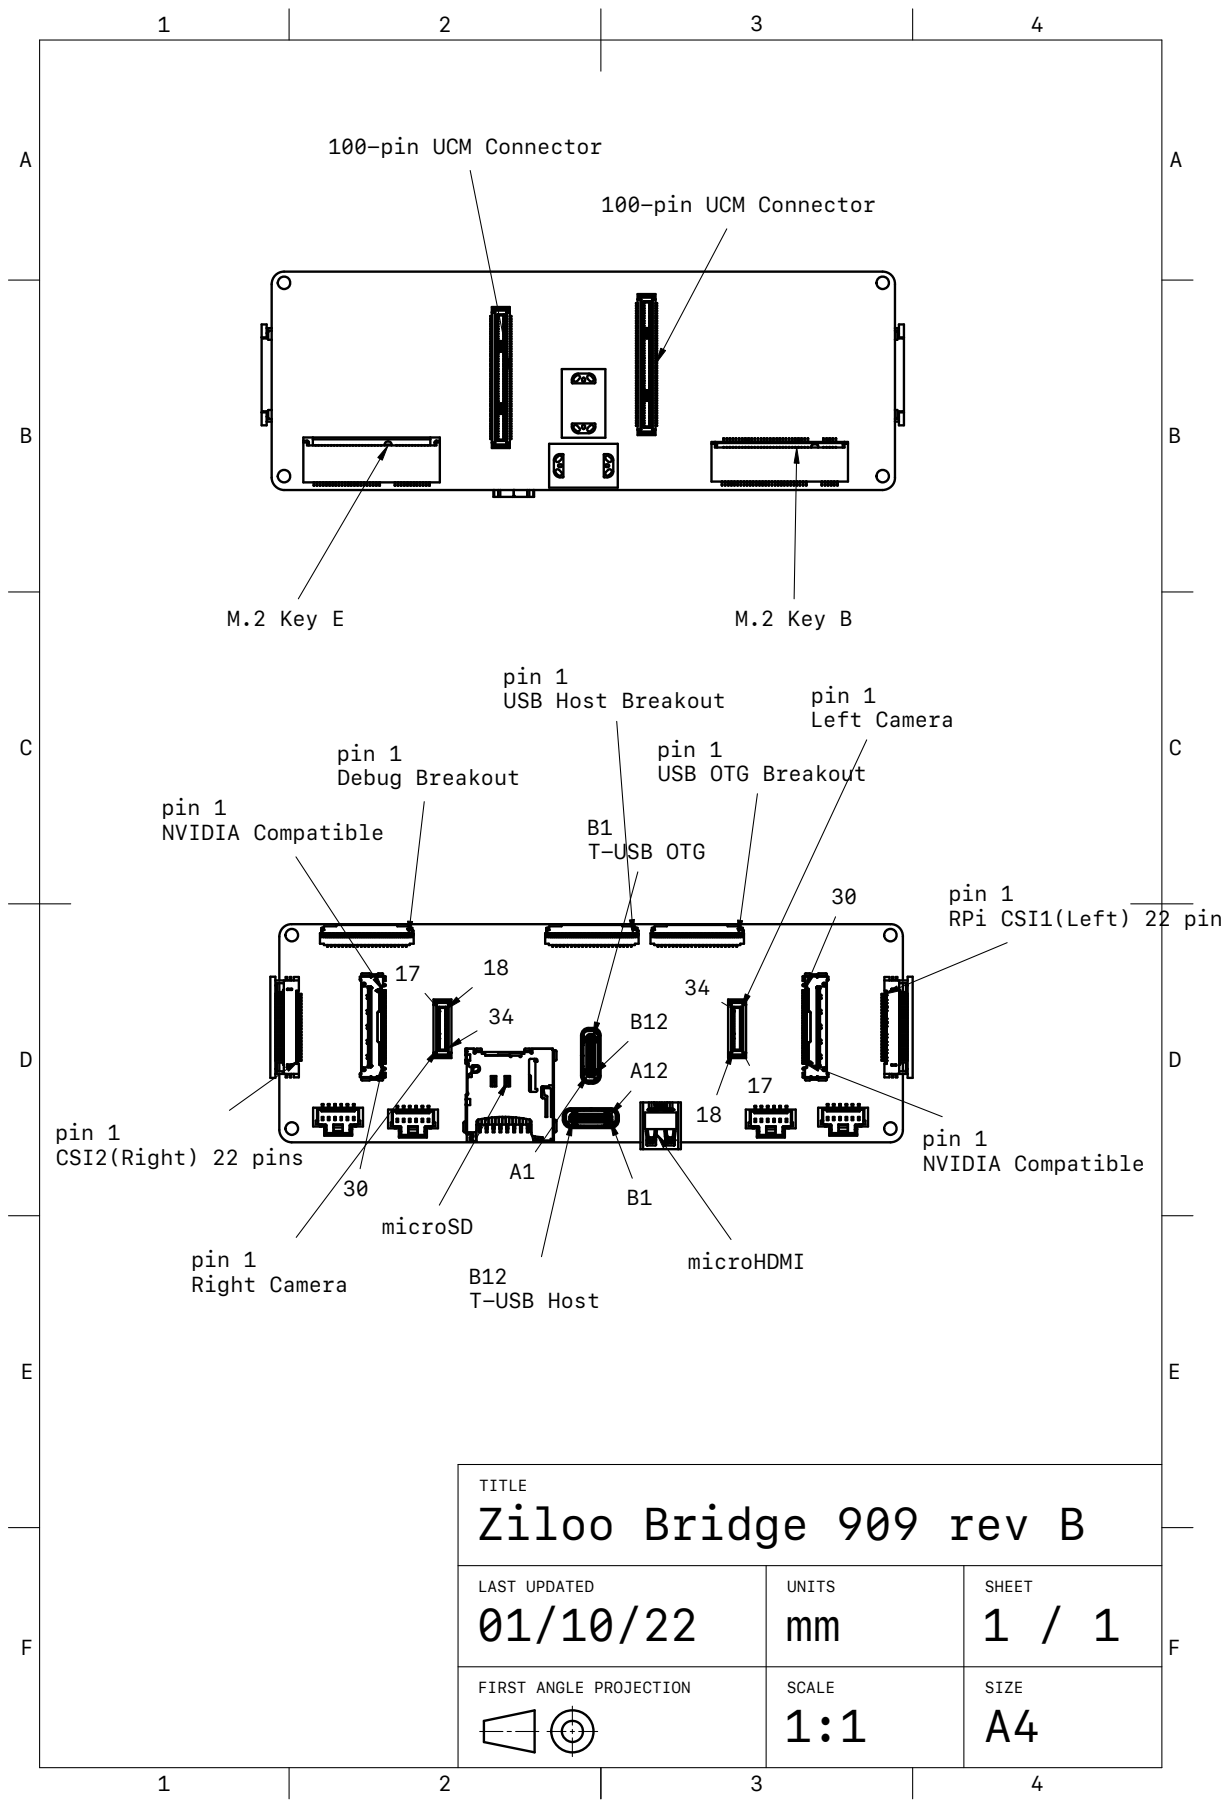
[picture p204: page 1]
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
