experientials/ziloo/Hardware/909/Drawing_Ziloo_Bridge_909.pdf

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

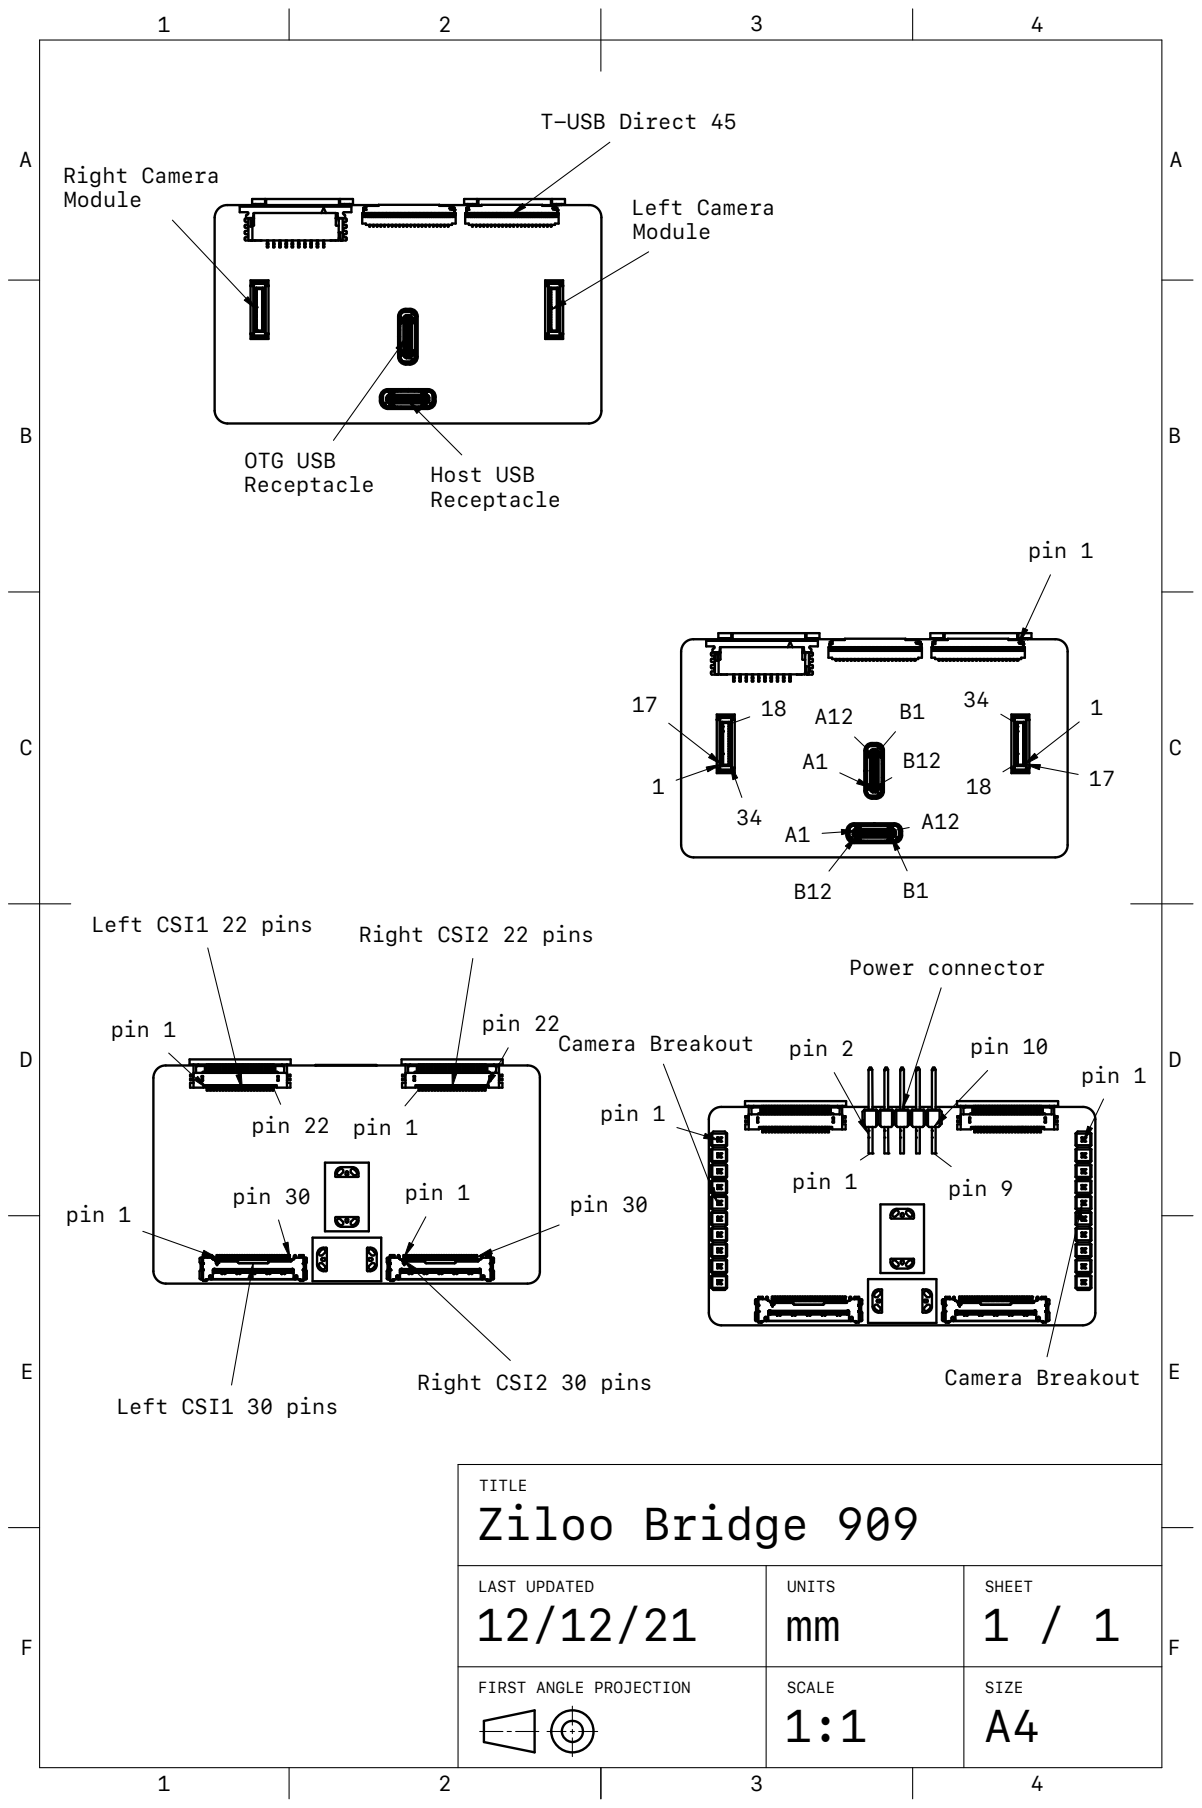
[picture p205: page 1]
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
