experientials/ziloo/Hardware/201/OV2735-combined-module/Ziloo v2 camera module mounting.pdf

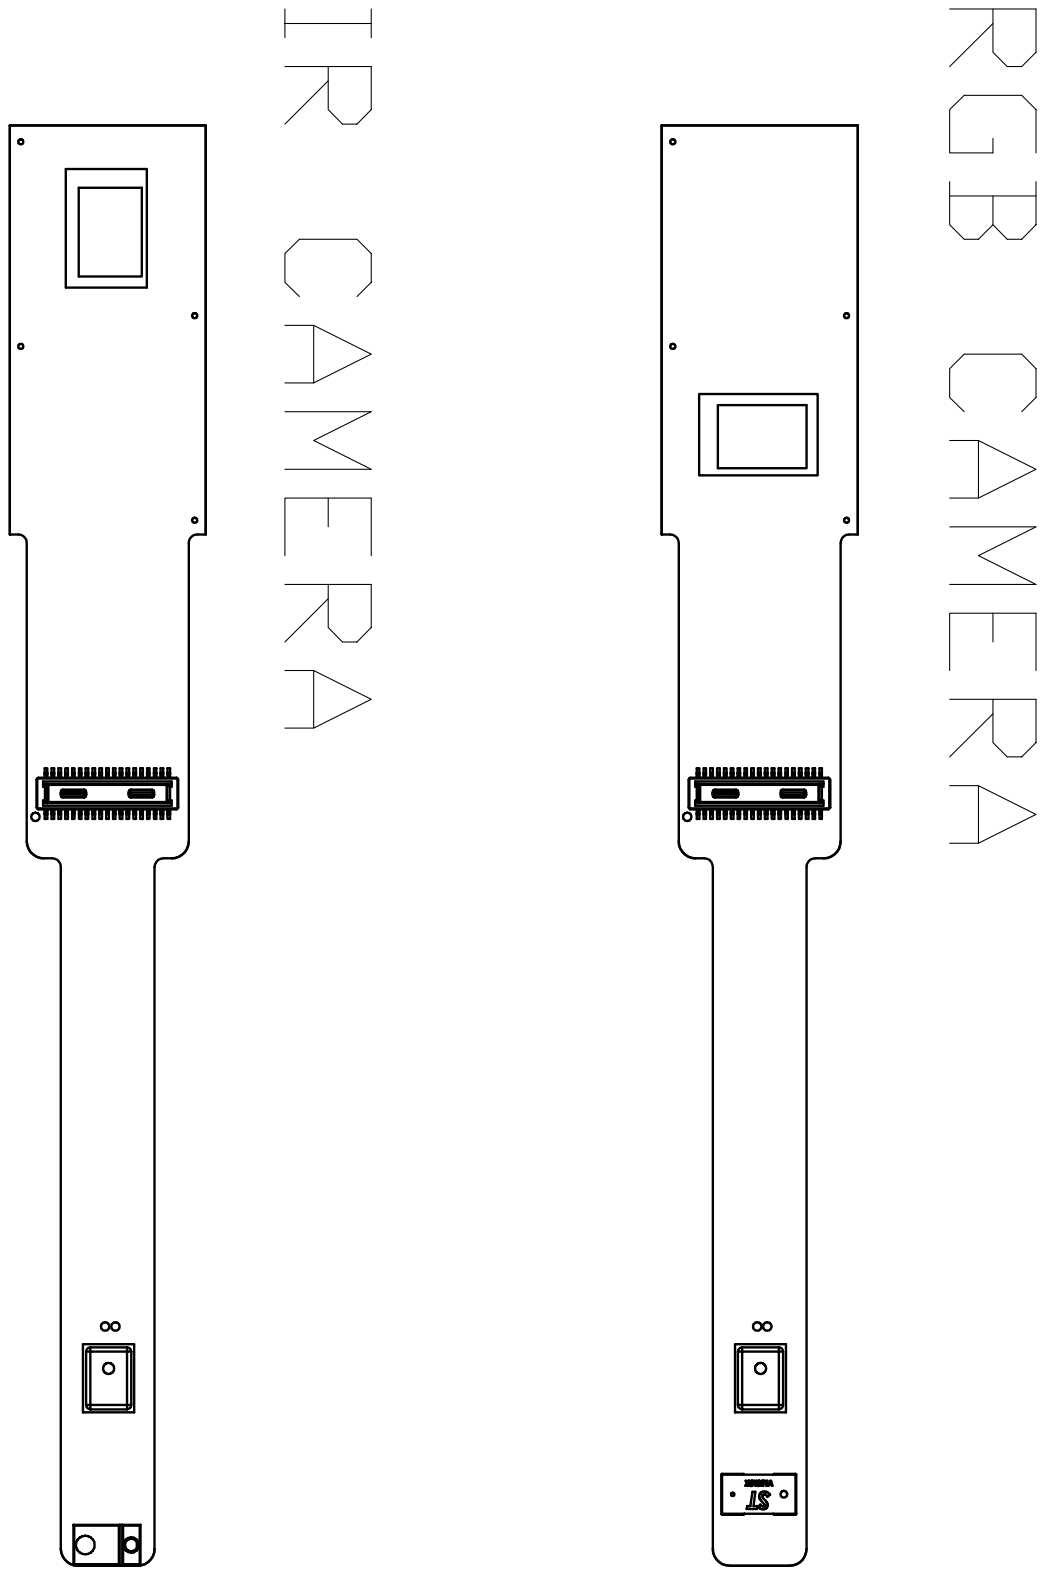
[picture p206: page 1]
