experientials/ziloo/Hardware/201/OV2735-module/Ziloo 201 camera modules 211108.pdf

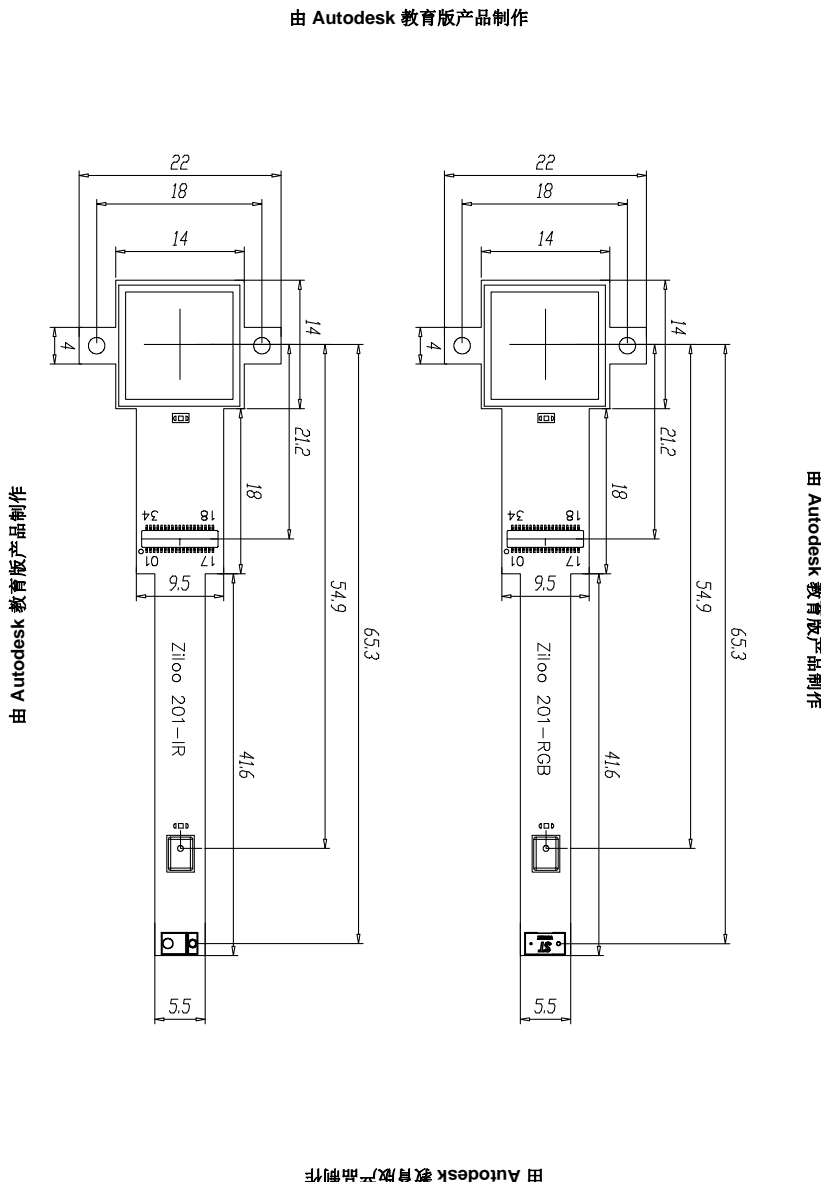
[picture p208: page 1]
由 Autodesk 教育版产品制作; uto; 育版产品制作; A uto
