experientials/ziloo/Hardware/201/OV2735-module/Ziloo v2 camera modules Model from britchcam.pdf

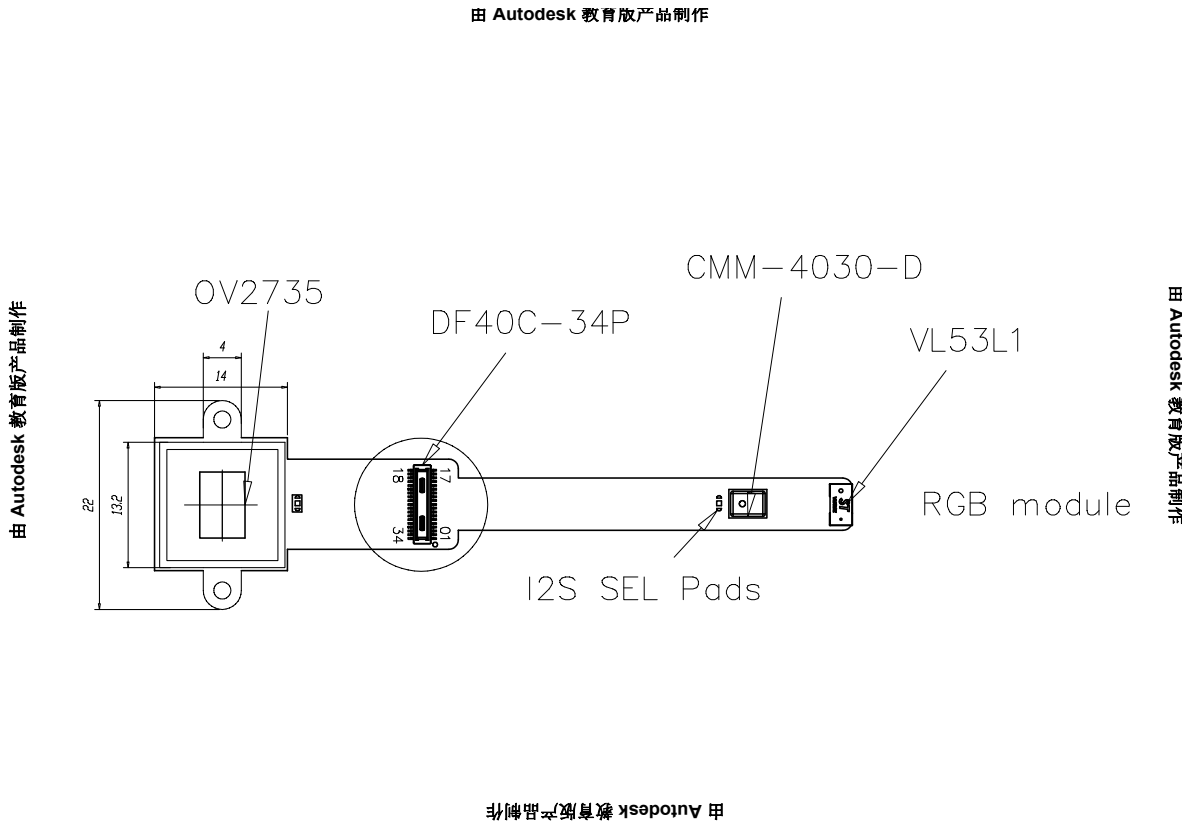
[picture p209: page 1]
育版产品制作; t o d e sk 教 育版产品制作; 由 Autodesk 教育版产品制作
