experientials/ziloo/Hardware/Power/v1/Bottom_board_V1.pdf

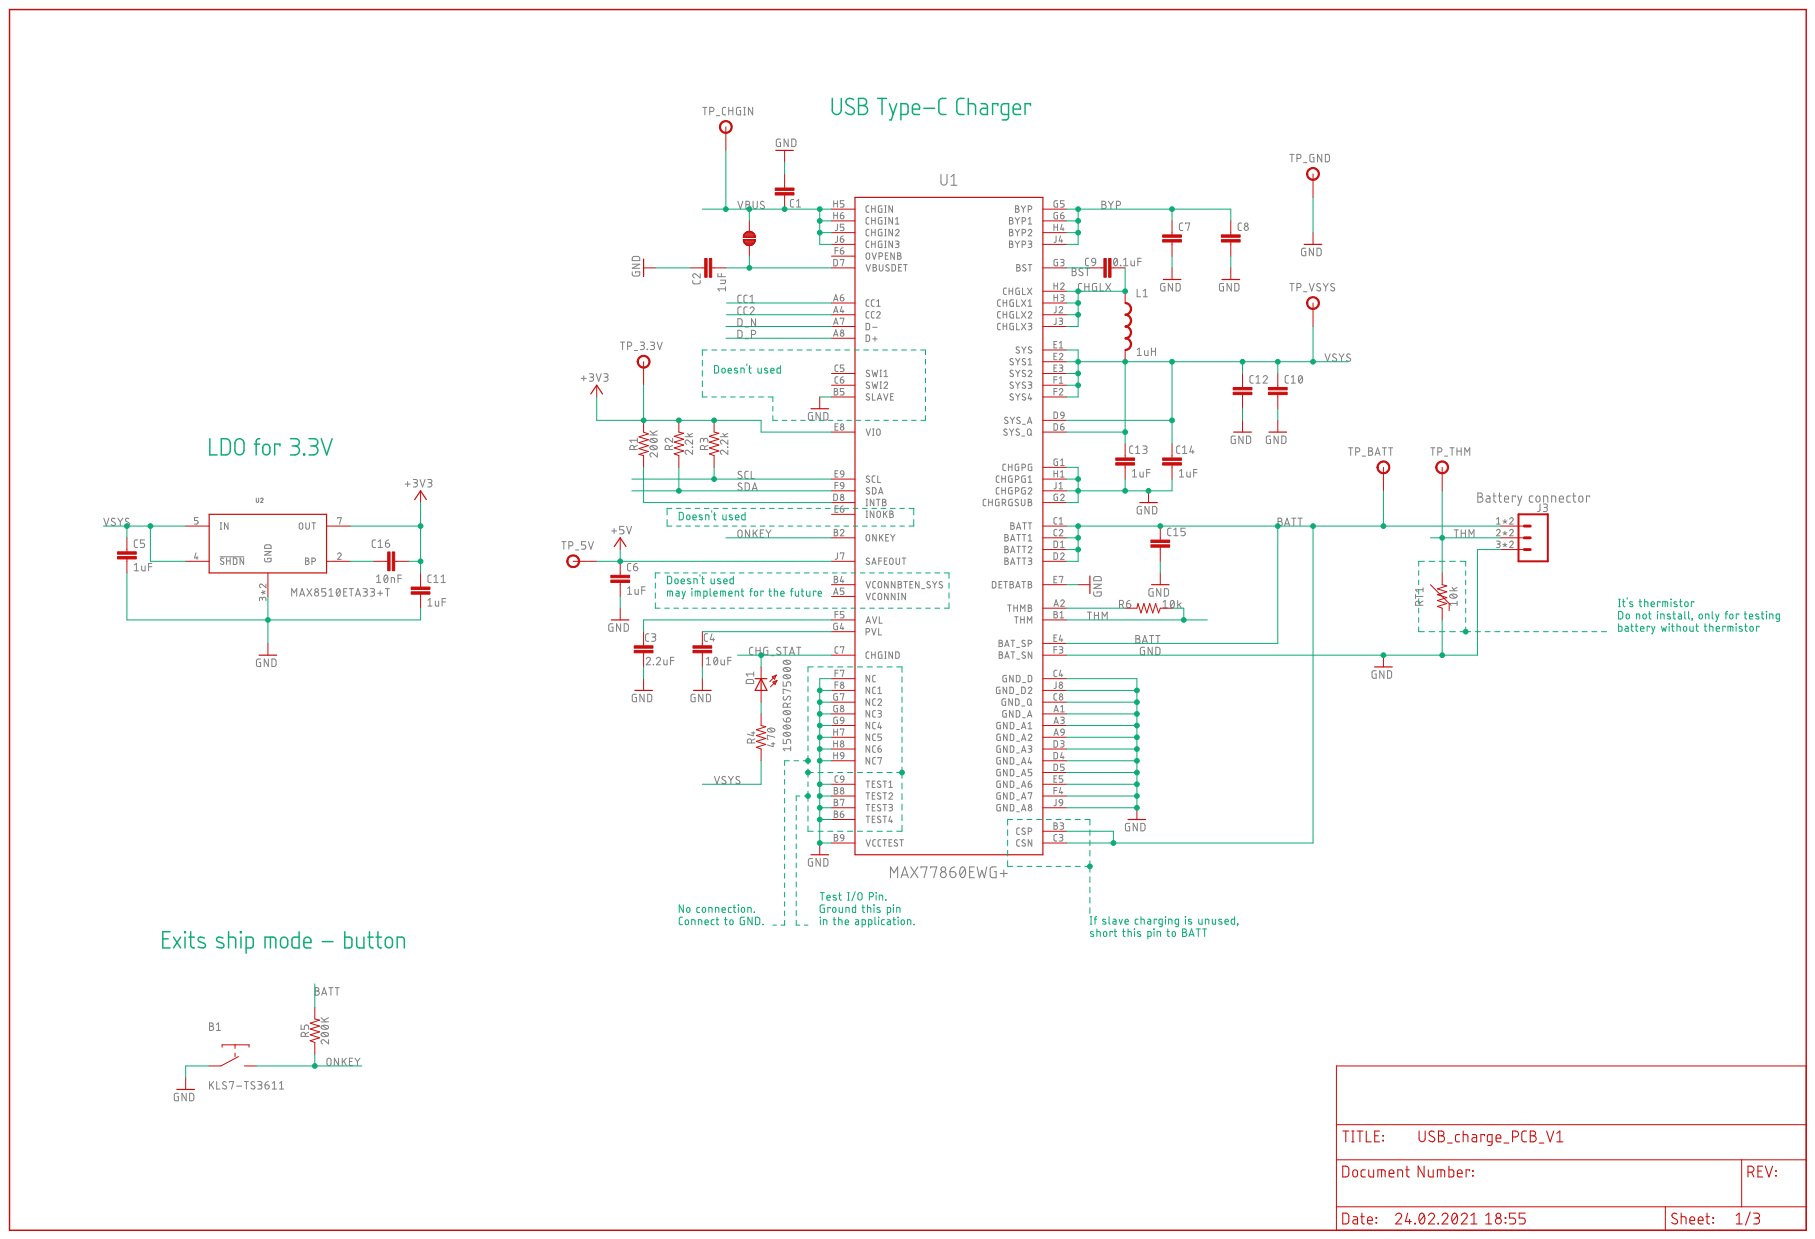
[picture p210: page 1]

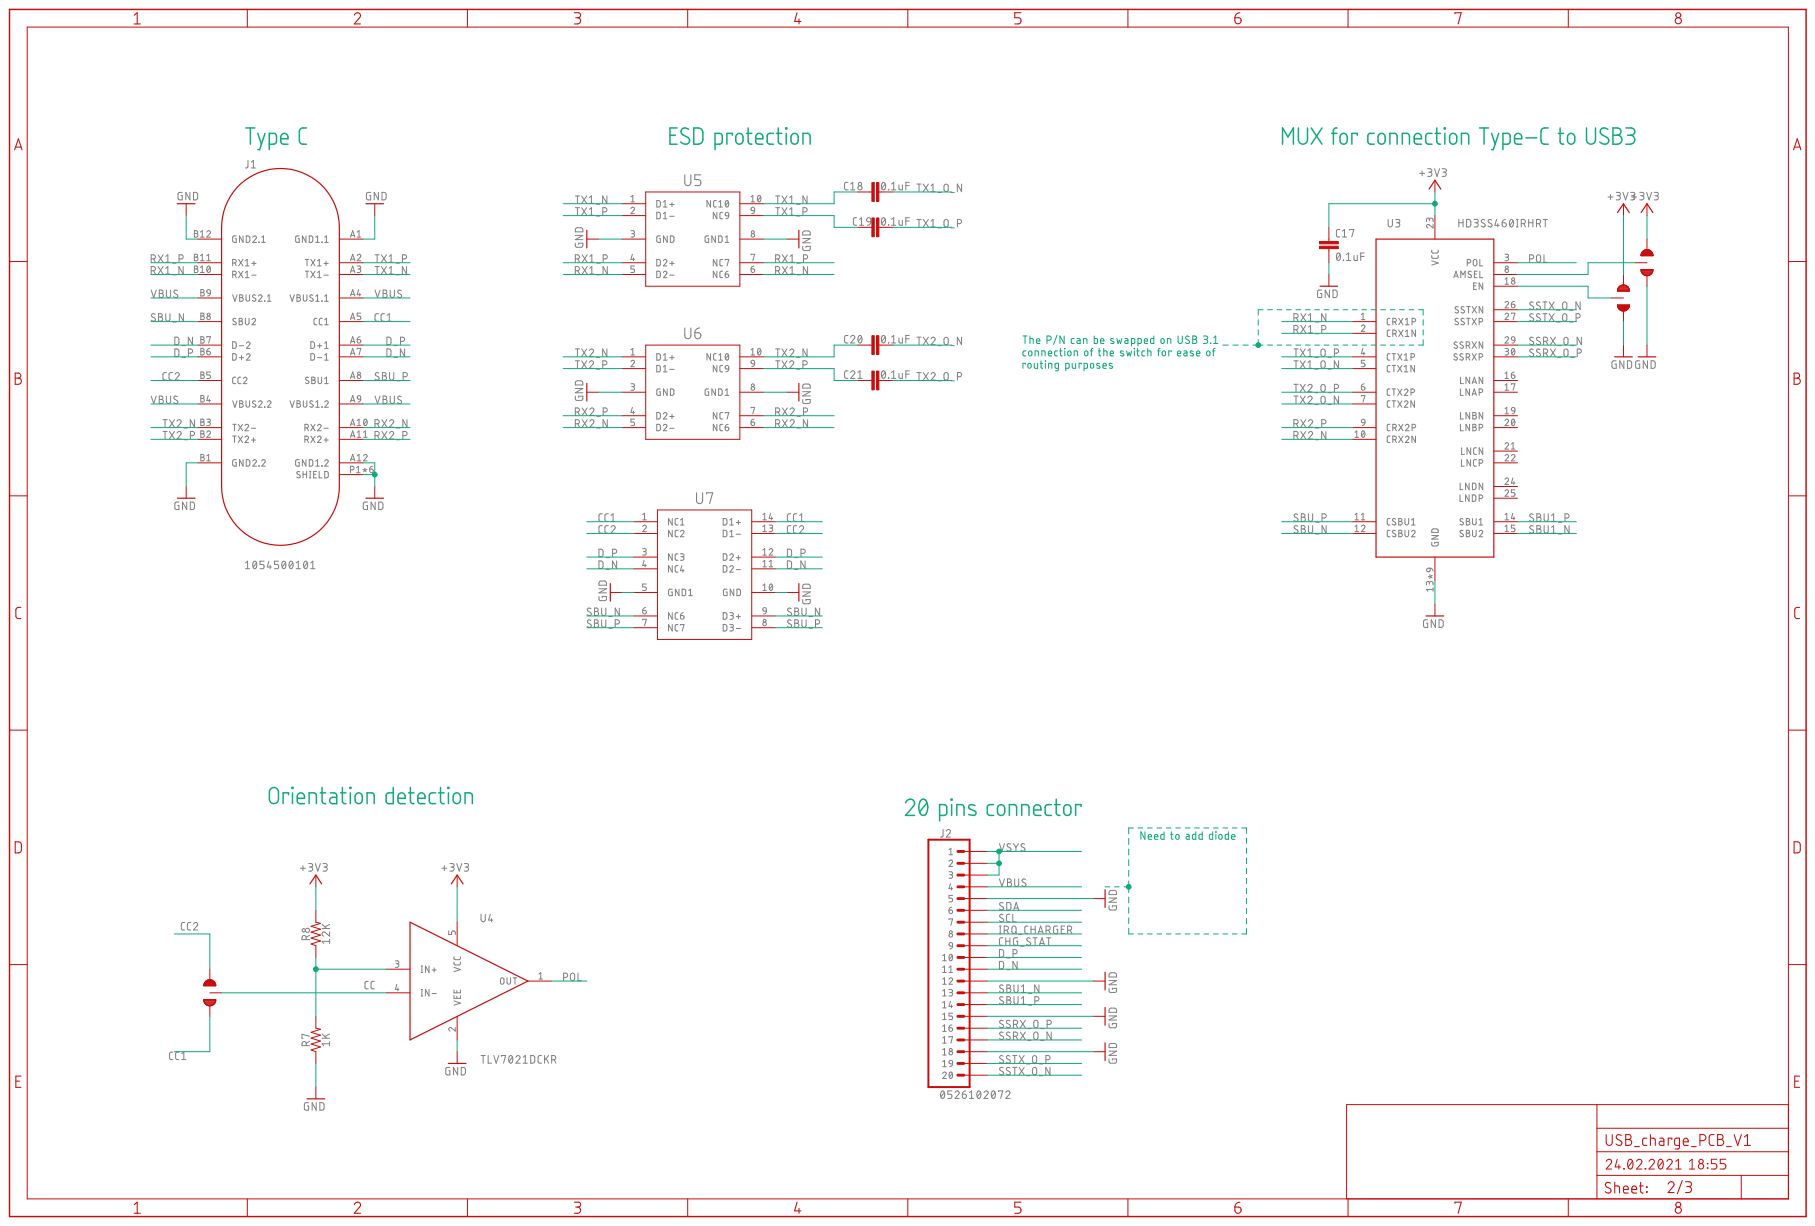
[picture p211: page 2]

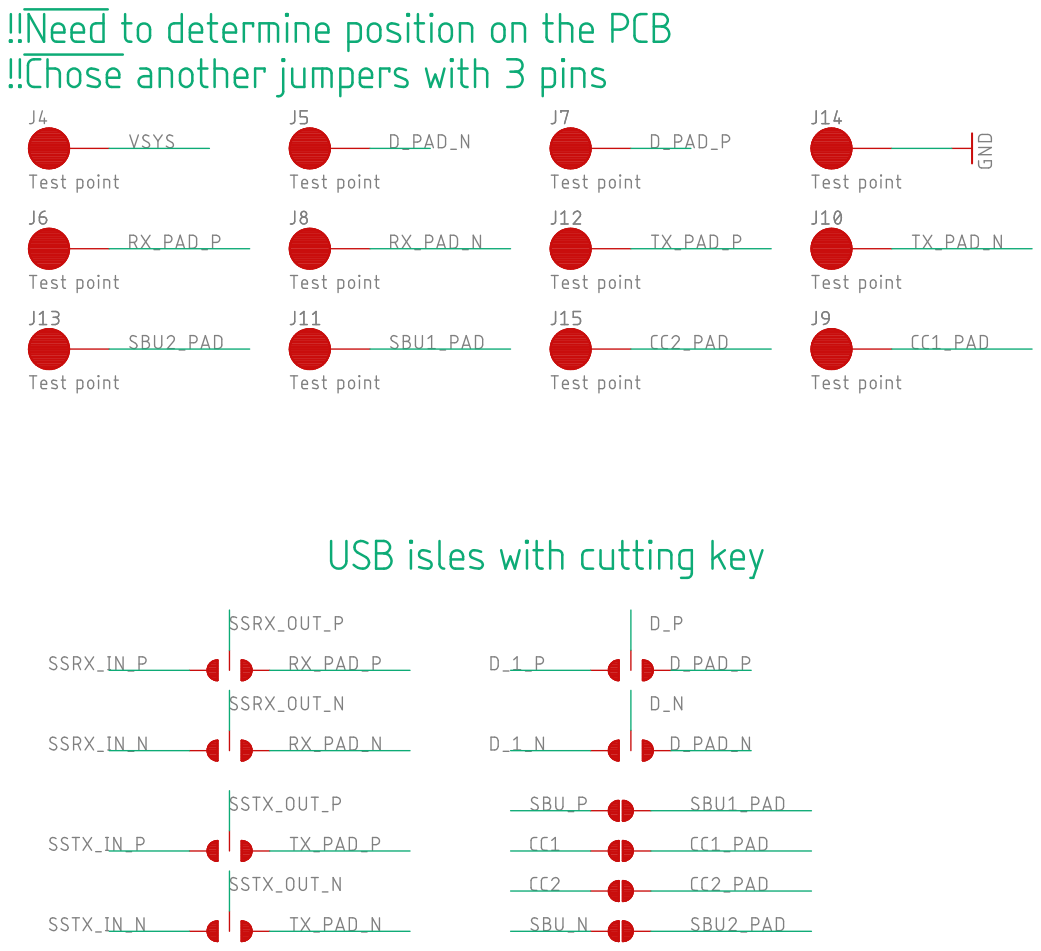
[picture p212: page 3]
