experientials/ziloo/Hardware/Power/Power_module_PCB_files/02_SCHEMATIC/USB_charge_PCB_V1.pdf

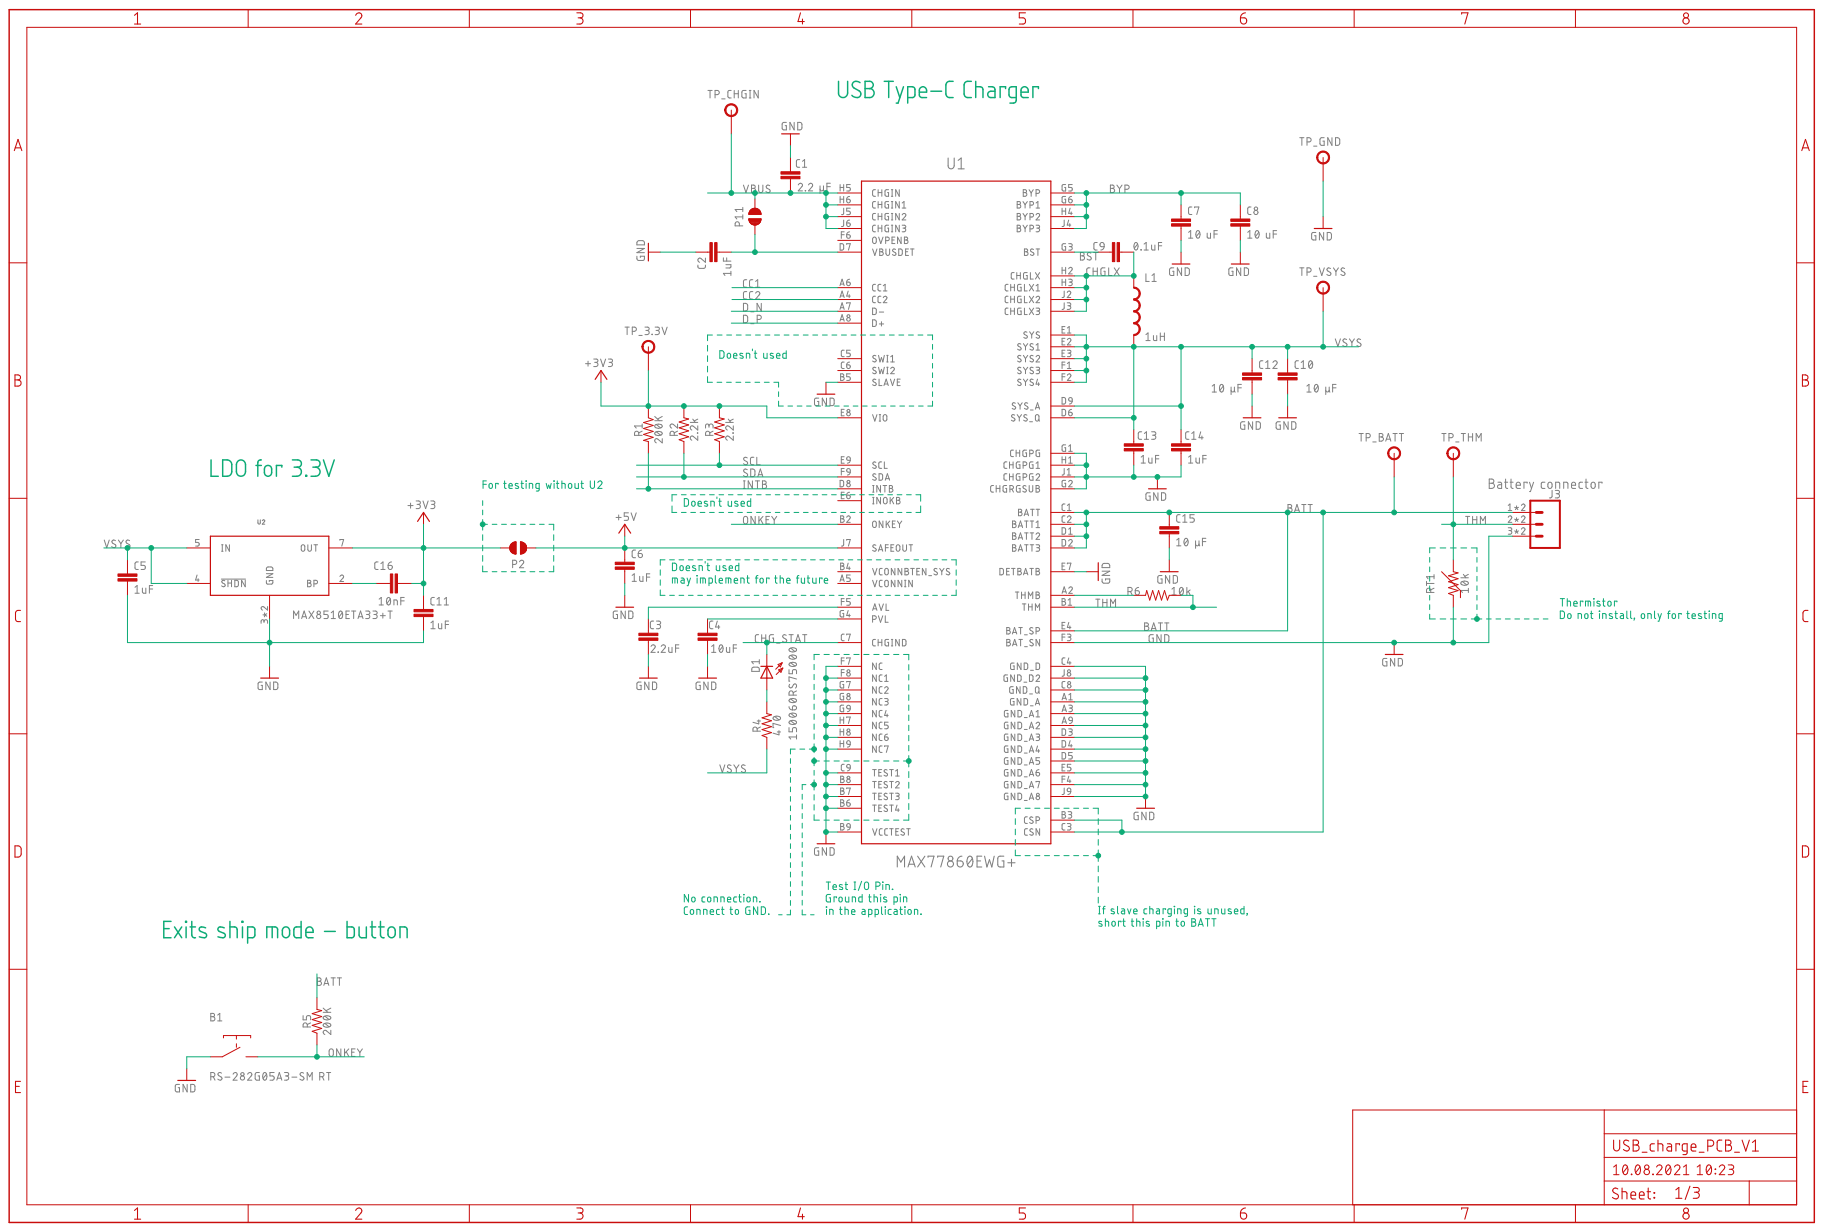
[picture p213: page 1]

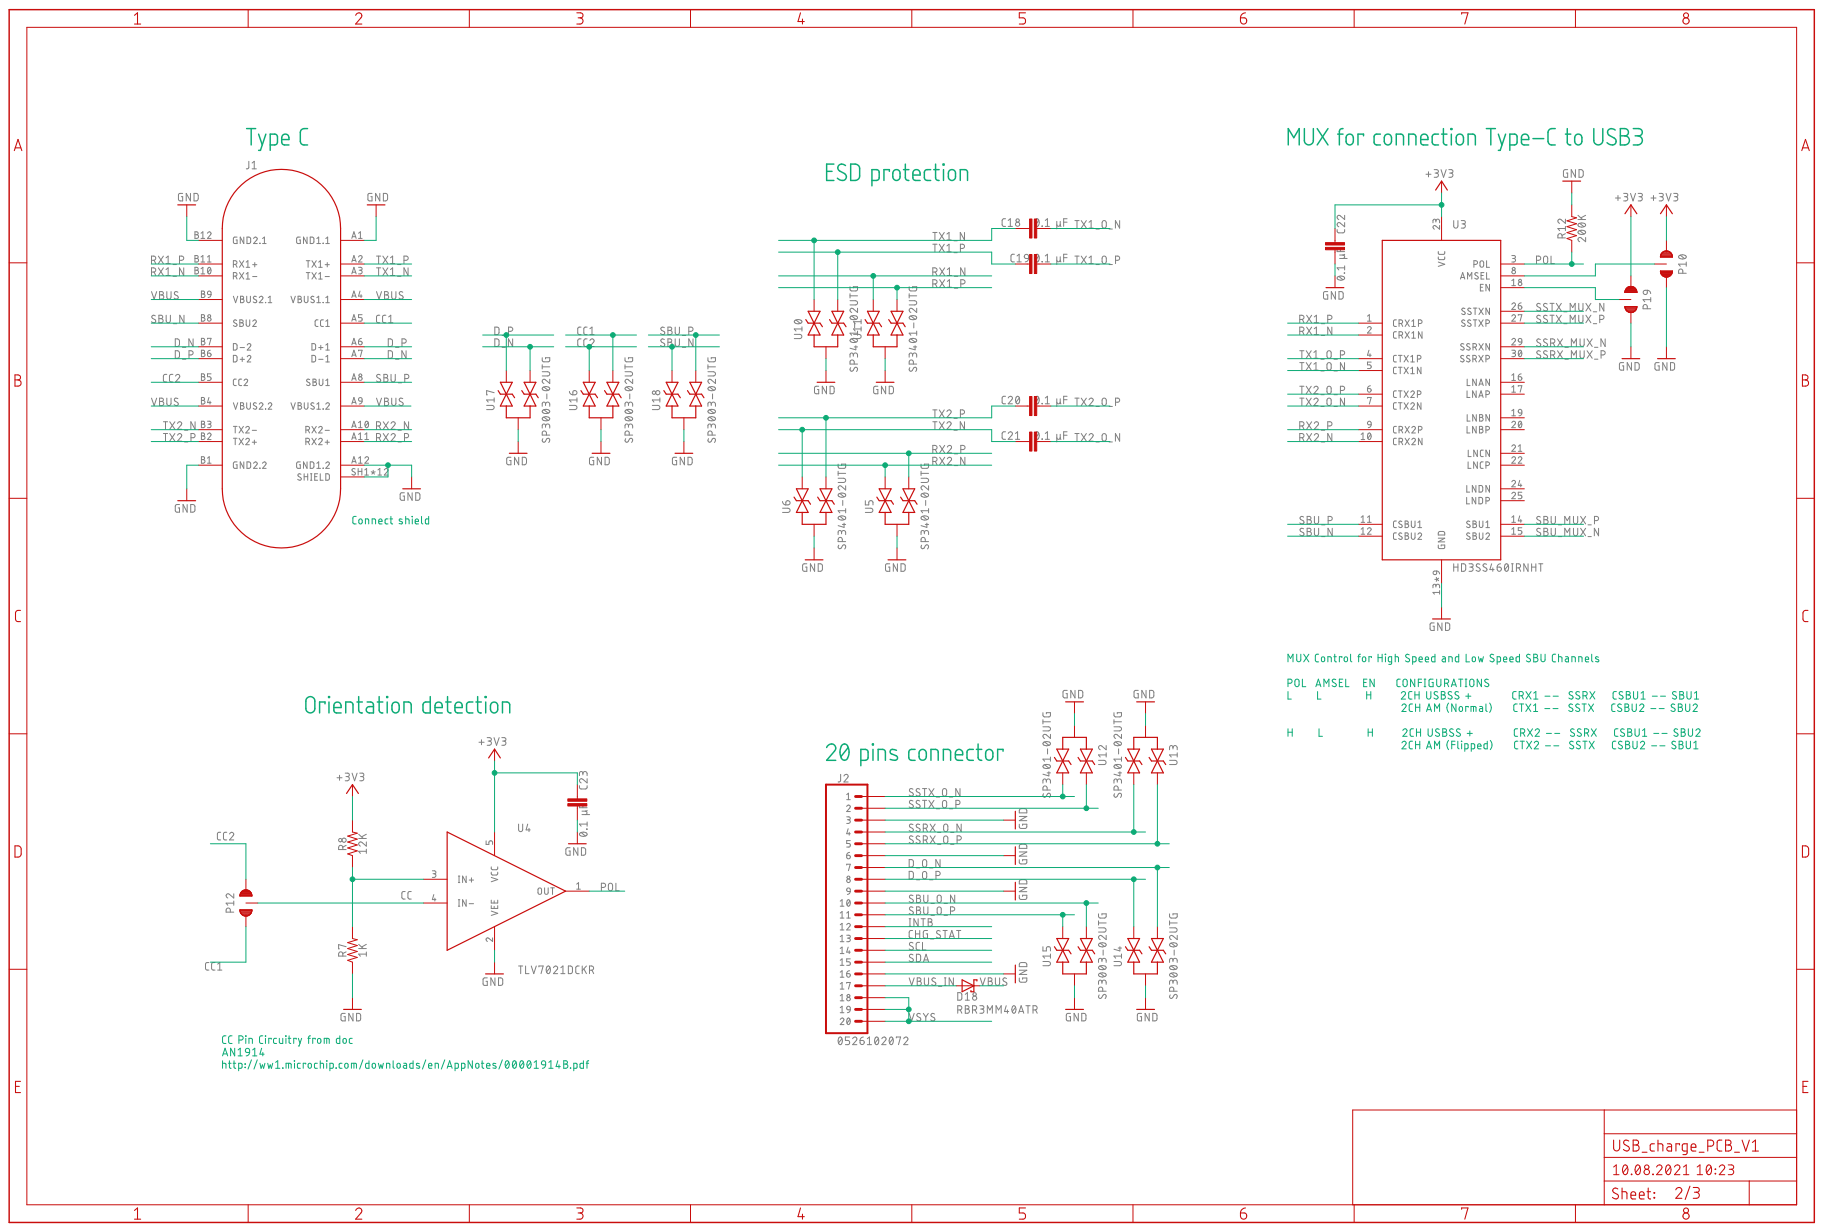
[picture p214: page 2]

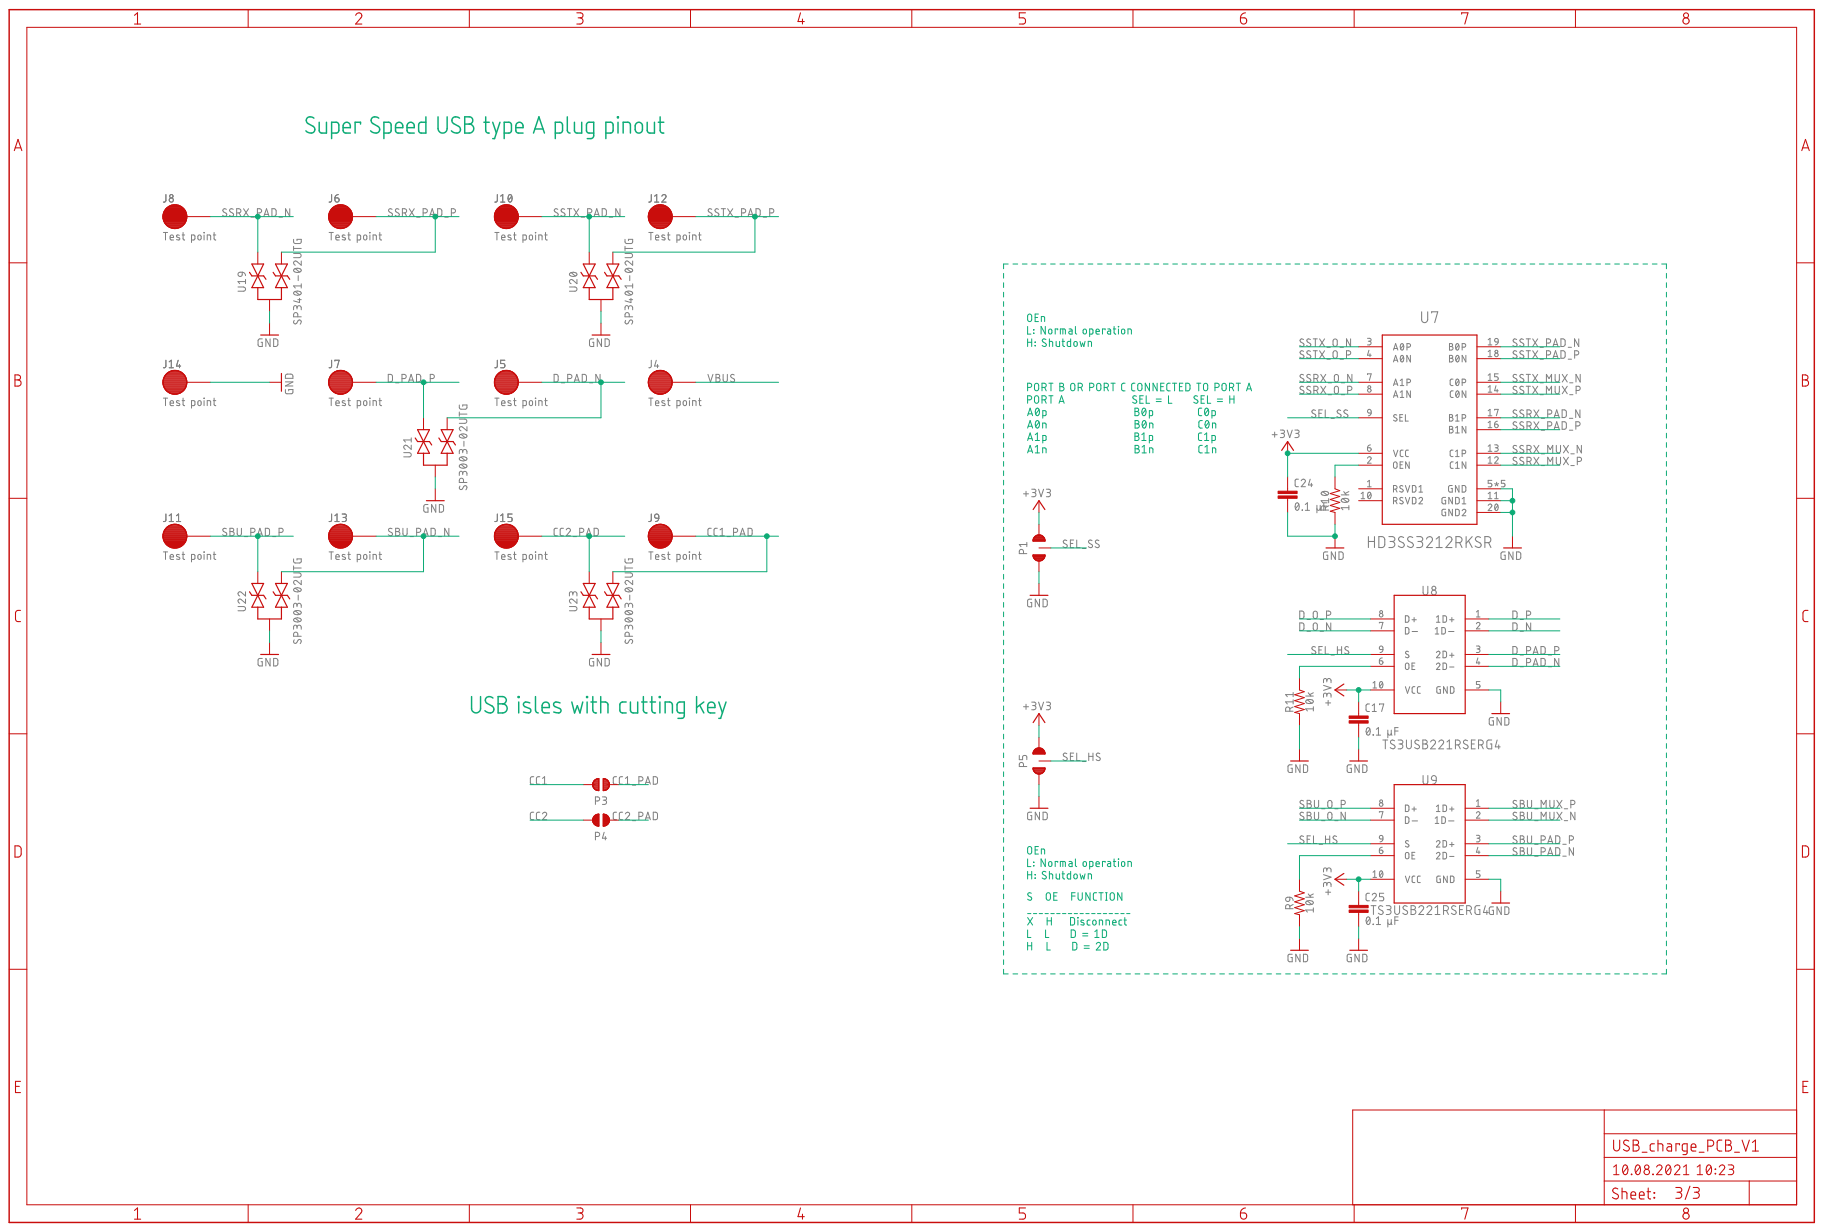
[picture p215: page 3]
