experientials/ziloo/Hardware/Power/Power_module_PCB_files/07_ASSEMBLY DRAWINGS/USB_charge_PCB_V1_top.pdf

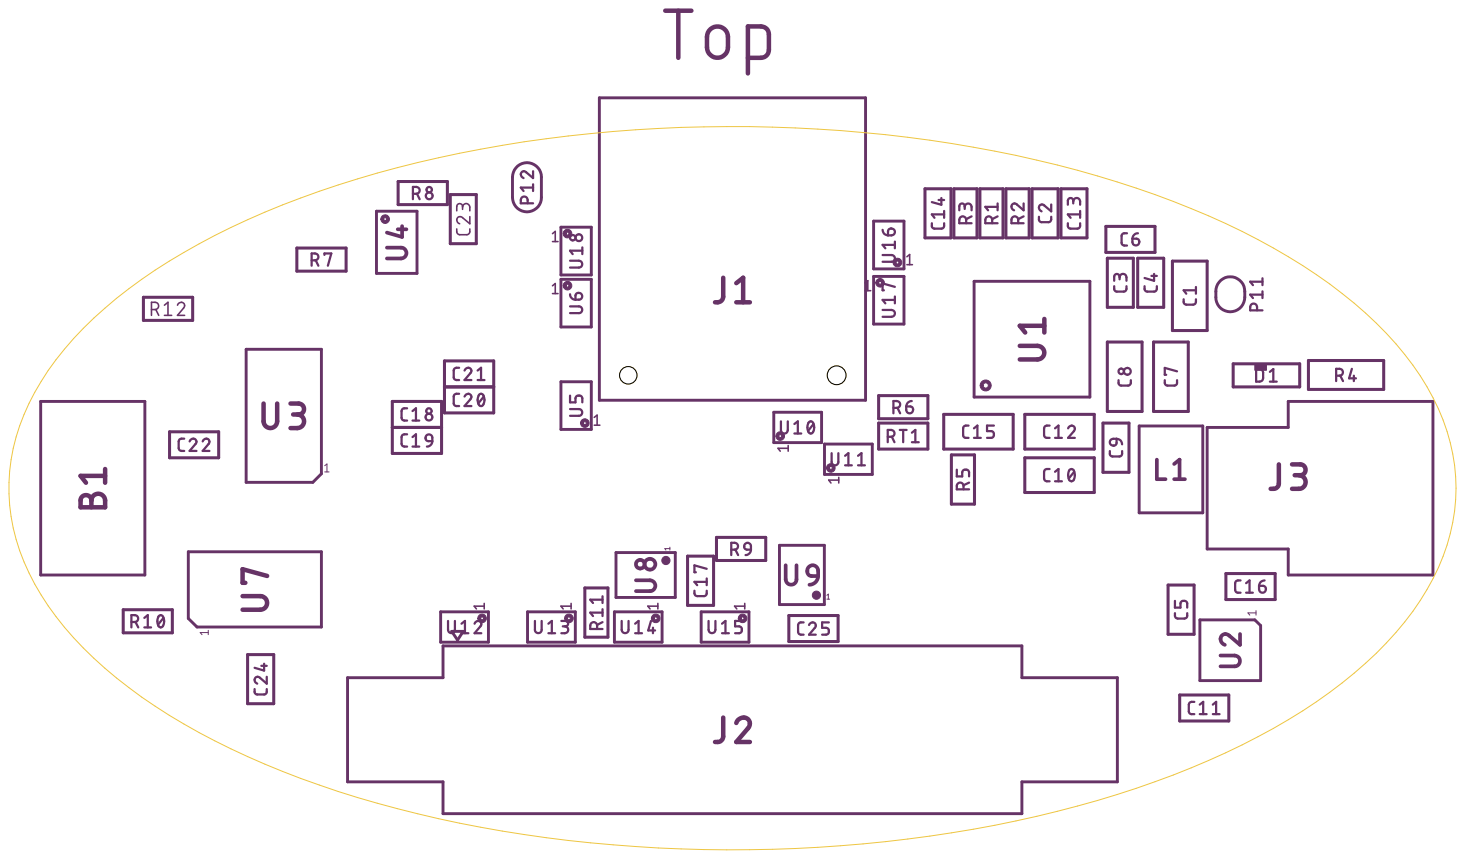
[picture p217: page 1]
