experientials/ziloo/Hardware/201/OV2735-module/holders/JSD HA1313_A115P18-052(FD-HD05).pdf

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

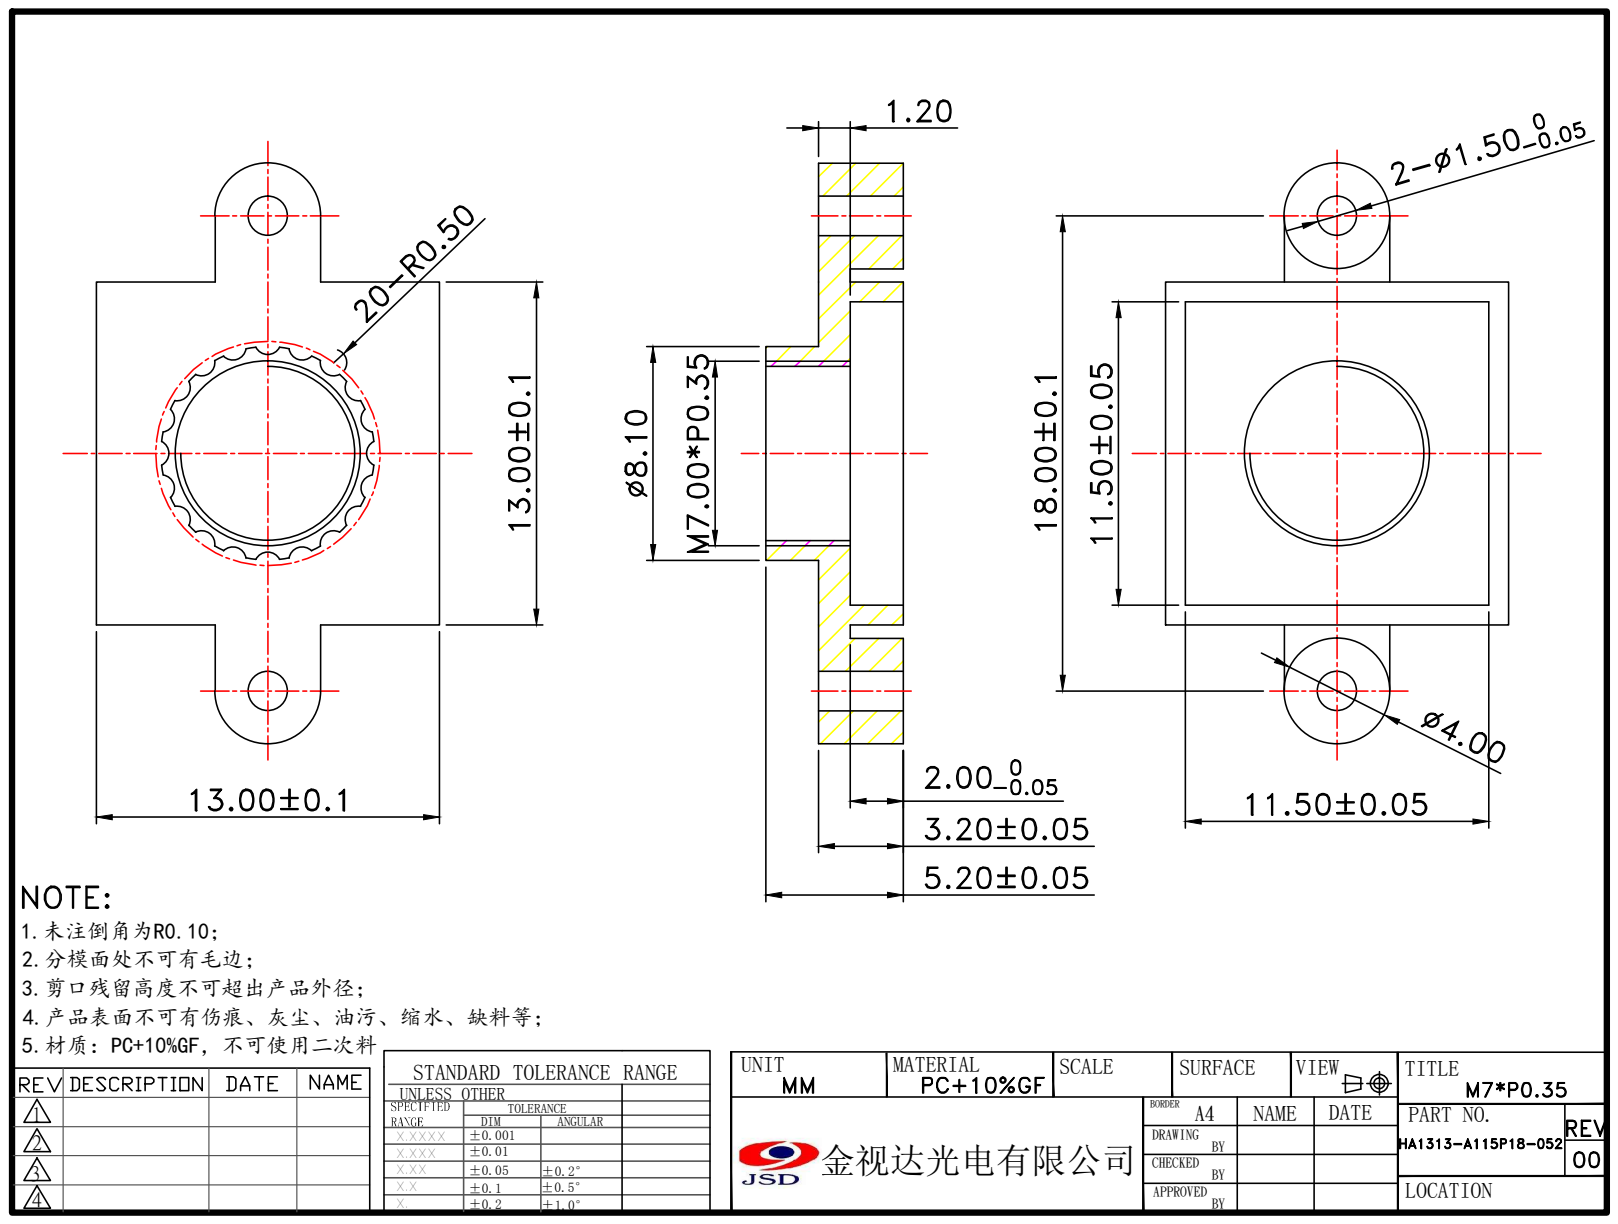
[picture p218: page 1]
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
