experientials/ziloo/Hardware/201/OV2735-module/lenses/50307A Lens Datesheet.pdf

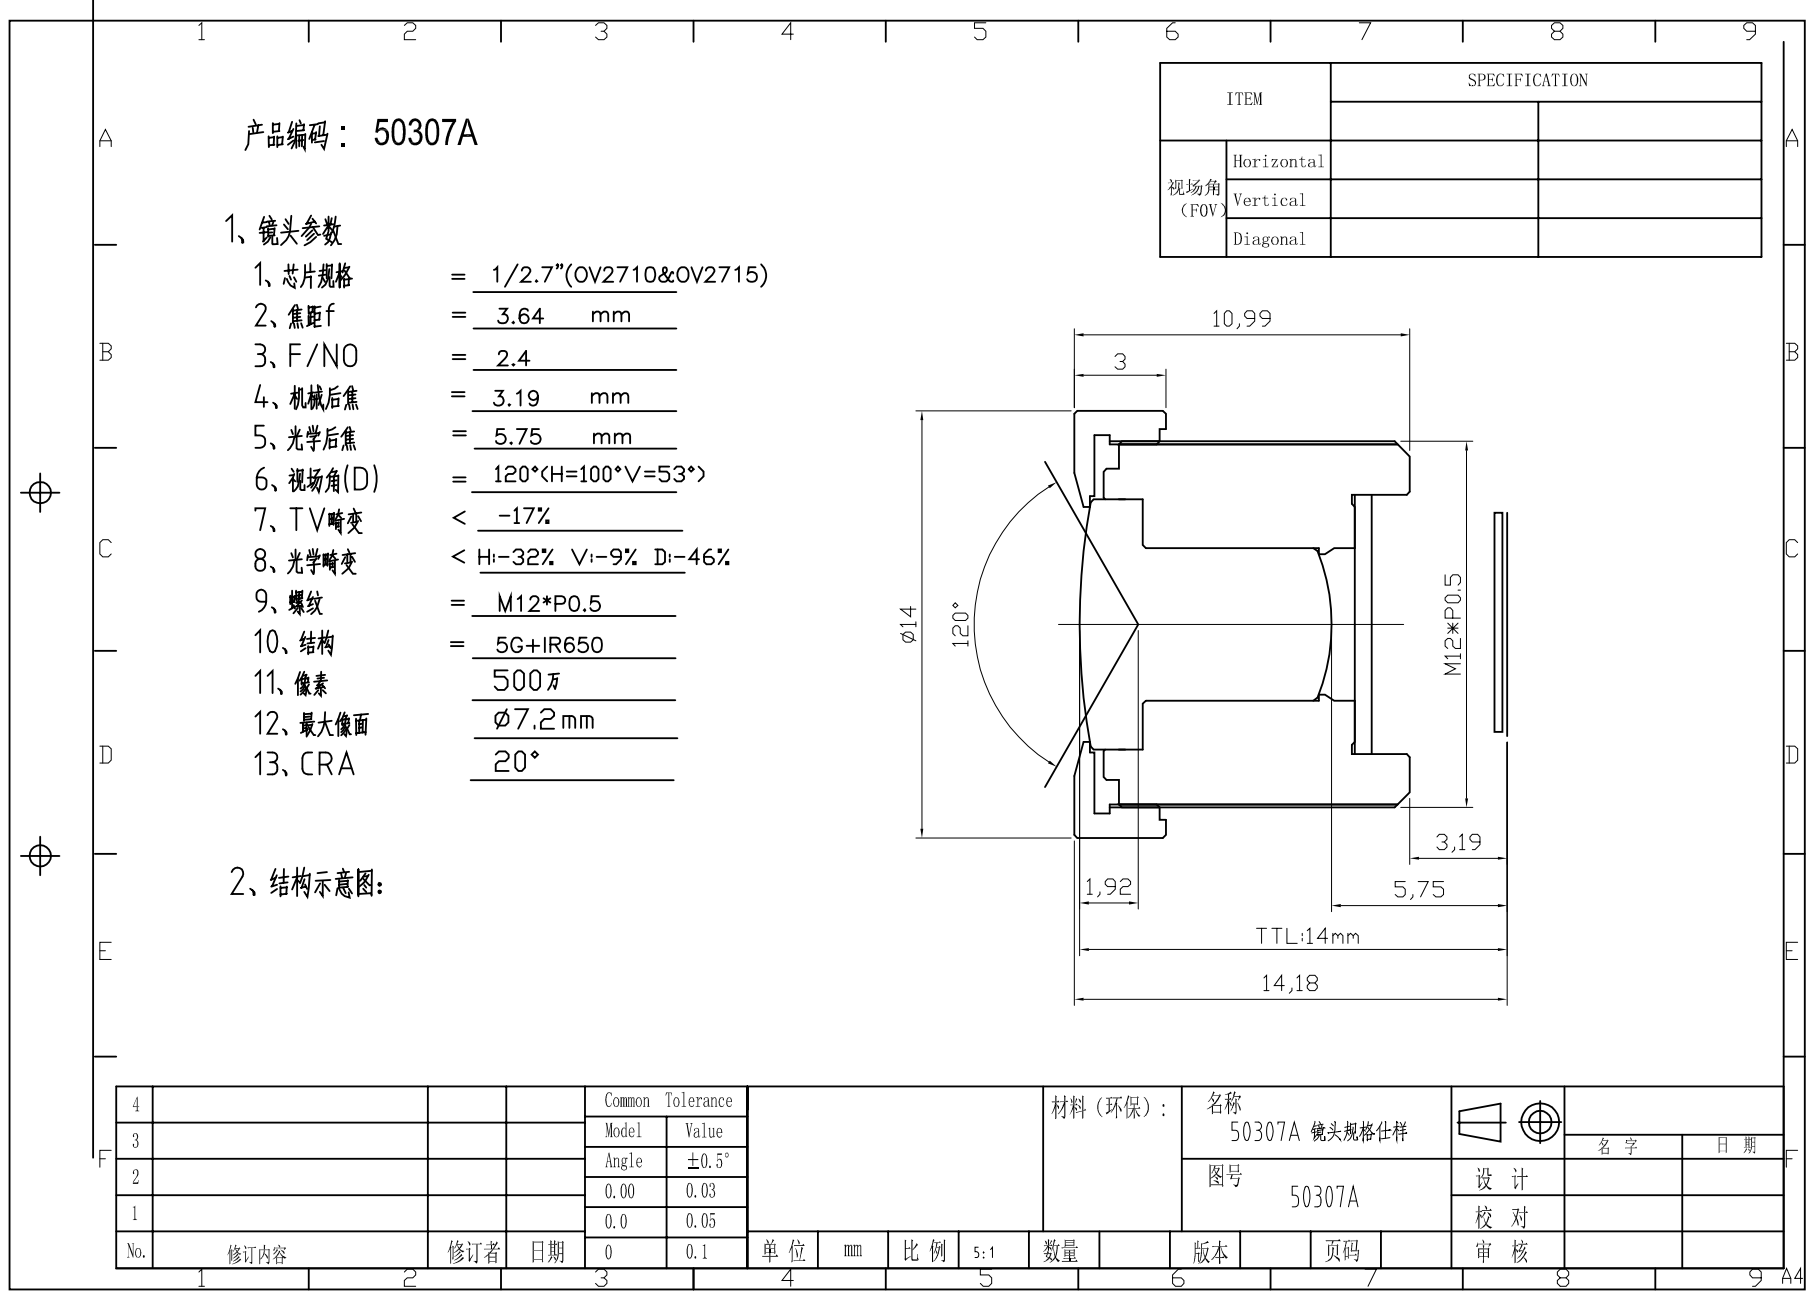
[picture p219: page 1]
