experientials/ziloo/Hardware/201/OV2735-module/lenses/50307C Lens Datesheet.pdf

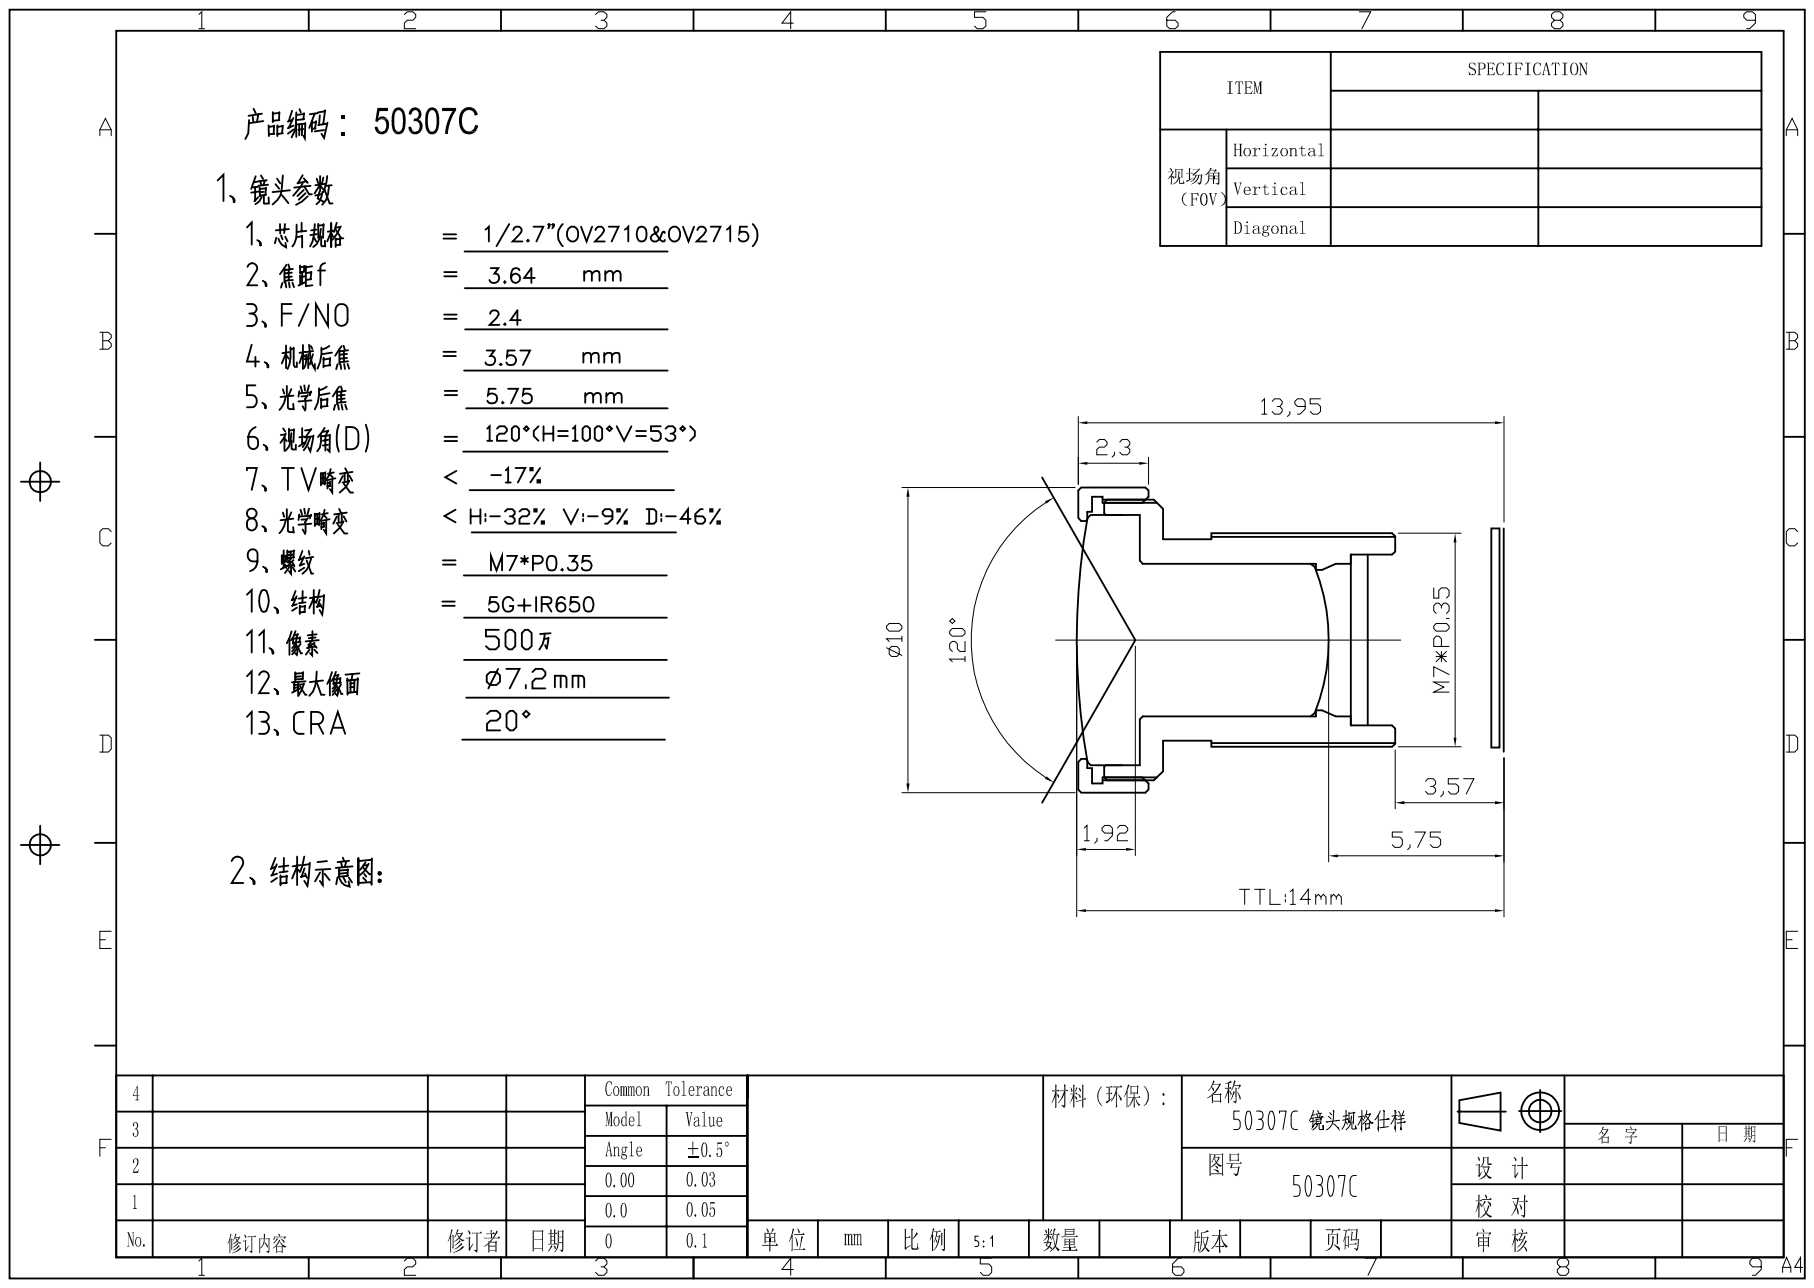
[picture p220: page 1]
