experientials/ziloo/Hardware/201/OV2735-module/lenses/50310A Lens Datesheet (OV2710).pdf

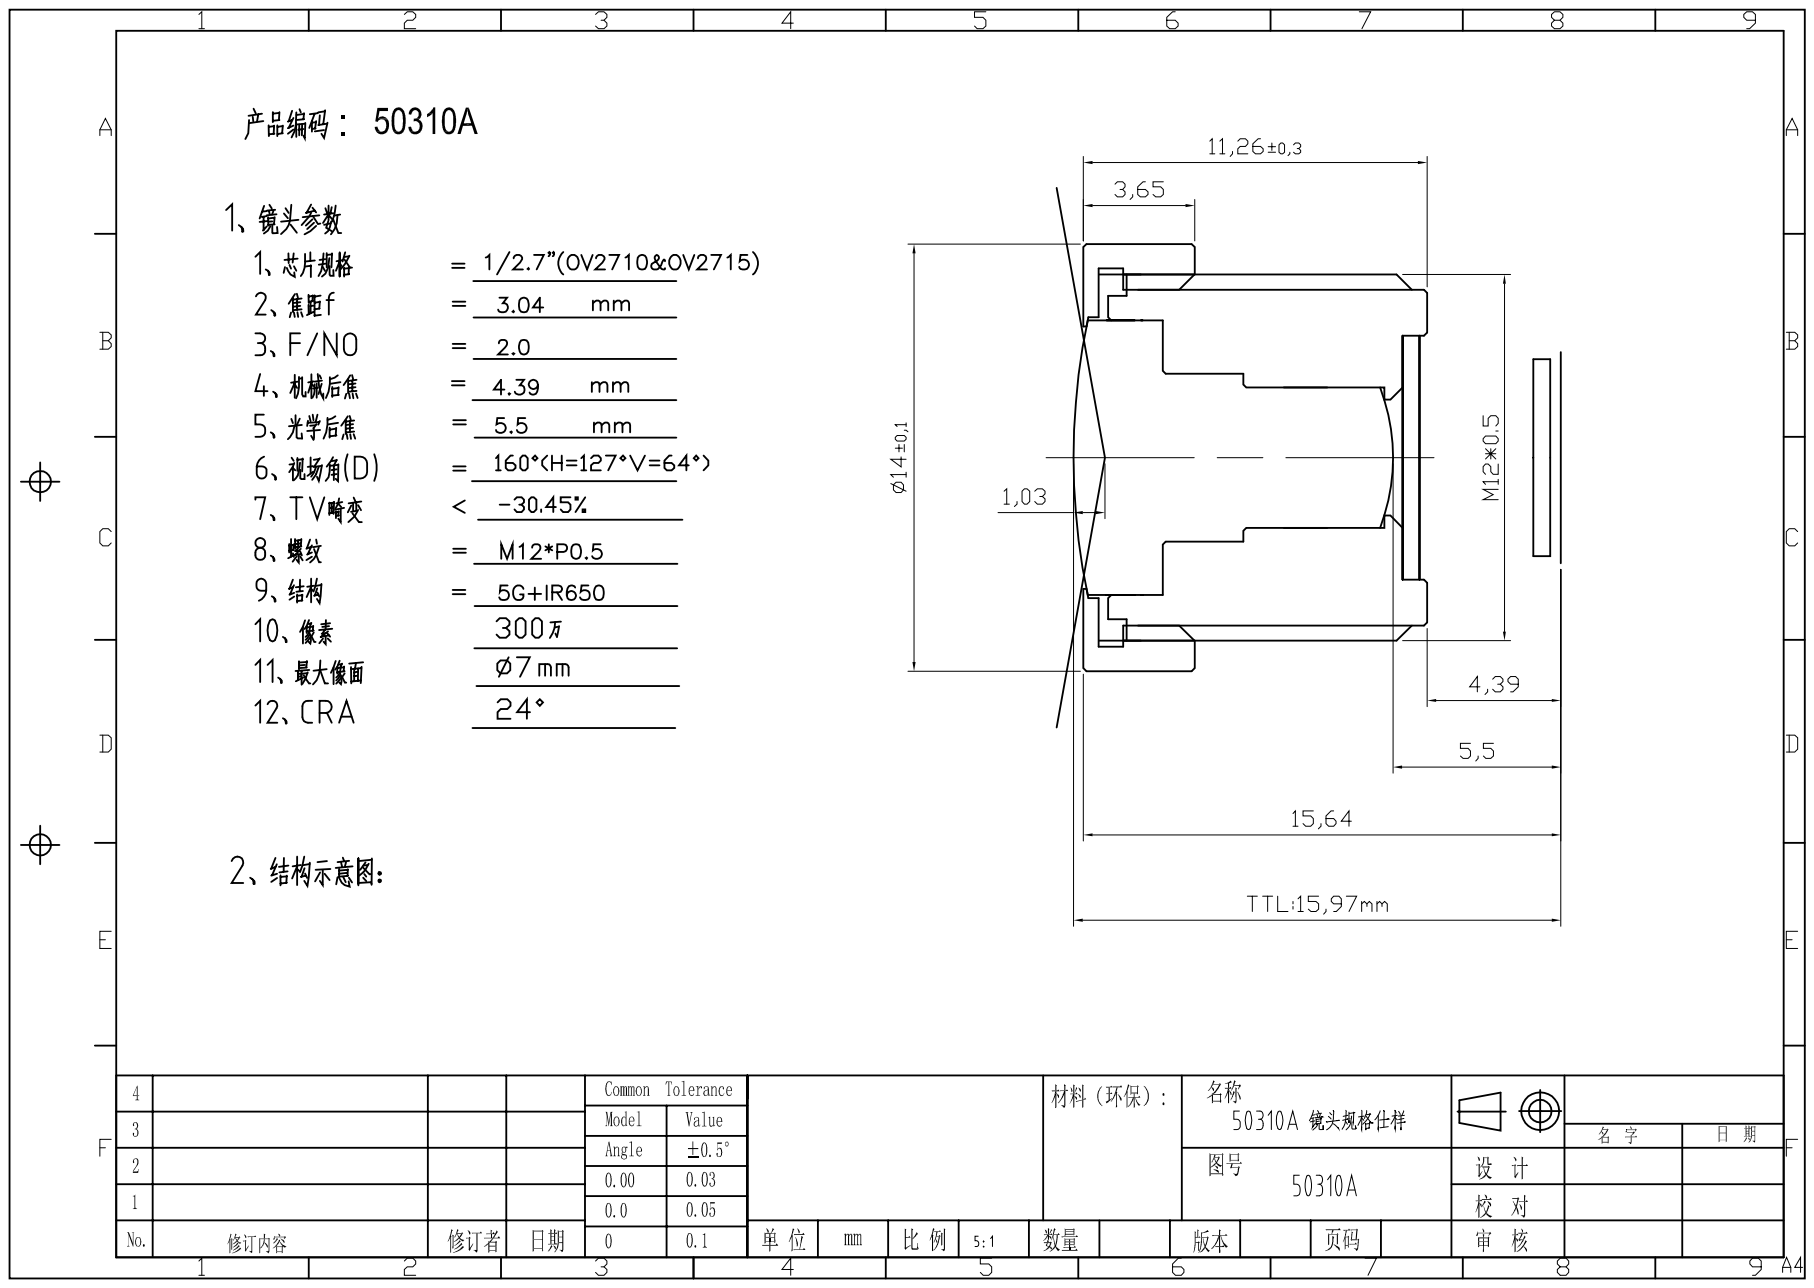
[picture p221: page 1]
