experientials/ziloo/Hardware/201/OV2735-module/lenses/50310C Lens Datesheet.pdf

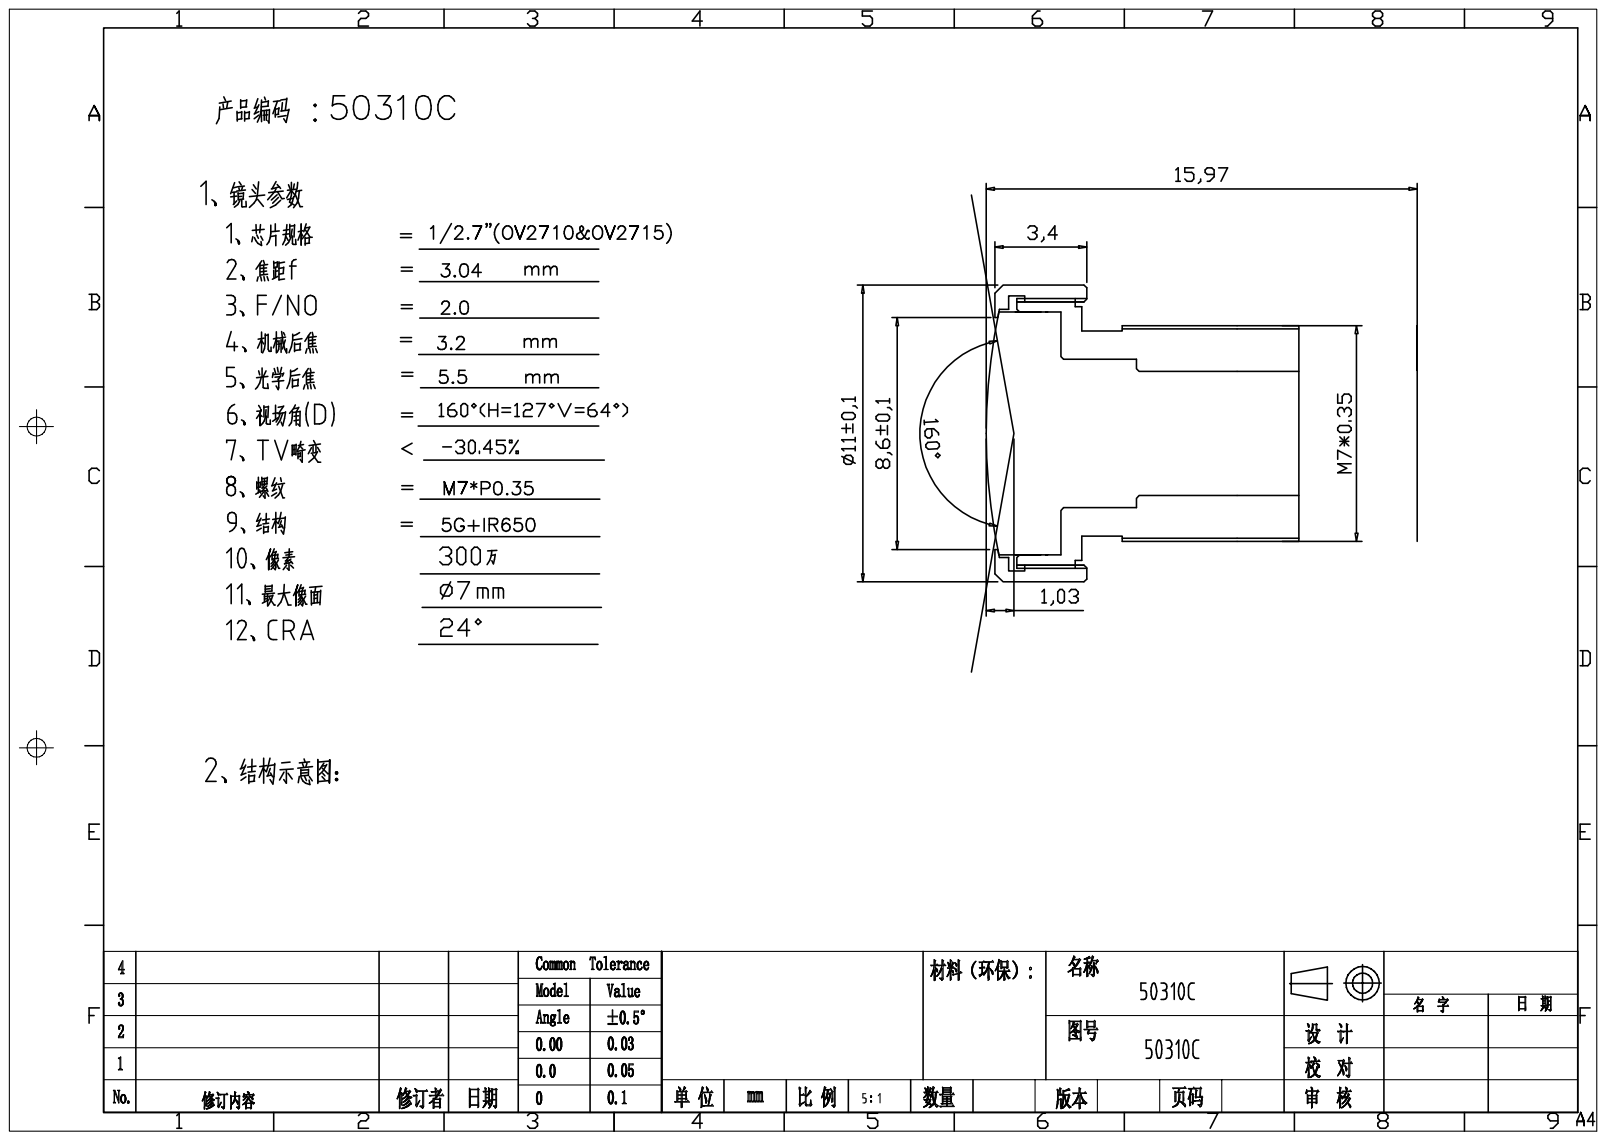
[picture p222: page 1]
