experientials/ziloo/Hardware/201/OV2735-module/lenses/H03四柱12 3间距 Model (1)(2).pdf

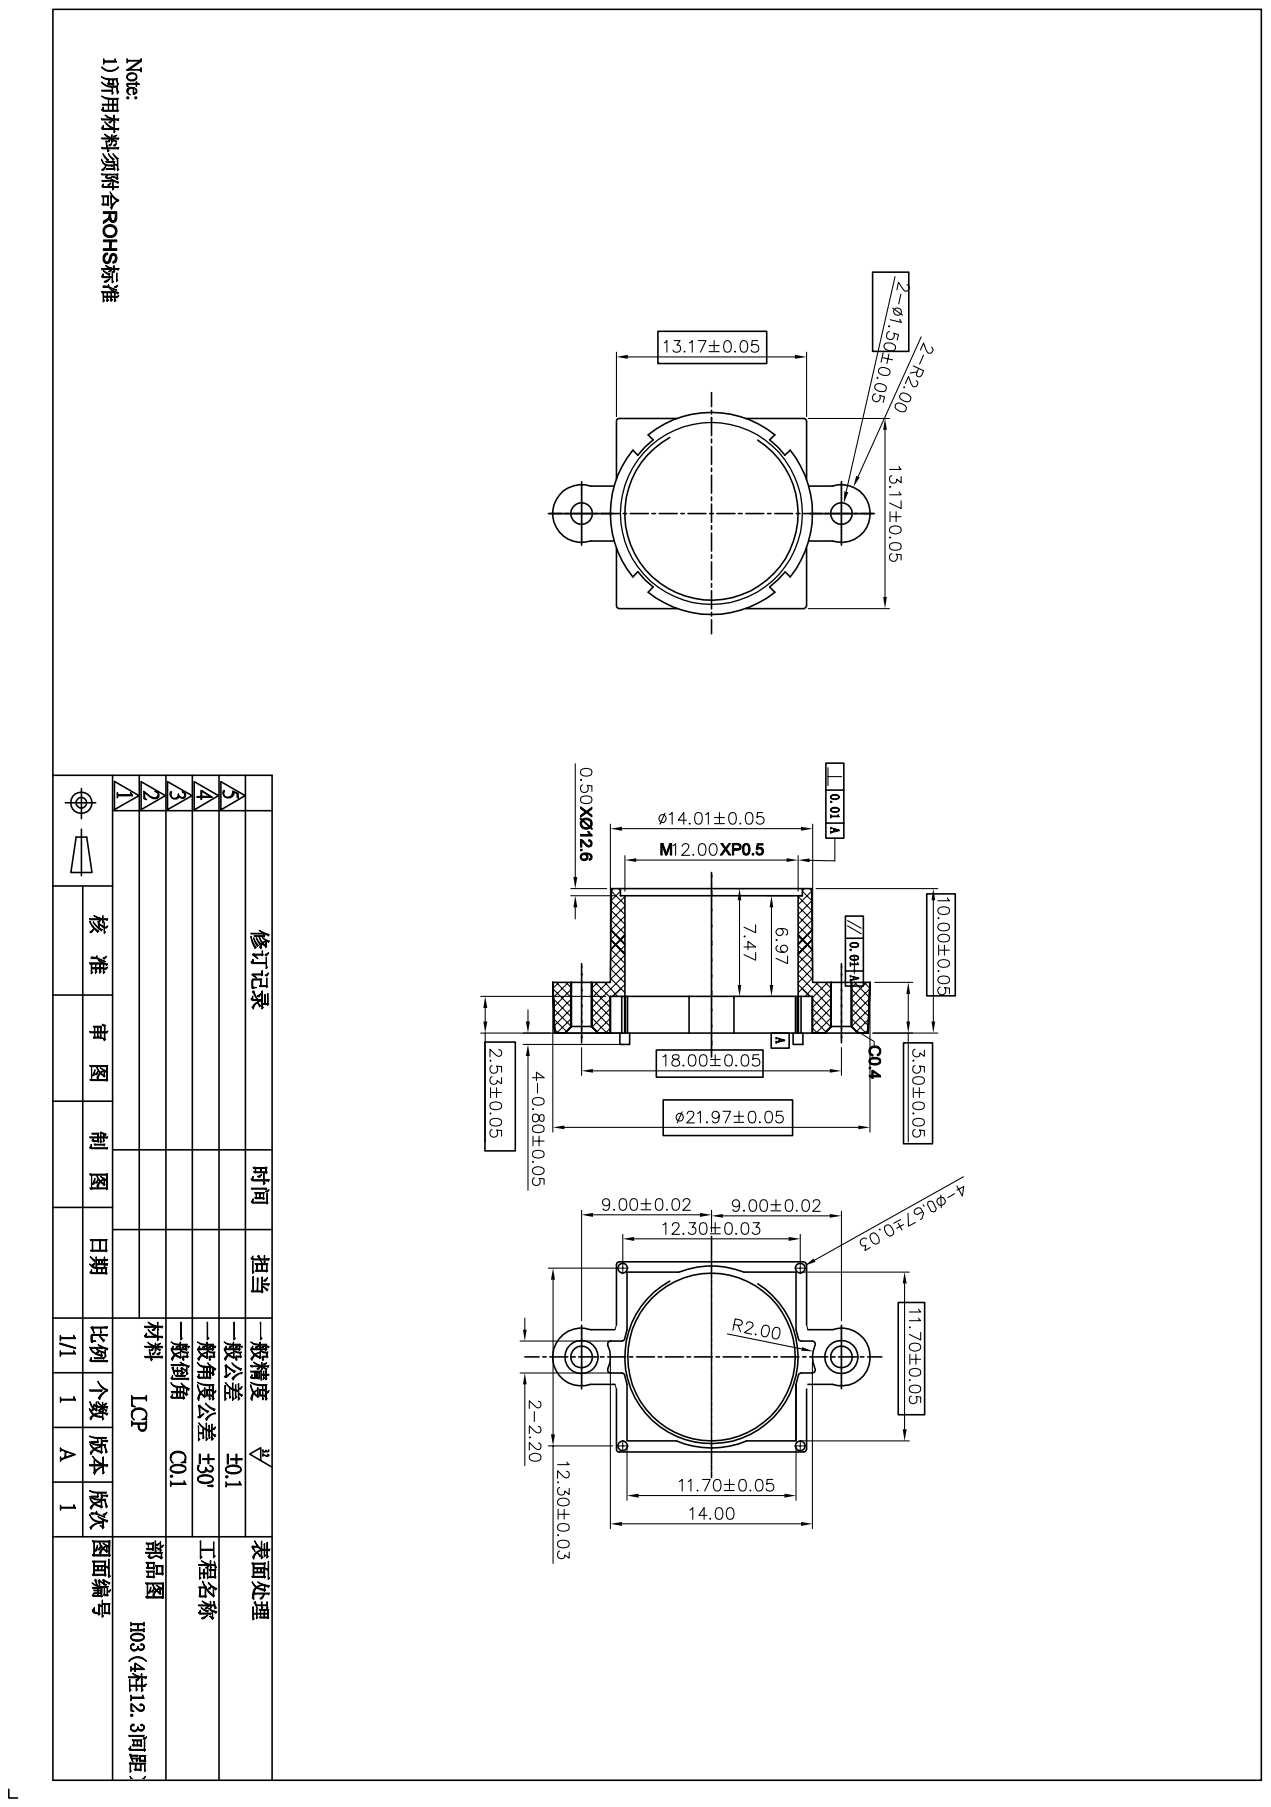
[picture p223: page 1]
