experientials/ziloo/Hardware/201/OV2735-module/lenses/JSD2157-A1.pdf

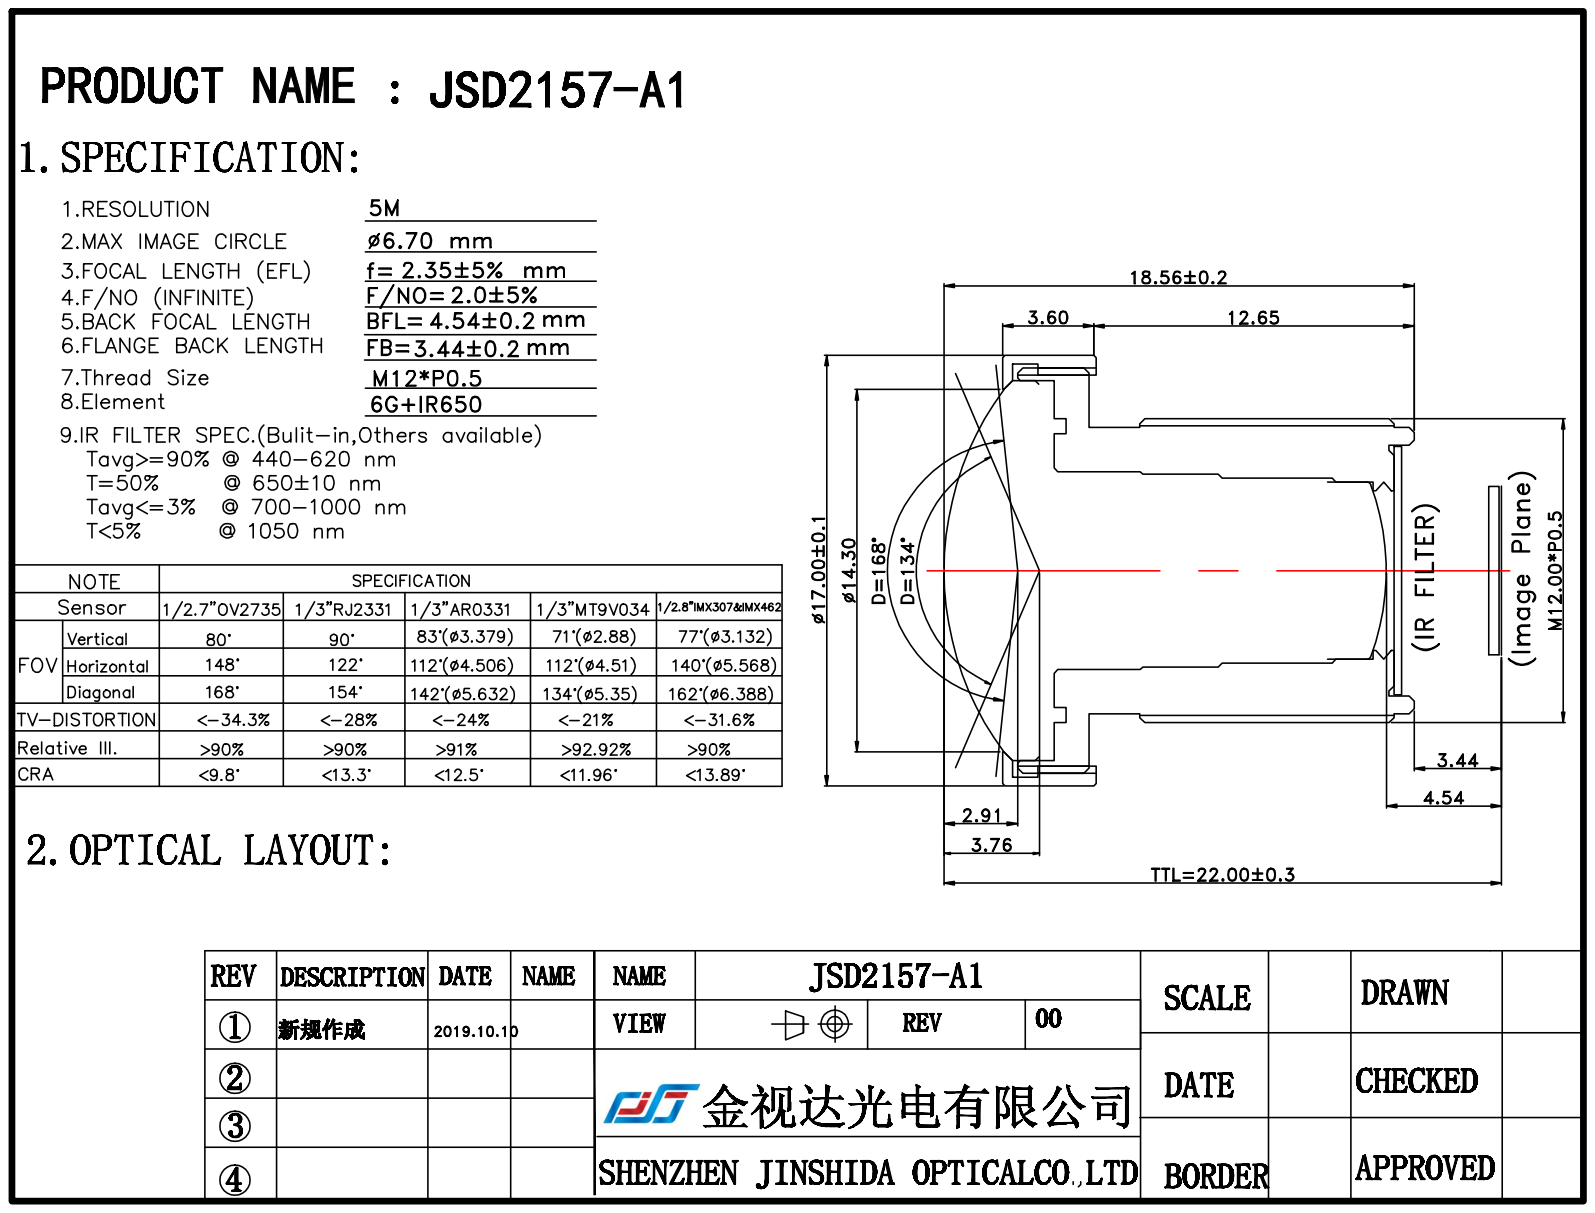
[picture p224: page 1]
