experientials/ziloo/Hardware/201/OV2735-module/lenses/JX1318座子规格书.pdf

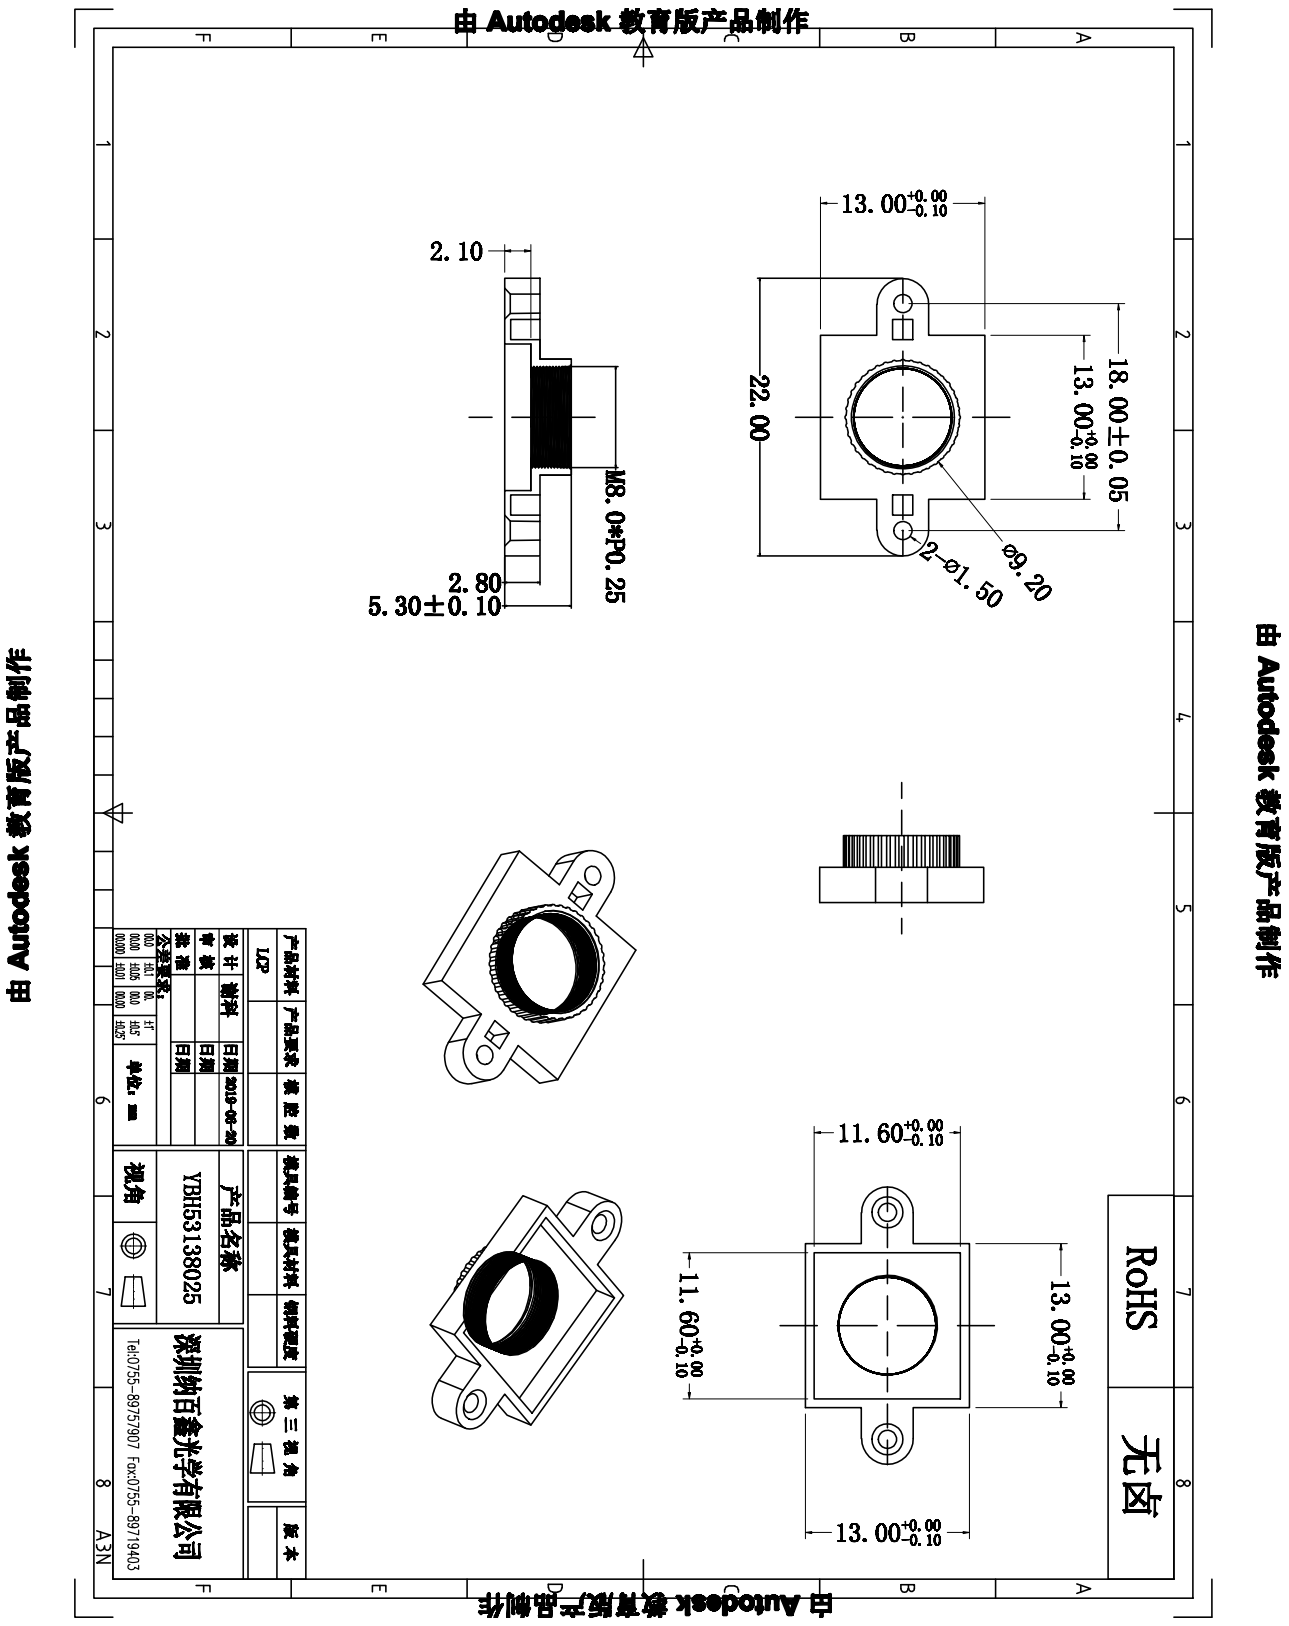
[picture p225: page 1]
